OLIMEX/OLINUXINO/HARDWARE/LCDs/LCD-DRIVER/README.md

LCD-DRIVER is a common LCD board used in Olimex displays that have one of these suffixes 
at the end of the product name: "-RTS", "-CTS", or "+" and suffix.

Displays without touchscreen, without "+" at the end of the product name, or with suffix "TS" 
use own driver boards, not LCD-DRIVER. Check the folders of these displays for schematics of 
the driver boards.

It is important to notice that depending on the size of the display and the type of touschreen 
used the LCD_DRIVER board would be configured dirrently. Refer to the labes in the schematic 
and also refer to the bill of materials in the hardware revision B folder (BOM) for the 
different configurations.

List of boards using LCD-DRIVER as of 03.09.2019:

LCD-OLinuXino-4.3+
LCD-OLinuXino-4.3RTS
LCD-OLinuXino-5CTS+
LCD-OLinuXino-7+
LCD-OLinuXino-7CTS
LCD-OLinuXino-7RTS
LCD-OLinuXino-7TS+
LCD-OLinuXino-10+
LCD-OLinuXino-10CTS
LCD-OLinuXino-10RTS
LCD-OLinuXino-10TS+
