OLIMEX/OLINUXINO/HARDWARE/LCDs/LCD-OLinuXino-10+/README.md

Description of product LCD-OLinuXino-10+

LCD-OLinuXino-10+ is a 10 inch display with resolution of 1024x600 pixels. 

LCD-OLINUXINO-10+ has no touschreen.

The design uses LCD-DRIVER board, instead the legcay board design of the original 
LCD-OLinuXino-10 (without the plus) and LCD-OLinuXino-10TS.

Refer to LCD-DRIVER's GitHub page for the hardware deisng files.

It is important to notice that depending on the size of the display and the type of touschreen 
used the LCD-DRIVER board would be configured dirrently. Refer to the labes in the schematic 
and also refer to the bill of materials in the hardware revision B folder (BOM) for the 
different configurations.
