OLIMEX/OLINUXINO/HARDWARE/LCDs/LCD-OLinuXino-10/README.md

LCD-OLINUXINO-10 is a 10 inch display with resolution of 1024x600 pixels. LCD-OLINUXINO-10 has no touschreen.

LCD-OLINUXINO-10 and LCD-OLINUXINO-10TS use the same design files (schematic, board files).

Both boards use the legacy driver board design, not the common LCD-DRIVER board.

Visit the folder of LCD-OLinuXino-10TS for the hardware design resources.
