OLIMEX/OLINUXINO/HARDWARE/LCDs/LCD-OLinuXino-4.3+/README.md

Description of product LCD-OLinuXino-4.3+

LCD-OLinuXino-4.3+ is a 4.3 inch display with resolution of 480x272.

LCD-OLinuXino-4.3+ has no touschreen.

It has LCD-DRIVER board, instead the legacy PCB design of the original 
LCD-OLinuXino-4.3 (without the plus).

Refer to LCD-DRIVER's GitHub page for the hardware source files.

It is important to notice that depending on the size of the display and the type of touschreen 
used the LCD_DRIVER board would be configured dirrently. Refer to the labes in the schematic 
and also refer to the bill of materials in the hardware revision B folder (BOM) for the 
different configurations.
