OLIMEX/OLINUXINO/HARDWARE/LCDs/LCD-OLinuXino-4.3/README.md

LCD-OLINUXINO-4.3 is a 4.3 inch display with resolution of 480x272 pixels.

LCD-OLINUXINO-4.3 has no touschreen.

LCD-OLINUXINO-4.3 and LCD-OLINUXINO-4.3TS use the same design files (schematic, board files).

Both boards use the legacy driver board design, not the common LCD-DRIVER board.

Check the files in the LCD-OLinuXino-4.3TS folder for the hardware design files.
