OLIMEX/OLINUXINO/HARDWARE/LCDs/LCD-OLinuXino-4.3RTS/README.md

Description of product LCD-OLinuXino-4.3RTS

LCD-OLinuXino-4.3RTS is is a 4.3 inch display with resolution of 800x480 pixels and resistive touch screen.

It uses LCD-DRIVER board, instead the original board design of the original 
LCD-OLinuXino-4.3 (without the plus).

In LCD-OLinuXino-4.3RTS the touschreen uses digital interface (I2C).

Refer to LCD-DRIVER's GitHub page for the hardware source files.

It is important to notice that depending on the size of the display and the type of touschreen 
used the LCD_DRIVER board would be configured dirrently. Refer to the labes in the schematic 
and also refer to the bill of materials in the hardware revision B folder (BOM) for the 
different configurations.
