OLIMEX/OLINUXINO/HARDWARE/LCDs/LCD-OLinuXino-4.3TS+/README.md

Description of product LCD-OLinuXino-4.3TS+

LCD-OLinuXino-4.3TS+ is a 4.3 inch display with resolution of 480x272.

It uses LCD-DRIVER board, instead the original board design of the original 
LCD-OLinuXino-4.3 (without the plus).

Unlike LCD-OLinuXino-4.3RTS, the touchscreen of LCD-OLinuXino-4.3TS+ is configured for analog
connection. In LCD-OLinuXino-4.3RTS the touschreen uses digital interface (I2C).

Refer to LCD-DRIVER's GitHub page for the hardware source files.

It is important to notice that depending on the size of the display and the type of touschreen 
used the LCD_DRIVER board would be configured dirrently. Refer to the labes in the schematic 
and also refer to the bill of materials in the hardware revision B folder (BOM) for the 
different configurations.
