OLIMEX/OLINUXINO/HARDWARE/LCDs/LCD-OLinuXino-5CTS/README.md

LCD-OLinuXino-5CTS is a 5 inch display with resolution of 800x480 pixels and capacitive touch screen.

LCD-OLINUXINO-5CTS uses the legacy driver board design, not the common LCD-DRIVER board.
