OLIMEX/OLINUXINO/SOFTWARE/A13/EASYCAP/README

EasyCap is low cost video capture USB dongle which could be find at low cost from ebay. It allow 1 to 4 cameras to be connected and to implement DVR security survilance on your PC.

Kaloyan Yovchev sent us tested drivers which works with A13-OLinuXIno and kernel 3.0.42+
