OLIMEX/OLINUXINO/SOFTWARE/A13/ANDROID-MOD-IO/README.TXT

This is demo code made by Dimitar Gamishev and show how to access MOD-IO and drive relays, read GPIOs, read ADCs with Android application.
The sources of the projects are at: https://github.com/hehopmajieh/modio_android
