OLIMEX/OLINUXINO/HARDWARE/A10S-OLinuXino-MICRO/A10S-OLinuXino-MICRO_Rev_D.sch.pdf

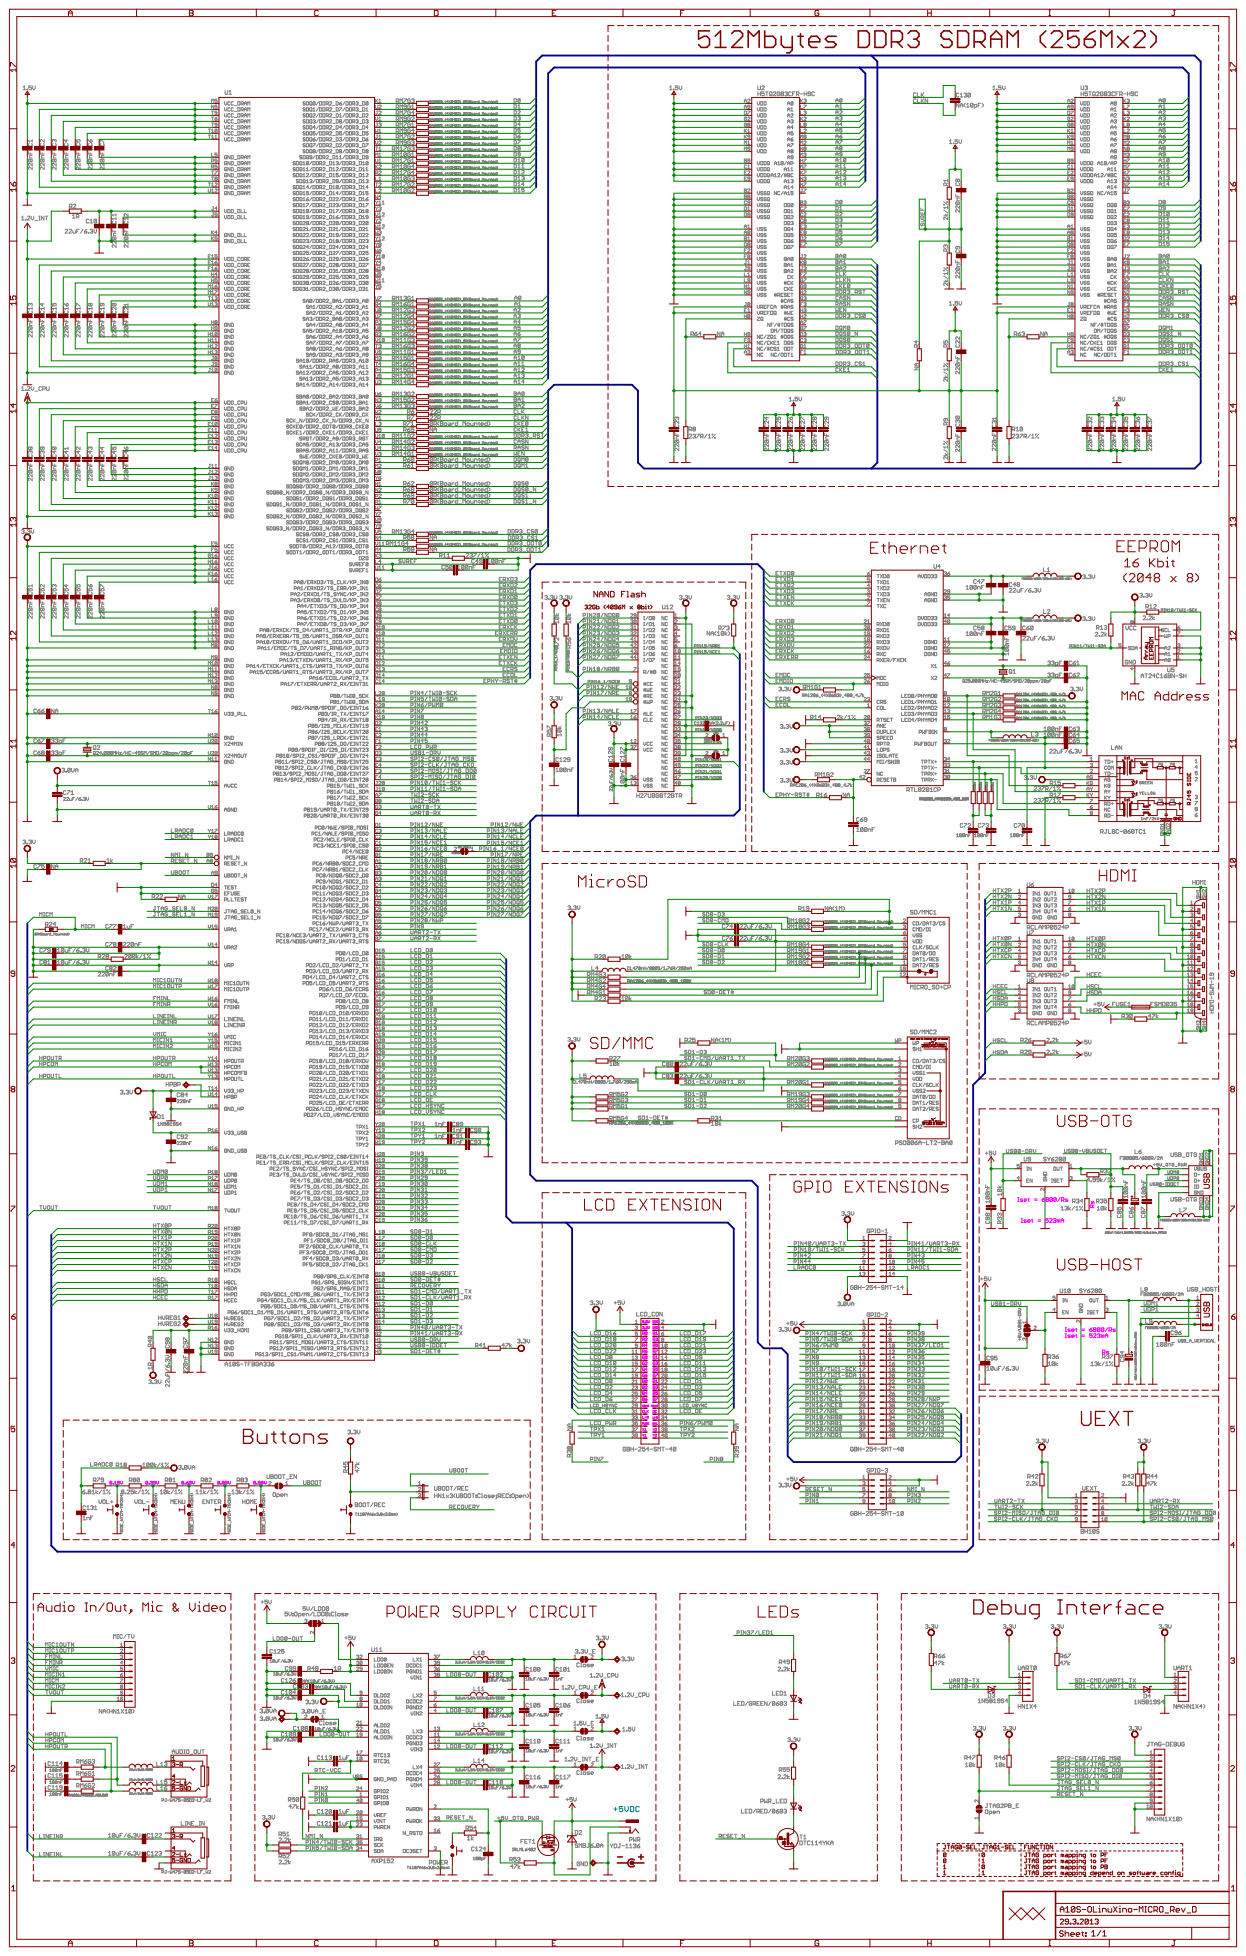
[picture p3: page 1]
