OLIMEX/OLINUXINO/HARDWARE/AM3352-OLinuXino/AM3352-OLINUXINO_Rev_A-14122012.sch.pdf

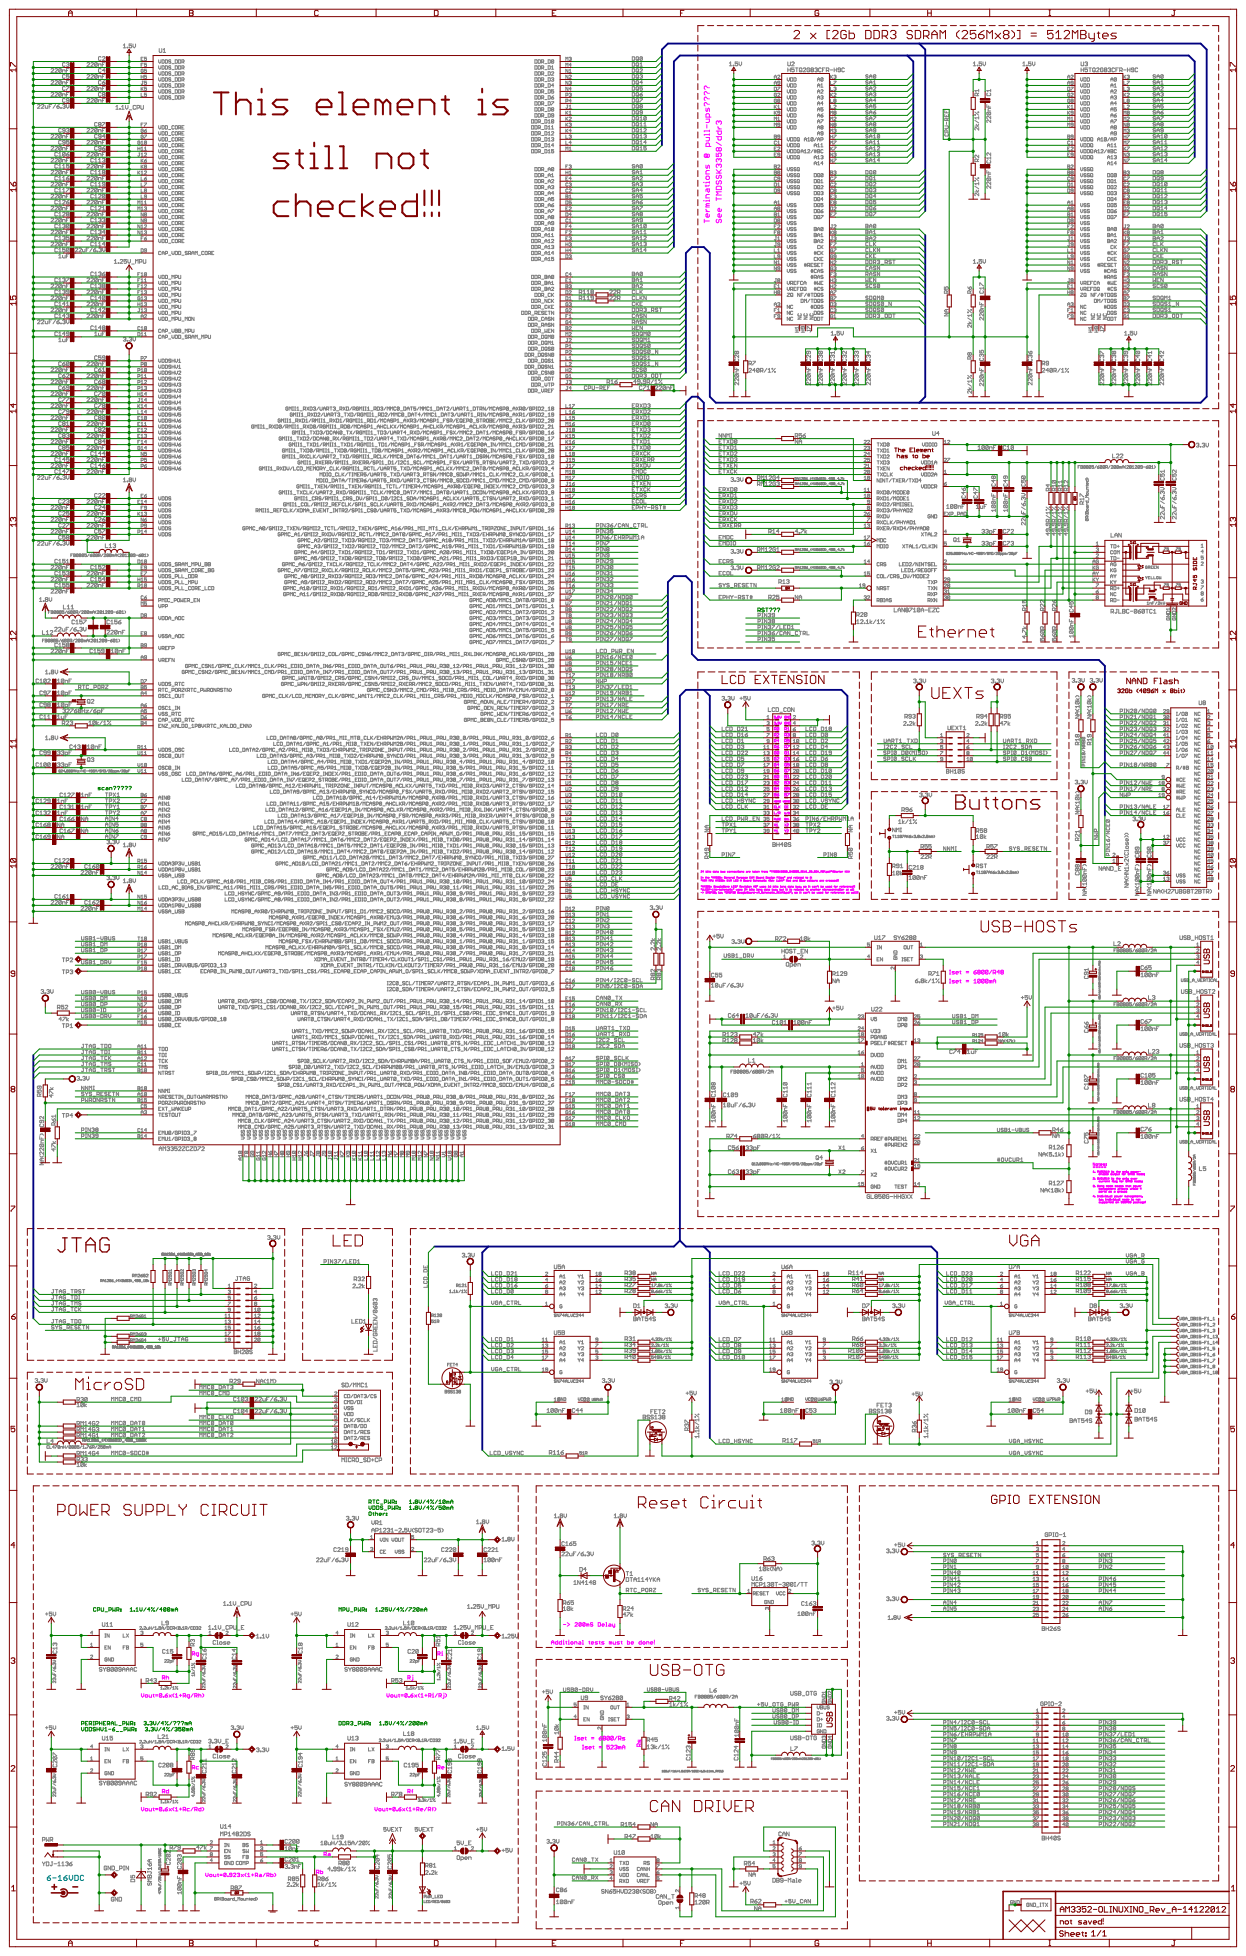
[picture p4: page 1]
