OLIMEX/OLINUXINO/HARDWARE/A13-OLinuXino-MICRO/A13-OLinuXino-MICRO_Rev_A.sch.pdf

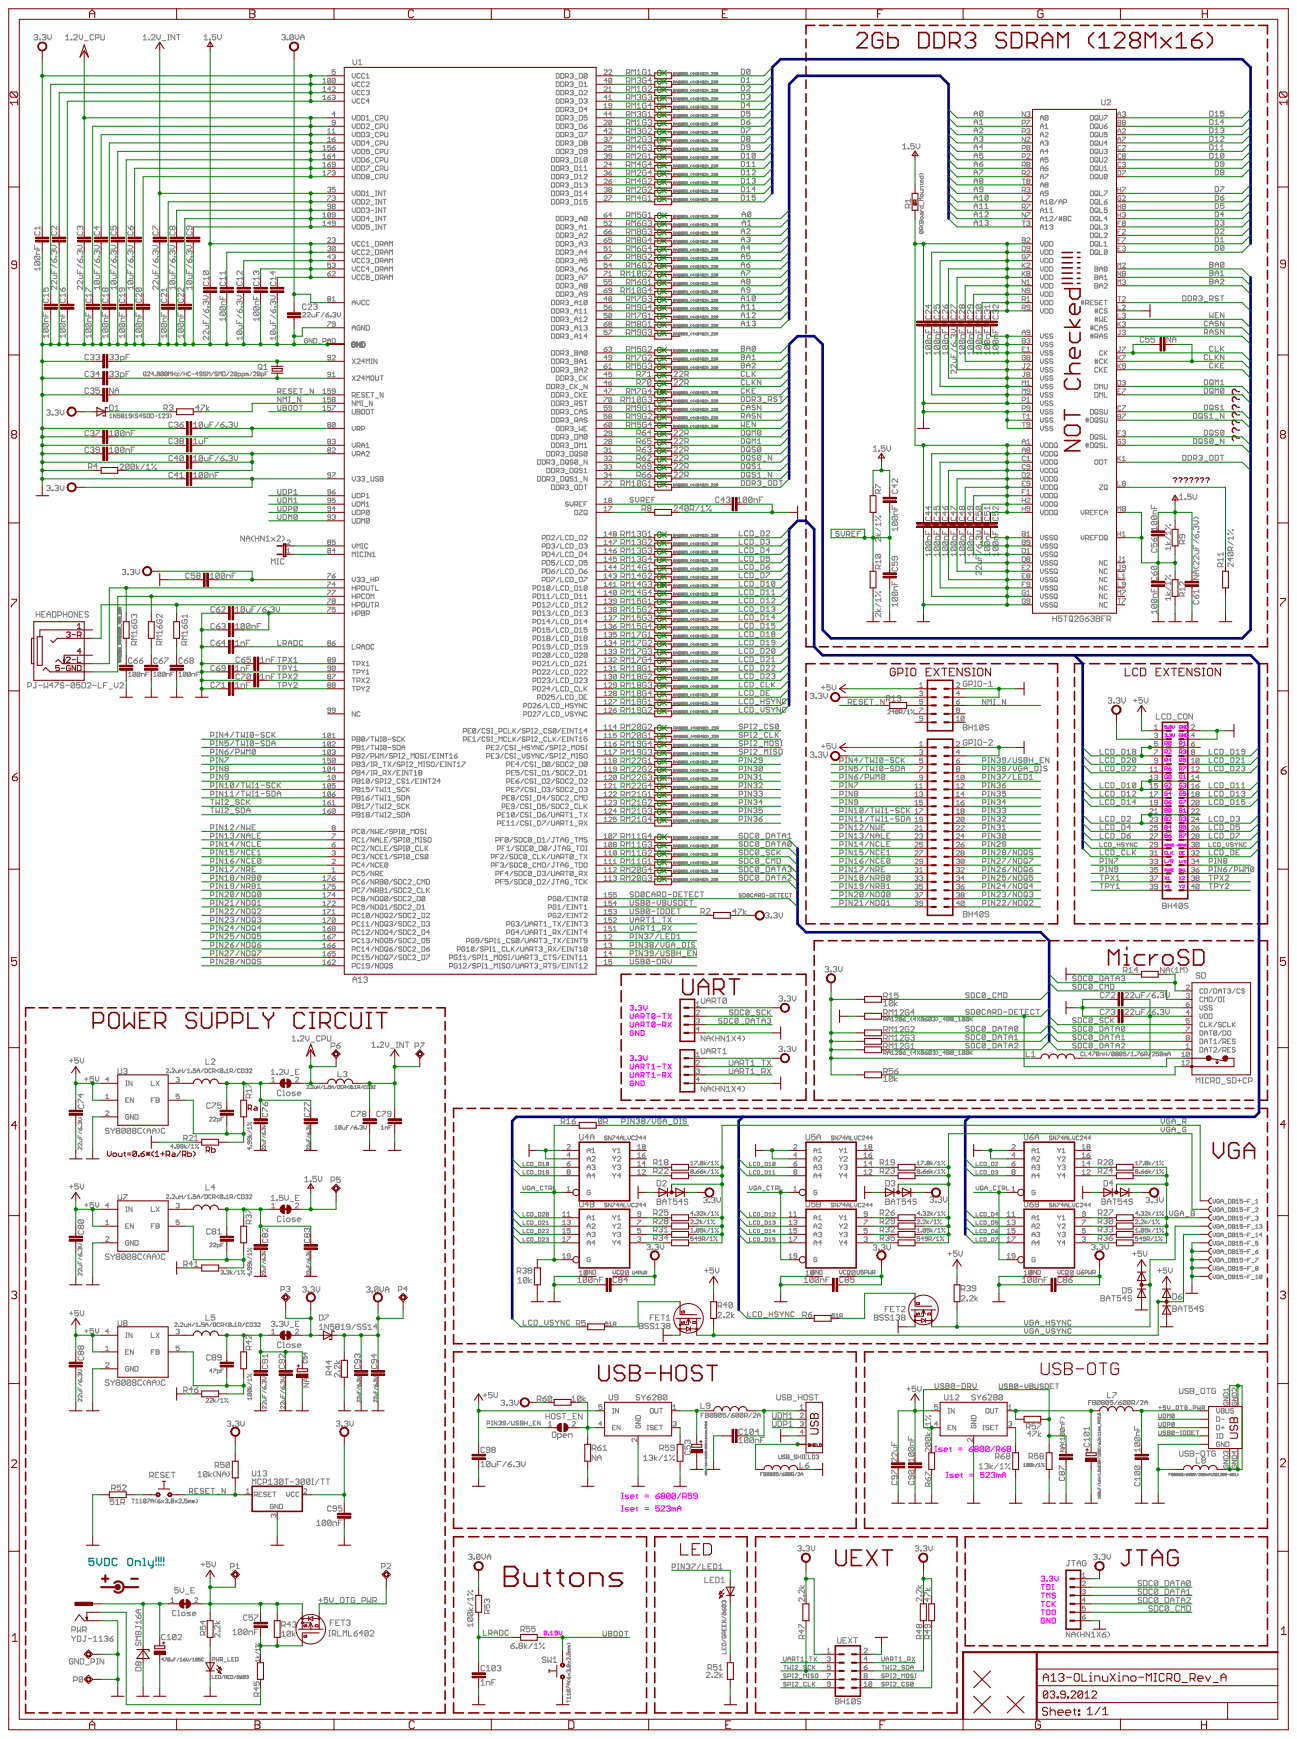
[picture p5: page 1]
