OLIMEX/OLINUXINO/HARDWARE/A10-OLinuXino/A10-OLinuXino_Rev_A.sch.pdf

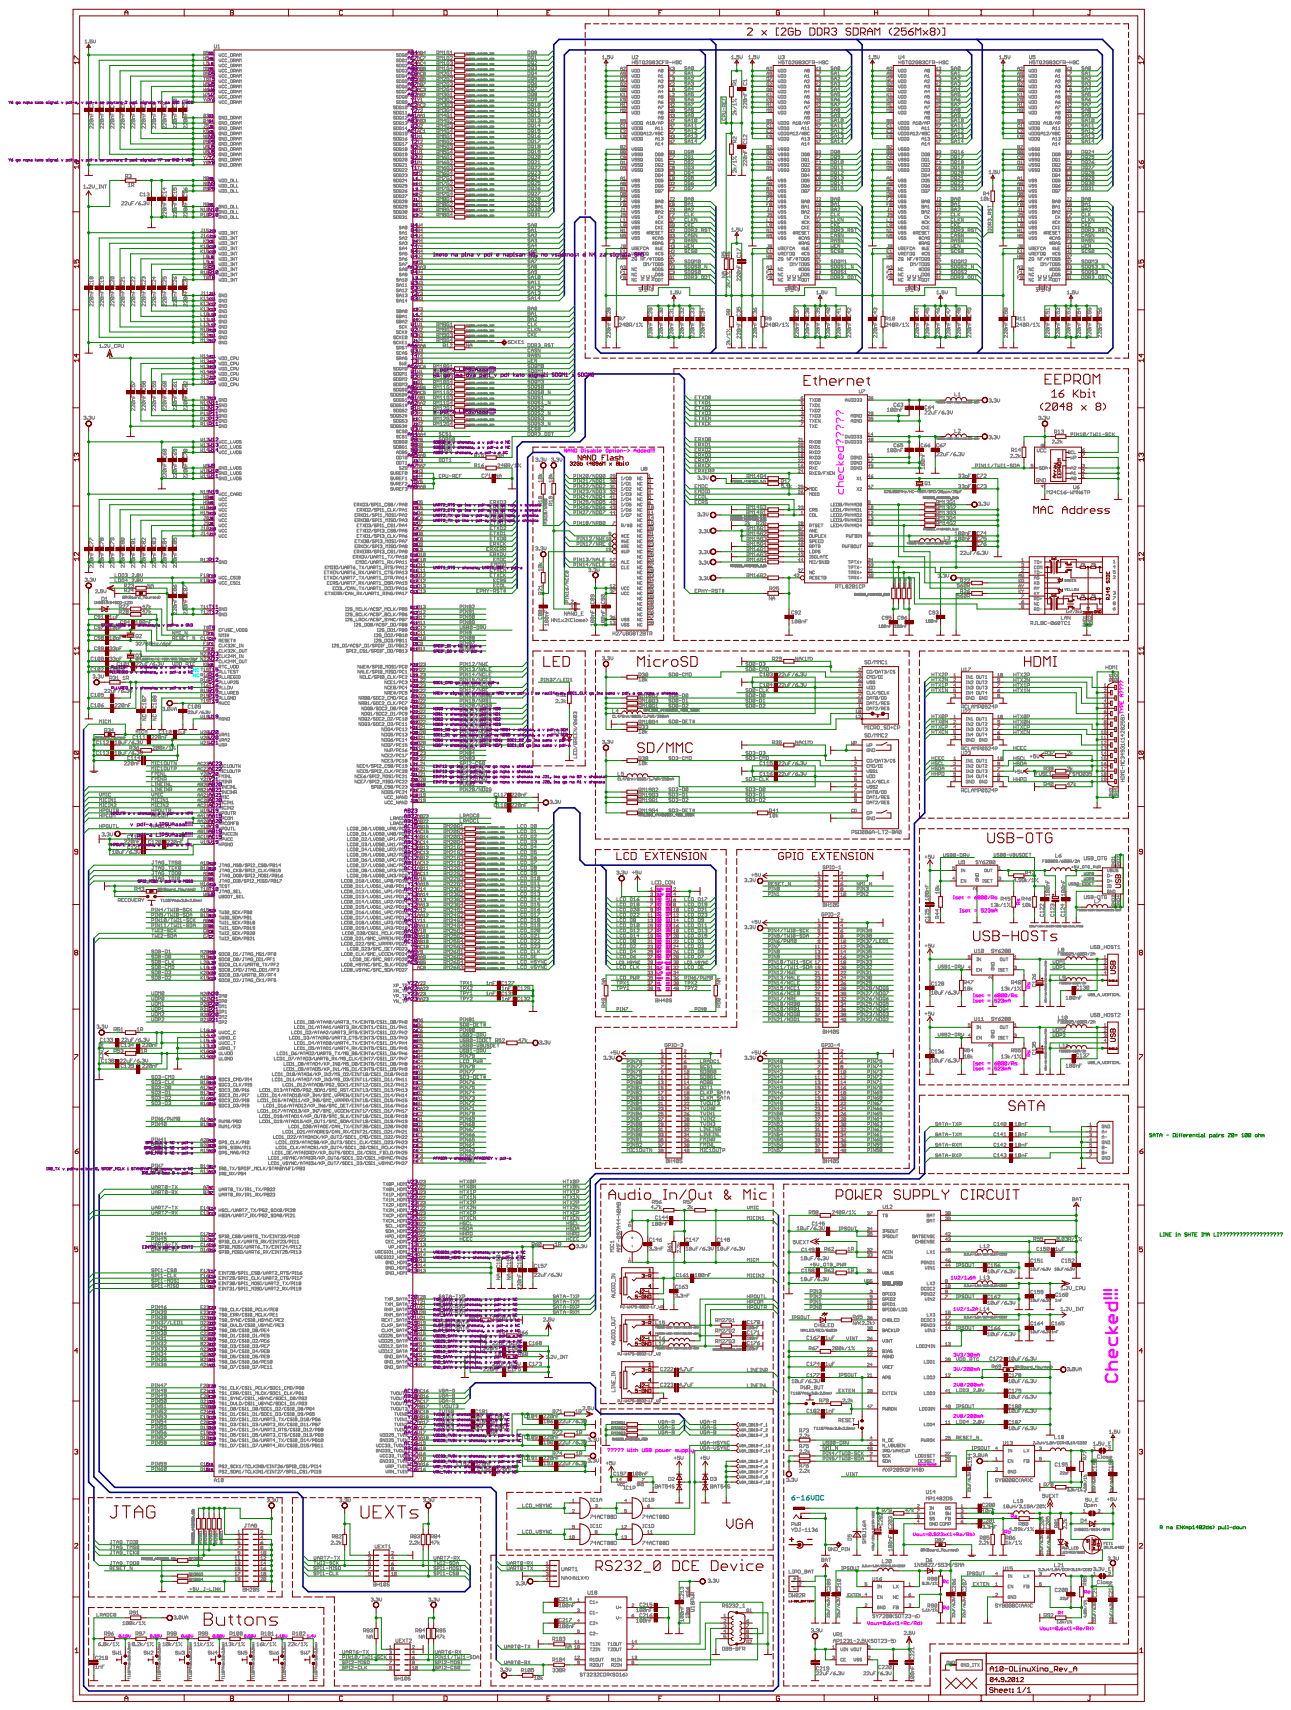
[picture p6: page 1]
