OLIMEX/OLINUXINO/HARDWARE/A10-OLinuXino-LIME/2. Older hardware revisions/A10-OLinuXino-LIME hardware revision preliminary/A10-OLinuXino/README.TXT

A10-OLinuXino	September, 2012	REV.A

Status	: design 

Issues	: 

TODO	: 

Features of the board specification:
What we put on the board:
- A10 Cortex A8 processor running at 1Ghz
- 1GB of DDR3 memory (organized as 4 x 256MB x8 with two 2Gbit chips)
- 4GB NAND Flash
- HDMI
- VGA
- RS232 UART
- 100Mbit Ethernet
- LCD 
- 2 USB hosts 
- 1 USB OTG
- SATA
- JTAG
- UEXT1 and UEXT2 for connecting addtional UEXT modules like Zigbee, Bluetooth, Relays, etc
- GPIO-1,2,3,4 with total 132 GPIOs available for the user
- Audio Output, Audio Input, Line Input
- 7 buttons for android navigation
- STATUS LED
- micro-SDcard 
- normal size SD/MMC card
- 6-16VDC input power supply, noise immune design
- LiPo battery power option
- RESET and Power-Down buttons
- console debug UART port
