OLIMEX/OLINUXINO/BOXES/LIME2-PLASTIC-BOX/Olinuxinoe-lime2-back.png

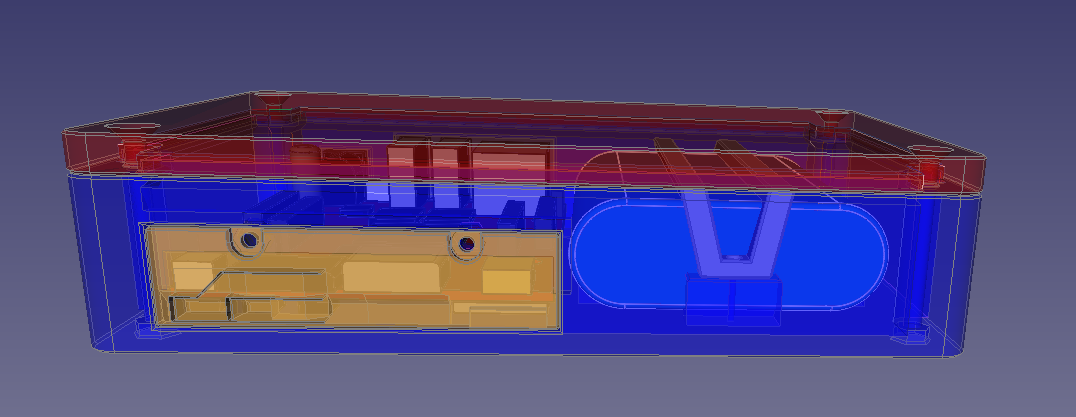
BOXES/LIME2-PLASTIC-BOX/Olinuxinoe-lime2-back.png
