OLIMEX/OLINUXINO/BOXES/LIME2-PLASTIC-BOX/Olinuxinoe-lime2-open.png

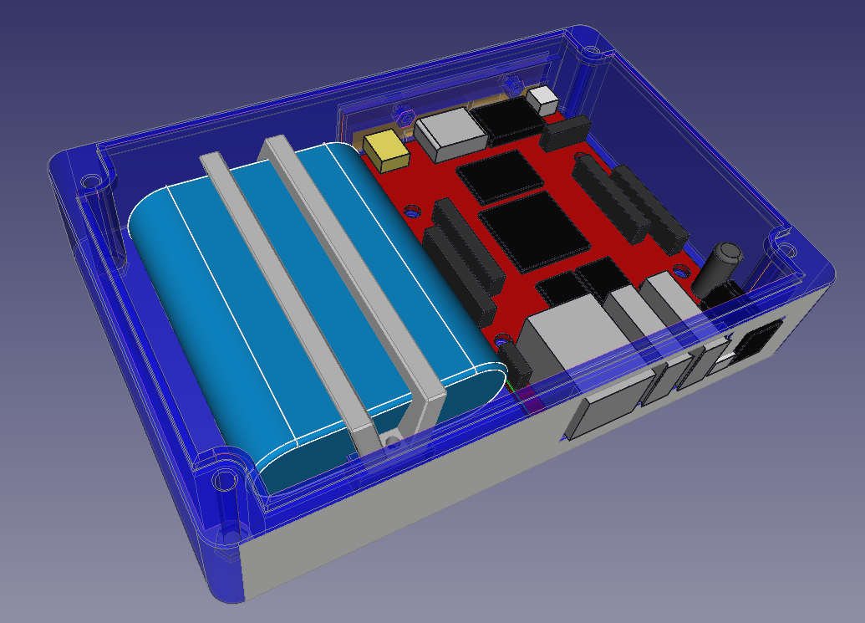
BOXES/LIME2-PLASTIC-BOX/Olinuxinoe-lime2-open.png
