OLIMEX/OLINUXINO/BOXES/LIME2-PLASTIC-BOX/Olinuxinoe-lime2-top.png

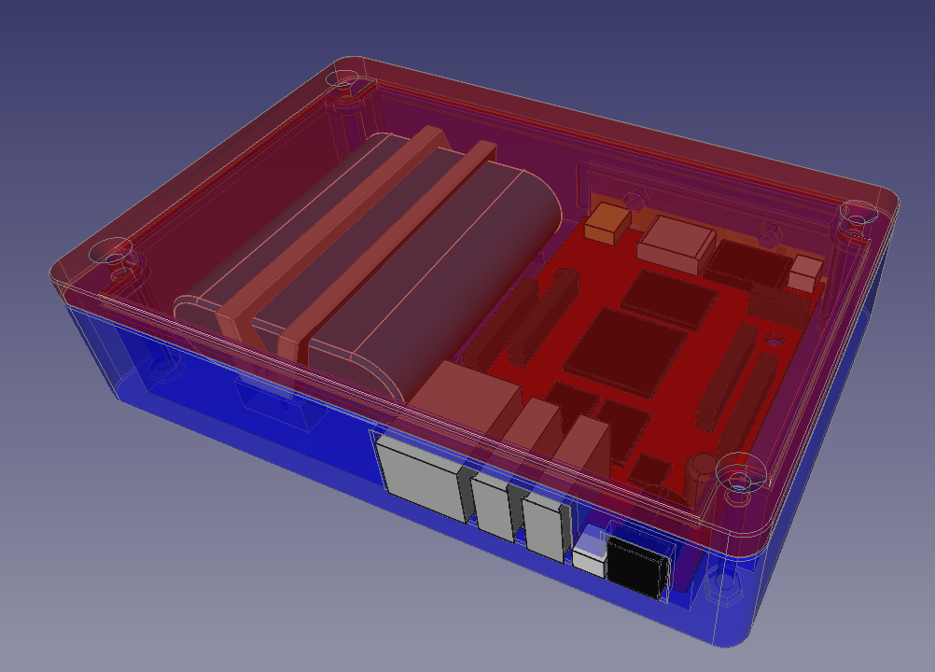
BOXES/LIME2-PLASTIC-BOX/Olinuxinoe-lime2-top.png
