OLIMEX/OLINUXINO/BOXES/LIME2-PLASTIC-BOX/PLASTIC-BOX-ASM1.jpg

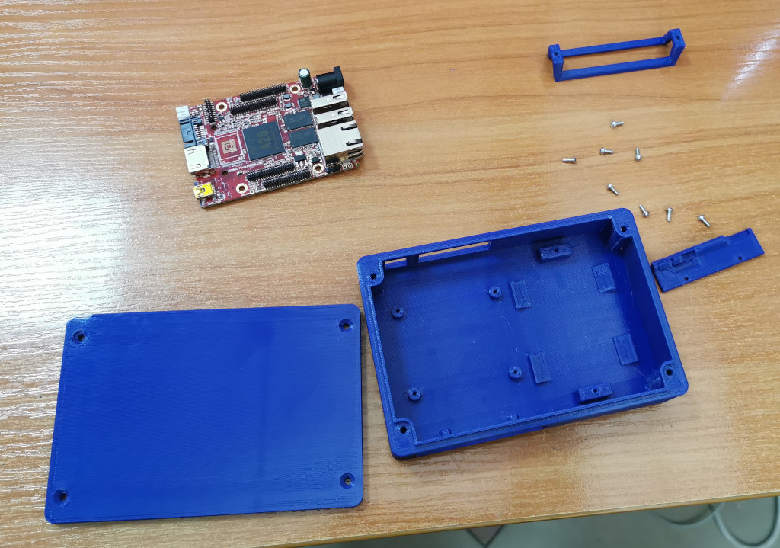
BOXES/LIME2-PLASTIC-BOX/PLASTIC-BOX-ASM1.jpg
