OLIMEX/OLINUXINO/BOXES/LIME2-PLASTIC-BOX/PLASTIC-BOX-ASM2.jpg

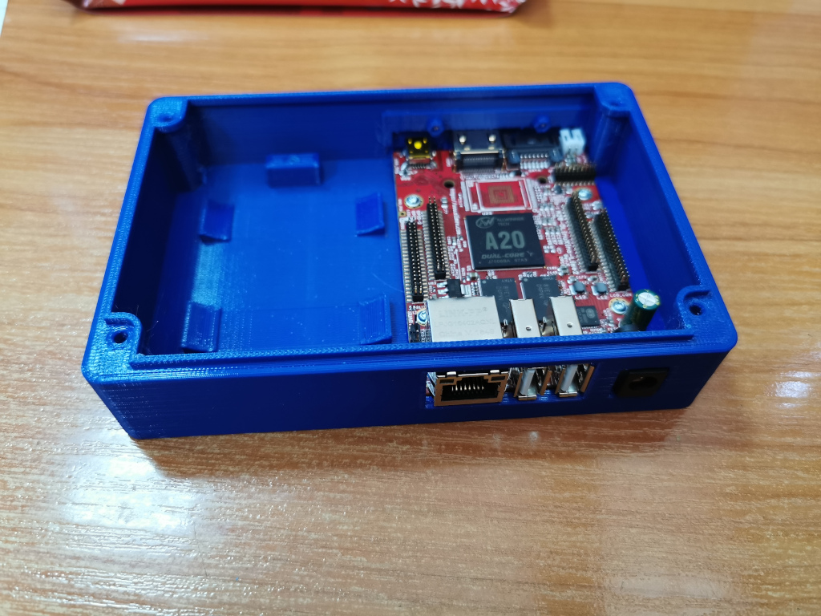
BOXES/LIME2-PLASTIC-BOX/PLASTIC-BOX-ASM2.jpg
