OLIMEX/OLINUXINO/SOFTWARE/A13/A13+OpenCV+Scratch+BallTracking/Configure Blue.png

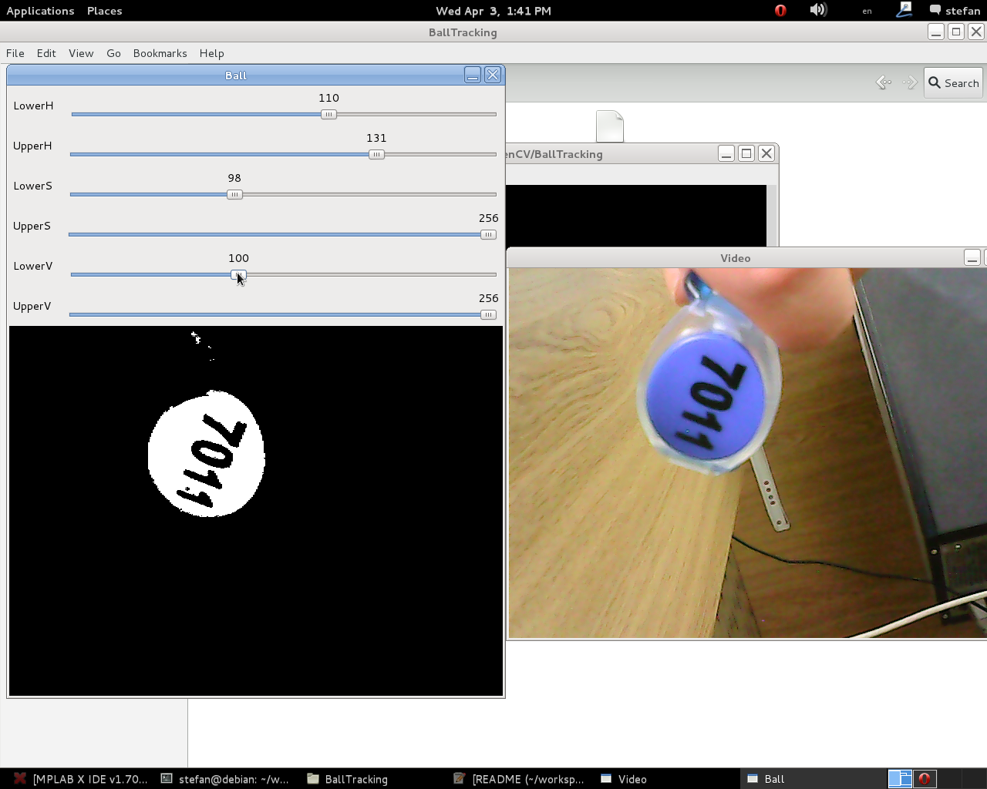
SOFTWARE/A13/A13+OpenCV+Scratch+BallTracking/Configure Blue.png
