OLIMEX/OLINUXINO/SOFTWARE/A13/A13-OLinuXino-WIFI-MOD-GPS-LOGGER/A13+GPS.png

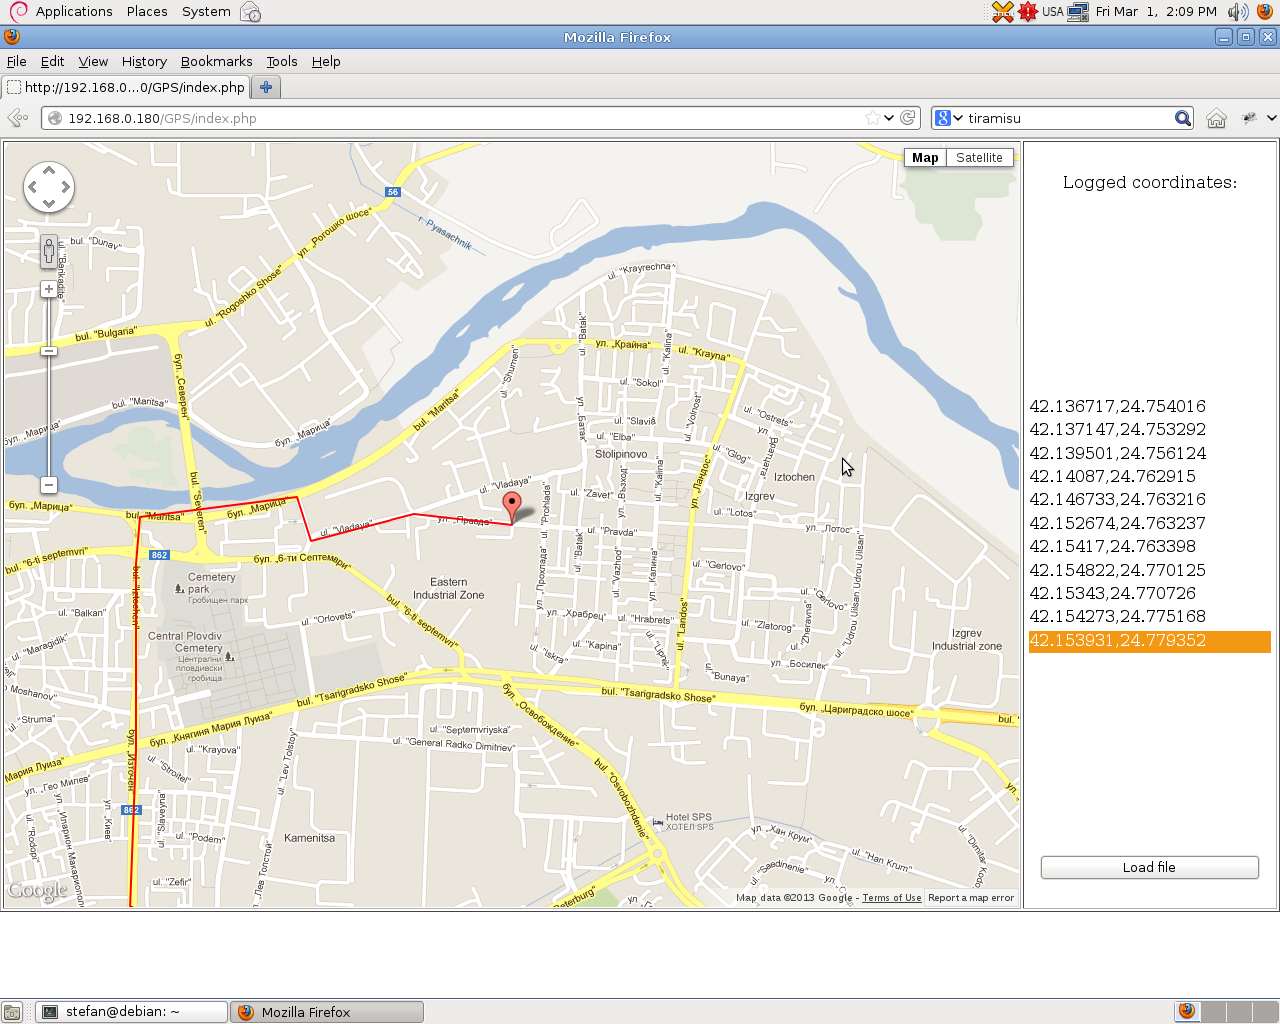
SOFTWARE/A13/A13-OLinuXino-WIFI-MOD-GPS-LOGGER/A13+GPS.png
