OLIMEX/OLINUXINO/SOFTWARE/A13/MOD-GPS/MOD-GPS-COMPILE.jpg

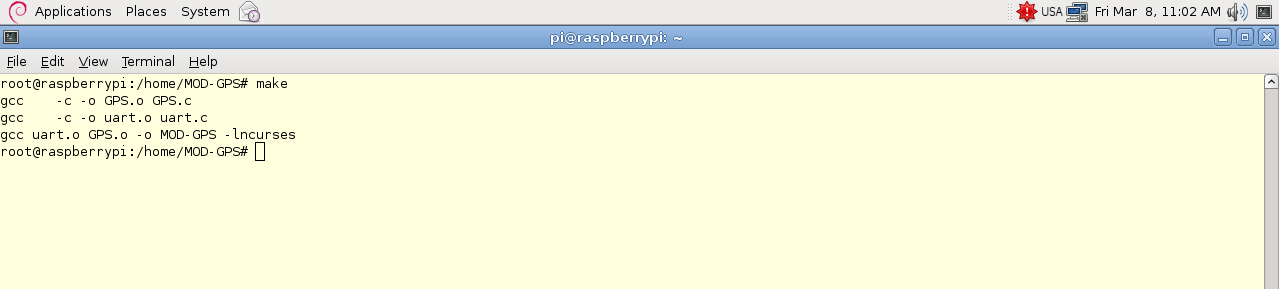
SOFTWARE/A13/MOD-GPS/MOD-GPS-COMPILE.jpg
