OLIMEX/OLINUXINO/SOFTWARE/A13/MOD-GPS/MOD-GPS-START.jpg

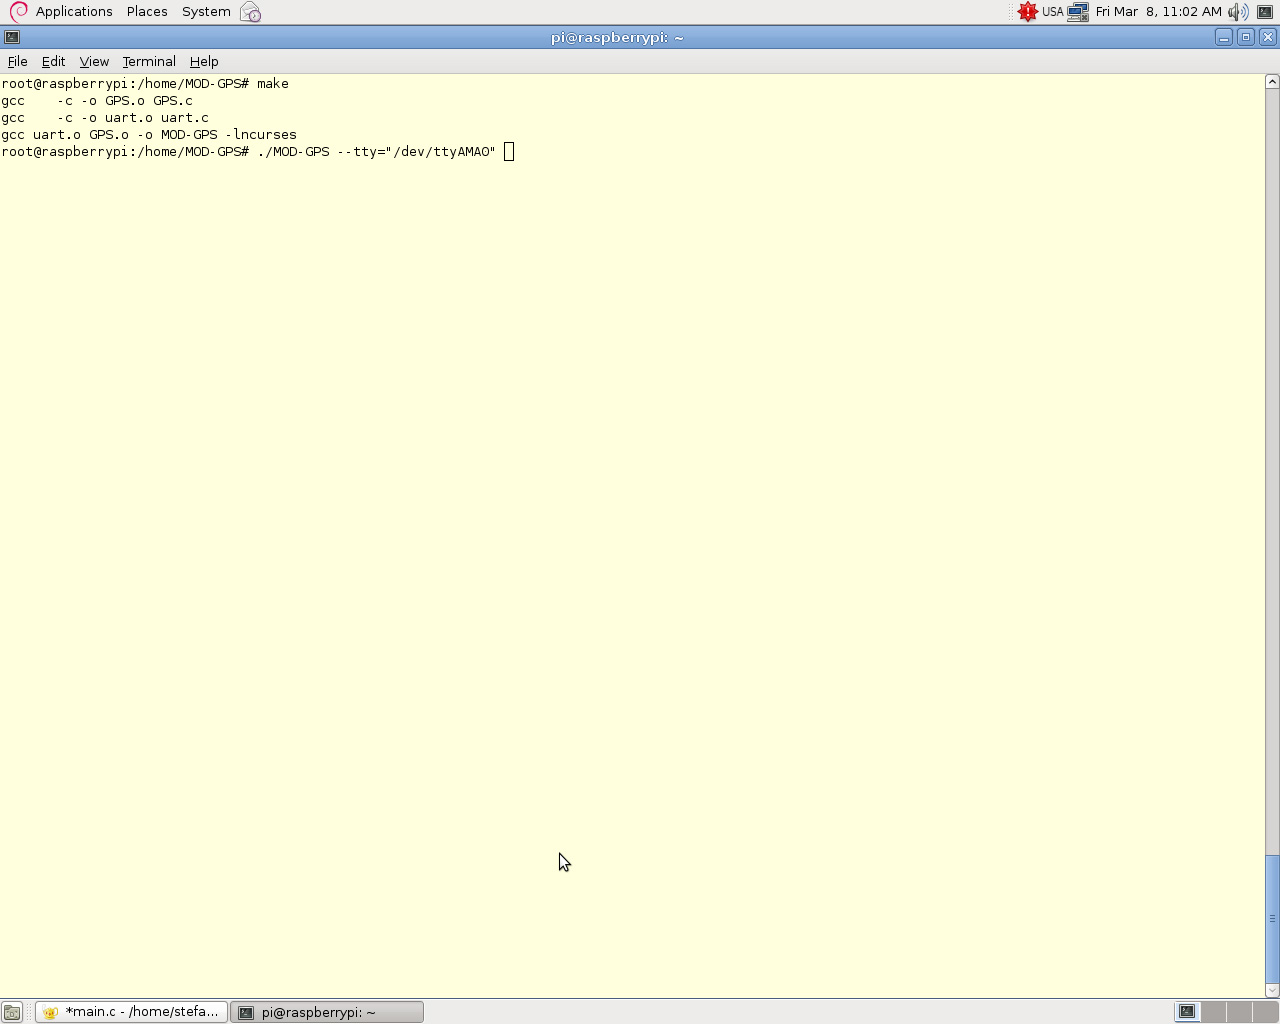
SOFTWARE/A13/MOD-GPS/MOD-GPS-START.jpg
