OLIMEX/OLINUXINO/SOFTWARE/A13/MOD-GPS/MOD-GPS.jpg

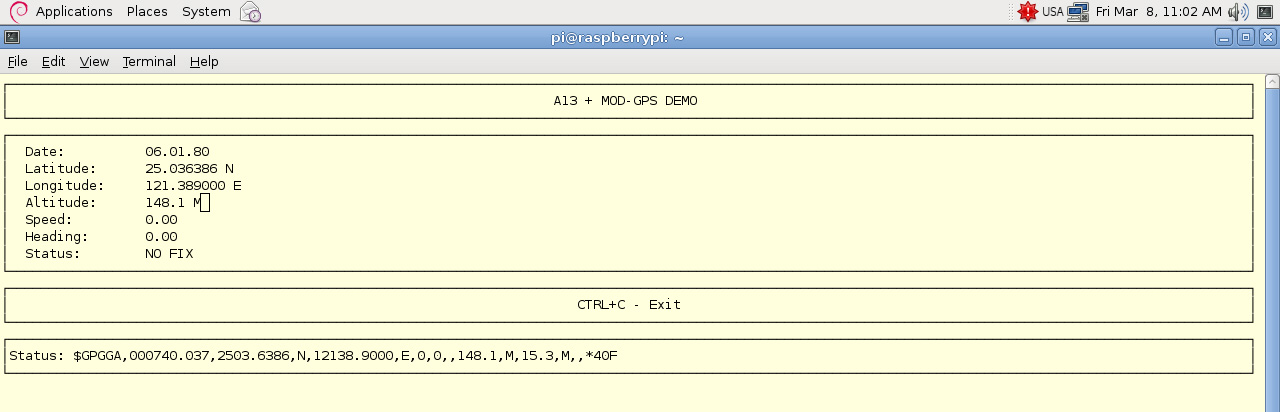
SOFTWARE/A13/MOD-GPS/MOD-GPS.jpg
