OLIMEX/OLINUXINO/SOFTWARE/A13/MOD-RGB/RGB.png

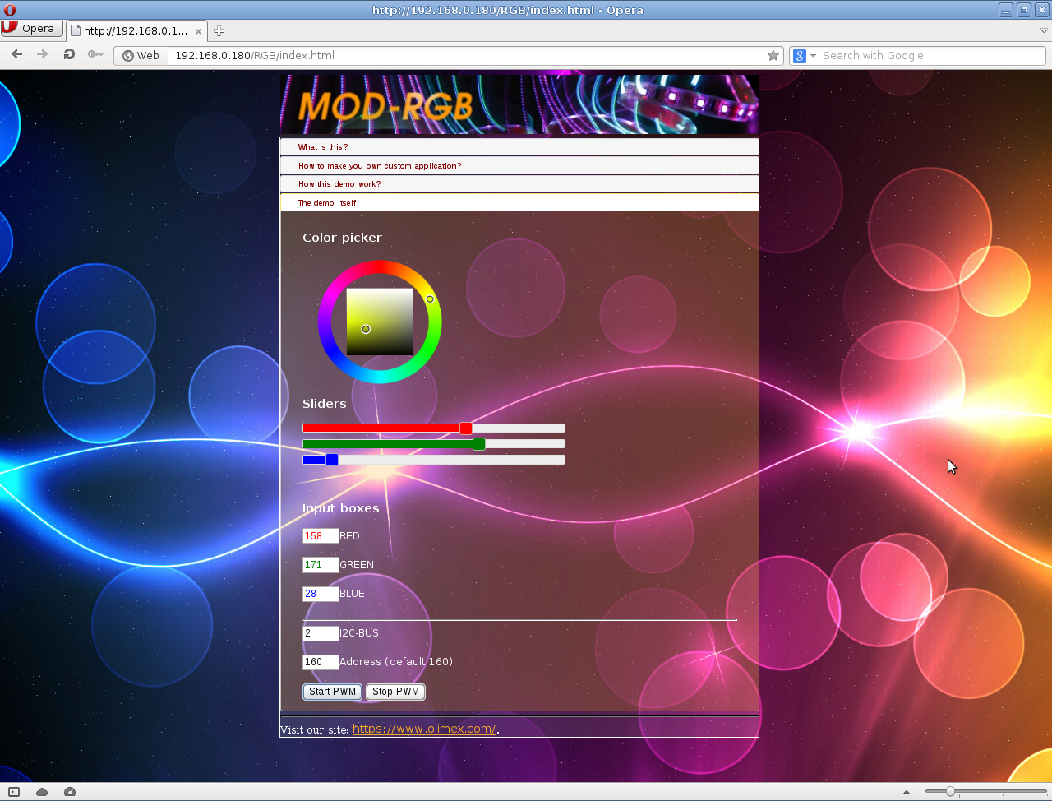
SOFTWARE/A13/MOD-RGB/RGB.png
