OLIMEX/OLINUXINO/SOFTWARE/A20/ANDROID A20-OLINUXINO-TOOLS/A20-OLINUXINO-TOOLS/ic_launcher-web.png

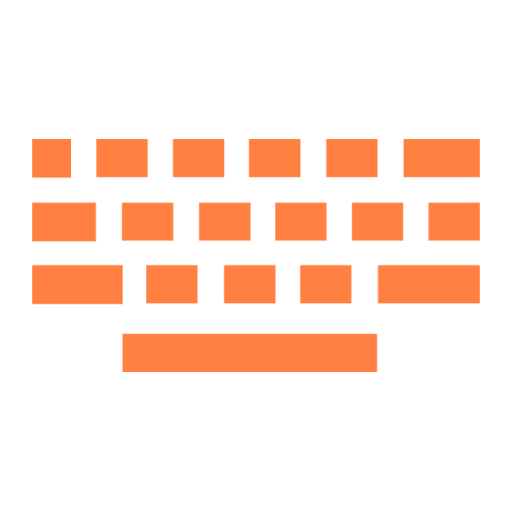
SOFTWARE/A20/ANDROID A20-OLINUXINO-TOOLS/A20-OLINUXINO-TOOLS/ic_launcher-web.png
