OLIMEX/OLINUXINO/SOFTWARE/A20/ANDROID A20-OLINUXINO-TOOLS/Screenshot_1970-01-02-02-06-02.png

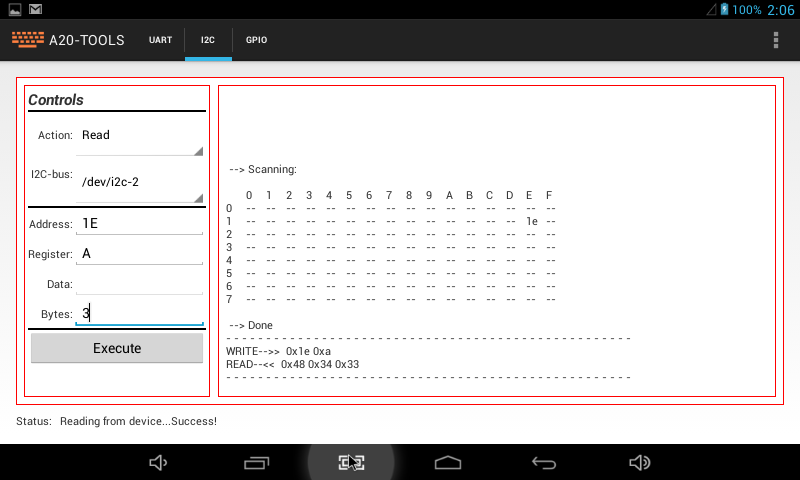
SOFTWARE/A20/ANDROID A20-OLINUXINO-TOOLS/Screenshot_1970-01-02-02-06-02.png
