OLIMEX/OLINUXINO/HARDWARE/LCDs/LCD-OLinuXino-15.6FHD/Hardware revision H/LCD-OLinuXino-15.6FHD_Rev_H_bom.ods

Designation | Quantity | Designator | Package
(na) | 1 | RM1 | R_MATRIX_4_KICAD
(na) 100K | 2 | R12,R15 | R0402
(na) FB0805 | 1 | FB4 | L_0805_5MIL_DWS
SMD РЕЗ 0603 1.05 K 1% | 1 | R14 | R_0603_5MIL_DWS
SMD КОНД 0402 100 NF 10% 10VDC | 16 | C3,C4,C5,C6,C7,C8,C9,C11,C13,C14,C15,C16,C17,C18,C24,C19 | C_0402_5MIL_DWS
SMD РЕЗ 0402 10 K 5% | 4 | R5,R6,R8,R11 | R_0402_5MIL_DWS
SMD КОНД 0603 1 UF 10V X5R | 2 | C1,C2 | C_0603_5MIL_DWS
SMD КОНД 0603 1 UF 50VDC X5R | 2 | C20,C21 | C_0603_5MIL_DWS
SMD РЕЗ 0402 2.2 K 5% | 5 | R1,R3,R10,R2,R4 | R_0402_5MIL_DWS
SMD РЕЗ 0603 20 K 1% | 1 | R13 | R_0603_5MIL_DWS
SMD КОНД 0402 33 PF +-0.25 PF | 2 | C10,C12 | C_0402_5MIL_DWS
4SB24.000F20E15/5x3.2mm/20ppm/20pF | 1 | Q1 | Q5x3.25
PWR-JACK-MIL-SMT | 1 | PWR1 | PWR-JACK-MIL-SMT
SMD ДИОД ШОТКИ SOT23 BAT54C | 1 | D2 | SOT23
SMD ИНД YS75 22 UH | 1 | L1 | SD75
SMD ТРАНЗИСТОР DTC114YKA | 1 | T1 | SOT23
FB0805 | 3 | FB1,FB2,FB3 | L_0805_5MIL_DWS
SMD СЪЕДИНИТЕЛ FPV-WZA21-40LF | 2 | P1,SOM204-LVDS1 | FPV-WZA21-40-LF
SMD ТРАНЗИСТОР IRLML6402 | 1 | FET1 | SOT23
SMD СЪЕДИНИТЕЛ LCD30P-0.5MM-02 | 1 | eDP1 | eDP-TERES
SMD ИС MCP1700T-1202E/MB | 1 | U1 | SOT89
SMD СЪЕДИНИТЕЛ B-V-40-LF (GBH254SMT-40) | 1 | uICR1 | GBH-254-SMT-40
SMD СЪЕДИНИТЕЛ MALE-PAV16X-2x20 | 2 | LIME1,LIME2 | GPH127SMT-02X20(PA-V16X-2X20-LF)
SMD ИС MT3608 2-24V 2A | 1 | U3 | SOT23-6
SMD ИС NCS8801 | 1 | U2 | QFN56_7x7mm_0.4p
SMD ИС PIC10F206T-I/OT | 1 | IC1 | SOT23-6
SMD ДИОД 1N5822 (SS34) SMA | 2 | D1,D3 | SMA-KA
LCD 15.6 1920x1080-eDP | 1
