OLIMEX/OLINUXINO/HARDWARE/A64-OLinuXino/A64-OLinuXino_Rev_C/A64-OlinuXino_Rev_C.csv

Id | Designator | Package | Quantity | Designation | Supplier and ref
1 | LCD_CON1 | FPV-WZA21-40-LF | 1 | FPV-WZA21-40-LF
2 | USB1 | USB_A_VERTICAL_PTH | 1 | USB_A_VERTICAL
3 | HDMI1 | HDMI-SWM-19 | 1 | HDMI-SWM-19
4 | U5 | TBGA100 | 1 | MTFC4GACAANA-4M_IT(TBGA100)
5 | Mounting_hole1 | Mounting_hole_3.3mm_with_5.5mm_pad | 1 | Mounting_hole
6 | PWRLED1,GPIO_LED1 | LED_0603_KA | 2 | LED/Red/0603
7 | L16 | YS75_7X8MM | 1 | 2.2uH/3A/YS75/7x8
8 | RM9,RM7,RM12 | RA1206_(4X0603)_4B8_xx | 3 | RA1206_(4x0603)_4B8_100k
9 | C187,C48,C62,C105,C185,C84,C85 | C_0402_5MIL_DWS | 7 | 33pF/50V/5%
10 | R93 | R_0402_5MIL_DWS | 1 | 10M
11 | C91,C5,C10,C16,C21,C26,C42,C47,C49,C53,C54,C57,C59,C63,C89,C116,C121,C122,C124,C125,C126,C128,C129,C131,C133,C136,C138,C139,C140,C141,C143,C144,C145,C146,C147,C148,C149,C150,C151,C152,C153,C154,C157,C159,C161,C162,C164,C165,C166,C167,C168,C169,C170,C171,C172,C173,C175,C176,C178,C179,C188,C192,C194 | C_0603_5MIL_DWS | 63 | 10uF/6.3V/20%
12 | R46 | R_0402_5MIL_DWS | 1 | 27k
13 | T1 | DFN2x2-6L | 1 | WPM1481-6/TR(DFN2X2-6L)
14 |  | LOGO_ROHS_1 | 1
15 | RM2,RM5,RM3,RM14 | RA0805_(4X0402)_xx | 4 | RA0805_(4X0402)_22R
16 | RM4,RM1 | RA1206_(4X0603)_4B8_xx | 2 | RA1206_(4X0603)_4B8_10k
17 | ,,,,, | Fiducial1x3_transp | 6
18 | 5V_E1,HSIC_E1 | SJ | 2 | Opened
19 | C1,C2,C3,C4,C6,C7,C8,C9,C11,C12,C13,C14,C15,C17,C18,C19,C20,C22,C23,C24,C25,C28,C29,C30,C31,C32,C33,C34,C35,C37,C44,C46,C50,C51,C52,C58,C60,C65,C66,C67,C72,C73,C74,C79,C80,C90,C92,C109,C110,C115,C117,C123,C127,C130,C132,C134,C155,C156,C158,C177,C186,C189,C191,C195,C197,C199,C200,C203,C206,C207,C208,C209,C210,C215,C216,C217,C45,C82,C83,C86,C87 | C_0402_5MIL_DWS | 81 | 100nF/10V/10%
20 | C27,C38,C43,C55,C120,C135,C137,C142,C160,C163,C181,C182,C190,C211 | C_0603_5MIL_DWS | 14 | 1uF/10V/10%
21 | C36,C204,C205,C214,C218,C219 | C_0603_5MIL_DWS | 6 | 22uF/6.3V/20%
22 | C39,C40,C41,C81 | C_0402_5MIL_DWS | 4 | NA(100nF/10V/10%)
23 | C56,C61 | C_0603_5MIL_DWS | 2 | 2.2uF/6.3V/10%
24 | C64,C68,C71,C75,C78,C118,C119,C180,C201,C202 | C_0805_5MIL_DWS | 10 | 47uF/6.3V/20%
25 | C69,C70,C76,C77 | C_0805_5MIL_DWS | 4 | NA(47uF/6.3V/20%)
26 | C106,C107,C198 | C_0402_5MIL_DWS | 3 | NA
27 | C174 | C_0603_5MIL_DWS | 1 | NA(110uF/6.3V/20%)
28 | C183,C184 | C_0402_5MIL_DWS | 2 | 10pF/50V/5%
29 | C193 | C_0402_5MIL_DWS | 1 | NA(1nF/50V/10%)
30 | D2,D3 | SMA-KA | 2 | 1N5822/SS34/SMA
31 | D4 | SOD-123_1C-2A_KA | 1 | 1N5819(S4SOD-123)
32 | FET1 | SOT23 | 1 | BSS138(SOT23-3)
33 | FET2 | SOT23 | 1 | IRLML6402(SOT-23)
34 | FUSE1 | FUSE-1206 | 1 | FSMD035
35 | FUSE2 | FUSE-5025 | 1 | NA(5025)
36 | L1,L2,L3,L4,L5,L6,L8,L21,L23,L24 | L_0805_5MIL_DWS | 10 | FB0805/600R/2A
37 | NAND_E1 | SJ | 1 | Unsoldered
38 | Q2 | MC306-HS | 1 | MC-306_32.768KHZ/12.5pF/20ppm/SMD_8038
39 | Q3 | Q5x3.25 | 1 | 4SB24.000F20E15/5x3.2mm/20ppm/20pF
40 | R2 | R_0402_5MIL_DWS | 1 | 100R/1%
41 | R3,R4,R33,R54,R100,R105,R109,R63,R64,R65 | R_0402_5MIL_DWS | 10 | 22R
42 | R18 | R_0402_5MIL_DWS | 1 | NA(22R)
43 | R39,R43,R44,R45 | R_0402_5MIL_DWS | 4 | NA(510R)
44 | R60 | R_0402_5MIL_DWS | 1 | NA(0R)
45 | R96,R97,R98,R84,R19,R20,R24,R6,R118,R55 | R_0402_5MIL_DWS | 10 | NA
46 | U6,U9 | SOT-23-5 | 2 | SY6280AAC(SOT23-5)
47 | U13 | SOT23-6 | 1 | MT3608(SOT23-6)
48 | R37,R40,R42,R85,R83,R95,R76,R79,R31,R52,R21,R23,R99,R106,R119 | R_0402_5MIL_DWS | 15 | 10k
49 | R38,R51 | R_0402_5MIL_DWS | 2 | 4.7k
50 | R41 | R_0402_5MIL_DWS | 1 | 13k/1%
51 | R61,R104,R48,R15,R16,R17,R22,R53,R56,R57 | R_0402_5MIL_DWS | 10 | NA(10k)
52 | ANT1 | bt_antenna_1ant_2gnd | 1 | PCB_WIFI_ANT
53 | R70,R71,R74,R82,R90,R88,R75,R77,R47,R50 | R_0402_5MIL_DWS | 10 | 2.2k
54 | R101,R102 | R_0402_5MIL_DWS | 2 | NA(2.2k)
55 | R103,R30,R35,R116 | R_0402_5MIL_DWS | 4 | 100k
56 | R78 | R_1206_5MIL_DWS | 1 | 0.01R/1%/1206
57 | R92,R89,R91,R107,R108,R110,R111,R112,R113,R114,R117,R58 | R_0402_5MIL_DWS | 12 | 1k
58 | R80 | R_0402_5MIL_DWS | 1 | 8.25k/1%
59 | R81 | R_0402_5MIL_DWS | 1 | 1.1k/1%
60 | R25 | R_0402_5MIL_DWS | 1 | 470R
61 | R26,R29,R11,R12,R1,R5,R8 | R_0402_5MIL_DWS | 7 | 2k/1%
62 | R32 | R_0402_5MIL_DWS | 1 | NA(1M)
63 | R49 | R_0402_5MIL_DWS | 1 | 3.92k/1%
64 | R27 | R_0402_5MIL_DWS | 1 | 200k/1%
65 | R7,R9,R10 | R_0402_5MIL_DWS | 3 | 243R/1%
66 | R13,R14 | R_0402_5MIL_DWS | 2 | NA(243R/1%)
67 |  | OLIMEX_LOGO_TB | 1
68 |  | LOGO_ANTISTATIC_1 | 1
69 |  | LOGO_OPENHARDWARE_8x8 | 1
70 |  | LOGO_PBFREE | 1
71 |  | LOGO_RECYCLEBIN_1 | 1
72 | 3.3V/VCC-PE:2.8V1 | SJ_2_SMALL_12_TIED | 1 | Opened(2-3);Closed(1-2)
73 | PWRON1,RESET1,UBOOT1 | uTACTIL | 3 | IT-1185AU2-160G-G-TR
74 | R34,R62,R86,R87,R94 | R_0402_5MIL_0R(Board_Mounted) | 5 | 0R(Board_Mounted)
75 | R36 | R_0603_5MIL_0R(Board_Mounted) | 1 | 0R(Board_Mounted)
76 | C196 | C_1206_5MIL_DWS_ISO | 1 | 1nF/2kV/10%/X7R
77 | C212,C213 | C_0603_5MIL_DWS | 2 | 27pF/50V/5%
78 | Q4 | HCX-4S_2Pins_5.0x3.2mm | 1 | E4SB25.000F20E15(25MHz/20pF/20ppm/5x3.2mm)
79 | R115 | R_0603_5MIL_DWS | 1 | 12.1k/1%
80 | R120 | R_0603_5MIL_DWS | 1 | 120R
81 | RM8 | RA1206_(4X0603)_4B8_xx | 1 | RA1206_(4x0603)_4B8_4.7k
82 | RM15 | RA1206_(4X0603)_4B8_xx | 1 | RA1206_(4x0603)_4B8_22R
83 | D5 | SMA-KA | 1 | 1N4007/SMA
84 | VR1 | SOT223 | 1 | AMS1117(ADJ)
85 | U12 | SO-8_208mil | 1 | NA(W25Q128FVSIG(EN25Q64-104HIP))
86 | D1 | DO214AA | 1 | SMBJ6.0A
87 | +1.5V1,+1.8V1,+3.0VA1,+3.3VD1,+3.3VWiFiIO1,+5V_USBOTG1,1.1V_CPUS1,1.1V_CPUX1,1.1V_SYS1,3.0V_RTC1,3.3V1,3.3V_MIPI1,IPS1,VCC-PC1,VCC-PL1,1.25_EXT1,GND1 | TP_SMD | 17 | TESTPAD
88 | R59 | R_0402_5MIL_DWS | 1 | 47k
89 | U10,U8,U7 | SLP2510P8 | 3 | NA(RCLAMP0524P(SLP2510P8))
90 | U2,U3 | FBGA96(HYNIX_SAMSUNG_512MX16_DDR3) | 2 | K4B4G1646Q-HYK0(FBGA-96_256Mx16_DDR3-1600_11-11-11)
91 | HSIC1 | B4B-PH-K-S | 1 | NA(B4B-PH-K-S)
92 | GPIO1 | HN2x20 | 1 | NA(HN2x20)
93 | U4 | TSOP48 | 1 | NA(H27UBG8T2BTR-BC(TSOP48))
94 | U1 | FBGA396 | 1 | AllWinner-A64(FBGA396)
95 | UEXT1 | HN2x5 | 1 | NA(HN2x5)
96 | DBG_UART1 | HN1x3 | 1 | NA(HN1x3)
97 | U14 | QFN68 | 1 | AXP803(QFN68_8x8mm)
98 | LIPO_BAT1 | LIPO_BAT-CON2DW02R | 1 | DW02R
99 | LAN1 | TM211Q01FM22 | 1 | TM211Q01FM22
100 | PHYRST1 | HN1x2_Jumper | 1 | HN1x2(Opened)
101 | U11 | RL-SM02BD(RTL8723BS) | 1 | RTL8723BS(ComboModule)
102 | MICRO_SD1 | TFC-WPAPR-08 | 1 | MICRO_SD(TFC-WPAPR-08)
103 | MIPI-DSI1 | FPV-WZA21-20-LF | 1 | FPV-WZA21-20-LF
104 | U15 | QFN48_1DRILL(PADPITCH-0.5MM) | 1 | KSZ9031RNXCC(QFN48_1DRILL(PADPITCH-0.5MM))
105 | L18,L15,L17 | CD42(43) | 3 | SWPA4018S1R5NT(1.5uH/3.35A/DCR<0.1R/CD43)
106 | L14,L20,L19 | CD32 | 3 | SWPA3015S1R5NT(1.5uH/2.30A/DCR<0.1R/CD32)
107 | USB-OTG1 | USB-MICRO_MISB-SWMM-5B_LF | 1 | MICRO_USB/MISB-SWMM-5B_LF
108 | GNDA1 | TESTPAD_40-ROUND | 1 | TESTPAD
109 | PWR1 | PWRJ-2mm(YDJ-1134) | 1 | PWRJ-2mm(YDJ-1134)
110 | Mounting_hole2,Mounting_hole3 | Mounting_hole_3.3mm_with_5.5mm_pad_no_inner_pads | 2 | Mounting_hole
111 | LINEINL/MICIN1N1,LINEINR/MICIN1P1,PWR_PC1 | SJ_2_SMALL | 3 | Opened(2-3);Soldered(1-2)
112 | PHONEOUTL/LINEOUTL1,PHONEOUTR/LINEOUTR1 | SJ_2_SMALL | 2 | Soldered(1-2);Opened(2-3)
113 | Mounting_hole4 | Mounting_hole_3.3mm | 1 | Mounting_hole
114 | CHGLED1 | LED_0603_KA | 1 | LED/YELLOW/0603
115 | HEADPHONES/LINEOUT1,MIC/LINEIN1 | SCJ325P00XG0B02G | 2 | SCJ325P00XG0B02G
116 | R28 | R_0402_5MIL_DWS | 1 | NA(1k)
