OLIMEX/OLINUXINO/HARDWARE/LCDs/LCD-DRIVER/Hardware revision C/LCD-DRIVER_Rev_C_LCD-10-TS.ods

Qty | Designation | Package | Designator
5 | 0R/R0402 | R_0402_5MIL_DWS | R30,R31,R32,R33,R61
2 | 1R/1%/R0603 | R_0603_5MIL_DWS | R38,R40
1 | 220R/R0402 | R_0402_5MIL_DWS | R50
1 | 510R/1%/R0402 | R_0402_5MIL_DWS | R16
4 | 1k/1%/R0402 | R_0402_5MIL_DWS | R15,R36,R39,R55
1 | 1.05k/1%/R0402 | R_0402_5MIL_DWS | R45
1 | 2.2k/R0402 | R_0402_5MIL_DWS | R41
9 | 10k/R0402 | R_0402_5MIL_DWS | R11,R14,R18,R22,R23,R34,R42,R48,R63
4 | 20k/1%/R0402 | R_0402_5MIL_DWS | R35,R37,R43,R58
2 | 27k/R0402 | R_0402_5MIL_DWS | R46,R47
1 | 56.2k/1%/R0402 | R_0402_5MIL_DWS | R44
3 | 100nF/16V/10%/X7R/C0402 | C_0402_5MIL_DWS | C6,C9,C14
6 | 100nF/50V/20%/Y5V/C0603 | C_0603_5MIL_DWS | C15,C18,C22,C23,C24,C26
2 | 2.2uF/50V/10%/X5R/C0805 | C_0805_5MIL_DWS | C16,C19
6 | 22uF/6.3V/20%/X5R/C0603 | C_0603_5MIL_DWS | C7,C20,C21,C25,C27,C8
2 | 22uH/1.5A/220mR/20%/CD53(YS53-220M) | CD53(54) | L1,L2
1 | BAT54C(SOT23-3) | SOT23-3 | D2
1 | BZV55C20/SOD80C | SOD80C-4148-KA | D3
2 | BAT54S(SOT23-3) | SOT23-3 | D4,D6
1 | BZV55C5V1/SOD80C | SOD80C-4148-KA | D7
3 | IRLML6402(SOT23-3) | SOT23 | FET1,FET2,FET3
1 | DTC114YKA(SOT-23) | SOT23 | T1
2 | AP3036BKTR-G1(SOT23-6) | SOT23-6 | U3,U4
1 | MALE-PAV16X-2x20(0.8_bud) | GPH127SMT-02X20 (PA-V16X-2X20-LF)_Drill_0.9mm | LCD_Lime2
1 | MALE-PAV16X-2x20(0.8_bud) | GPCB127SMT-02X20 (YA-V36P-2X20-LF)_Drill_0.9mm | LCD_Lime1
1 | P-B-V-40-LF | GBH254SMT-40 | LCD_CON1
1 | LCD-10"(1024x600_LOYE_BOE10.1-33LEDH) +(FPV-WZA21-50-LF) | FPV-WZA21-50-LF | LCD-10,1in_DISP1
1 | LCD-TS10(LCD-10"_TOUCHPANEL) +(FPA-WZB25-04-LF) | FPA-WZB25-04-LF | LCD-10,1in_RTP1
1 | FPV-WZA21-40-LF | FPV-WZA21-40-LF | LCD_FLAT_CON1
1 | PWRJ-2mm(DCJ-W54R-20-LF) | PWRJ-2mm(DCJ-W54R-20-LF) | PWR_JACK1
2 | Closed | SJ_Closed | VLED-_E1,VLED+_E1
1 | 3.3V:Opened/5.0V:Closed | SJ_2_SMALL_23_TIED | 3.3V/5.0V1
1 | CTRL:Closed/EN:Opened | SJ_2_SMALL_23_TIED | CTRL/EN1
2 | Opened | SJ | L/R_EN1,U/D_EN1
1 | NA(WU10S) | WU10S | PWR1
1 | NA(LCD-4.3"(480x272_GFT043HA480272Y) +(FPV-WZA21-40-LF)) | FPV-WZA21-40-LF | LCD-4,3in_DISP1
5 | NA(22uF/6.3V/20%/X5R/C0603) | C_0603_5MIL_DWS | C1,C3,C5,C11,C2
3 | NA(100nF/16V/10%/X7R/C0402) | C_0402_5MIL_DWS | C4,C10,C17
2 | NA(10nF/50V/10%/X7R/C0402) | C_0402_5MIL_DWS | C12,C13
1 | NA(BZV55C3V9/SOD80C) | SOD80C-4148-KA | D1
1 | NA(BZV55C3V6/SOD80C) | SOD80C-4148-KA | D5
1 | NA(LCD-5â€(CAPACITIVE_TS)+ (FPV-WZB201-06-LF)) | FPV-WZB201-06-LF | LCD-5in_CTP1
1 | NA(LCD-5â€(800x480_HDW050TN22)+ (FPV-WZA21-40-LF)) | FPV-WZA21-40-LF | LCD-5in_DISP1
2 | NA(FPV-WZB201-06-LF) | FPV-WZB201-06-LF | LCD-7in_CTP1,LCD-10,1in_CTP1
1 | NA(LCD-7"(800x480_AT070TN92)+ (FPV-WZA21-50-LF)) | FPV-WZA21-50-LF | LCD-7in_DISP1
1 | NA(LCD-TS7(LCD-7"_TOUCHPANEL)+ (FPA-WZB25-04-LF)) | FPA-WZB25-04-LF | LCD-7in_RTP1
12 | NA/R0402 | R_0402_5MIL_DWS | R1,R4,R5,R8,R12,R13,R17,R20,R21, R24,R49,R62
16 | NA(10k/R0402) | R_0402_5MIL_DWS | R2,R3,R6,R7,R9,R10,R19,R51,R52, R53, R54,R56,R57,R59,R60,R64
1 | NA(20k/1%/R0402) | R_0402_5MIL_DWS | R25
4 | NA(2.2k/R0402) | R_0402_5MIL_DWS | R26,R27,R28,R29
1 | NA(AR1021T-I_SS(SSOP-20)) | SSOP-20W | U1
1 | NA(AT24C16C-SSHM-T(SOIC-8_150mil)) | SOIC-8_150mil | U2
1 | NA(LCD-7"(800x480_CX700TN94-CTP38)+ (FPV-WZA21-50-LF)) | FPV-WZA21-50-LF | LCD-7in_DISP2
1 | NA(LCD-10"_CAP_TS(1024x600_IPS_ CXT101H39-42E)+(FPV-WZA21-50-LF)) | FPV-WZA21-50-LF | LCD-10,1in_DISP2
