OLIMEX/OLINUXINO/HARDWARE/STMP157-OLinuXino-LIME2/1. Latest hardware revision/STMP157-OLinuXino-LIME2_Rev_B1/3d/pj-102ah.stp

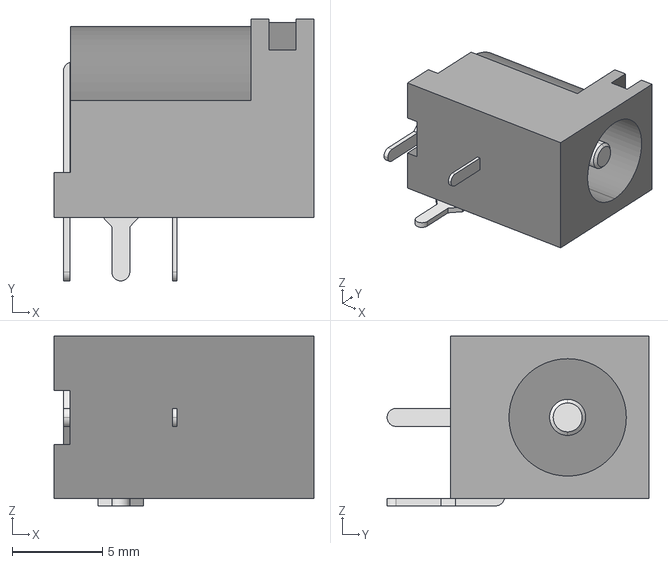
[picture p43: CAD file, 2021-10-07]
HARDWARE/STMP157-OLinuXino-LIME2/1. Latest hardware revision/STMP157-OLinuXino-LIME2_Rev_B1/3d/pj-102ah.stp
14.4 x 14.5 x 9.40 mm
