OLIMEX/OLINUXINO/BOXES/LIME2-PLASTIC-BOX/STL/Olinuxino-Lime2-SlimCase-v001-Bottom-v001.stl

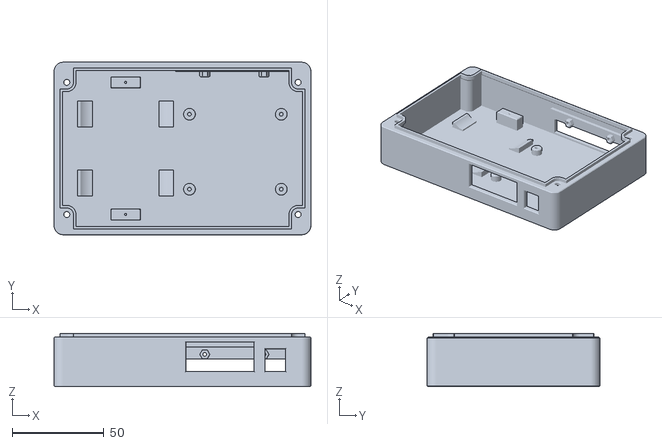
[picture p44: CAD file, 2020-05-13]
BOXES/LIME2-PLASTIC-BOX/STL/Olinuxino-Lime2-SlimCase-v001-Bottom-v001.stl
140.0 x 94.0 x 29.0
