OLIMEX/OLINUXINO/HARDWARE/A64-OLinuXino/1. Latest hardware revision/A64-OLinuXino hardware revision G/3d/L-CD32_shielded.step

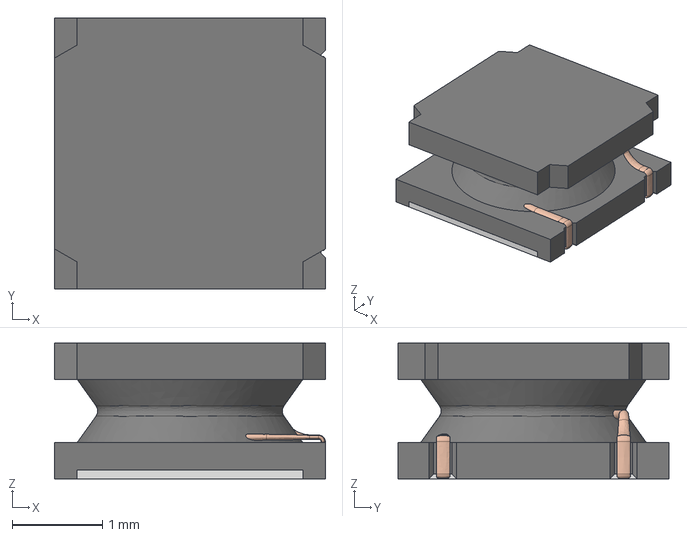
[picture p45: CAD file, 2021-03-23]
HARDWARE/A64-OLinuXino/1. Latest hardware revision/A64-OLinuXino hardware revision G/3d/L-CD32_shielded.step
3.00 x 3.00 x 1.50 mm
