OLIMEX/OLINUXINO/HARDWARE/LCDs/LCD-DRIVER/Hardware revision C/3d/WU10S-Molex_PicoBlade_530471010_1x10_P1.25mm_Vertical.step

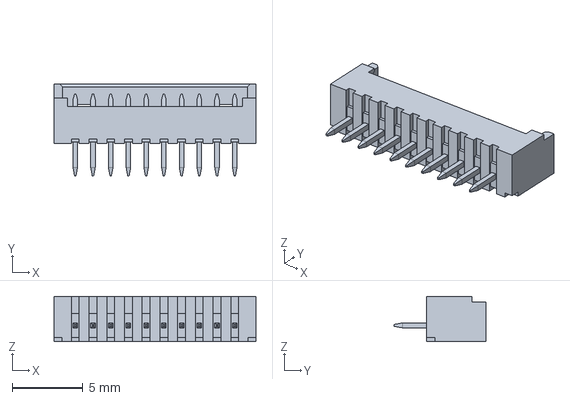
[picture p46: CAD file, 2020-01-09]
HARDWARE/LCDs/LCD-DRIVER/Hardware revision C/3d/WU10S-Molex_PicoBlade_530471010_1x10_P1.25mm_Vertical.step
14.2 x 6.50 x 3.20 mm
