OLIMEX/OLINUXINO/HARDWARE/STMP157-OLinuXino-LIME2/1. Latest hardware revision/STMP157-OLinuXino-LIME2_Rev_B1/3d/DO-214AC_SMA.step

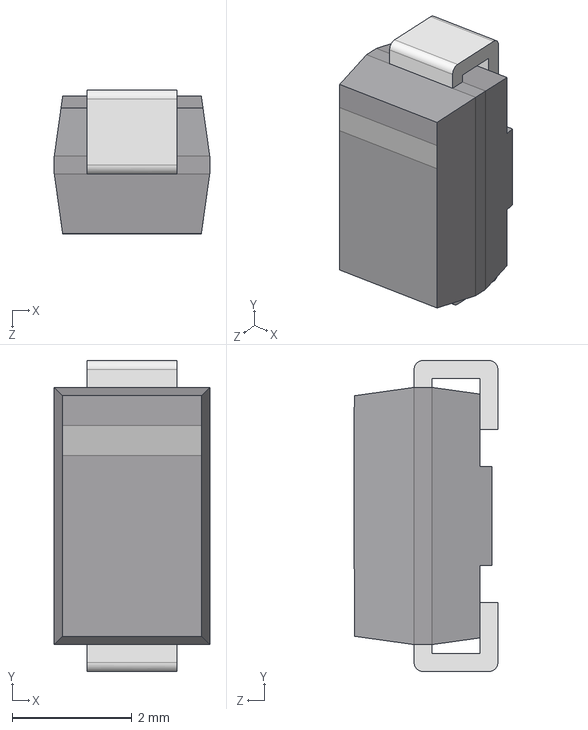
[picture p47: CAD file, 2021-10-07]
HARDWARE/STMP157-OLinuXino-LIME2/1. Latest hardware revision/STMP157-OLinuXino-LIME2_Rev_B1/3d/DO-214AC_SMA.step
2.60 x 5.20 x 2.40 mm
