OLIMEX/OLINUXINO/HARDWARE/LCDs/LCD-DRIVER/Hardware revision C/3d/GBH254SMT-40(B-V-40-LF).stp

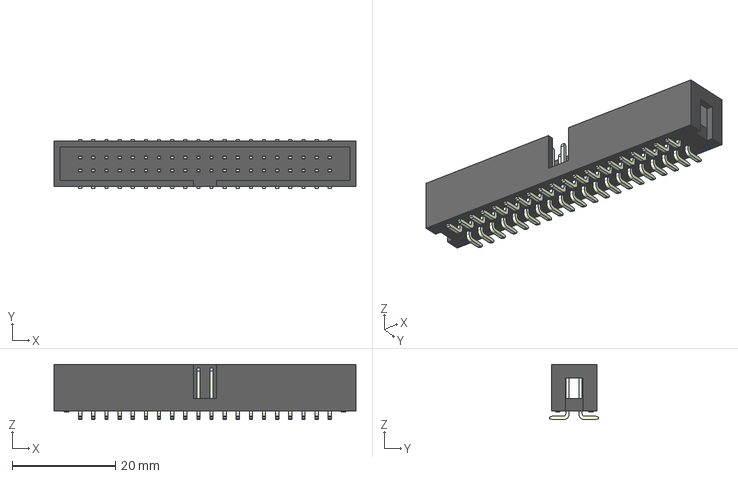
[picture p48: CAD file, 2020-01-09]
HARDWARE/LCDs/LCD-DRIVER/Hardware revision C/3d/GBH254SMT-40(B-V-40-LF).stp
58.4 x 9.50 x 10.6 mm
