OLIMEX/OLINUXINO/HARDWARE/STMP157-OLinuXino-LIME2/1. Latest hardware revision/STMP157-OLinuXino-LIME2_Rev_B1/3d/BGA-624_21.0x21.0mm_Layout25x25_P0.8mm.step

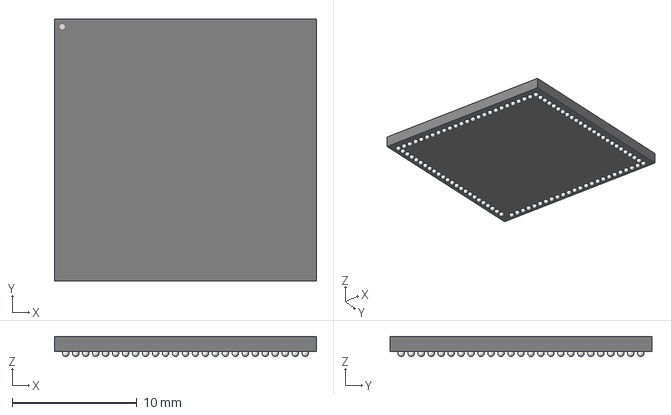
[picture p49: CAD file, 2021-10-07]
HARDWARE/STMP157-OLinuXino-LIME2/1. Latest hardware revision/STMP157-OLinuXino-LIME2_Rev_B1/3d/BGA-624_21.0x21.0mm_Layout25x25_P0.8mm.step
21.0 x 21.0 x 1.61 mm
