OLIMEX/OLINUXINO/HARDWARE/A64-OLinuXino/1. Latest hardware revision/A64-OLinuXino hardware revision G/3d/Q32.768kHz_12.5pF_2P_SMD1206---ECS-.327-12.5-34B-C-TR.STEP

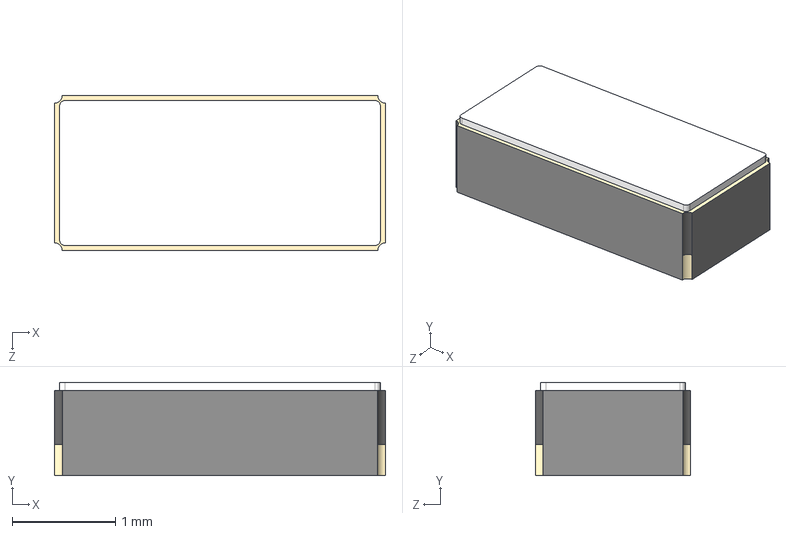
[picture p50: CAD file, 2021-03-23]
HARDWARE/A64-OLinuXino/1. Latest hardware revision/A64-OLinuXino hardware revision G/3d/Q32.768kHz_12.5pF_2P_SMD1206---ECS-.327-12.5-34B-C-TR.STEP
3.20 x 0.9 x 1.50 mm
