OLIMEX/OLINUXINO/HARDWARE/LCDs/LCD-DRIVER/Hardware revision C/3d/BAT54.step

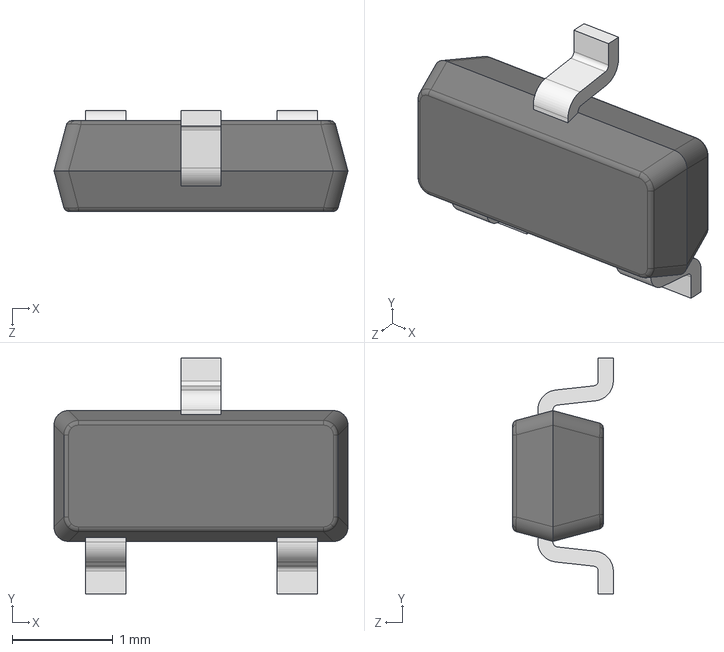
[picture p51: CAD file, 2020-01-09]
HARDWARE/LCDs/LCD-DRIVER/Hardware revision C/3d/BAT54.step
2.92 x 2.34 x 1.00 mm
