OLIMEX/OLINUXINO/HARDWARE/LCDs/LCD-DRIVER/Hardware revision C/3d/40PinMaleSMD.stp

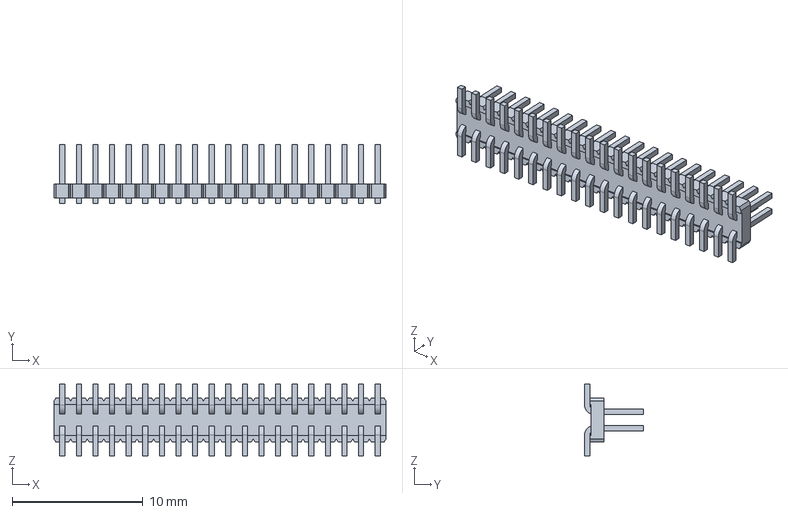
[picture p52: CAD file, 2020-01-09]
HARDWARE/LCDs/LCD-DRIVER/Hardware revision C/3d/40PinMaleSMD.stp
25.4 x 4.50 x 5.50 mm
