OLIMEX/OLINUXINO/HARDWARE/STMP157-OLinuXino-LIME2/1. Latest hardware revision/STMP157-OLinuXino-LIME2_Rev_B1/3d/USB-A-S-F-B-VU.stp

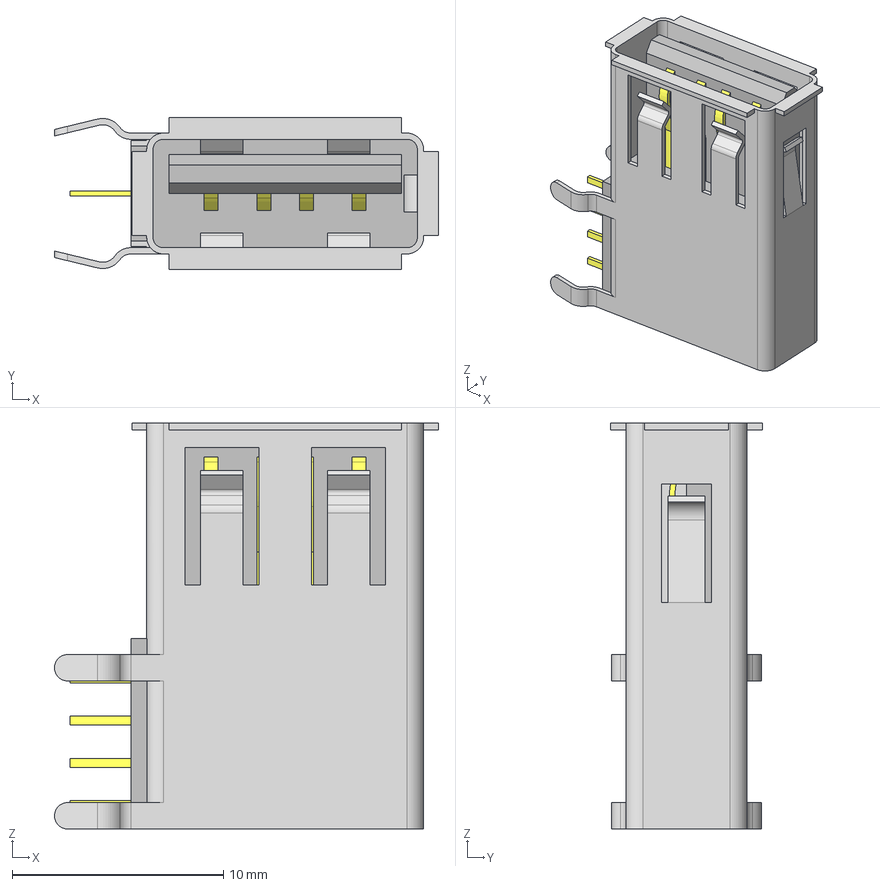
[picture p53: CAD file, 2021-10-07]
HARDWARE/STMP157-OLinuXino-LIME2/1. Latest hardware revision/STMP157-OLinuXino-LIME2_Rev_B1/3d/USB-A-S-F-B-VU.stp
18.2 x 7.20 x 19.2 mm
_USB-A-S-VU_S
_USB-A-S-B-VU_B
_USB-A-S-VU_P
