OLIMEX/OLINUXINO/HARDWARE/A64-OLinuXino/1. Latest hardware revision/A64-OLinuXino hardware revision G/3d/bga-81-2.step

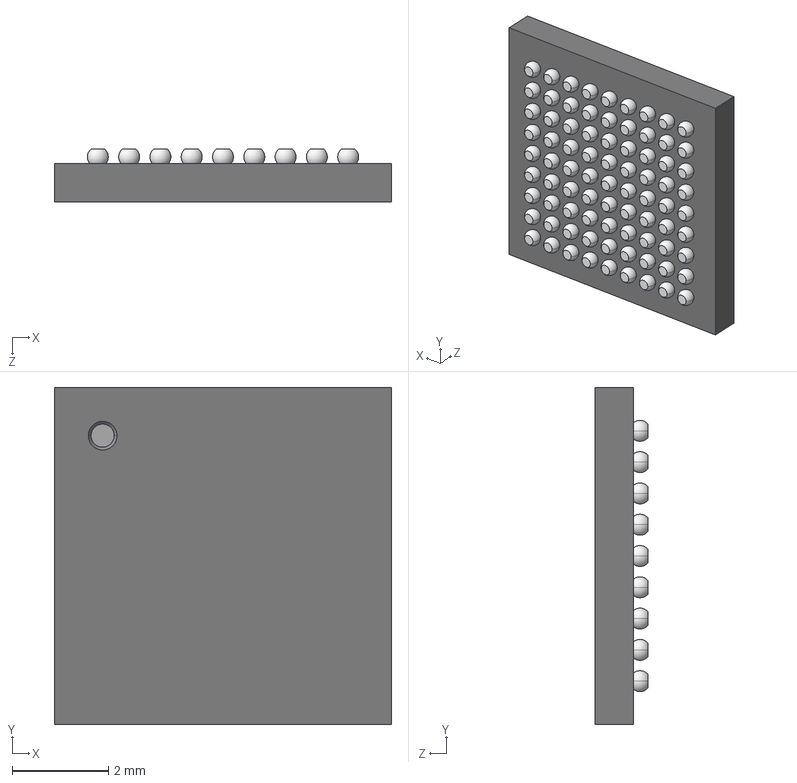
[picture p54: CAD file, 2021-03-23]
HARDWARE/A64-OLinuXino/1. Latest hardware revision/A64-OLinuXino hardware revision G/3d/bga-81-2.step
7.00 x 7.00 x 1.10 mm
