OLIMEX/OLINUXINO/HARDWARE/LCDs/LCD-DRIVER/Hardware revision C/3d/FPA-WZB25-04-LF.stp

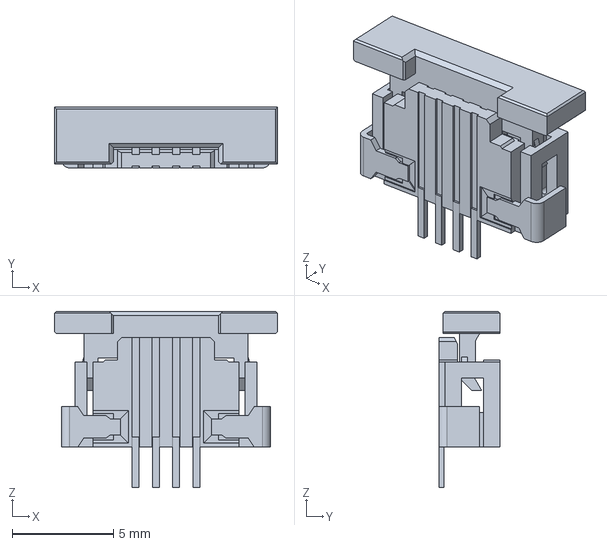
[picture p55: CAD file, 2020-01-09]
HARDWARE/LCDs/LCD-DRIVER/Hardware revision C/3d/FPA-WZB25-04-LF.stp
11.0 x 3.00 x 8.70 mm
