OLIMEX/OLINUXINO/HARDWARE/A64-OLinuXino/1. Latest hardware revision/A64-OLinuXino hardware revision G/3d/SOT-223-2.STEP

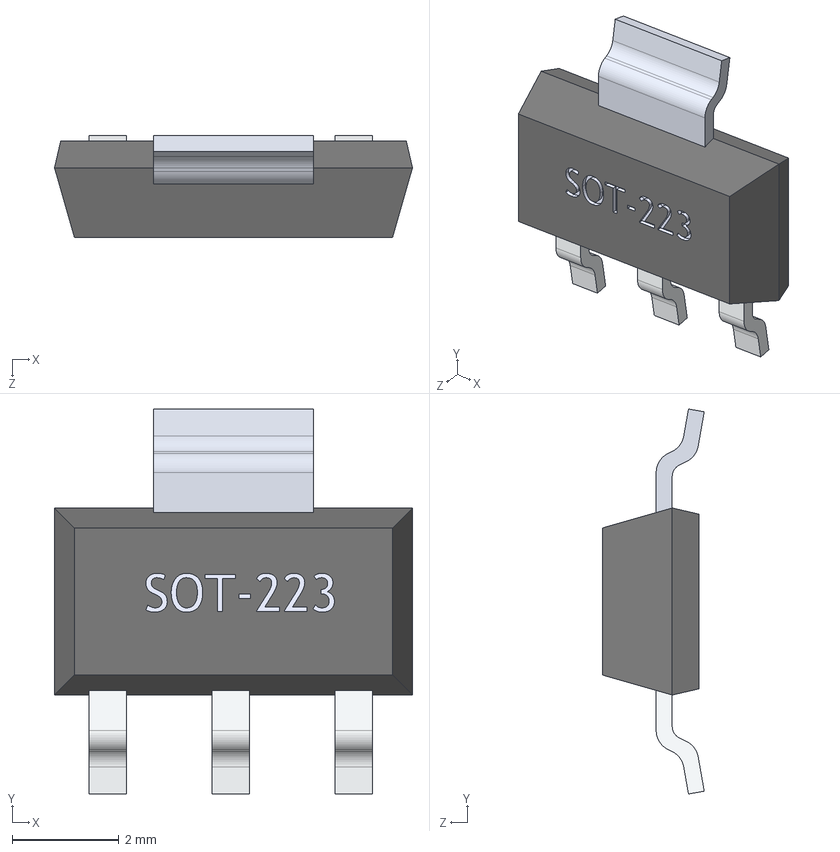
[picture p56: CAD file, 2021-03-23]
HARDWARE/A64-OLinuXino/1. Latest hardware revision/A64-OLinuXino hardware revision G/3d/SOT-223-2.STEP
6.70 x 7.20 x 1.90 mm
User Library-SOT-223-2_PIN_SOT-223_2_1 x 3
User Library-SOT-223-2_SOT-223_1
User Library-SOT-223-2_PIN_SOT-223_1
