OLIMEX/OLINUXINO/HARDWARE/STMP157-OLinuXino-LIME2/1. Latest hardware revision/STMP157-OLinuXino-LIME2_Rev_B1/3d/L-CD75(YS75)_7.80x7.00x5.50mm.step

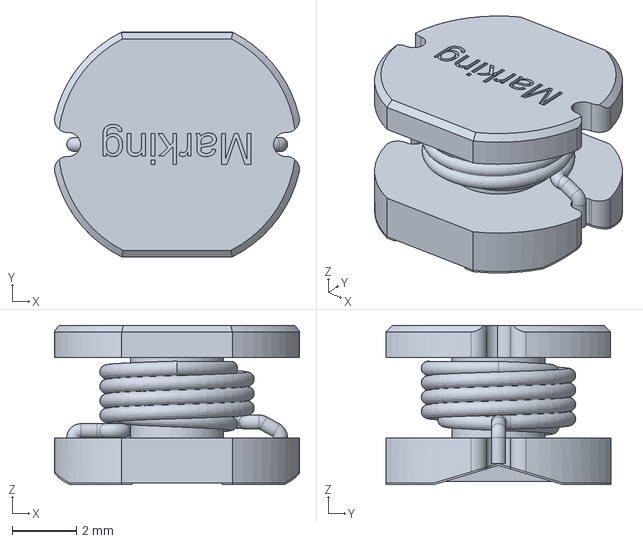
[picture p58: CAD file, 2021-10-07]
HARDWARE/STMP157-OLinuXino-LIME2/1. Latest hardware revision/STMP157-OLinuXino-LIME2_Rev_B1/3d/L-CD75(YS75)_7.80x7.00x5.50mm.step
7.63 x 7.00 x 4.95 mm
