OLIMEX/OLINUXINO/HARDWARE/A64-OLinuXino/1. Latest hardware revision/A64-OLinuXino hardware revision G/3d/it1185.step

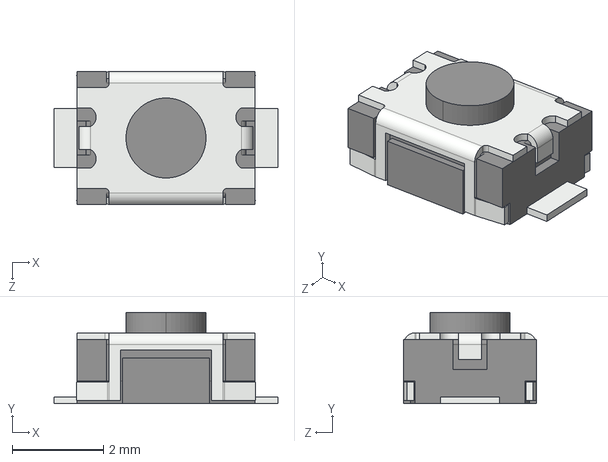
[picture p59: CAD file, 2021-03-23]
HARDWARE/A64-OLinuXino/1. Latest hardware revision/A64-OLinuXino hardware revision G/3d/it1185.step
4.90 x 2.00 x 2.90 mm
