OLIMEX/OLINUXINO/HARDWARE/STMP157-OLinuXino-LIME2/1. Latest hardware revision/STMP157-OLinuXino-LIME2_Rev_B1/3d/DF12(3.0)-40DS-0.5V.stp

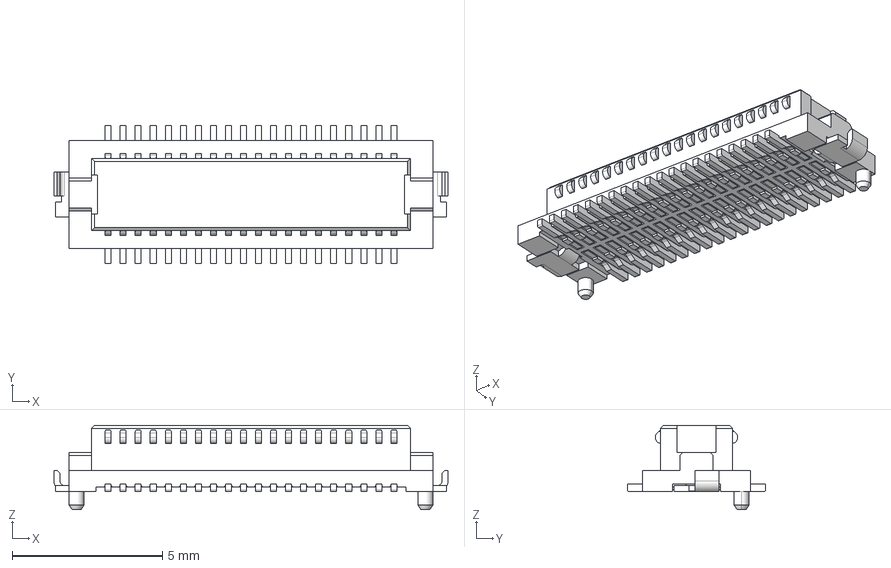
[picture p60: CAD file, 2021-10-07]
HARDWARE/STMP157-OLinuXino-LIME2/1. Latest hardware revision/STMP157-OLinuXino-LIME2_Rev_B1/3d/DF12(3.0)-40DS-0.5V.stp
13.1 x 4.60 x 2.80 mm
