OLIMEX/OLINUXINO/HARDWARE/STMP157-OLinuXino-LIME2/1. Latest hardware revision/STMP157-OLinuXino-LIME2_Rev_B1/3d/QFN-48_6x6mm_Pitch-0.4mm.STEP

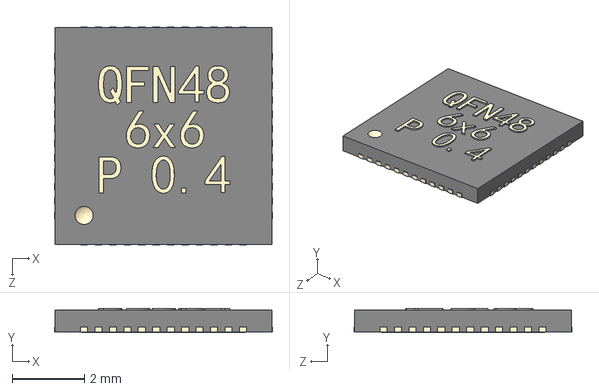
[picture p61: CAD file, 2021-10-07]
HARDWARE/STMP157-OLinuXino-LIME2/1. Latest hardware revision/STMP157-OLinuXino-LIME2_Rev_B1/3d/QFN-48_6x6mm_Pitch-0.4mm.STEP
6.04 x 0.67 x 6.04 mm
