OLIMEX/OLINUXINO/HARDWARE/A64-OLinuXino/1. Latest hardware revision/A64-OLinuXino hardware revision G/3d/DFN6(Body-2x2mm_Hight-1mm_Pitch-0,65mm).step

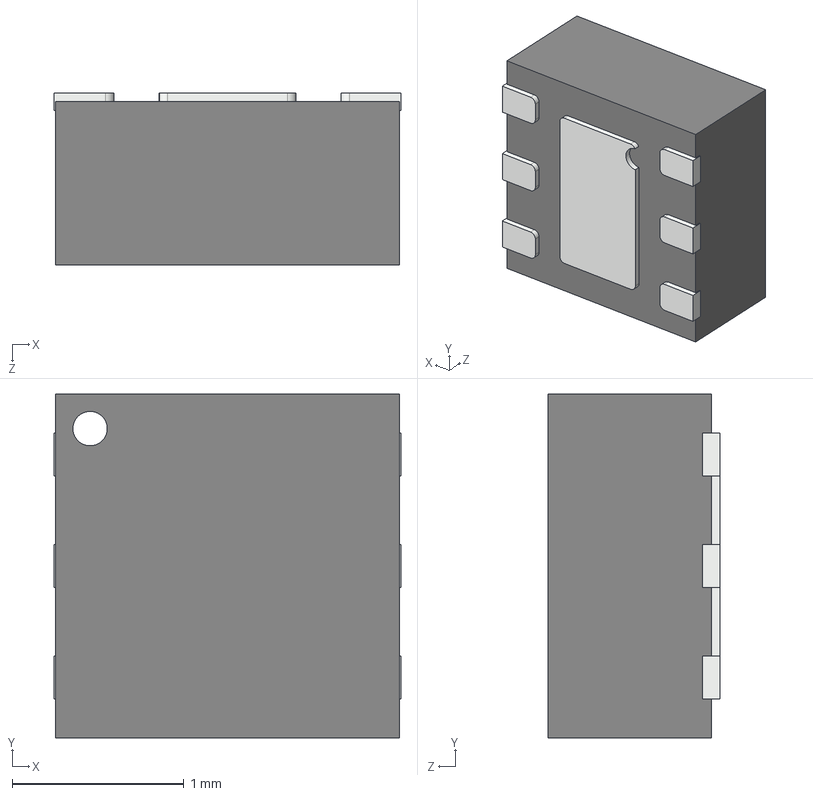
[picture p65: CAD file, 2021-03-23]
HARDWARE/A64-OLinuXino/1. Latest hardware revision/A64-OLinuXino hardware revision G/3d/DFN6(Body-2x2mm_Hight-1mm_Pitch-0,65mm).step
2.02 x 2.00 x 1.00 mm
