OLIMEX/OLINUXINO/HARDWARE/A64-OLinuXino/1. Latest hardware revision/A64-OLinuXino hardware revision G/3d/SMD5032.STEP

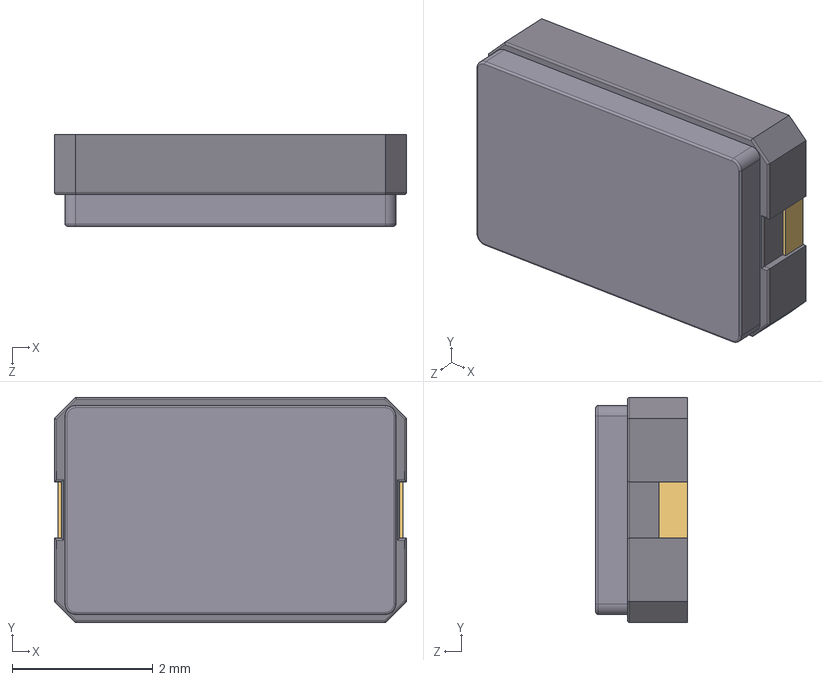
[picture p68: CAD file, 2021-03-23]
HARDWARE/A64-OLinuXino/1. Latest hardware revision/A64-OLinuXino hardware revision G/3d/SMD5032.STEP
5.00 x 3.20 x 1.30 mm
User Library-ABM3-1_Fillet002
User Library-ABM3-1_Fillet001
User Library-ABM3-1_Pad001
