OLIMEX/OLINUXINO/HARDWARE/STMP157-OLinuXino-LIME2/1. Latest hardware revision/STMP157-OLinuXino-LIME2_Rev_B1/3d/TFC-WPAPR-08---112J-TXAR-R_C_1-1.STEP

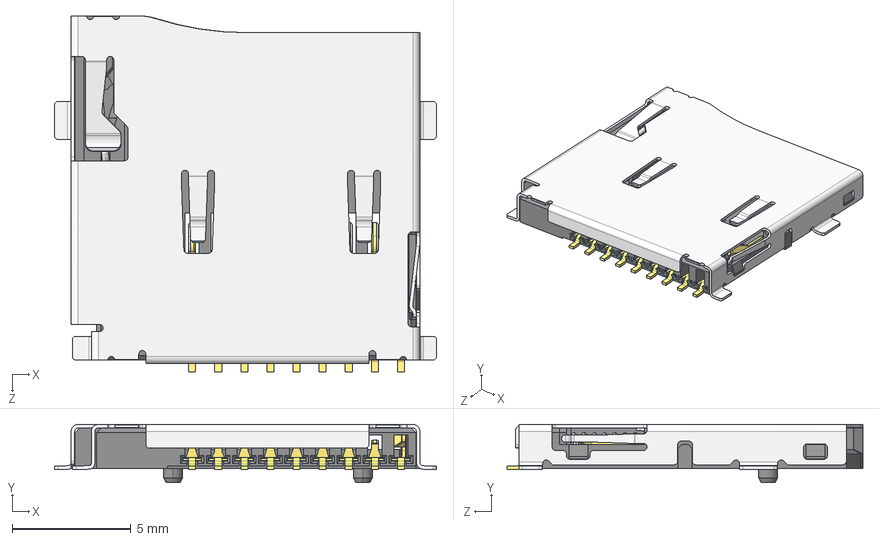
[picture p70: CAD file, 2021-10-07]
HARDWARE/STMP157-OLinuXino-LIME2/1. Latest hardware revision/STMP157-OLinuXino-LIME2_Rev_B1/3d/TFC-WPAPR-08---112J-TXAR-R_C_1-1.STEP
16.1 x 2.45 x 15.0 mm
