OLIMEX/OLINUXINO/HARDWARE/A64-OLinuXino/1. Latest hardware revision/A64-OLinuXino hardware revision G/3d/SO-8_208mil---SOIC8_Wide_5mmx5mm.step

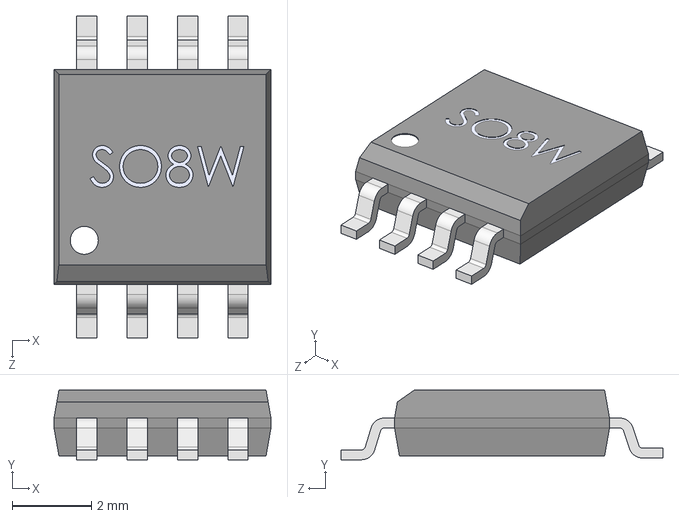
[picture p71: CAD file, 2021-03-23]
HARDWARE/A64-OLinuXino/1. Latest hardware revision/A64-OLinuXino hardware revision G/3d/SO-8_208mil---SOIC8_Wide_5mmx5mm.step
5.46 x 1.75 x 8.10 mm
