OLIMEX/OLINUXINO/HARDWARE/STMP157-OLinuXino-LIME2/1. Latest hardware revision/STMP157-OLinuXino-LIME2_Rev_B1/3d/SO-8_150mil---SN65HVDA1050AQDRQ1.STEP

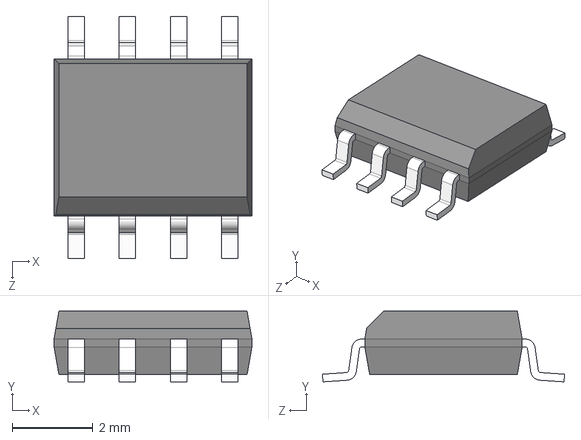
[picture p72: CAD file, 2021-10-07]
HARDWARE/STMP157-OLinuXino-LIME2/1. Latest hardware revision/STMP157-OLinuXino-LIME2_Rev_B1/3d/SO-8_150mil---SN65HVDA1050AQDRQ1.STEP
4.90 x 1.75 x 5.99 mm
