OLIMEX/OLINUXINO/HARDWARE/A64-OLinuXino/1. Latest hardware revision/A64-OLinuXino hardware revision G/3d/L-CD43_shielded.STEP

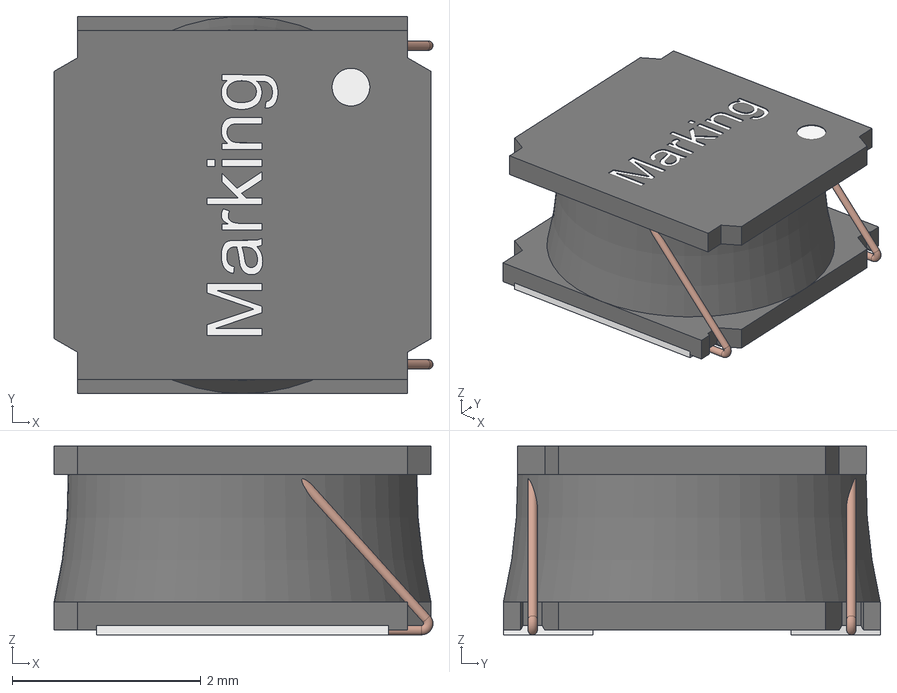
[picture p74: CAD file, 2021-03-23]
HARDWARE/A64-OLinuXino/1. Latest hardware revision/A64-OLinuXino hardware revision G/3d/L-CD43_shielded.STEP
4.02 x 4.00 x 2.00 mm
housing
contact x 2
Glue
Wire x 2
