OLIMEX/OLINUXINO/HARDWARE/A64-OLinuXino/1. Latest hardware revision/A64-OLinuXino hardware revision G/3d/BL-R8723BT1module.STEP

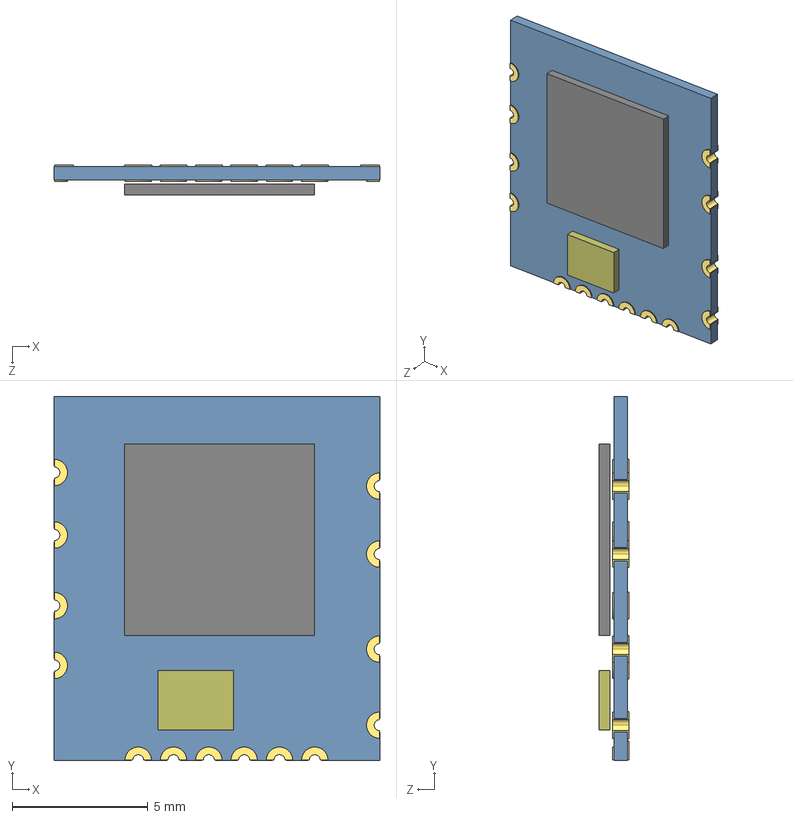
[picture p77: CAD file, 2021-03-23]
HARDWARE/A64-OLinuXino/1. Latest hardware revision/A64-OLinuXino hardware revision G/3d/BL-R8723BT1module.STEP
12.0 x 13.4 x 1.10 mm
User Library-BL-R8723BT1 module_Part_113087
User Library-BL-R8723BT1 module_Part_113087_2
User Library-BL-R8723BT1 module_Part_123053
User Library-BL-R8723BT1 module_Part_156259
User Library-BL-R8723BT1 module_Part_126661
User Library-BL-R8723BT1 module_Part_126661_2
User Library-BL-R8723BT1 module_Part_126661_3
User Library-BL-R8723BT1 module_Part_126661_4
User Library-BL-R8723BT1 module_Part_126661_5
User Library-BL-R8723BT1 module_Part_156259_2
User Library-BL-R8723BT1 module_Part_126661_6
User Library-BL-R8723BT1 module_Part_126661_7
User Library-BL-R8723BT1 module_Part_126661_8
User Library-BL-R8723BT1 module_Part_126661_9
User Library-BL-R8723BT1 module_Part_126661_10
User Library-BL-R8723BT1 module_Part_126661_11
User Library-BL-R8723BT1 module_Part_156259_3
