OLIMEX/OLINUXINO/HARDWARE/A64-OLinuXino/1. Latest hardware revision/A64-OLinuXino hardware revision G/3d/FPV-WZA21-20-LF_Molex-527452033.stp

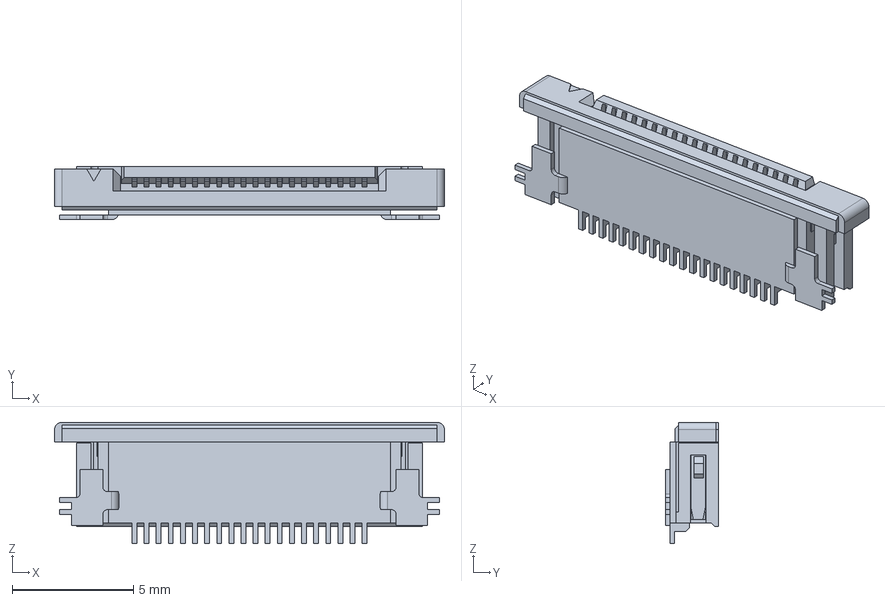
[picture p79: CAD file, 2021-03-23]
HARDWARE/A64-OLinuXino/1. Latest hardware revision/A64-OLinuXino hardware revision G/3d/FPV-WZA21-20-LF_Molex-527452033.stp
16.1 x 2.20 x 5.00 mm
