OLIMEX/OLINUXINO/HARDWARE/STMP157-OLinuXino-LIME2/1. Latest hardware revision/STMP157-OLinuXino-LIME2_Rev_B1/3d/JST_B2B-PH-SM4-TB(DW02R).step

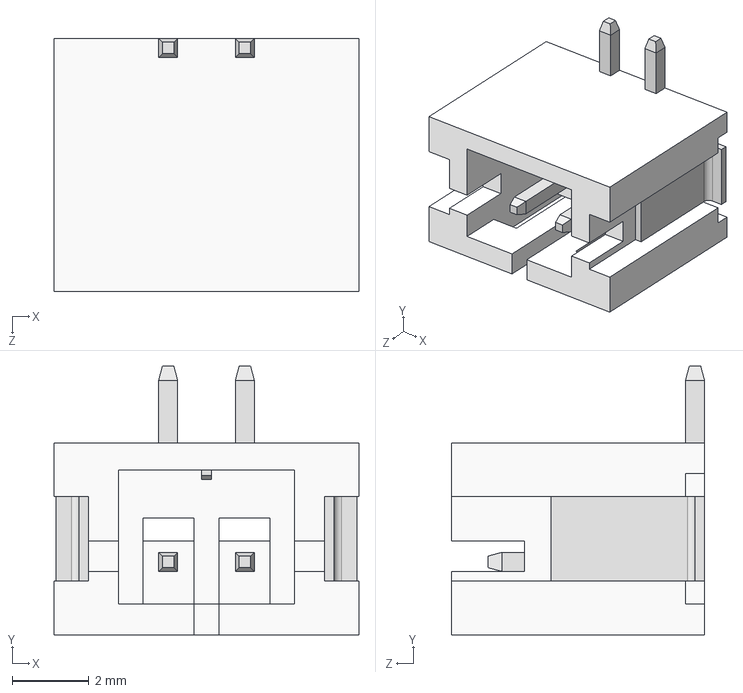
[picture p81: CAD file, 2021-10-07]
HARDWARE/STMP157-OLinuXino-LIME2/1. Latest hardware revision/STMP157-OLinuXino-LIME2_Rev_B1/3d/JST_B2B-PH-SM4-TB(DW02R).step
7.95 x 7.00 x 6.60 mm
