OLIMEX/OLINUXINO/HARDWARE/A64-OLinuXino/1. Latest hardware revision/A64-OLinuXino hardware revision G/3d/U_FL-R-SMT-1.step

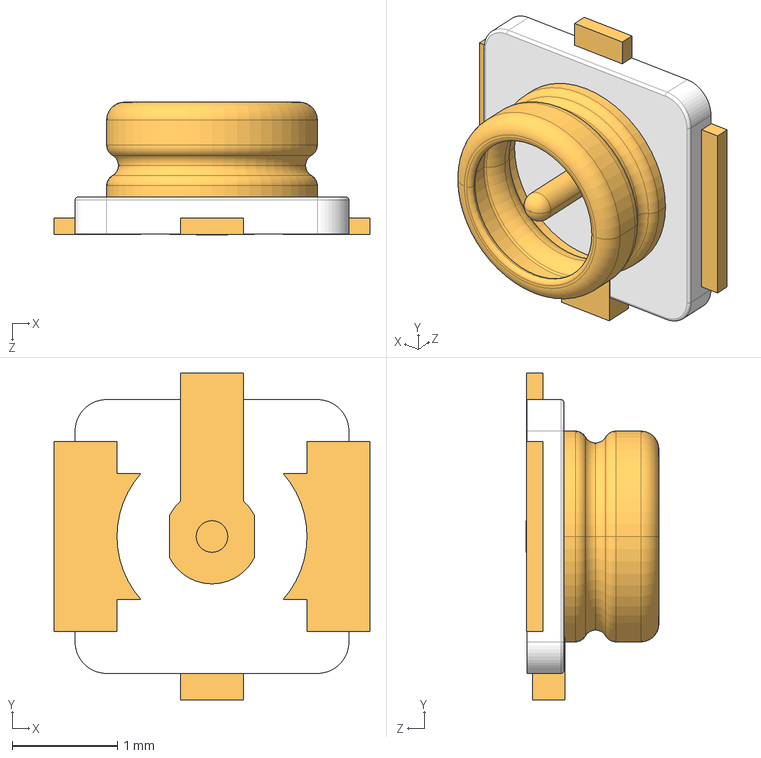
[picture p82: CAD file, 2021-03-23]
HARDWARE/A64-OLinuXino/1. Latest hardware revision/A64-OLinuXino hardware revision G/3d/U_FL-R-SMT-1.step
3.00 x 3.10 x 1.26 mm
