OLIMEX/OLINUXINO/HARDWARE/A64-OLinuXino/1. Latest hardware revision/A64-OLinuXino hardware revision G/3d/FPV-WZA21-40-LF_Molex-541044033.stp

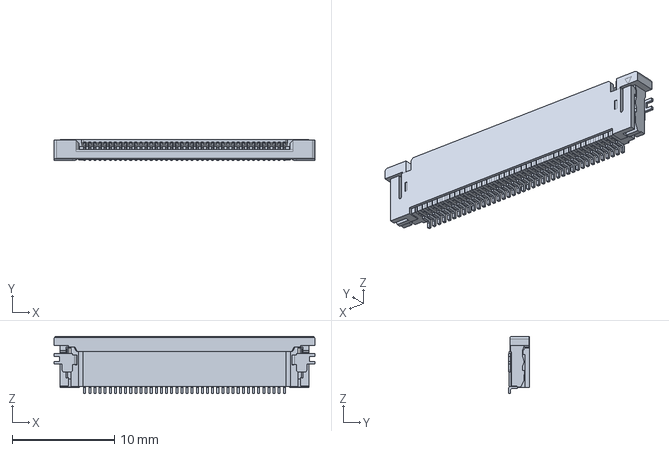
[picture p85: CAD file, 2020-01-09]
HARDWARE/A64-OLinuXino/1. Latest hardware revision/A64-OLinuXino hardware revision G/3d/FPV-WZA21-40-LF_Molex-541044033.stp
25.5 x 2.05 x 5.60 mm
