OLIMEX/OLINUXINO/HARDWARE/STMP157-OLinuXino-LIME2/1. Latest hardware revision/STMP157-OLinuXino-LIME2_Rev_B1/3d/HN1x3-PinHeader_1x03_P2.54mm_Vertical.step

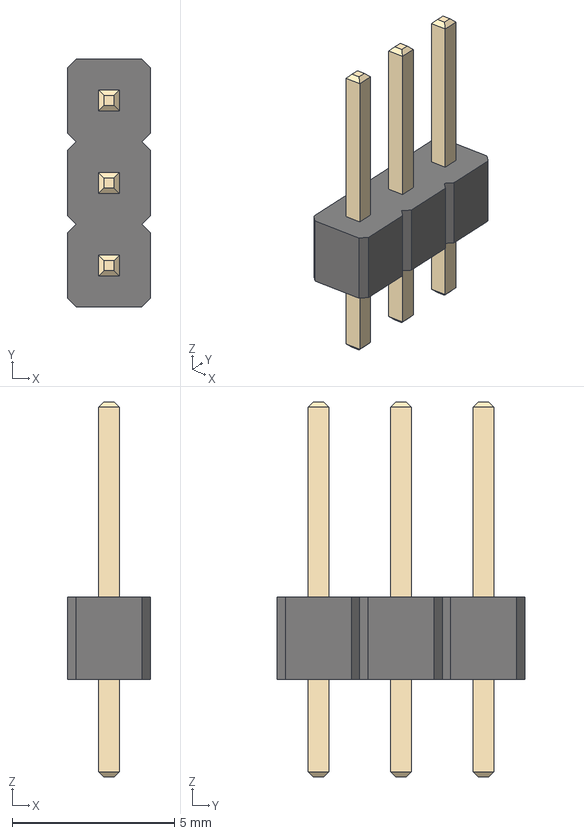
[picture p86: CAD file, 2021-03-23]
HARDWARE/STMP157-OLinuXino-LIME2/1. Latest hardware revision/STMP157-OLinuXino-LIME2_Rev_B1/3d/HN1x3-PinHeader_1x03_P2.54mm_Vertical.step
2.54 x 7.62 x 11.5 mm
