OLIMEX/OLINUXINO/HARDWARE/STMP157-OLinuXino-LIME2/1. Latest hardware revision/STMP157-OLinuXino-LIME2_Rev_B1/3d/HN1x2-PinHeader_1x02_P2.54mm_Vertical.step

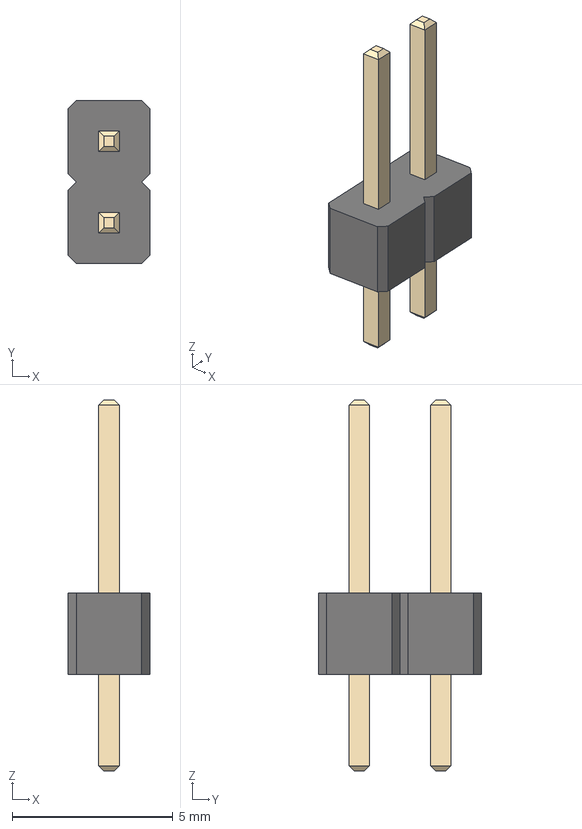
[picture p87: CAD file, 2021-03-23]
HARDWARE/STMP157-OLinuXino-LIME2/1. Latest hardware revision/STMP157-OLinuXino-LIME2_Rev_B1/3d/HN1x2-PinHeader_1x02_P2.54mm_Vertical.step
2.54 x 5.08 x 11.5 mm
