OLIMEX/OLINUXINO/HARDWARE/A10-OLinuXino-LIME/A10-OLinuXino-Lime-4GB_Rev_E.pdf

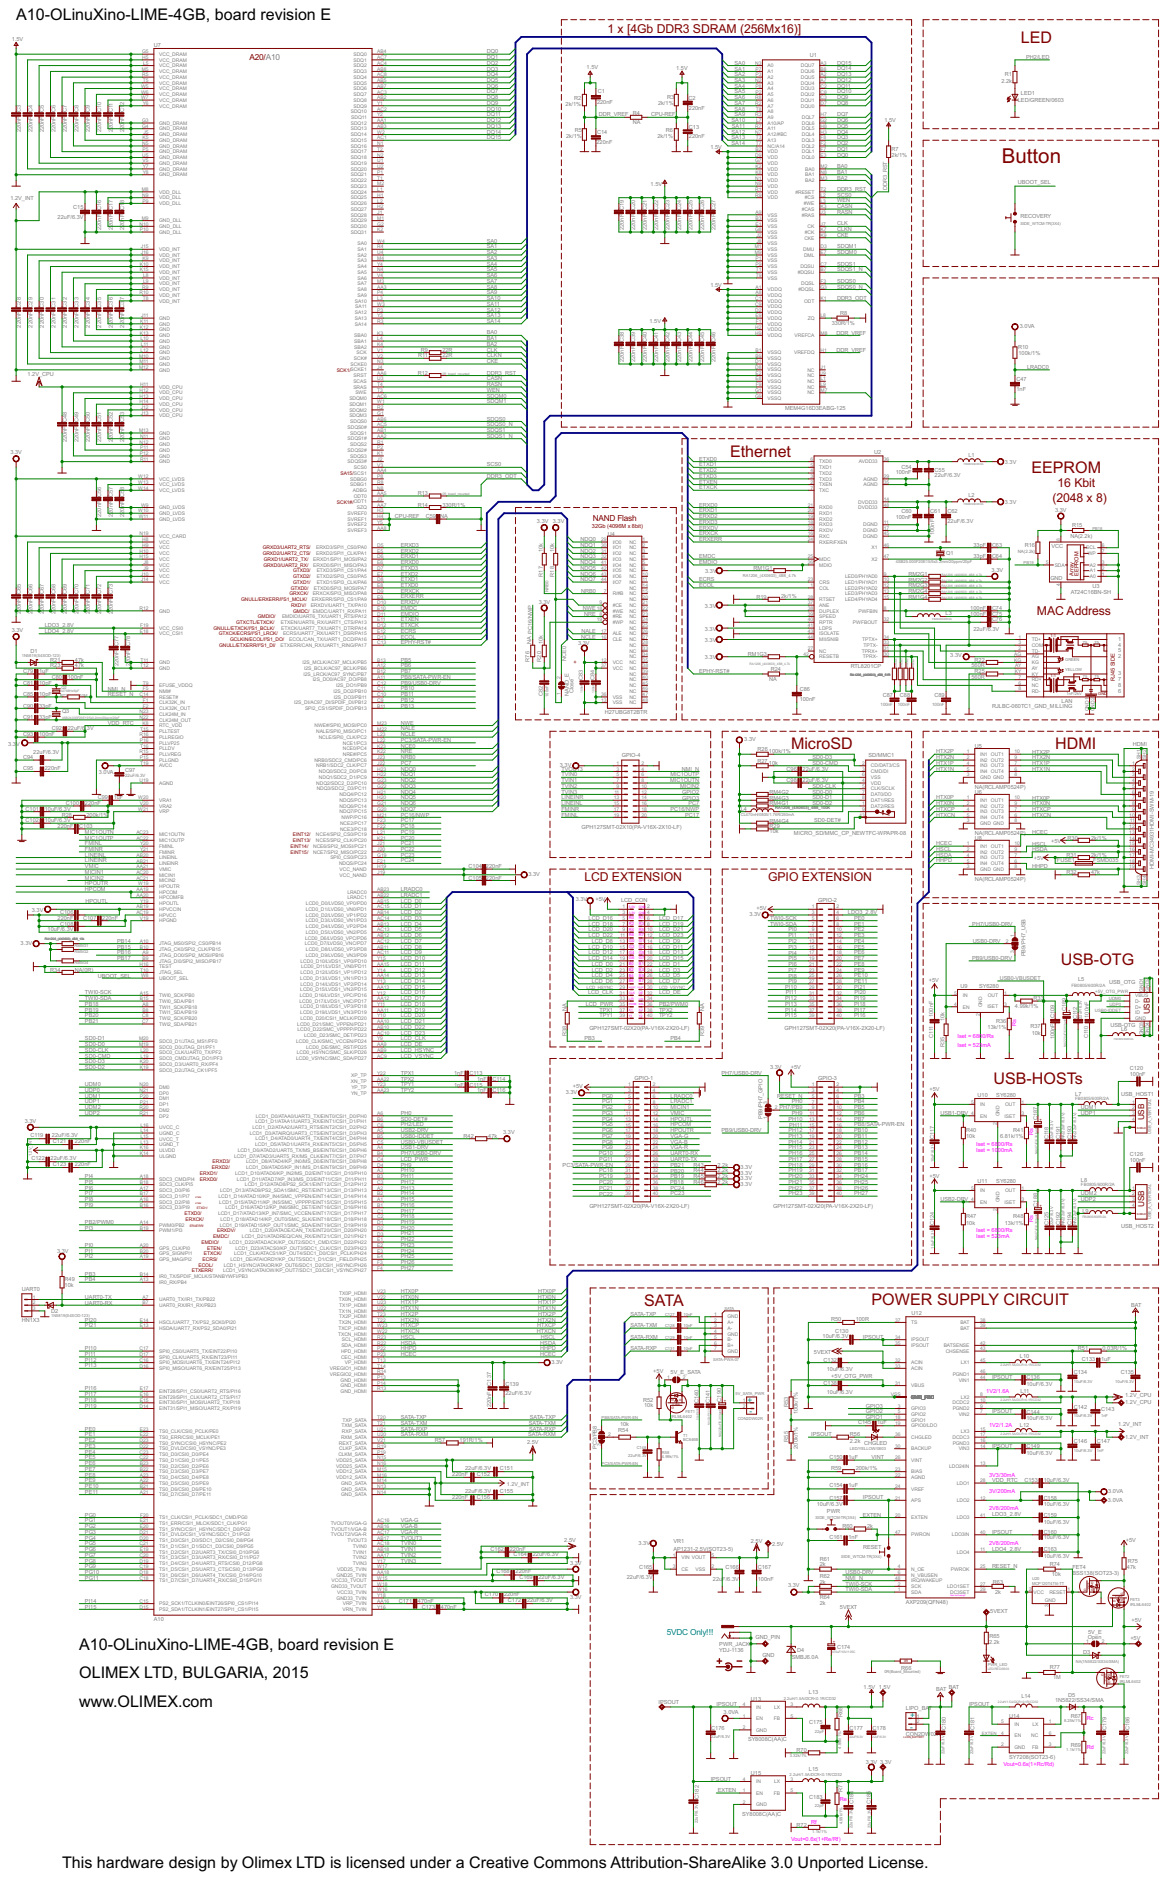
[picture p137: page 1]

A10-OLinuXino-LIME-4GB, board revision E

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

NA(47uF/6.3V/tant)

OLIMEX LTD, BULGARIA, 2015
www.OLIMEX.com

Rc Rd Vout=0.6x(1+Rc/Rd) Re Rf Vout=0.6x(1+Re/Rf)

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
