OLIMEX/OLINUXINO/HARDWARE/A13-OLinuXino/A13-OLinuXino_WIFI_Rev_G.pdf

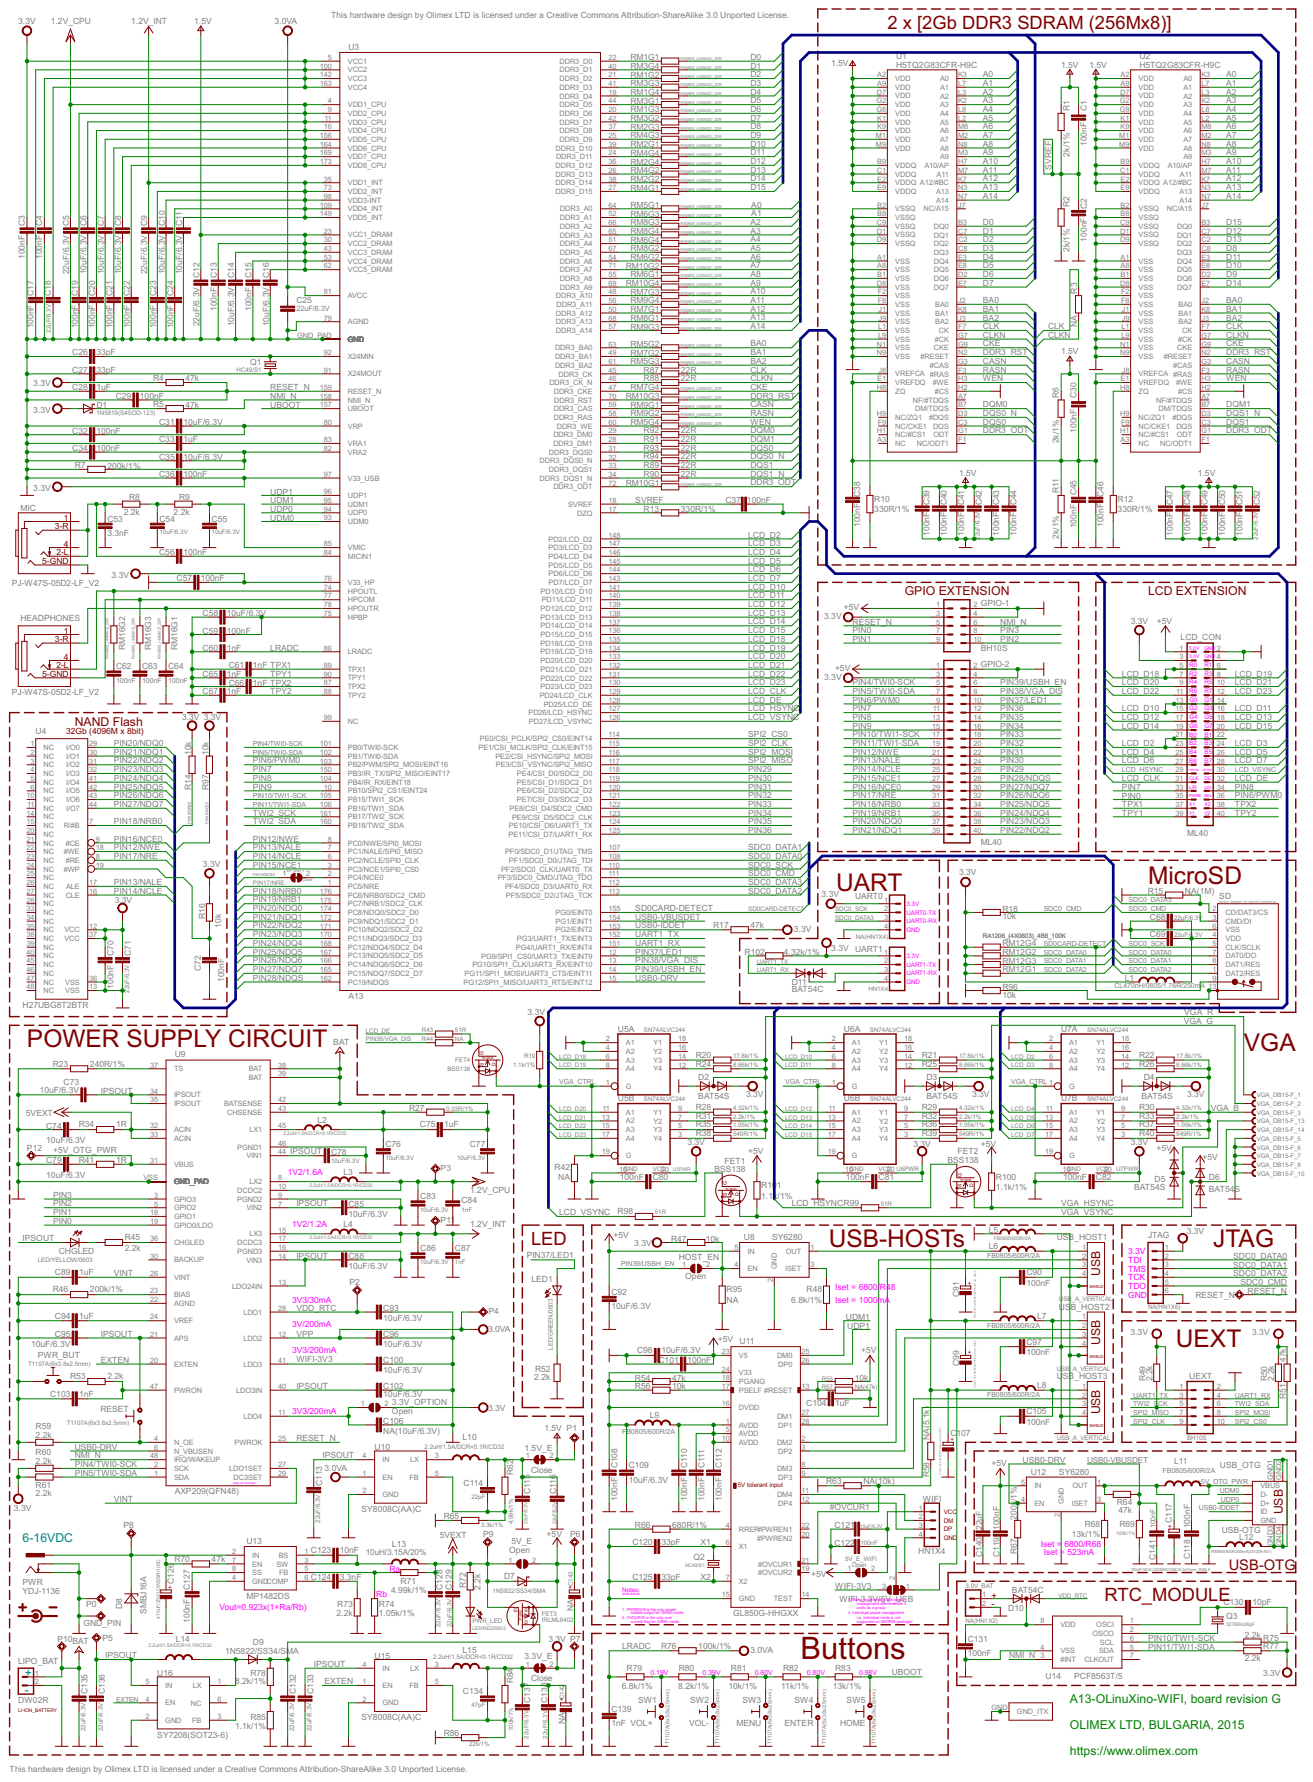
[picture p138: page 1]
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

30
43 | 67
62 | 54 DDR3_A8 71

management affects whole 4 Ra Rb Vout=0.923x(1+Ra/Rb)

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

A13-OLinuXino-WIFI, board revision G

https://www.olimex.com
