OLIMEX/OLINUXINO/HARDWARE/iMX233-OLinuXino-Micro/iMX233-OLinuXino-Micro_Rev_D.pdf

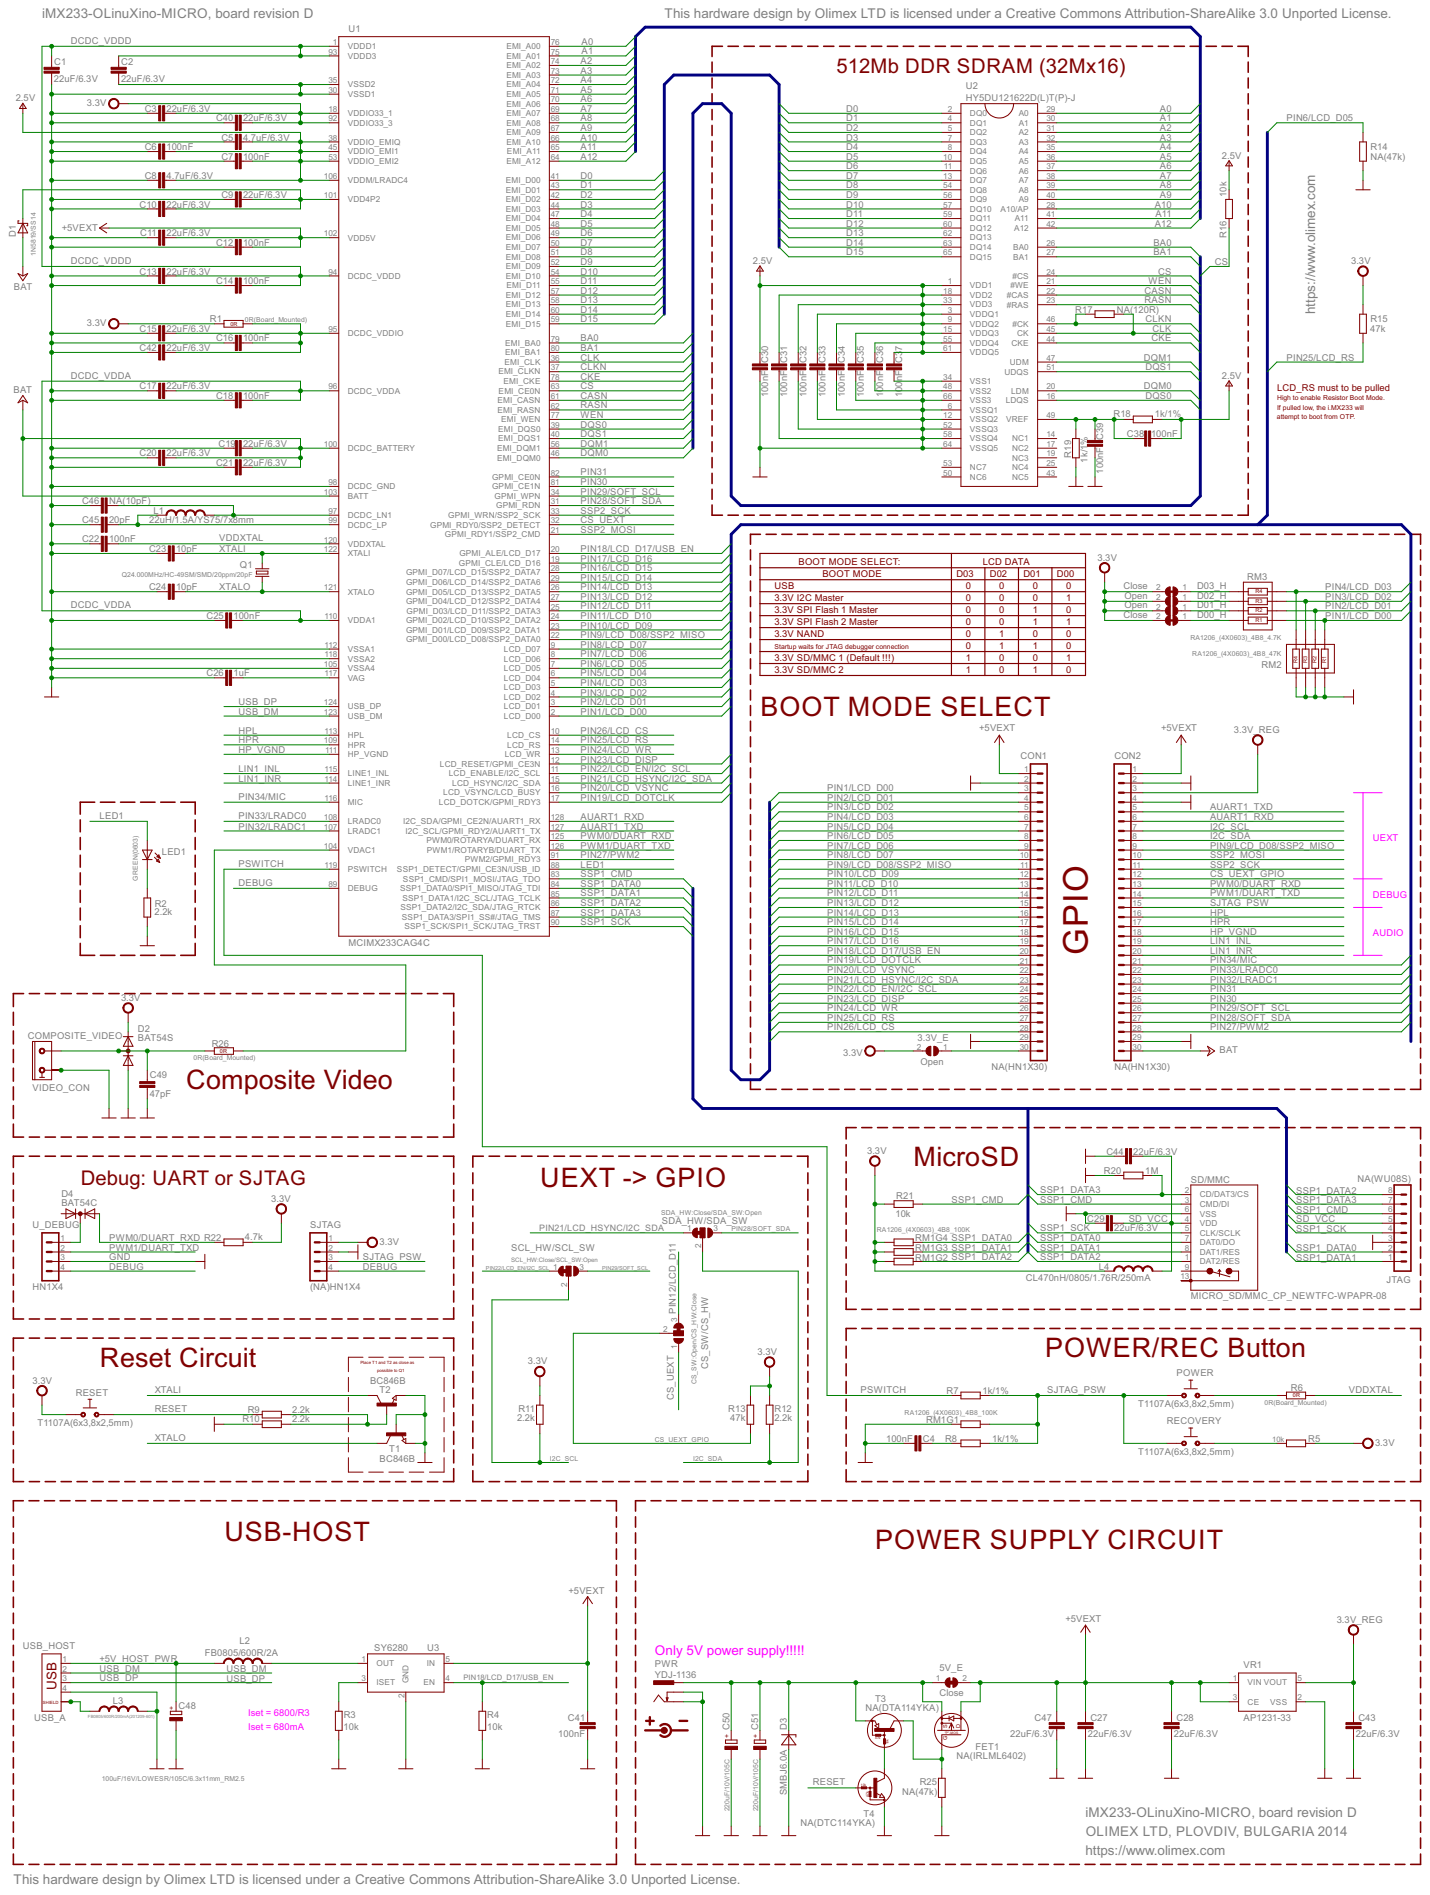
[picture p139: page 1]

iMX233-OLinuXino-MICRO, board revision D

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

LCD_RS must to be pulled

High to enable Resistor Boot Mode.
If pulled low, the i.MX233 will attempt to boot from OTP.

BOOT MODE SELECT: | LCD DATA
BOOT MODE | D03 0 | D02 0 | D01 0 | D00 USB 0

3.3V I2C Master 3.3V SPI Flash 1 Master 3.3V SPI Flash 2 Master 3.3V NAND

Close Open Open Close

Startup waits for JTAG debugger connection 3.3V SD/MMC 1 (Default !!!) 3.3V SD/MMC 2 | 1 | 0 | 0 | 1

Debug: UART or SJTAG

OLIMEX LTD, PLOVDIV, BULGARIA 2014
https://www.olimex.com
