OLIMEX/OLINUXINO/HARDWARE/iMX233-OLinuXino-Maxi/iMX233-OLINUXINO-MAXI_Rev_C2.sch.pdf

EMI_A12 | 64 EMI_A11 | 65 EMI_A10 | 66 EMI_A09 | 67 EMI_A08 | 68 EMI_A07 | 69 EMI_A06 | 70 EMI_A05 | 71 EMI_A04 | 72 EMI_A03 | 73 EMI_A02 | 74 EMI_A01 | 75 EMI_A00 | 76

# 512Mb DDR SDRAM (32Mx16)

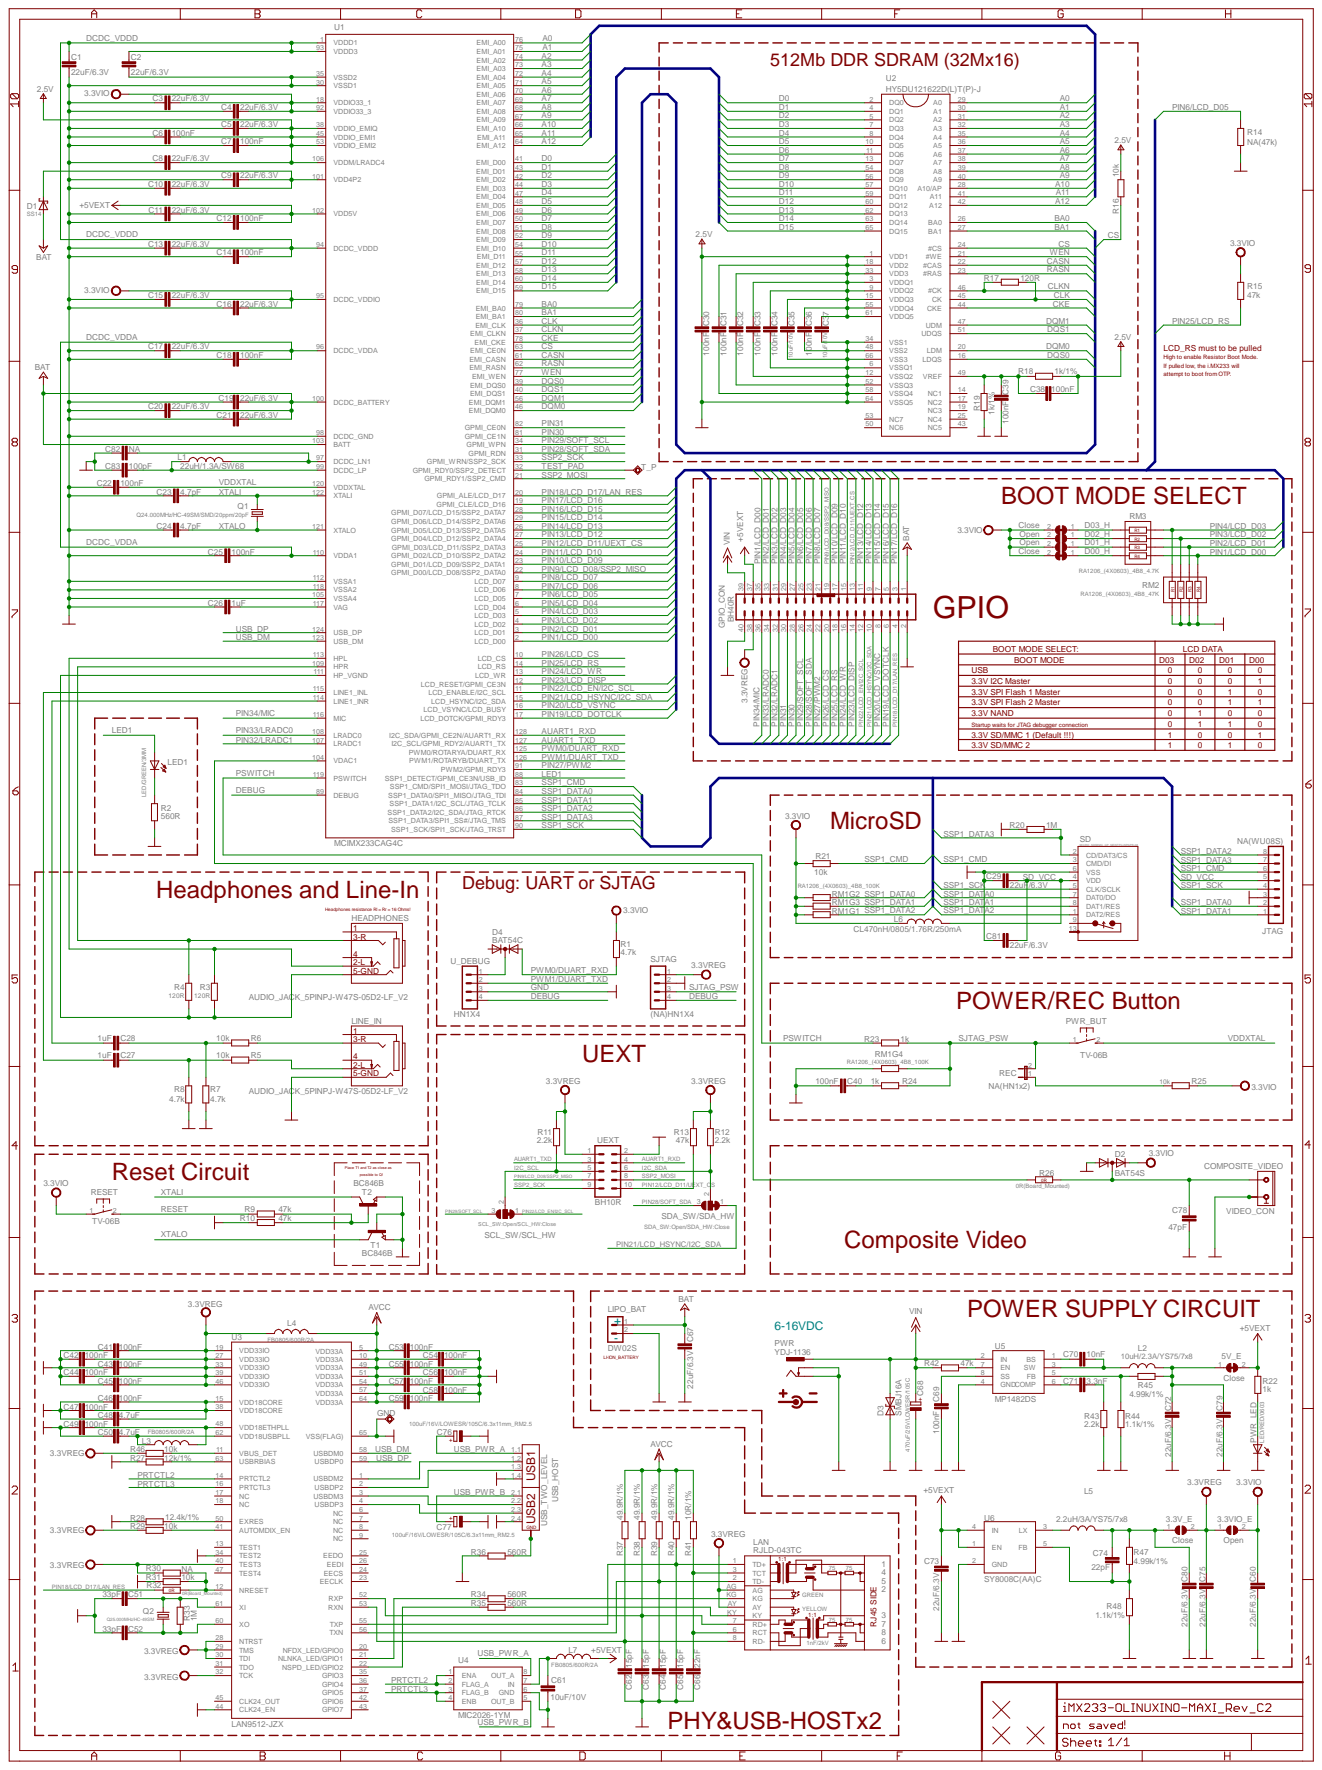
[picture p140: page 1]
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

3.3V I2C Master
3.3V SPI Flash 1 Master
3.3V SPI Flash 2 Master
3.3V NAND
Startup waits for JTAG debugger connection
3.3V SD/MMC 1 (Default !!!)
3.3V SD/MMC 2

Headphones and Line-In

Debug: UART or SJTAG

2 PWM1/DUART_TXD | 2
