OLIMEX/OLINUXINO/HARDWARE/A13-OLinuXino/A13-OLinuXino_WIFI_Rev_E.sch.pdf

# 2 x [2Gb DDR3 SDRAM (256Mx8)]

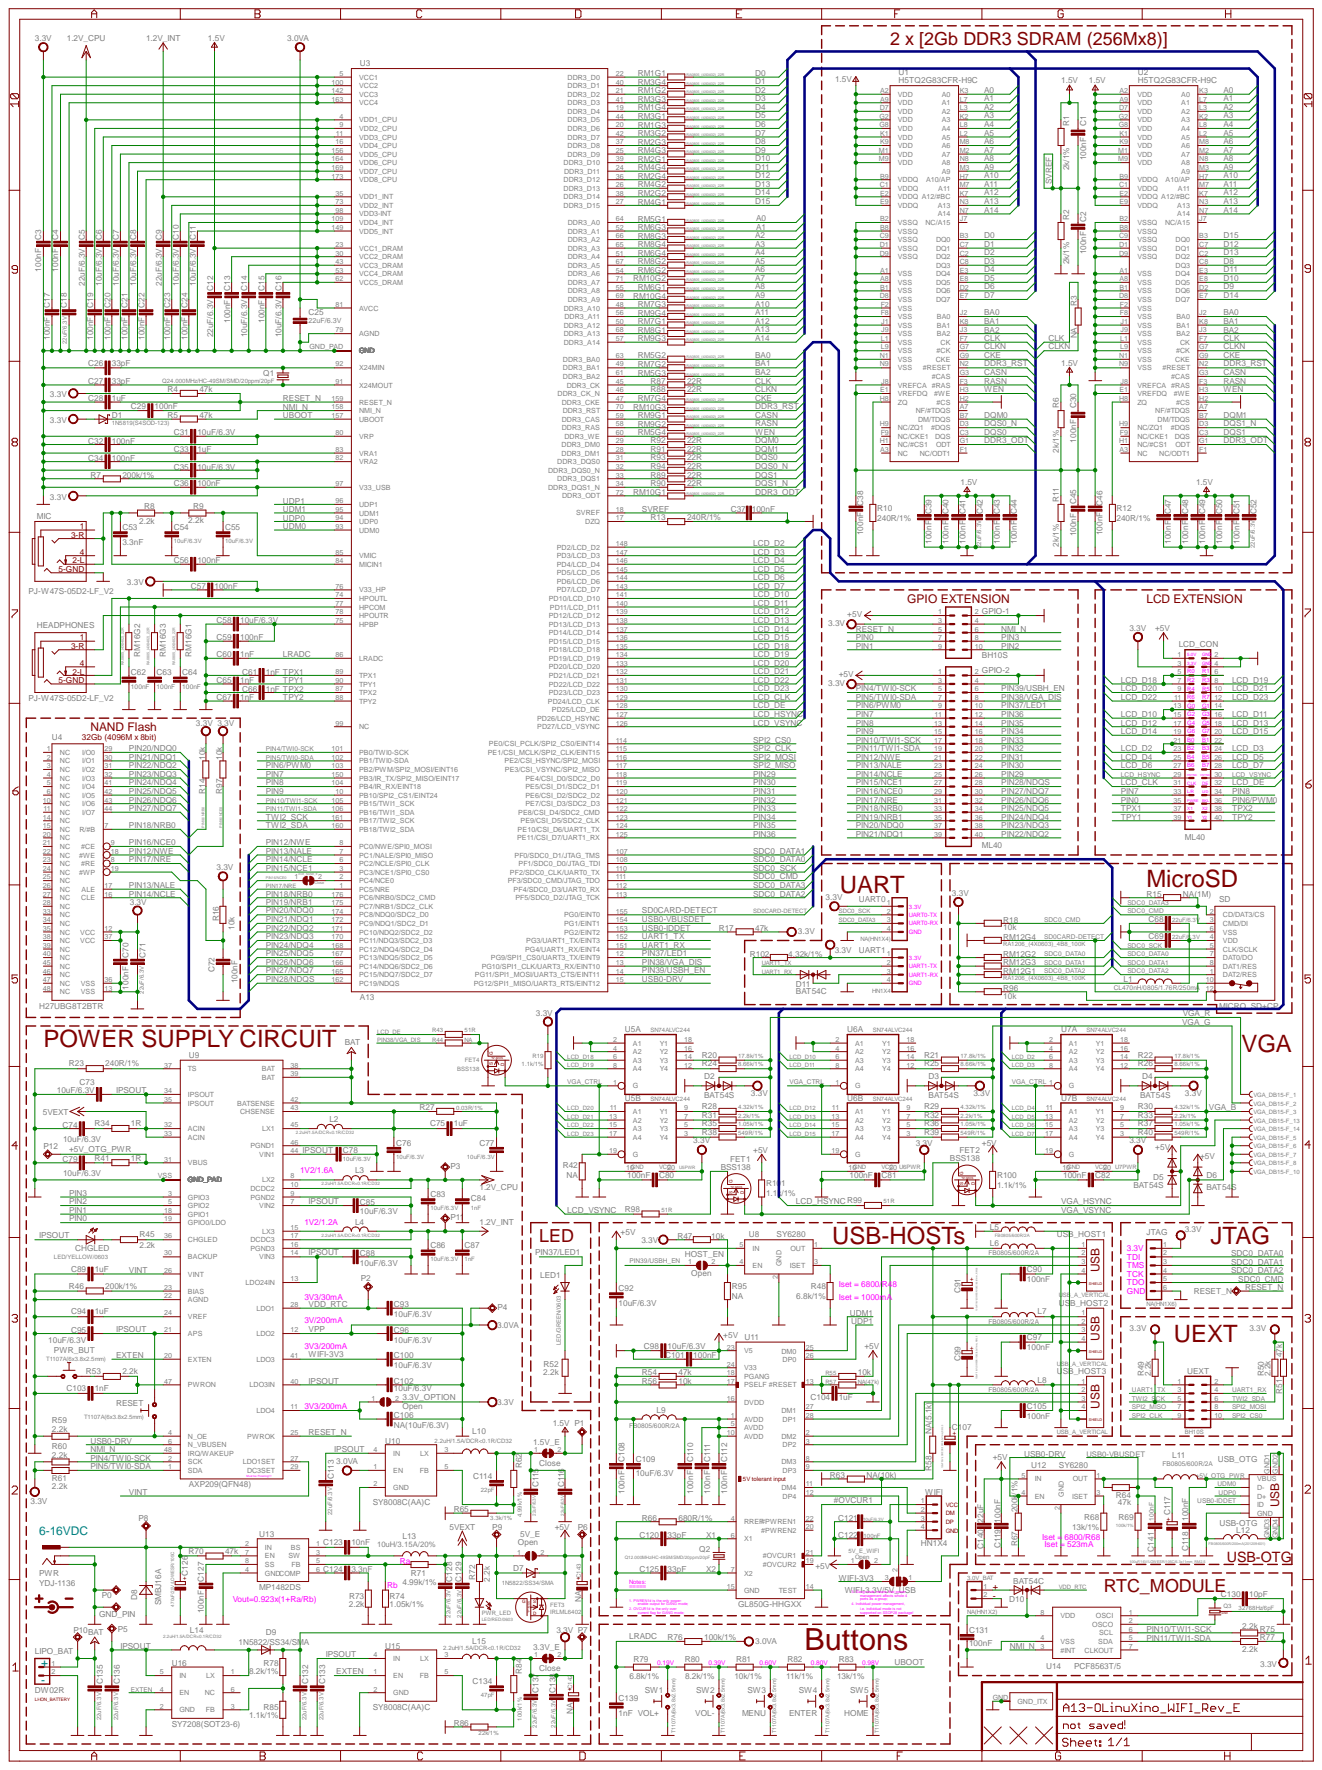
[picture p141: page 1]

1. PWREN1# is the only power-
enable output for GANG mode;
2. OVCUR1# is the only over
current flag for GANG mode;

3. Gang mode means that power
management affects whole 4
ports as a group;
4. Individual power management,
i.e. individual mode is not
supported on SSOP28 package!
