OLIMEX/OLINUXINO/HARDWARE/iMX233-OLinuXino-NANO/iMX233-OLinuXino-NANO_Rev_B.pdf

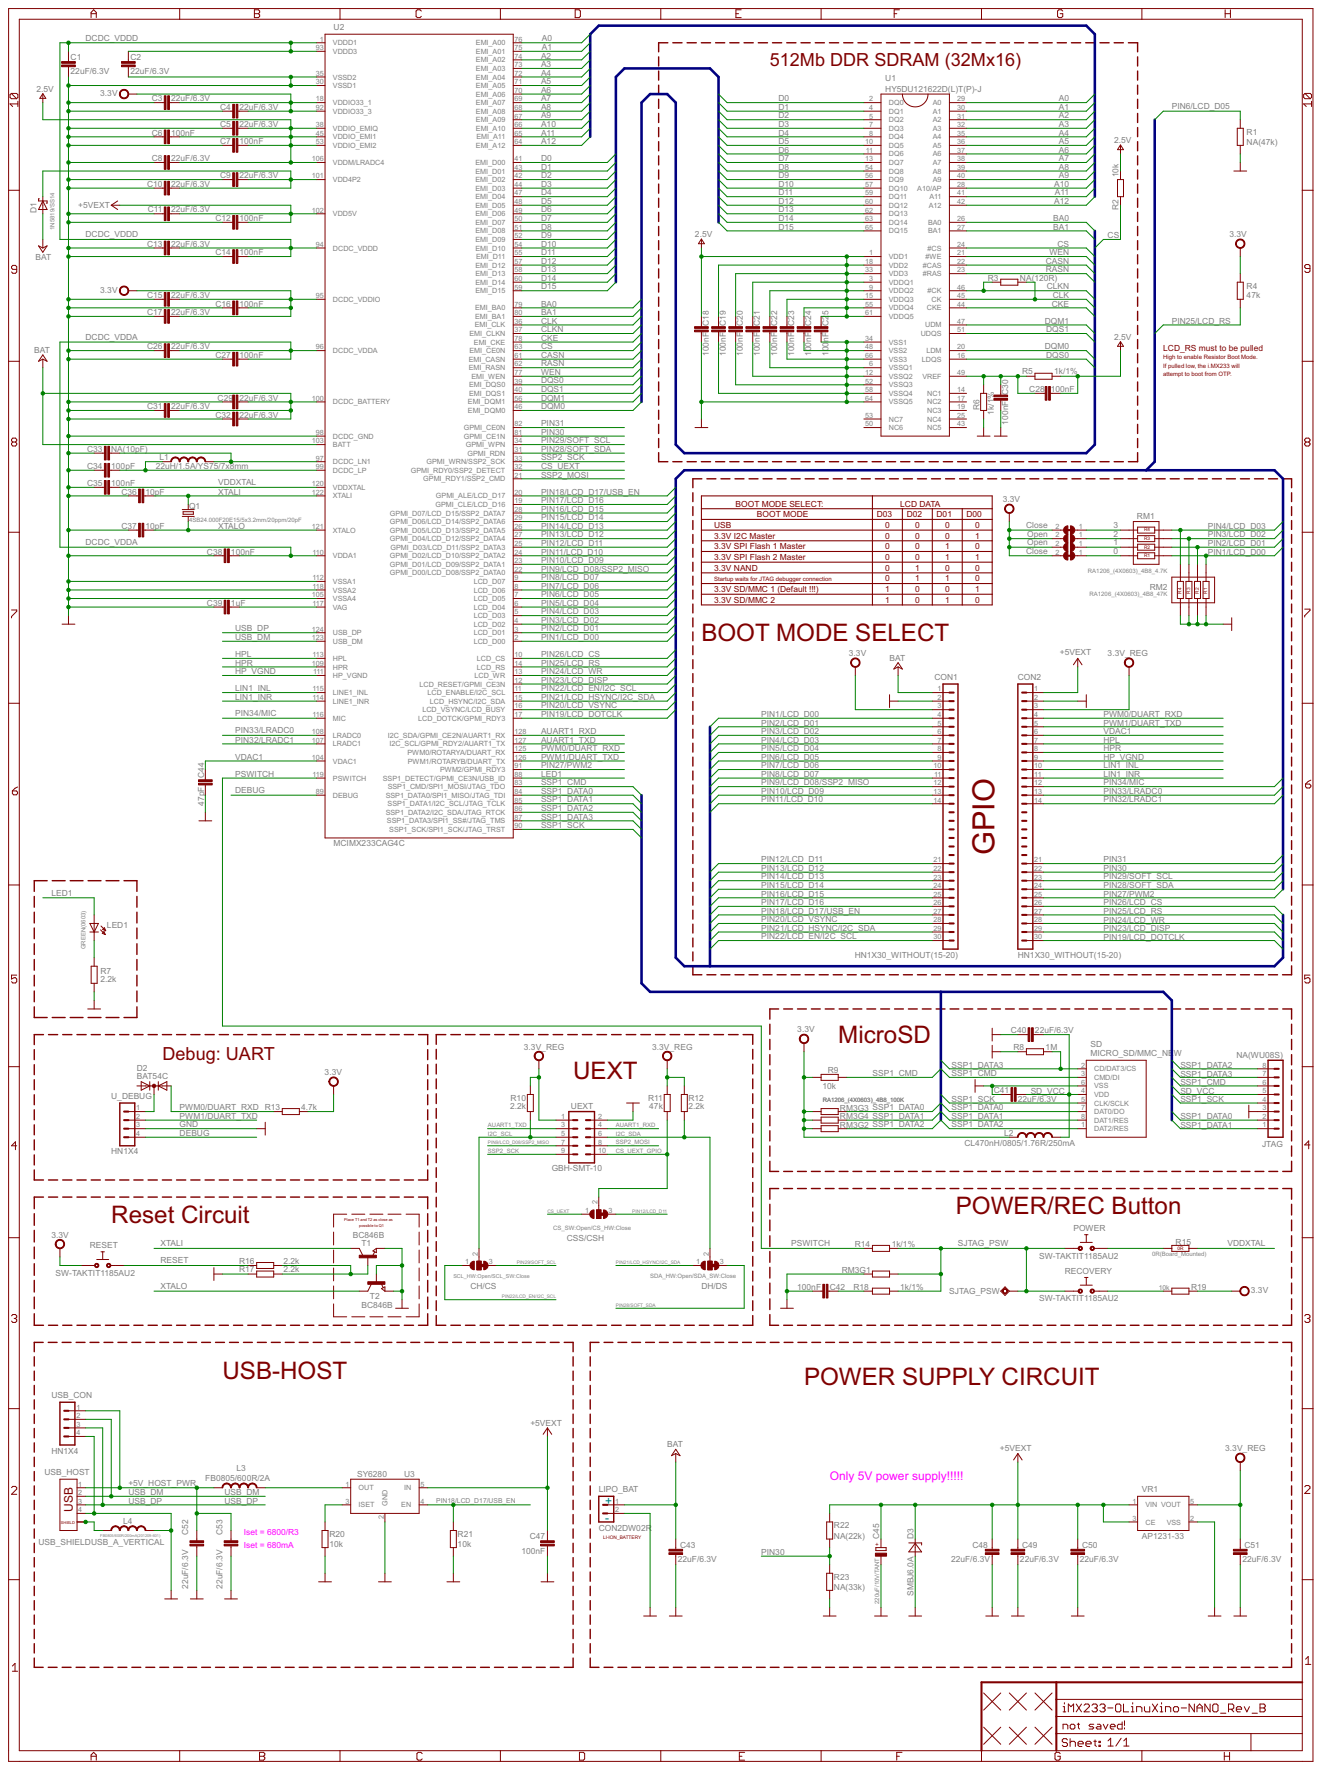
[picture p142: page 1]

LCD_RS must to be pulled

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

C31 | 22uF/6.3V | DQM0 46

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

Close Open Open Close

112 | PIN10/LCD_D09

Startup waits for JTAG debugger connection 3.3V SD/MMC 1 (Default !!!)

105 | | 7 PIN6/LCD_D05

C39 | 1uF | | 6 PIN5/LCD_D04

3.3V SD/MMC 2 | 1 | 0 | 1 | 0

USB_DP 124 | | 5 PIN4/LCD_D03
