OLIMEX/OLINUXINO/HARDWARE/iMX233-OLinuXino-Maxi/iMX233-OLINUXINO-MAXI_Rev_B1.sch.pdf

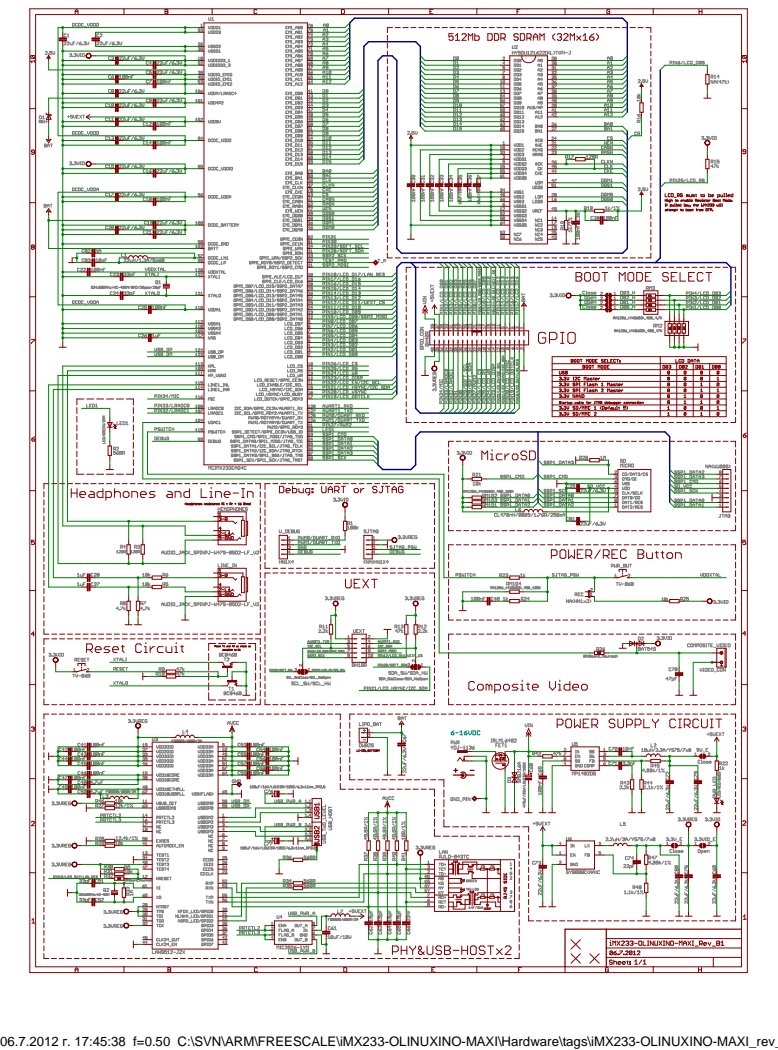
[picture p143: page 1]

06.7.2012 г. 17:45:38 f=0.50 C:\SVN\ARM\FREESCALE\iMX233-OLINUXINO-MAXI\Hardware\tags\iMX233-OLINUXINO-MAXI_rev_
