OLIMEX/OLINUXINO/HARDWARE/iMX233-OLinuXino-Micro/iMX233-OLinuXino-Micro_Rev_B.sch.pdf

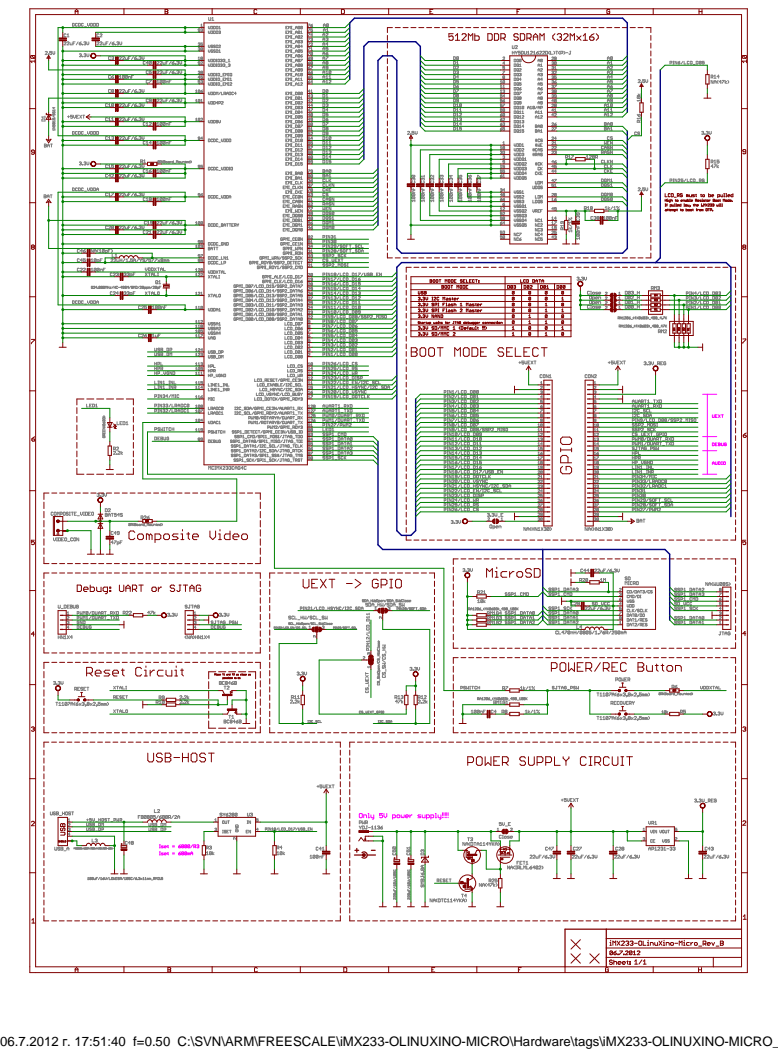
[picture p144: page 1]

06.7.2012 г. 17:51:40 f=0.50 C:\SVN\ARM\FREESCALE\iMX233-OLINUXINO-MICRO\Hardware\tags\iMX233-OLINUXINO-MICRO_Re
