OLIMEX/OLINUXINO/HARDWARE/A20-OLinuXino-MICRO/1. Latest hardware revision/A20-OLINUXINO-MICRO_Rev_N_BOM.pdf

A20-OLINUXINO-MICRO_Rev_N_BOM | 05/10/2022

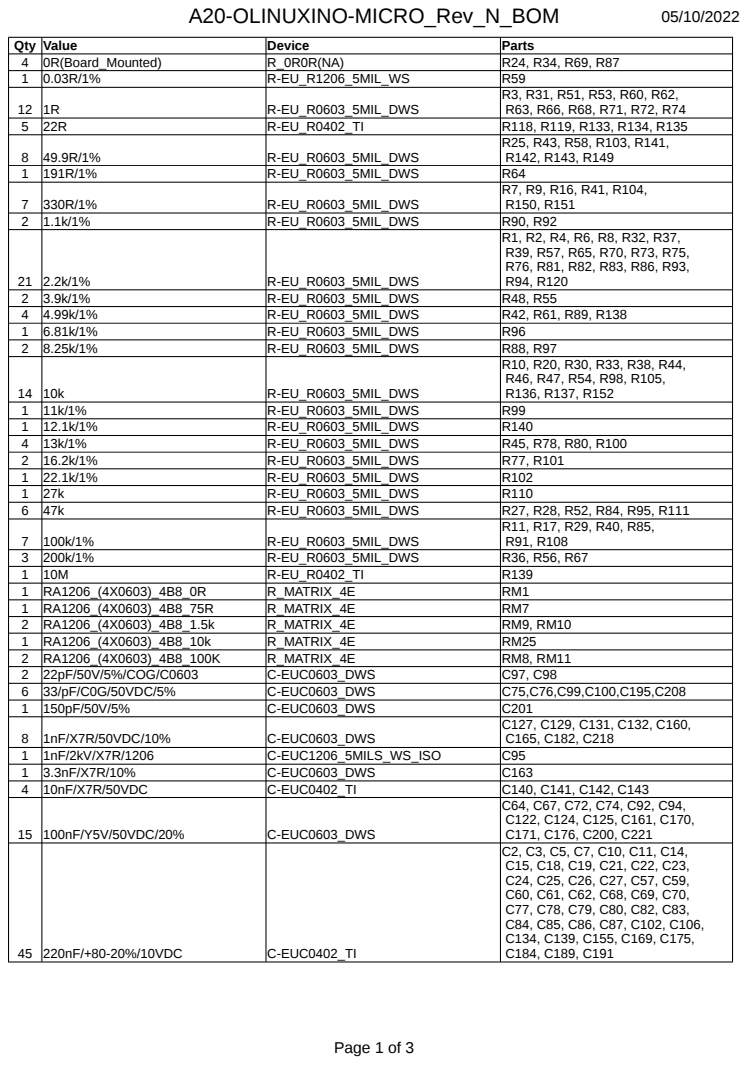
[picture p145: page 1]

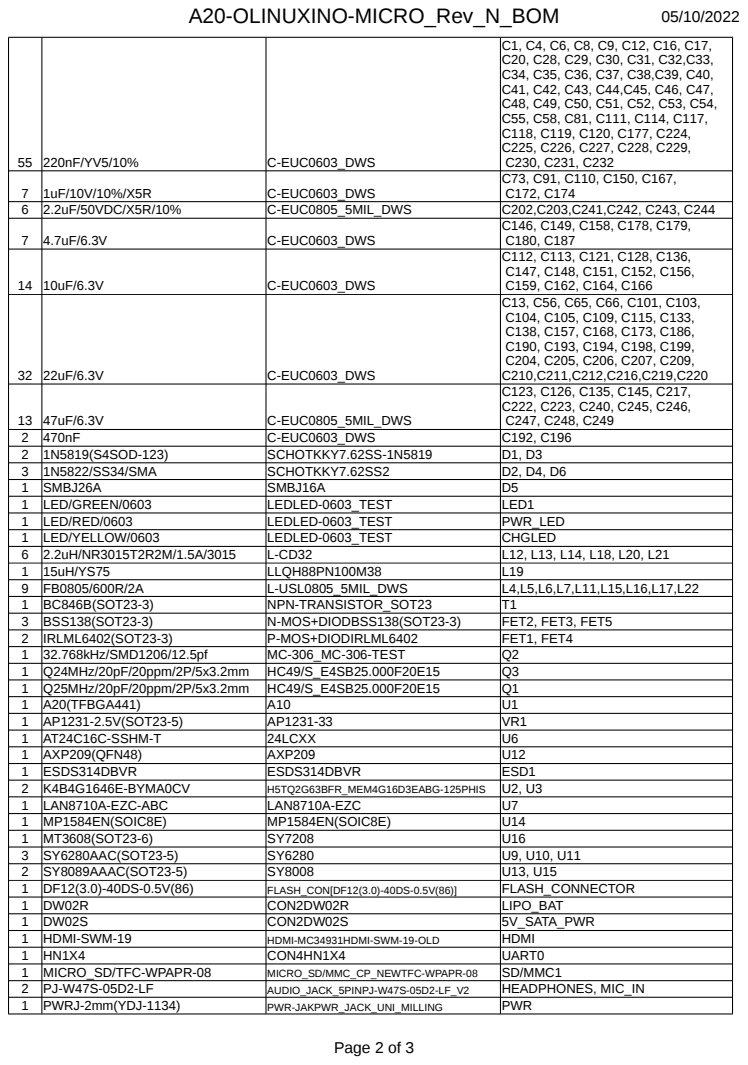
[picture p146: page 2]

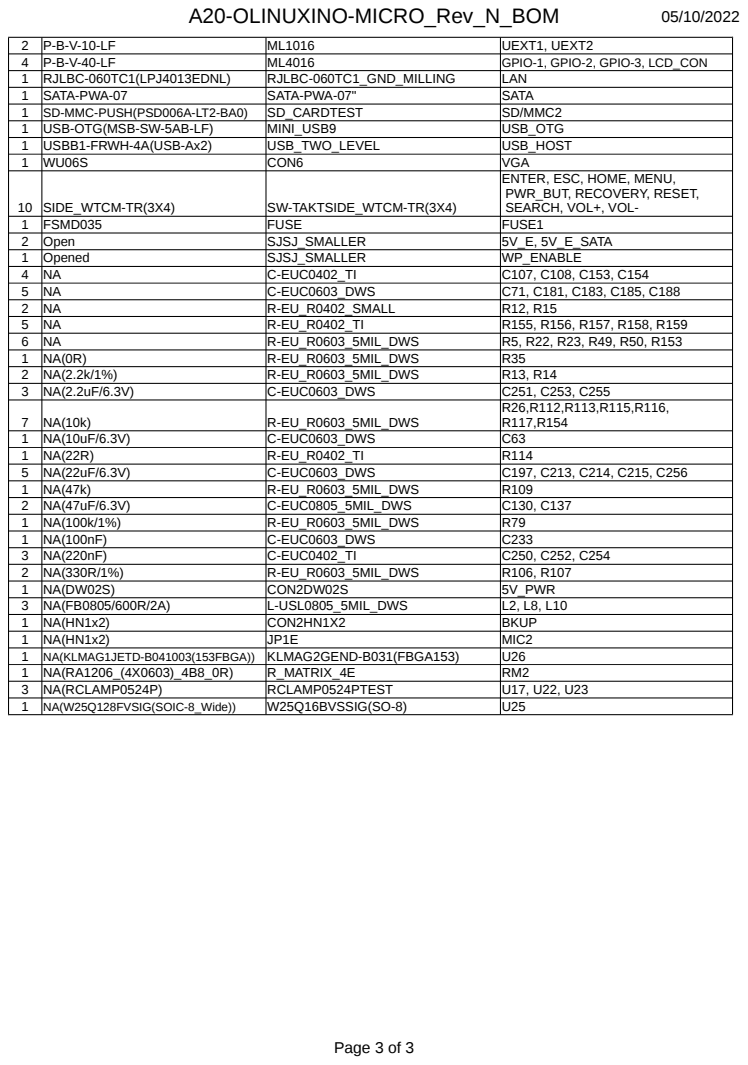
[picture p147: page 3]

ENTER, ESC, HOME, MENU,
PWR_BUT, RECOVERY, RESET,
SEARCH, VOL+, VOL-
