OLIMEX/OLINUXINO/HARDWARE/A20-OLinuXino-LIME2/1. Latest hardware revision/A20-OLinuXino-Lime2_Rev_L_BW.pdf

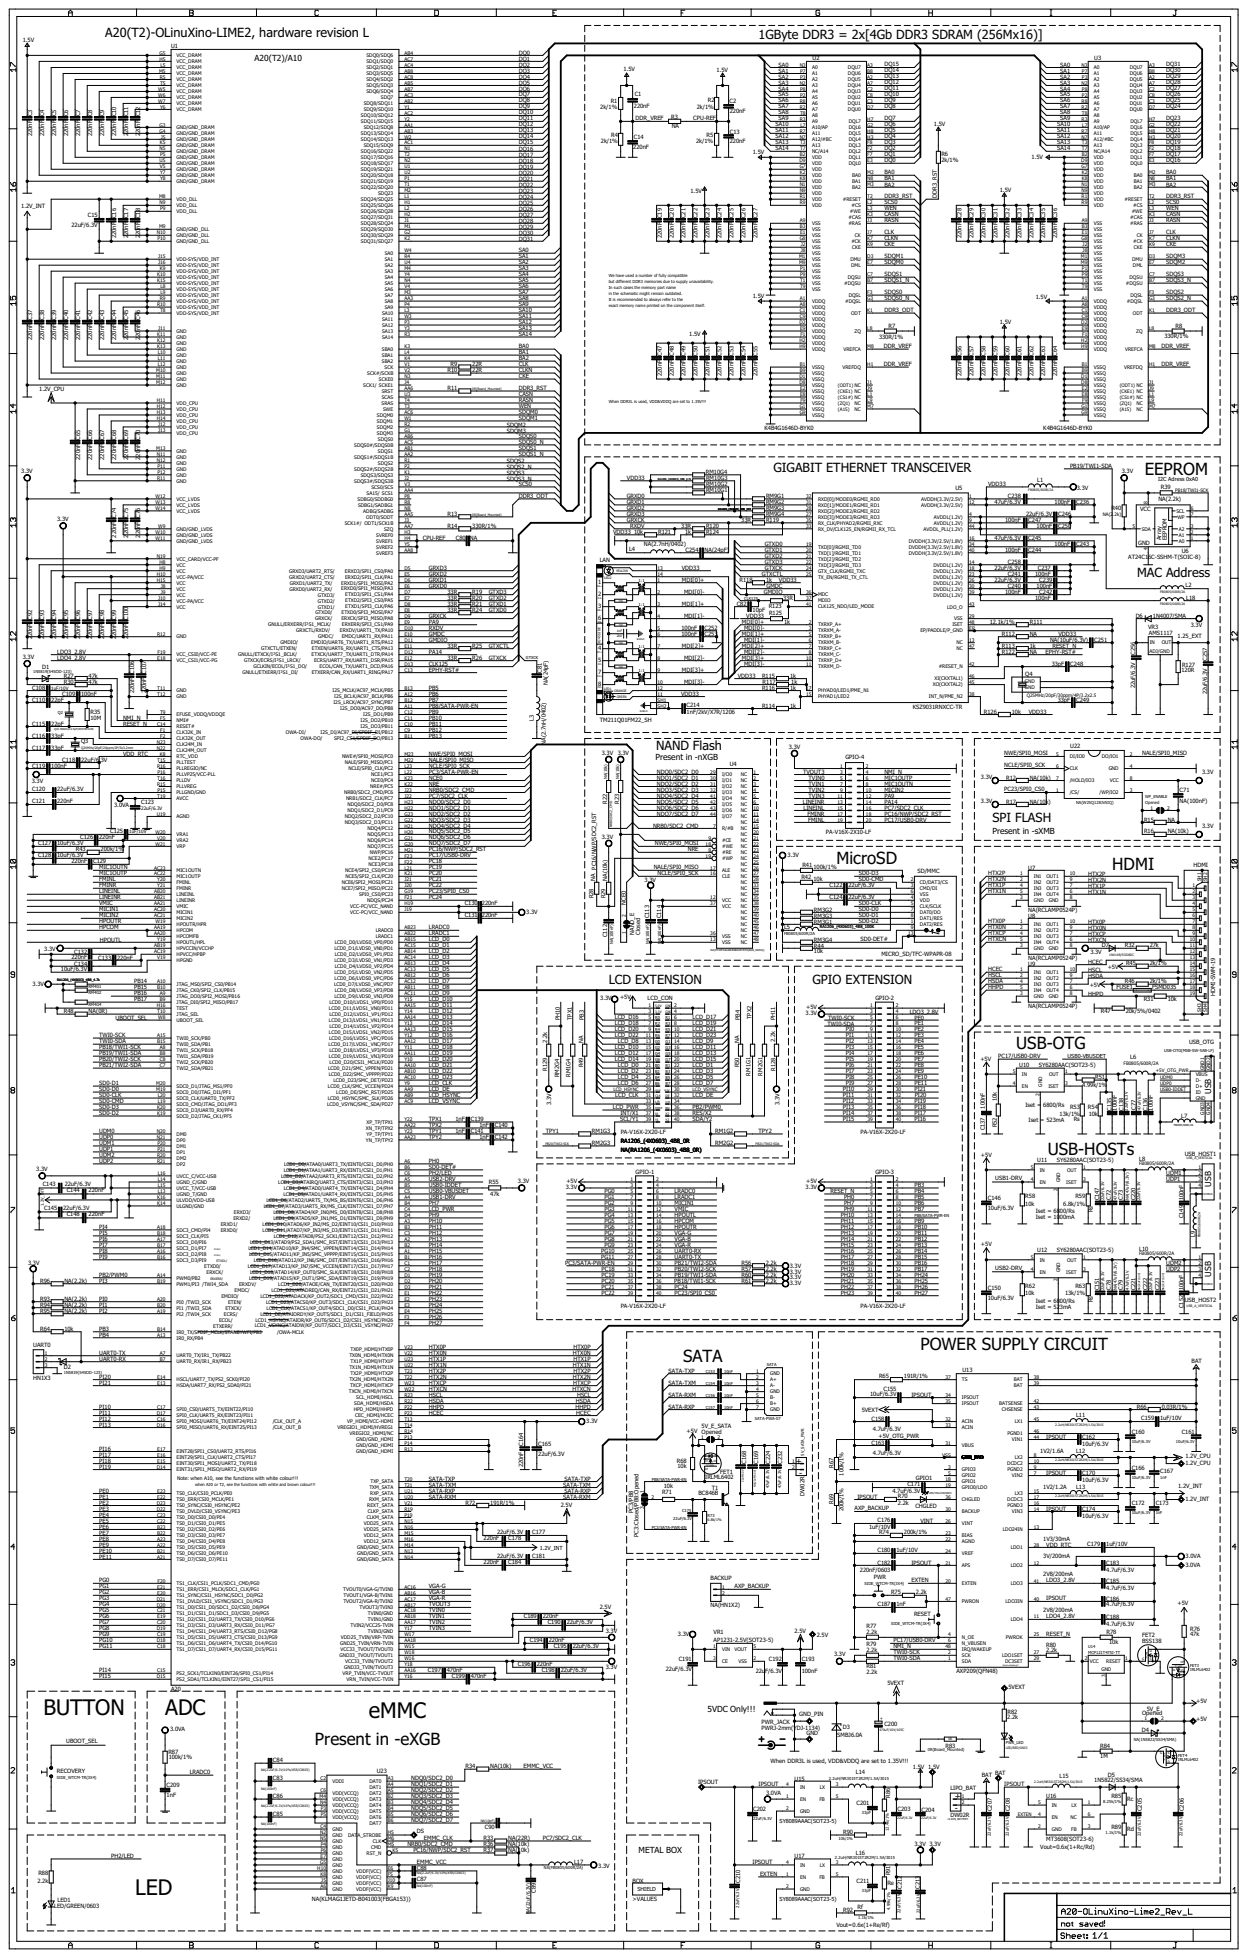
[picture p148: page 1]
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

in the schematic might remain outdated. It is recommended to always refer to the

exact memory name printed on the component itself.

When DDR3L is used, VDD&VDDQ are set to 1.35V!!!

GRXD3/UART2_RTS/ GRXD2/UART2_CTS/ GRXD1/UART2_TX/ GRXD0/UART2_RX/ GTXD3/ GTXD2/ GTXD1/ GTXD0/ GRXCK/ GNULL/ERXERR/I²S1_MCLK/ GRXCTL/RXDV/ GMDC/ GMDIO/ GTXCTL/ETXEN/ GNULL/ETXCK/I²S1_BCLK/ GTXCK/ECRS/I²S1_LRCK/ GCLKIN/ECOL/I²S1_DO/ GNULL/ETXERR/I²S1_DI/

OWA-DI/ OWA-DO/

USB-OTG(MSB-SW-5AB-LF) 4.99k/1%

Note: when A10, see the functions with white colour!!! when A20 or T2, see the functions with white and brown colour!!!
