OLIMEX/OLINUXINO/HARDWARE/A33-OLinuXino/1. Latest hardware revision/A33-OLinuXino_Rev_C.pdf

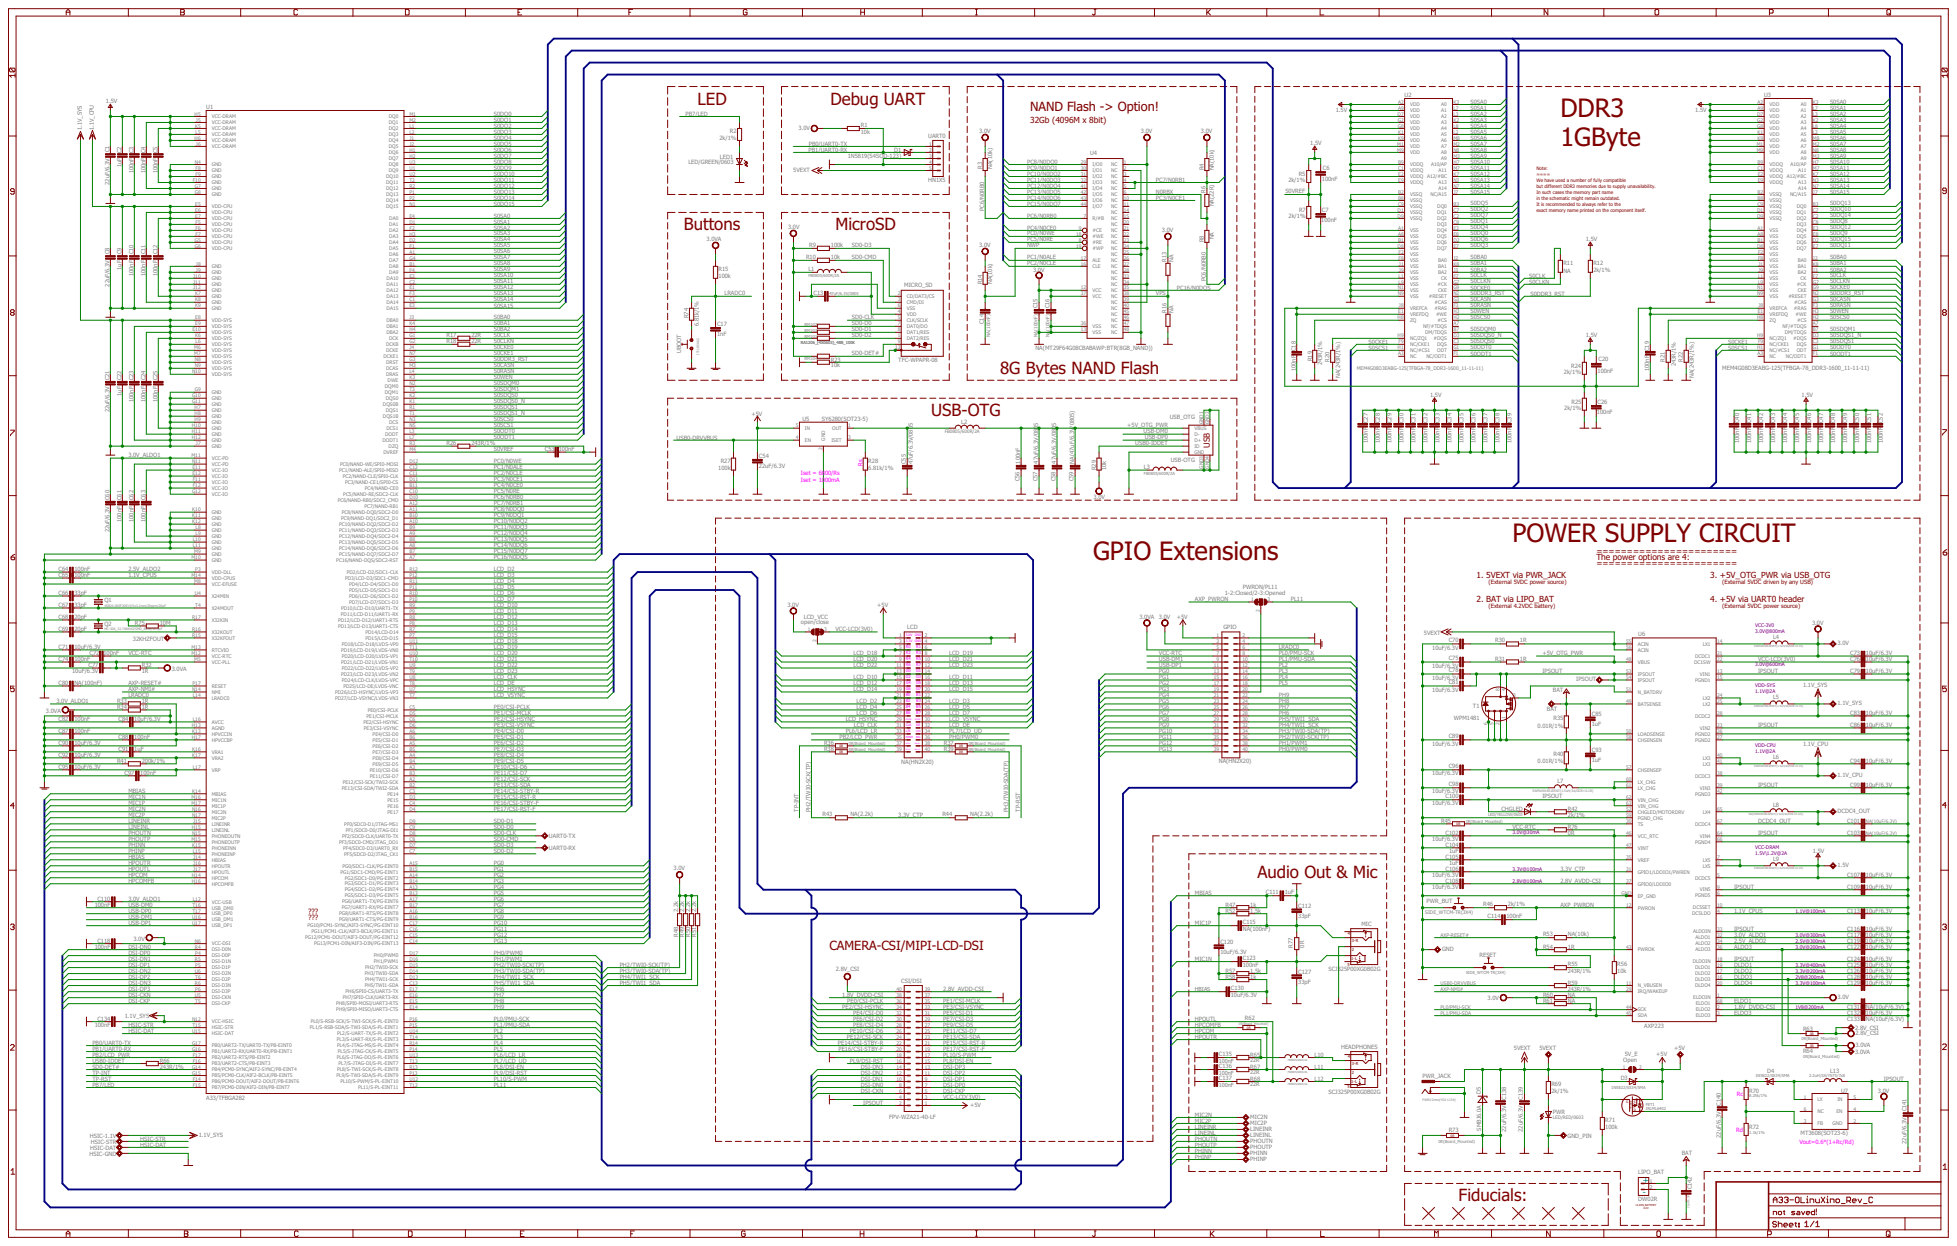
[picture p149: page 1]

NAND Flash -> Option! 32Gb (4096M x 8bit) LED

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

in the schematic might remain outdated. It is recommended to always refer to the

exact memory name printed on the component itself.

K9 L6 G11 H9 J7 N11 F11 G12 | VDD-SYS M6 VDD-SYS M7 VDD-SYS N8 VDD-SYS N9 VDD-SYS N10 VCC-PD M11

(External 5VDC driven by any USB) =======================

The power options are 4: 1. 5VEXT via PWR_JACK

PL0/PMU-SCK
PL1/PMU-SDA

HSIC-1.1V HSIC-STR HSIC-DAT HSIC-GND
