OLIMEX/OLINUXINO/HARDWARE/A10-OLinuXino-MICRO/A10-OLinuXino-MICRO hardware revision G/A20-OLINUXINO-MICRO_4GB_Rev_G1.pdf

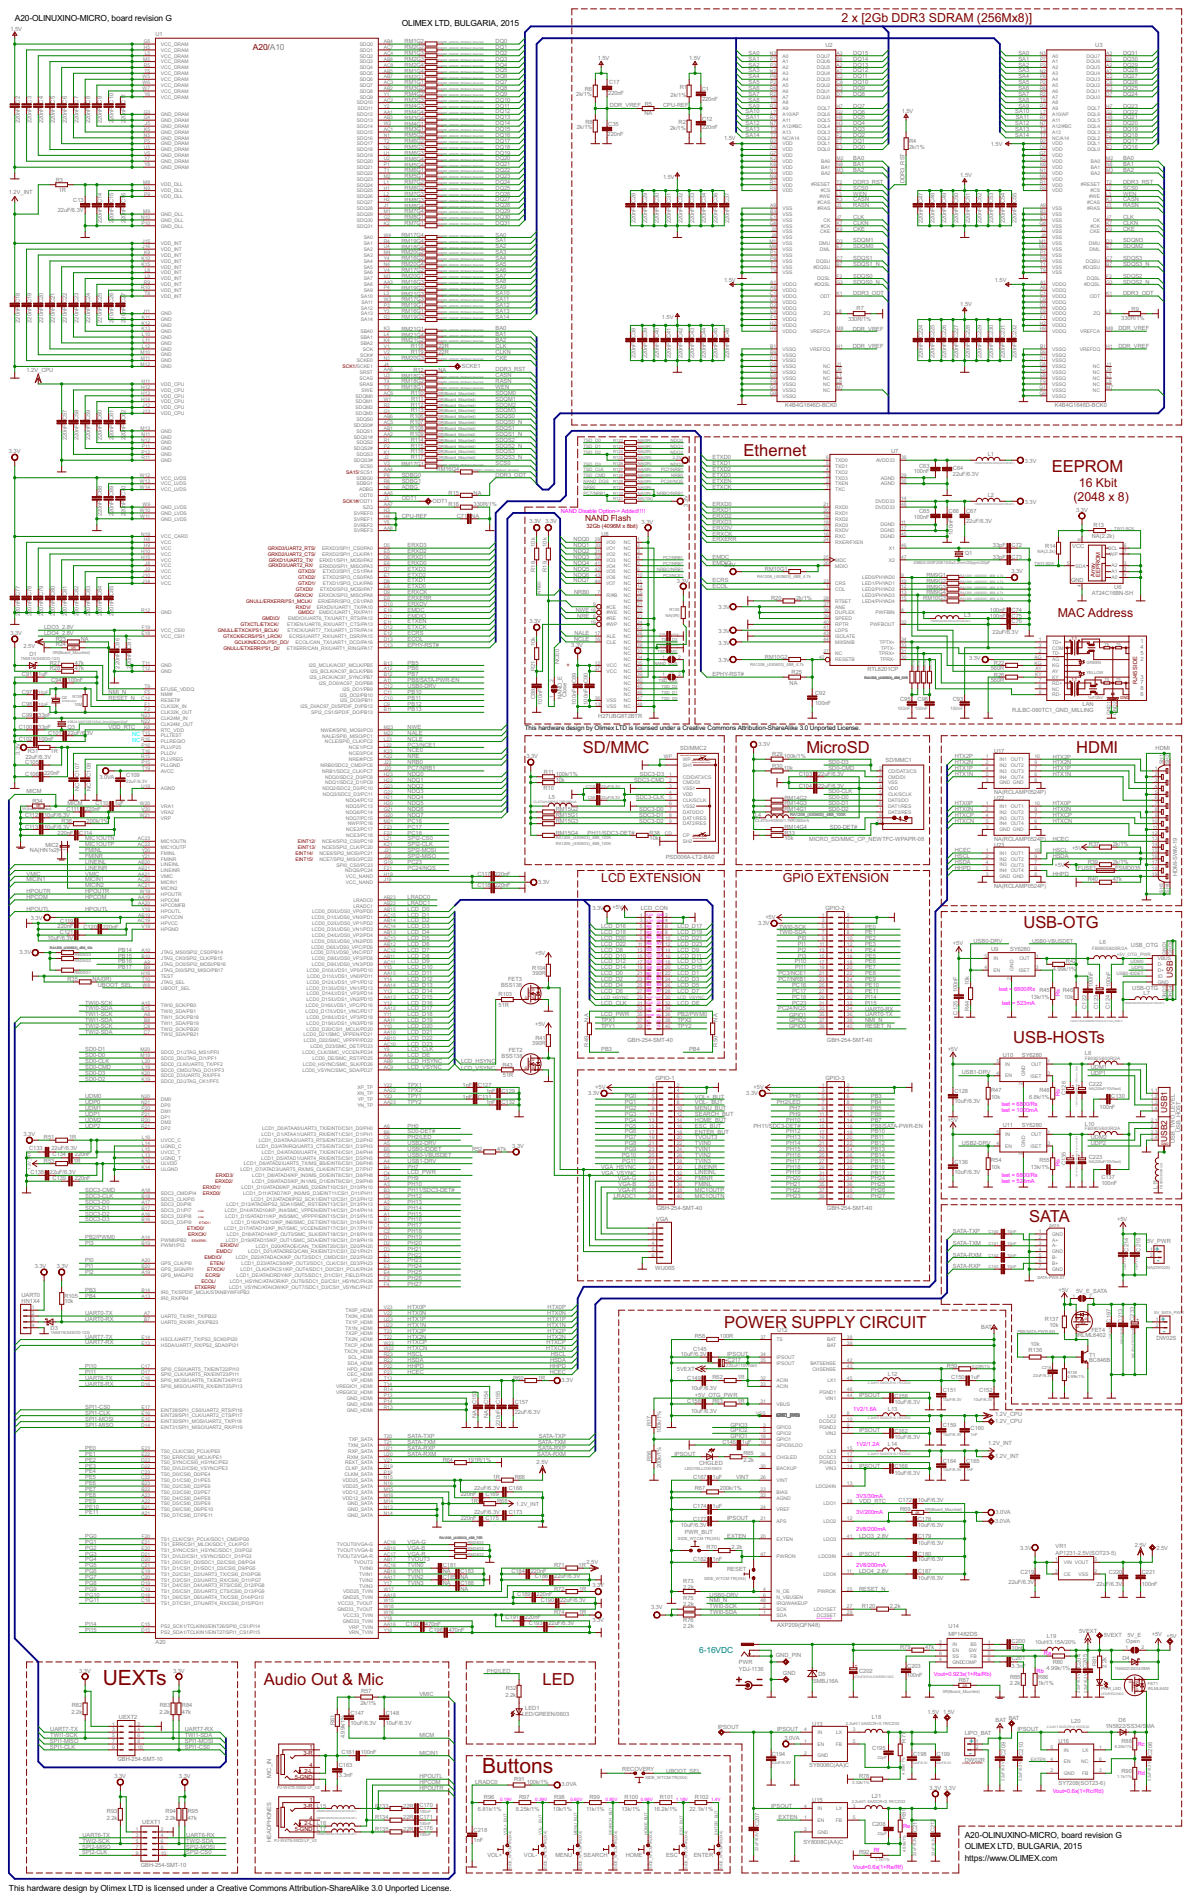
[picture p150: page 1]
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

When card is insertedwith WPstatus: Locked, WP switch i

When card is inserted, CPswitch is Closed
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
