OLIMEX/OLINUXINO/HARDWARE/LCDs/LCD-OLinuXino-7TS/Hardware revision F/LCD-OLINUXINO-7TS_Rev_F.pdf

5

A | B | C | D | E | F | G | H

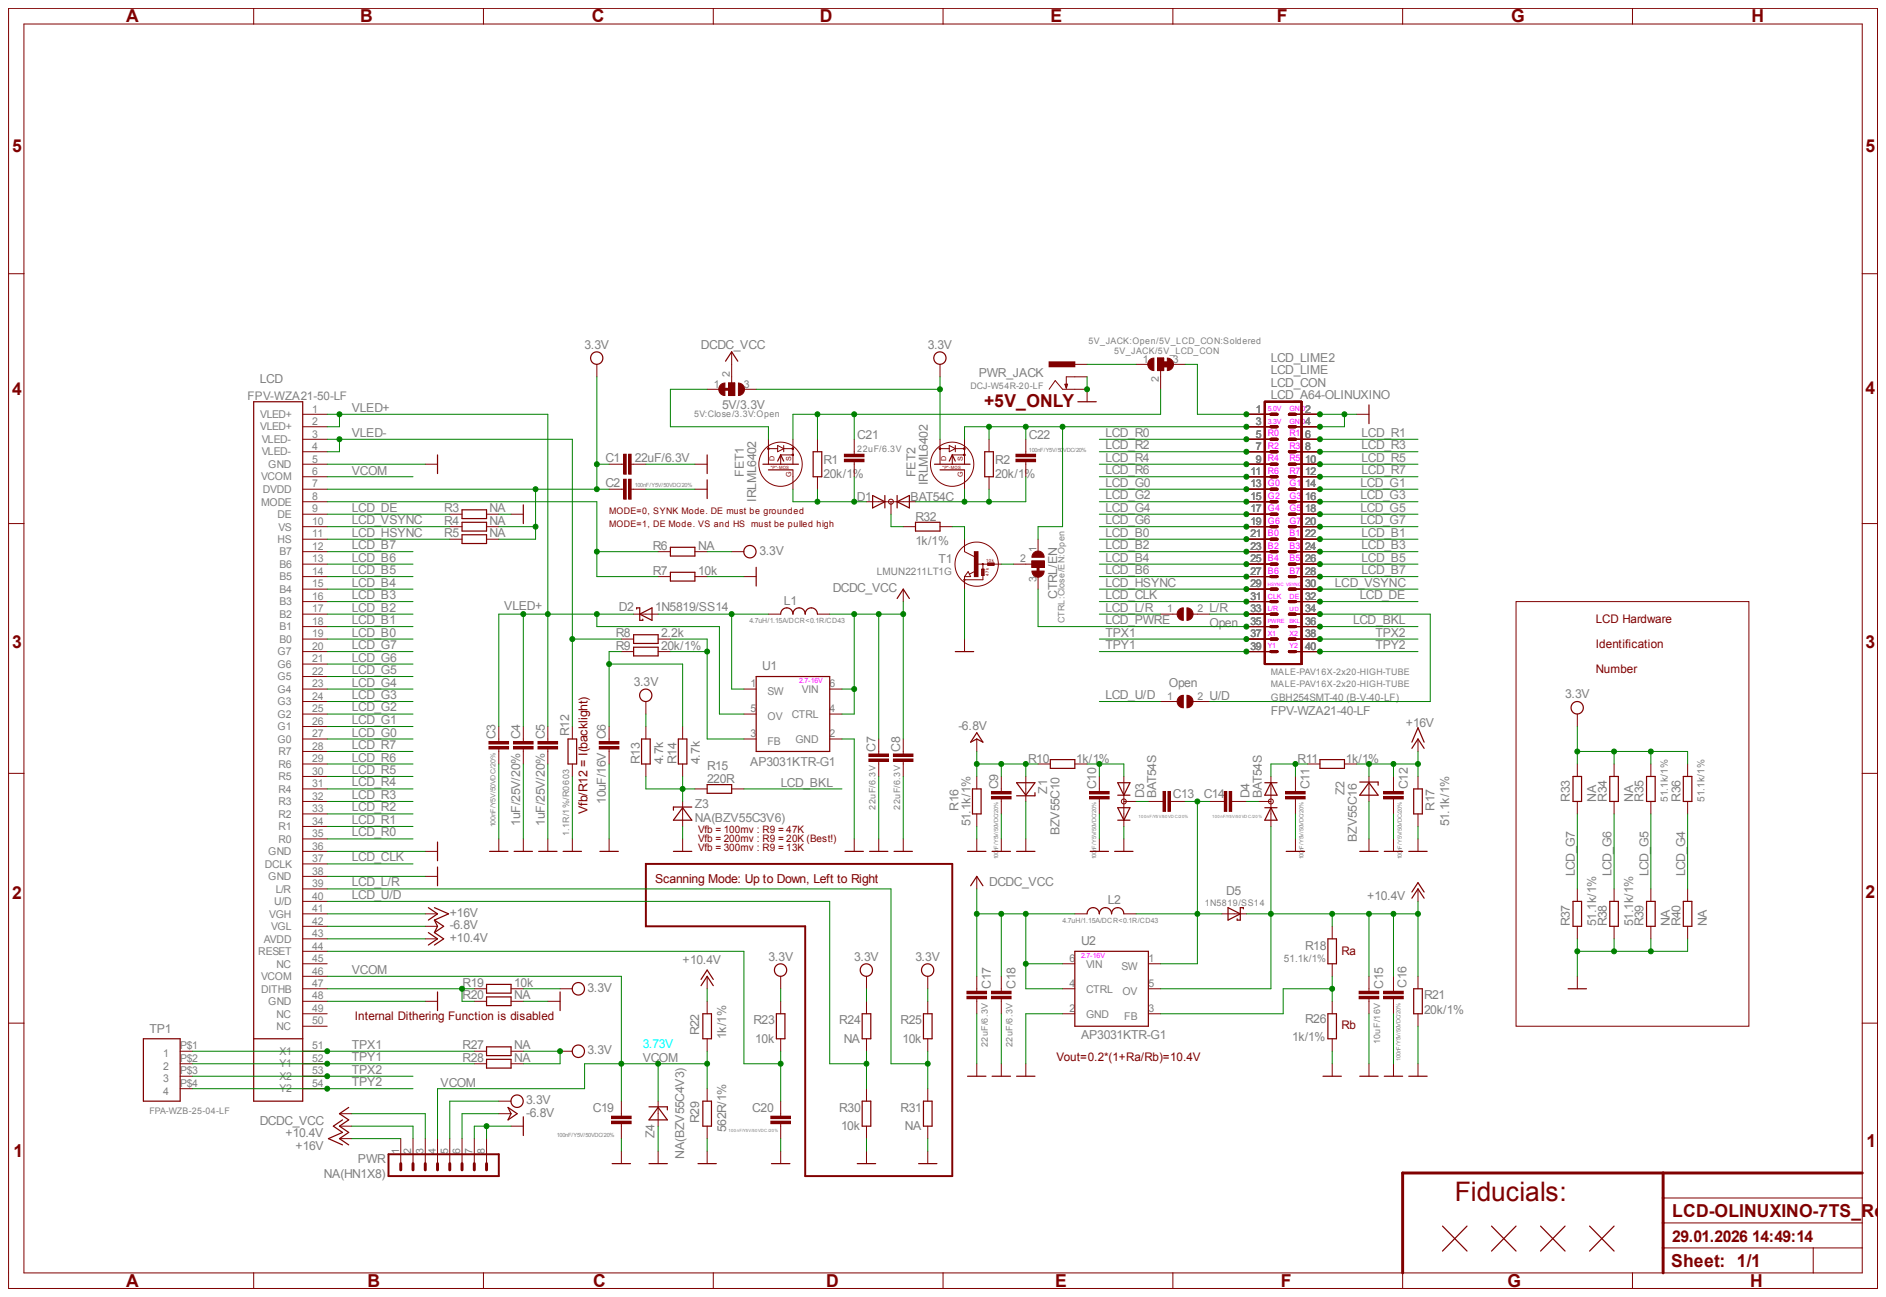
[picture p151: page 1]

MODE=0, SYNK Mode. DE must be grounded

MODE=1, DE Mode. VS and HS must be pulled high

CTRL:Close/EN:Open

Scanning Mode: Up to Down, Left to Right

Internal Dithering Function is disabled

P$2 | | TPY1 R28
P$3 | | TPX2 VCOM
P$4 | Y2 | TPY2 54

Fiducials:

Sheet: 1/1
