OLIMEX/OLINUXINO/HARDWARE/A13-OLinuXino-MICRO/1. Latest hardware revision/A13-OLinuXino-MICRO hardware revision C1/A13-OLinuXino-MICRO_Rev_C1.pdf

9

A | B | C | D | E | F | G | H

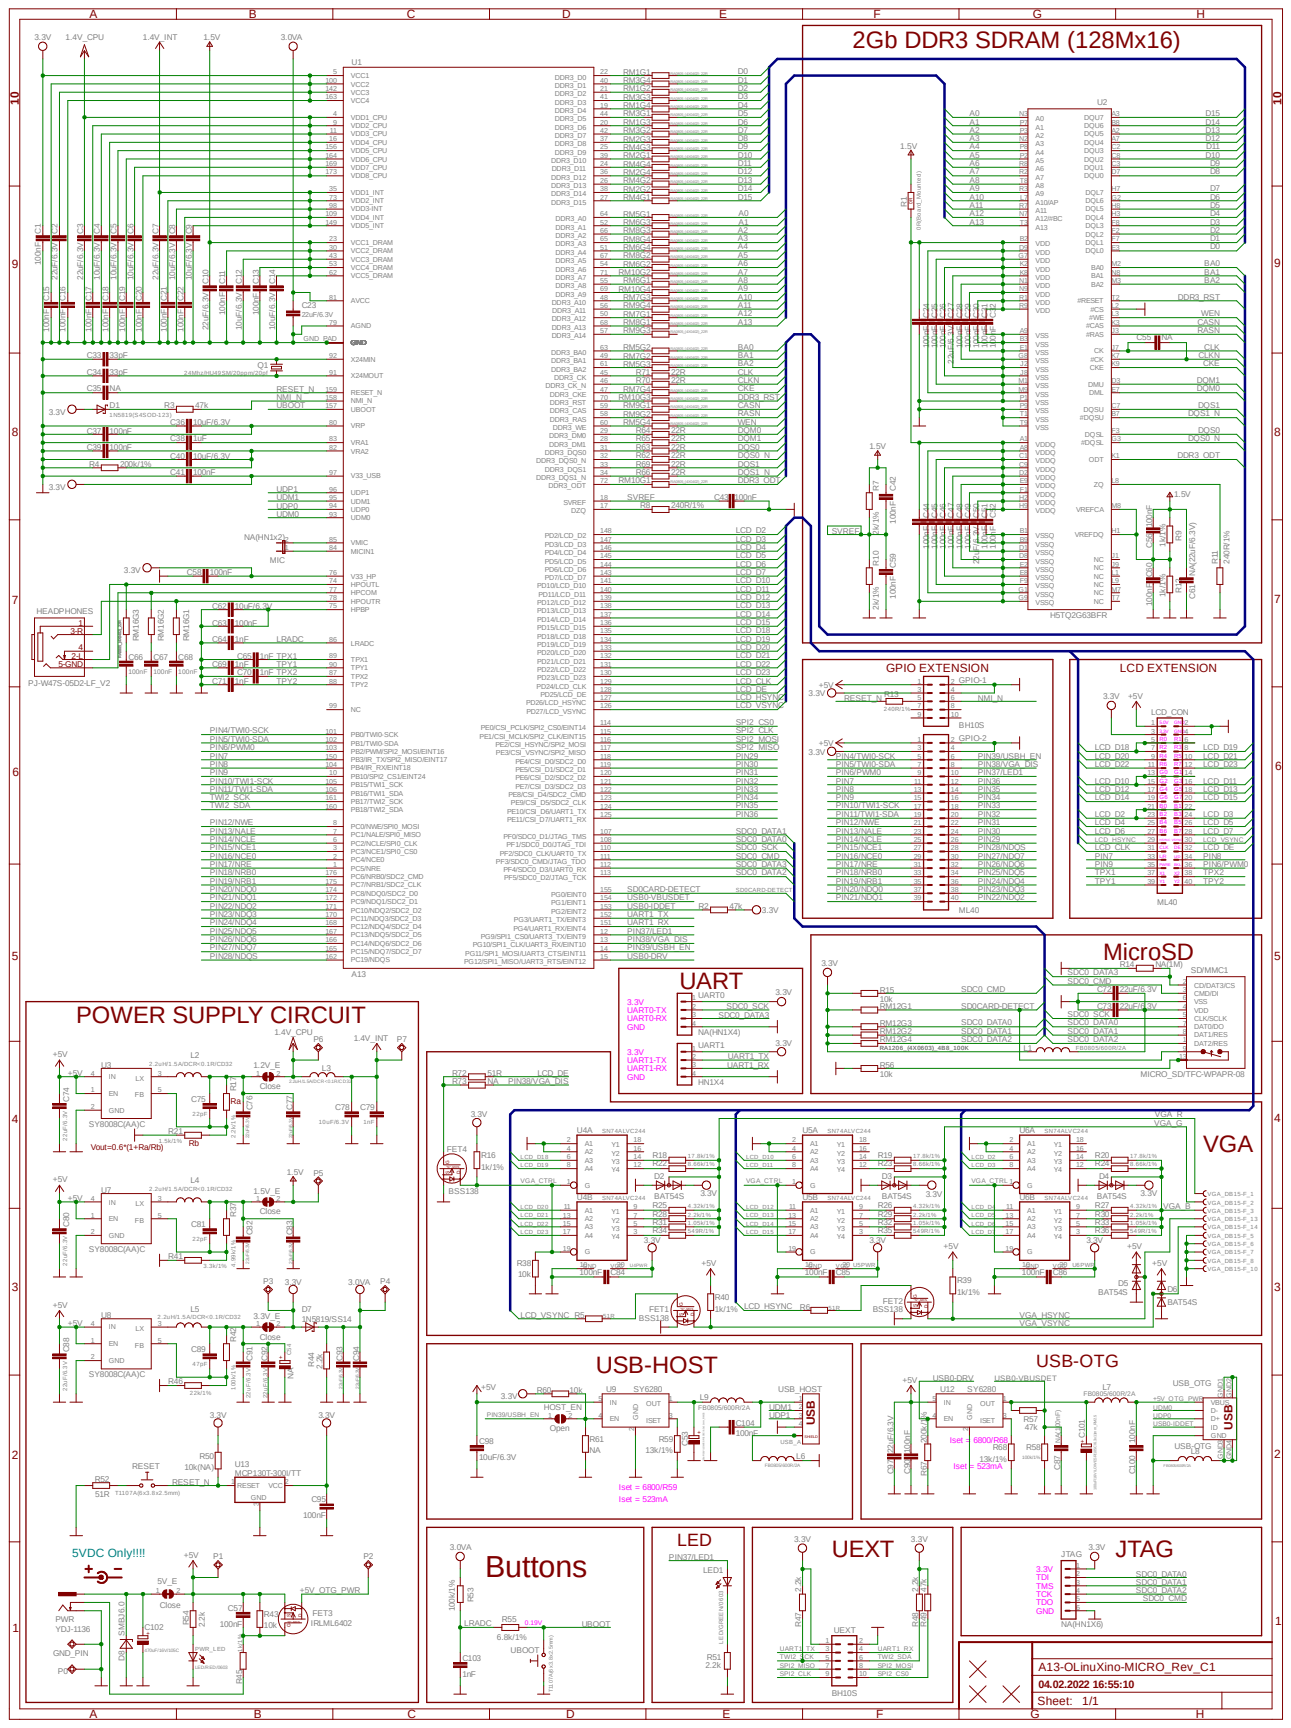
[picture p152: page 1]

3.3V 1.4V_CPU 1.4V_INT 1.5V 3.0VA

VCC2 100 | 40 RM3G4 RA0805_(4X0402)_22R D1
VCC3 142 | 21 RM1G2 RA0805_(4X0402)_22R D2
VCC4 163 | 41 RM3G3 D3 RA0805_(4X0402)_22R
VDD1_CPU 4 | 19 RM1G4 D4 RA0805_(4X0402)_22R

HPOUTR 78 | LCD_D12

C62 | 10uF/6.3V | HPBP 75 | LCD_D13
C63 | 100nF | LRADC | LRADC 86 | 137 LCD_D14

LCD_VSYNC 126 7 | | 8

PB0/TWI0-SCK 101 | 9 114 SPI2_CS0 | | 10

SDC0_CMD | CD/DAT3/CS 2 CMD/DI 3 VSS 6 VDD 4 CLK/SCLK 5 DAT0/DO 7 DAT1/RES 8 DAT2/RES 1 9

Rb Vout=0.6*(1+Ra/Rb)
