OLIMEX/OLINUXINO/HARDWARE/STMP157-OLinuXino-LIME2/1. Latest hardware revision/STMP157-OLinuXino-LIME2_Rev_B1/STMP157-OLinuXino-LIME2_Rev_B1.pdf

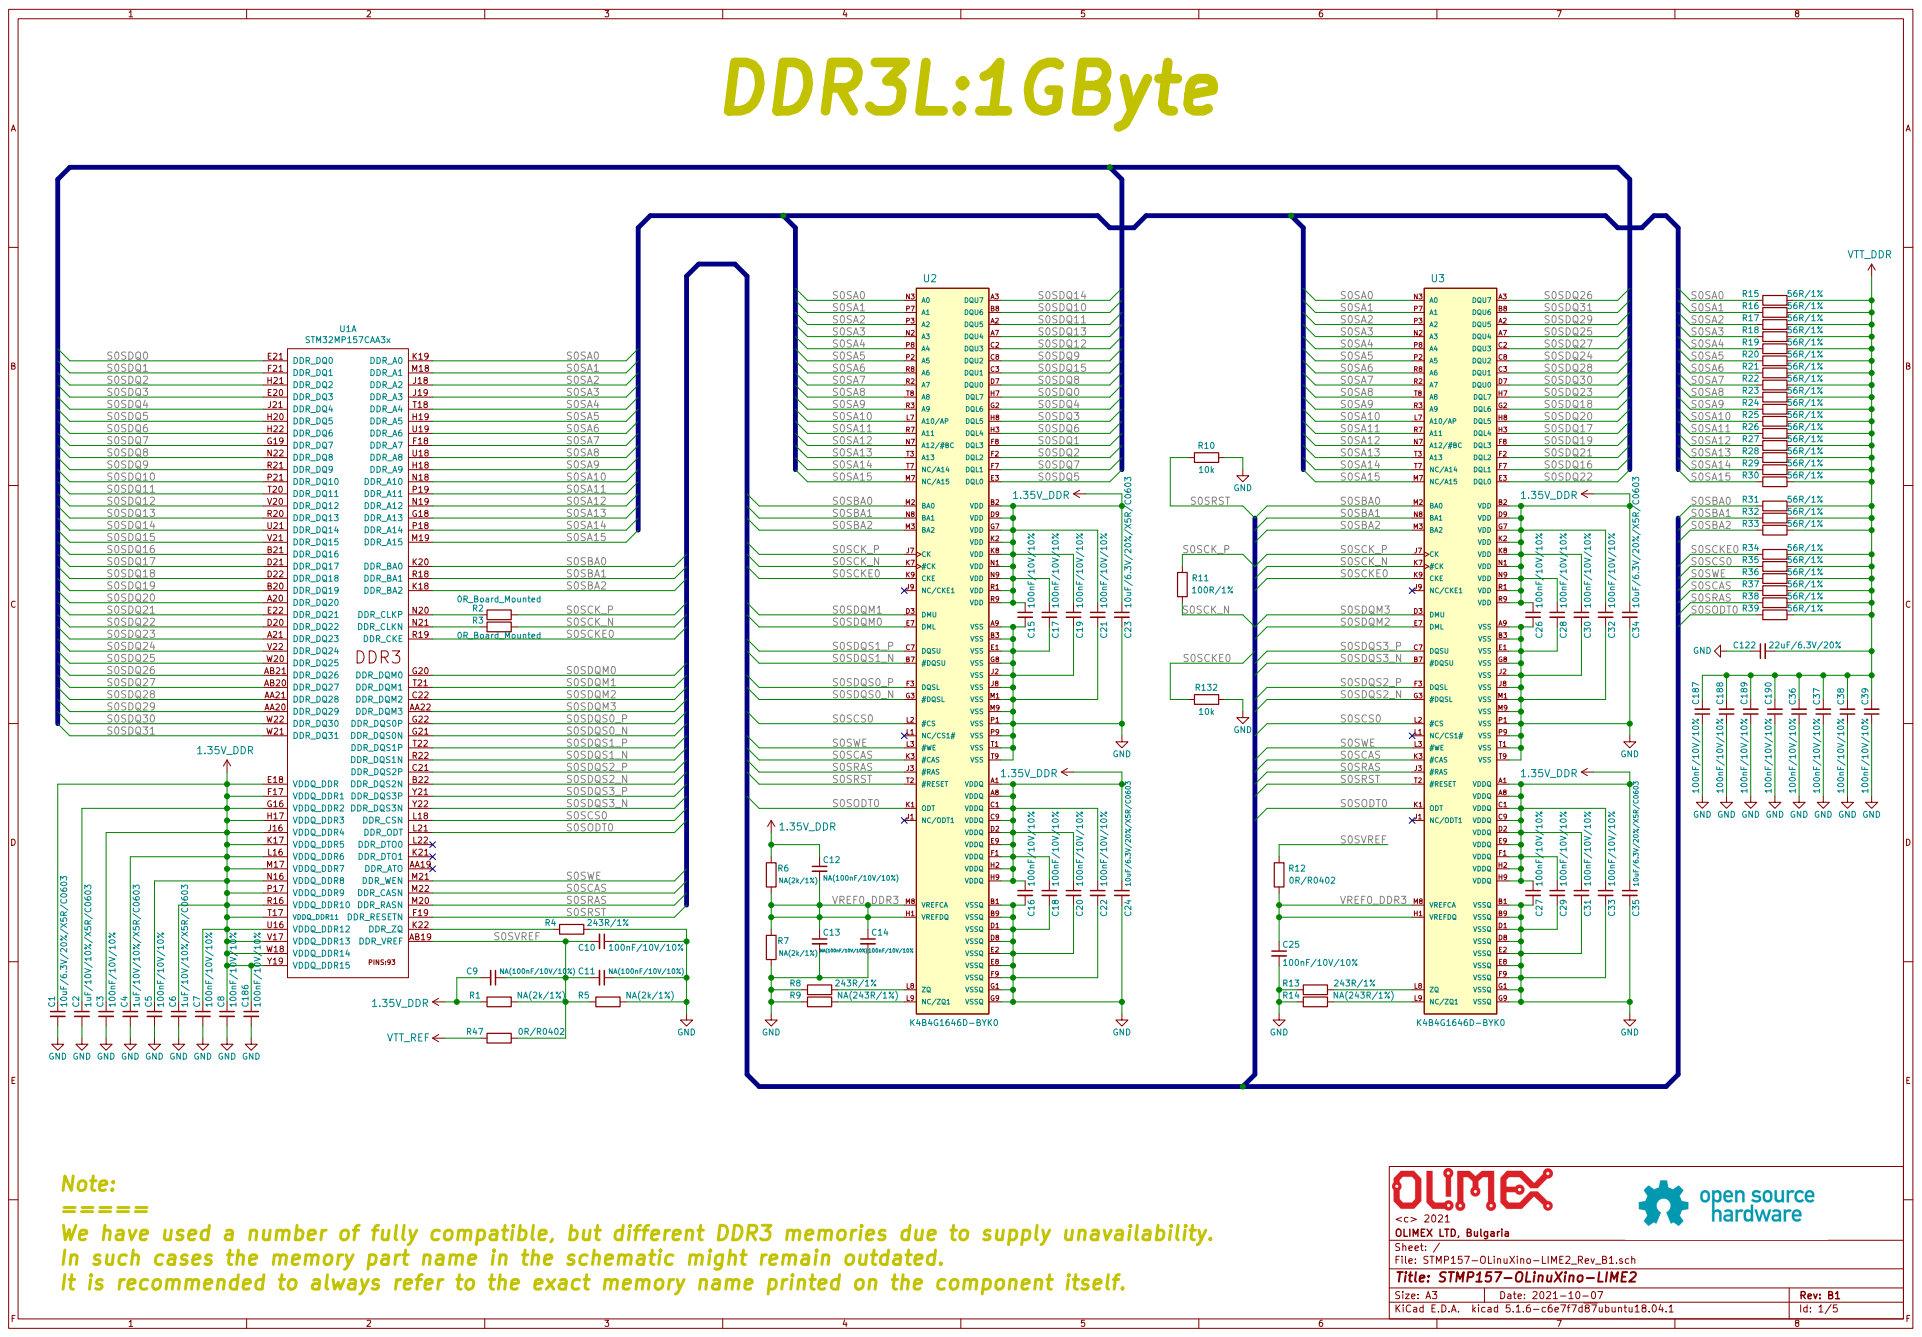
[picture p153: page 1]

GND GND GND GND GND

Note: ===== We have used a number of fully compatible, but different DDR3 memories due to supply unavailability.

In such cases the memory part name in the schematic might remain outdated.
It is recommended to always refer to the exact memory name printed on the component itself.

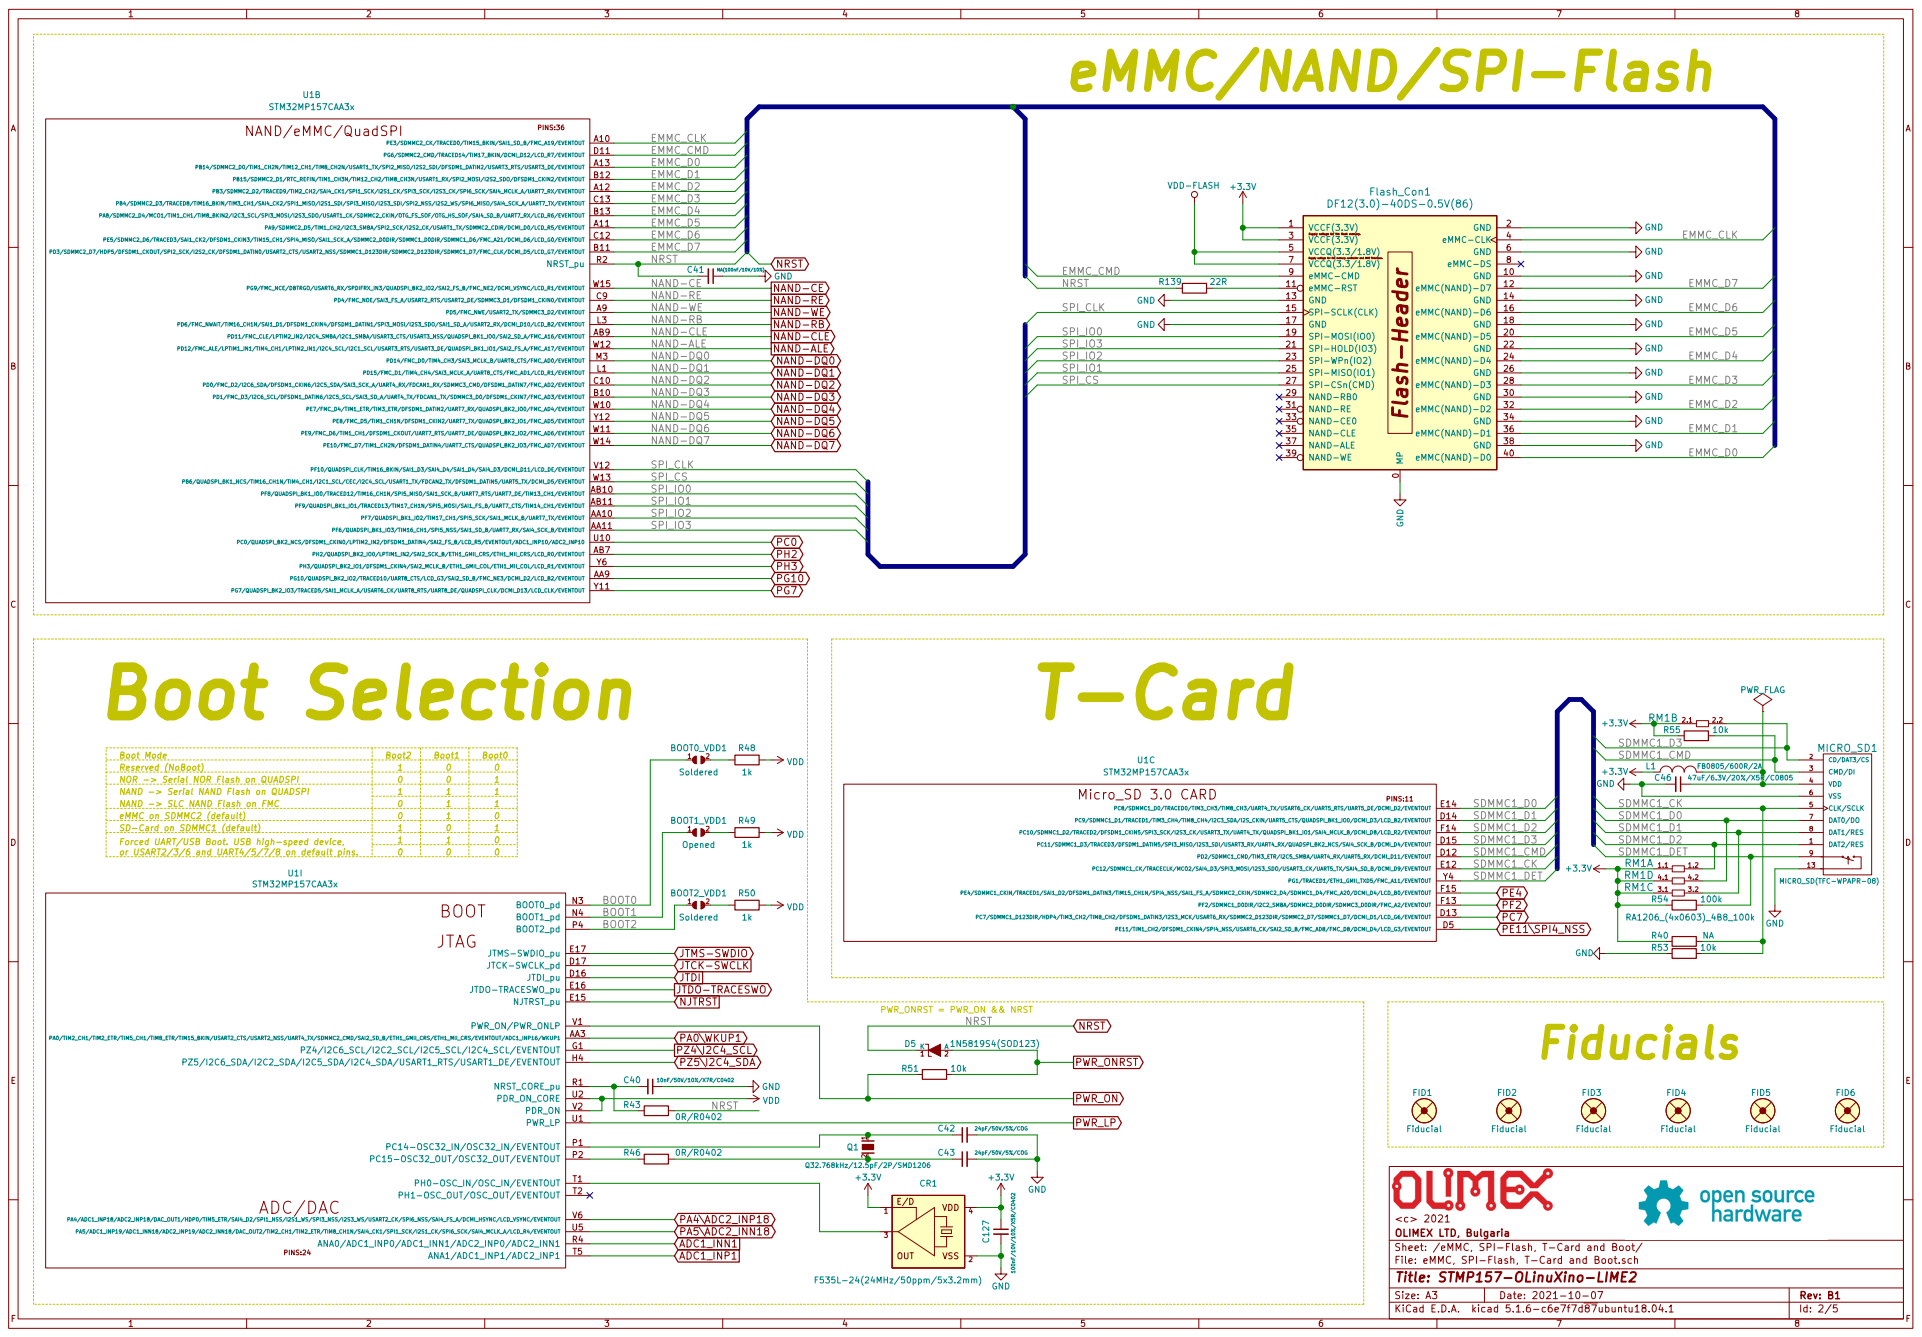
[picture p154: page 2]

EMMC_CLK
EMMC_CMD
EMMC_D0 NAND-RE
EMMC_D3 EMMC_D1 SPI_IO1 NAND-DQ6 NAND-DQ7 NAND-DQ5 NAND-DQ4 NAND-DQ3 NAND-CE
EMMC_D2 NAND-CLE NAND-ALE
NRST PH3 ADC1_INP1
NAND-DQ3 NAND-DQ2 NAND-DQ1 NAND-DQ0 NAND-DQ4 NAND-ALE NAND-CLE NAND-RB NAND-WE NAND-RE NAND-CE

File: eMMC, SPI-Flash, T-Card and Boot.sch Sheet: /eMMC, SPI-Flash, T-Card and Boot/ OLIMEX LTD, Bulgaria <c> 2021 R50

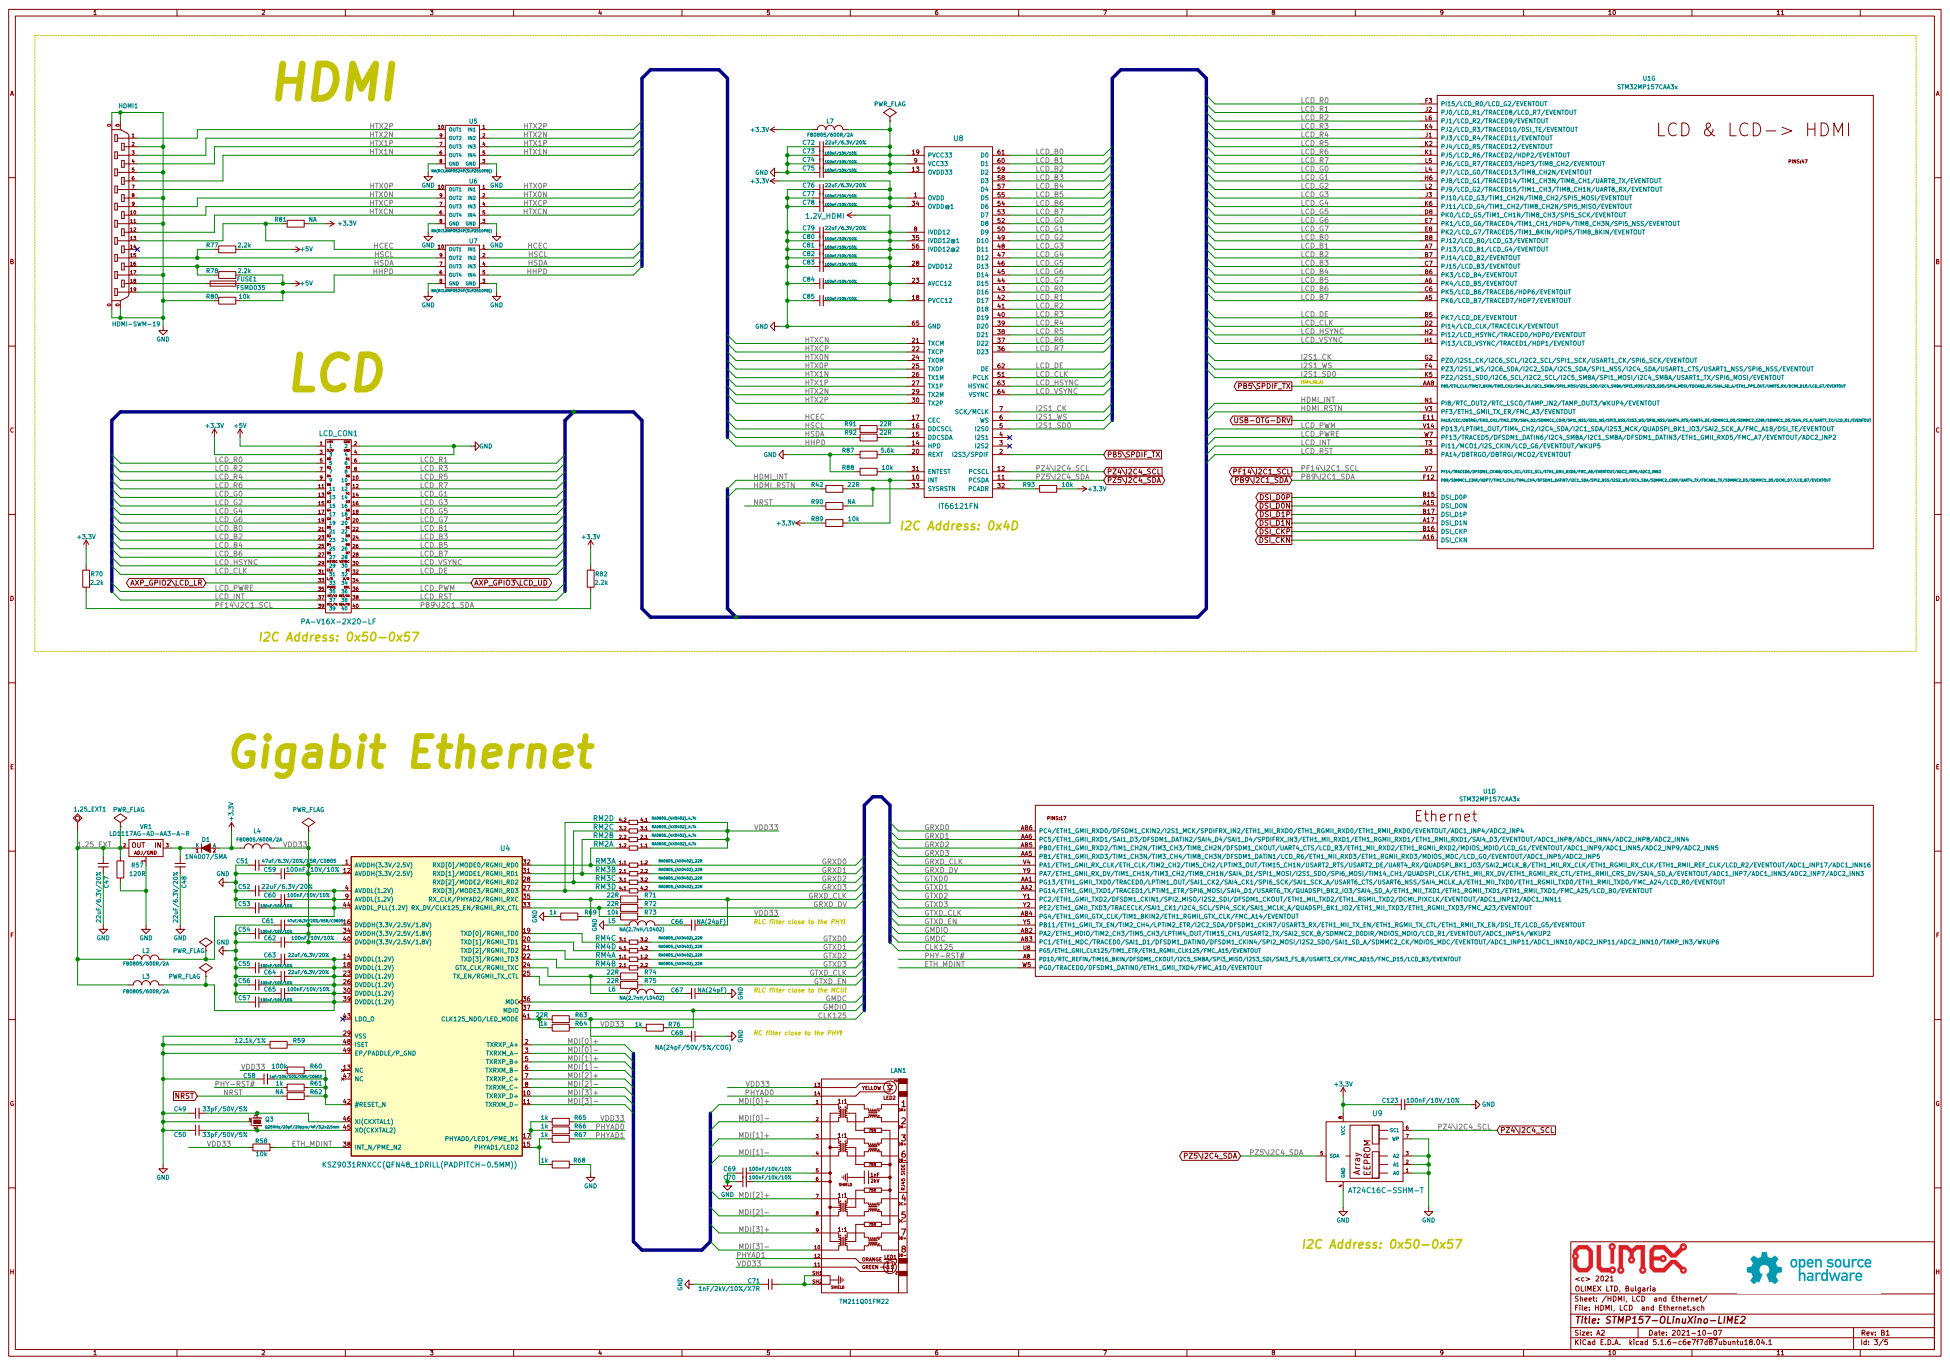
[picture p155: page 3]

RC filter close to the PHY! HDMI

NA(RCLAMP0524P(SLP2510P8))
HTXCP HSDA HSCL HTXCN

DA+ DA- DB+ DB- DC+ DC- DD+ DD- GREEN

4 SDA 5 SCL 6 WP 7 VCC

File: HDMI, LCD and Ethernet.sch Sheet: /HDMI, LCD and Ethernet/ OLIMEX LTD, Bulgaria <c> 2021

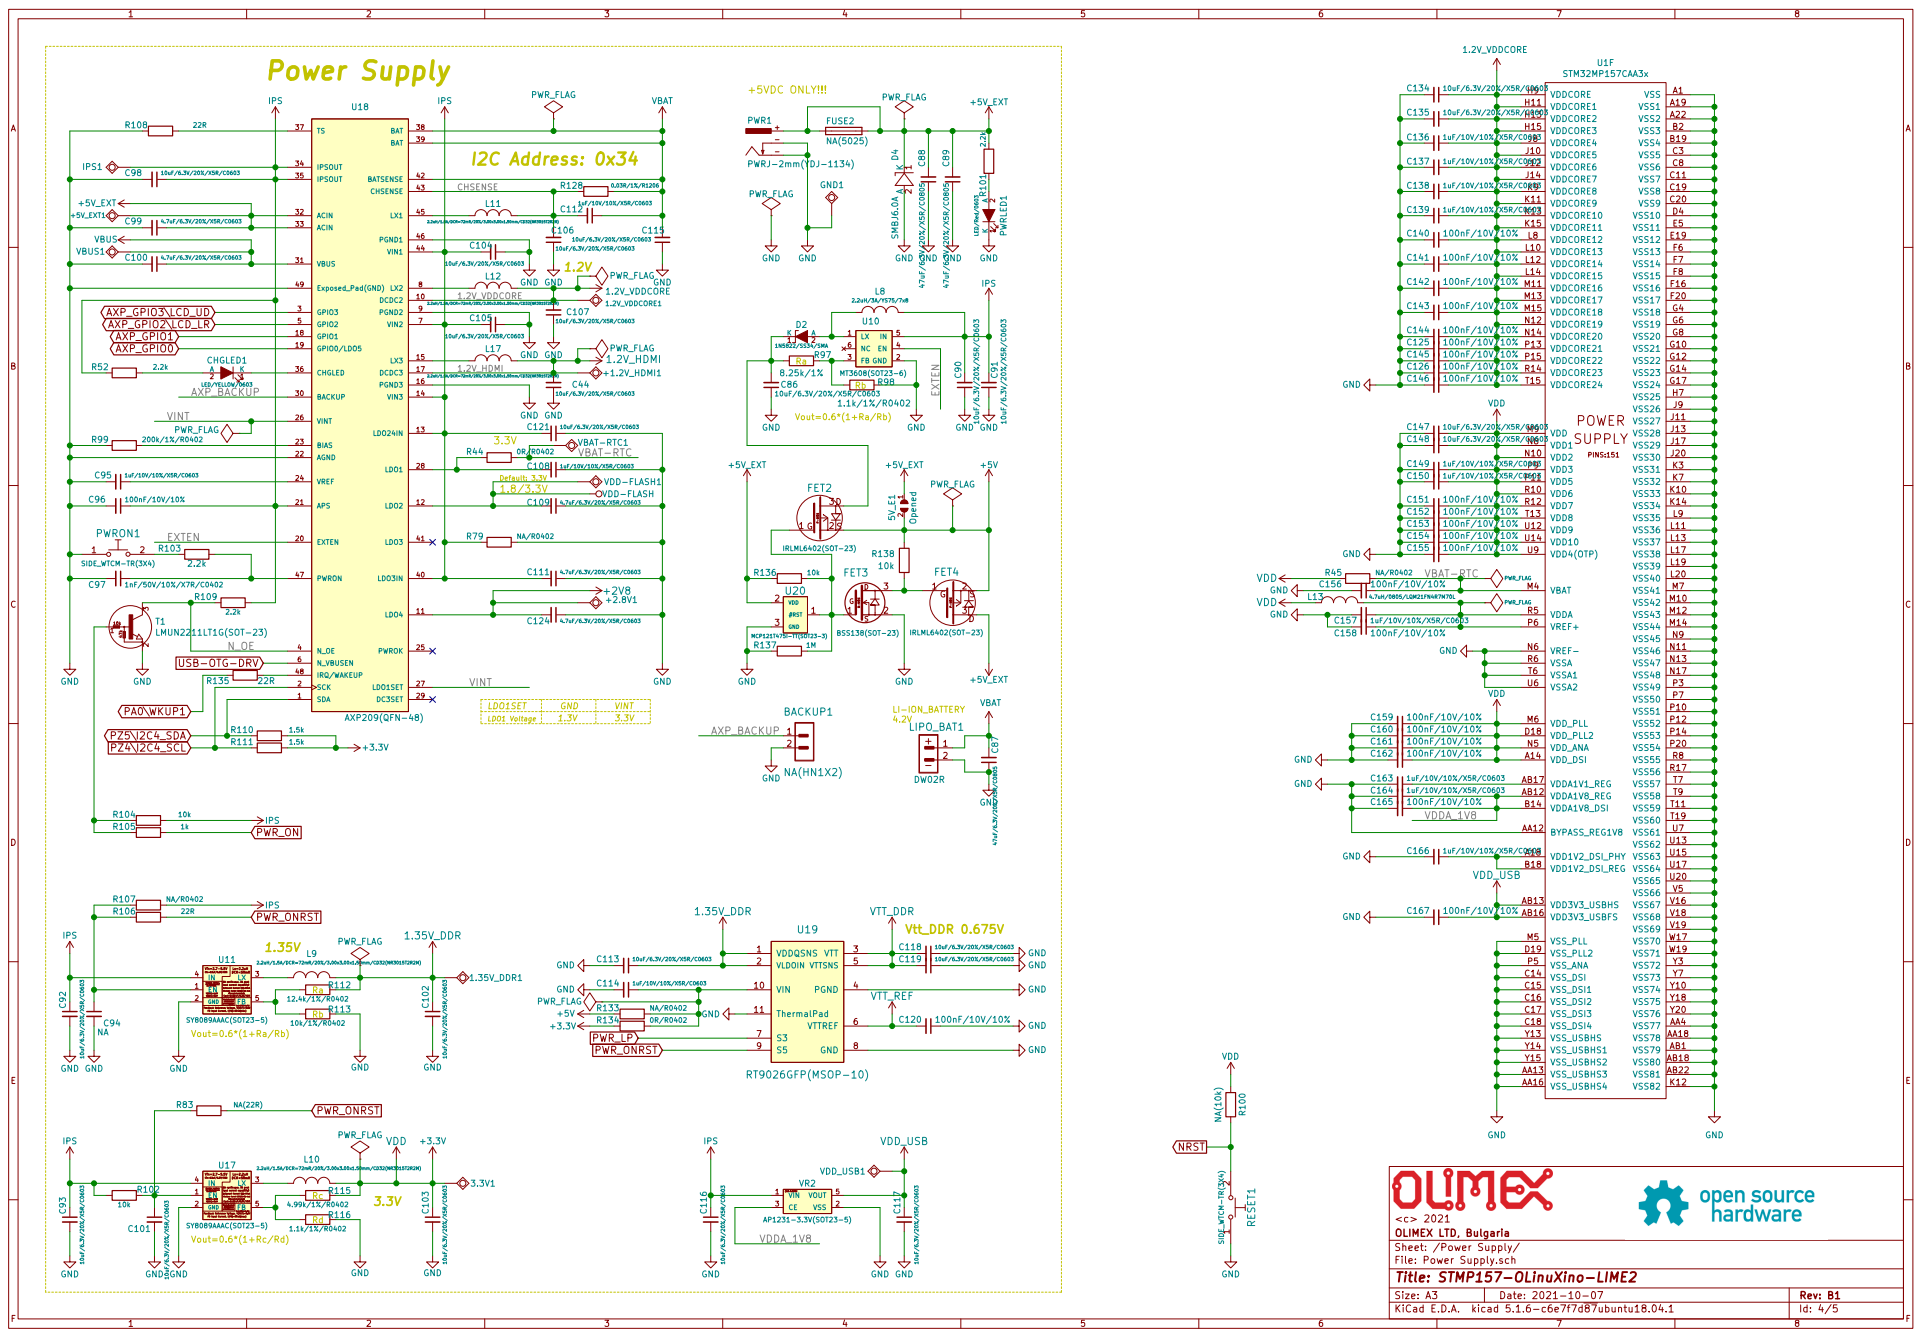
[picture p156: page 4]

Vout=0.6*(1+Ra/Rb) Power Supply

load current capability! Lx=2.2uH

Do not float. Enable control. FB Input Current, I(FB)=50nA(max) Feedback Reference Voltage, V(REF)=0.6V

Vout=0.6*(1+Ra/Rb) EN 1 GND 2

File: Power Supply.sch Sheet: /Power Supply/ OLIMEX LTD, Bulgaria <c> 2021

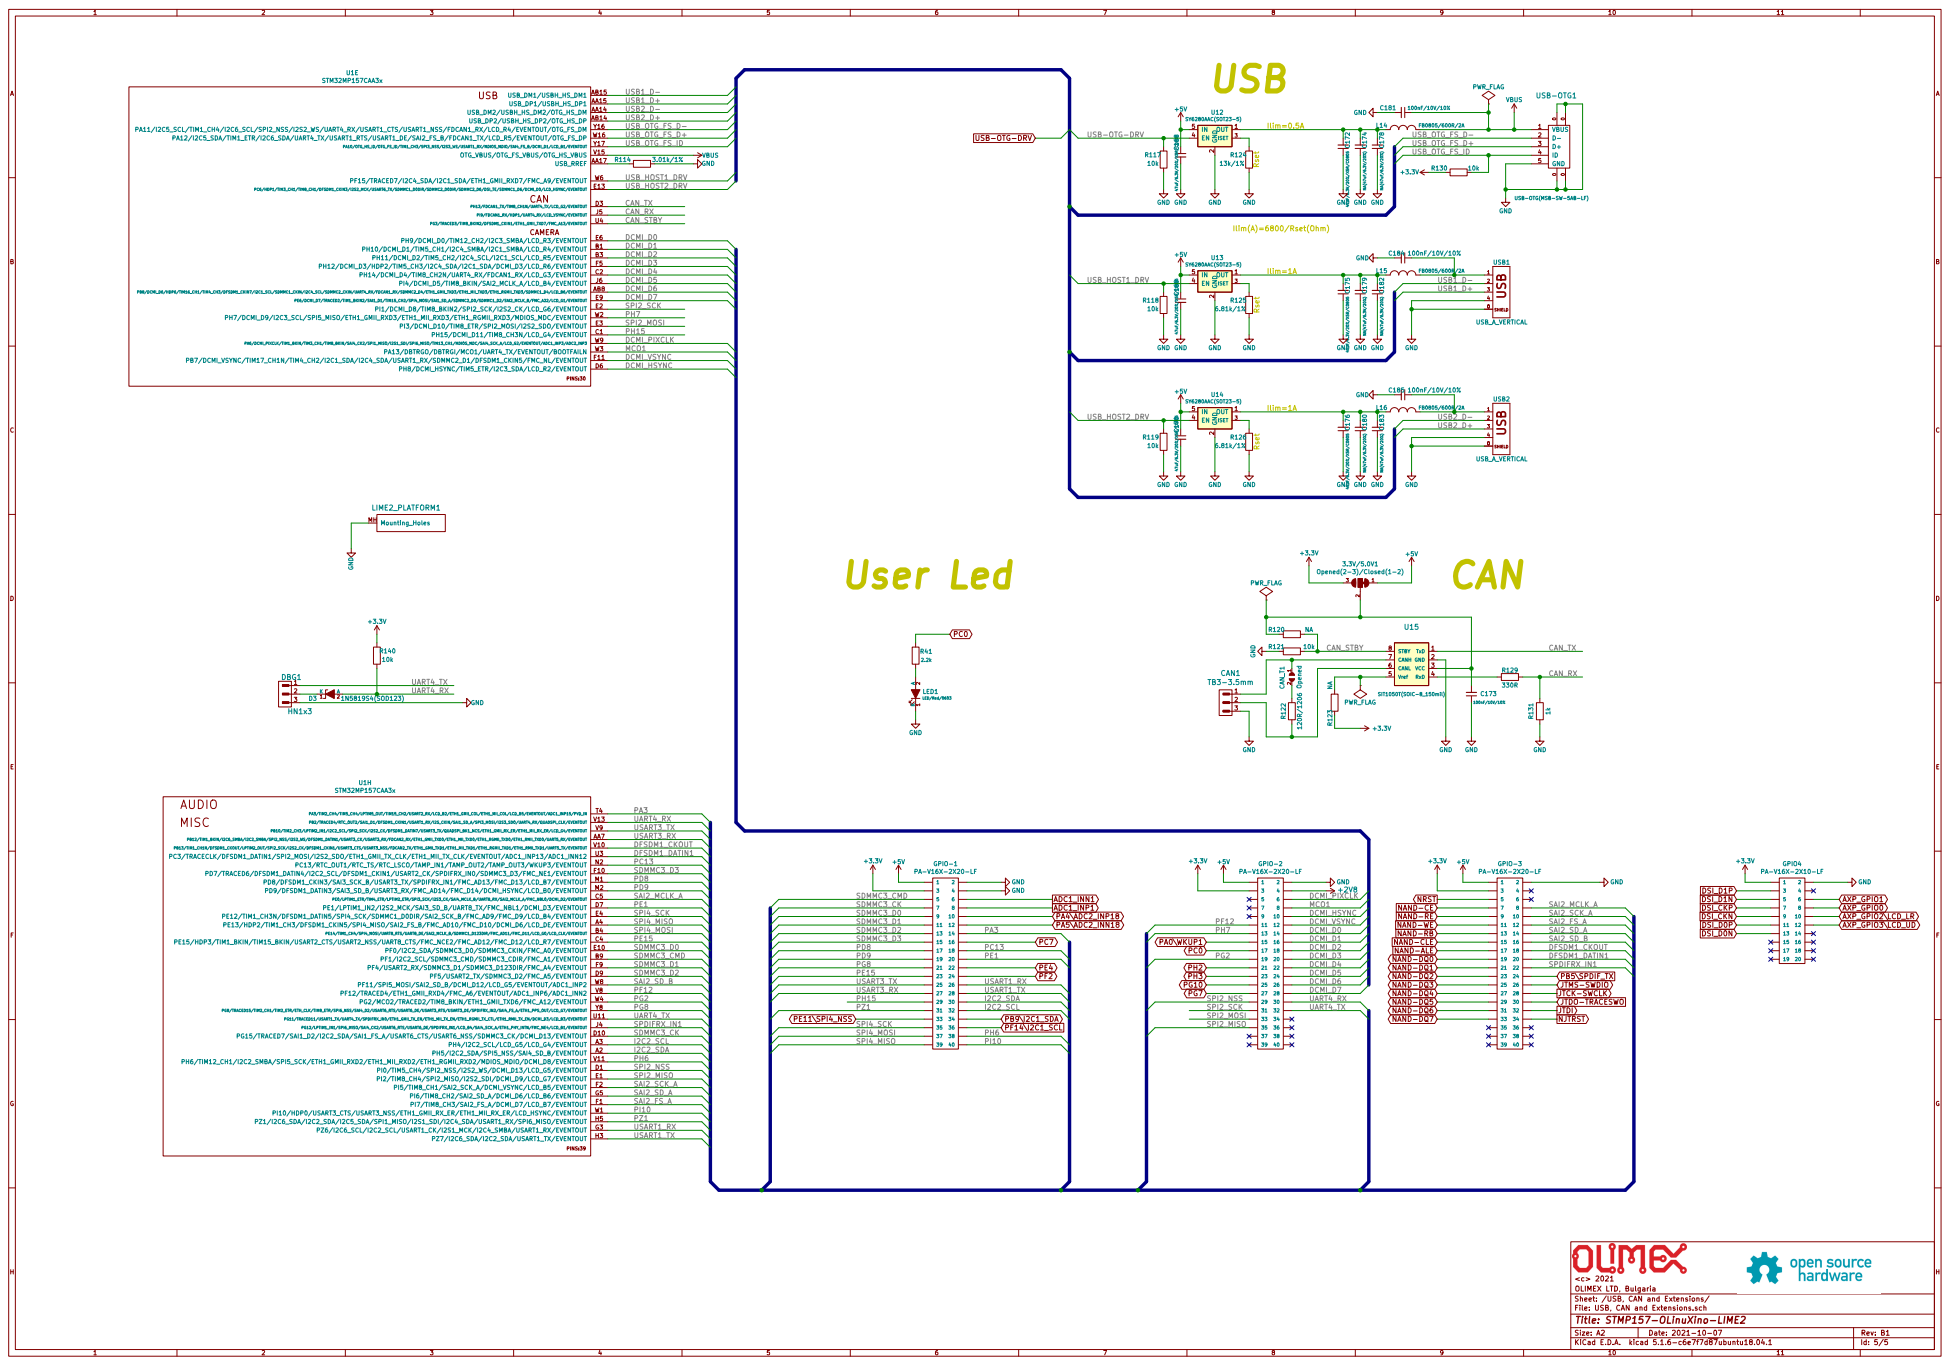
[picture p157: page 5]

Ilim(A)=6800/Rset(Ohm) USBRset

USB-OTG(MSB-SW-5AB-LF) +5V

AXP_GPIO0 NAND-DQ1 NAND-DQ0 NAND-ALE NAND-CLE NAND-RB NAND-WE NAND-RE NAND-CE

File: USB, CAN and Extensions.sch Sheet: /USB, CAN and Extensions/ OLIMEX LTD, Bulgaria <c> 2021
