OLIMEX/OLINUXINO/HARDWARE/A64-OLinuXino/1. Latest hardware revision/A64-OLinuXino hardware revision G/A64-OlinuXino_Rev_G.pdf

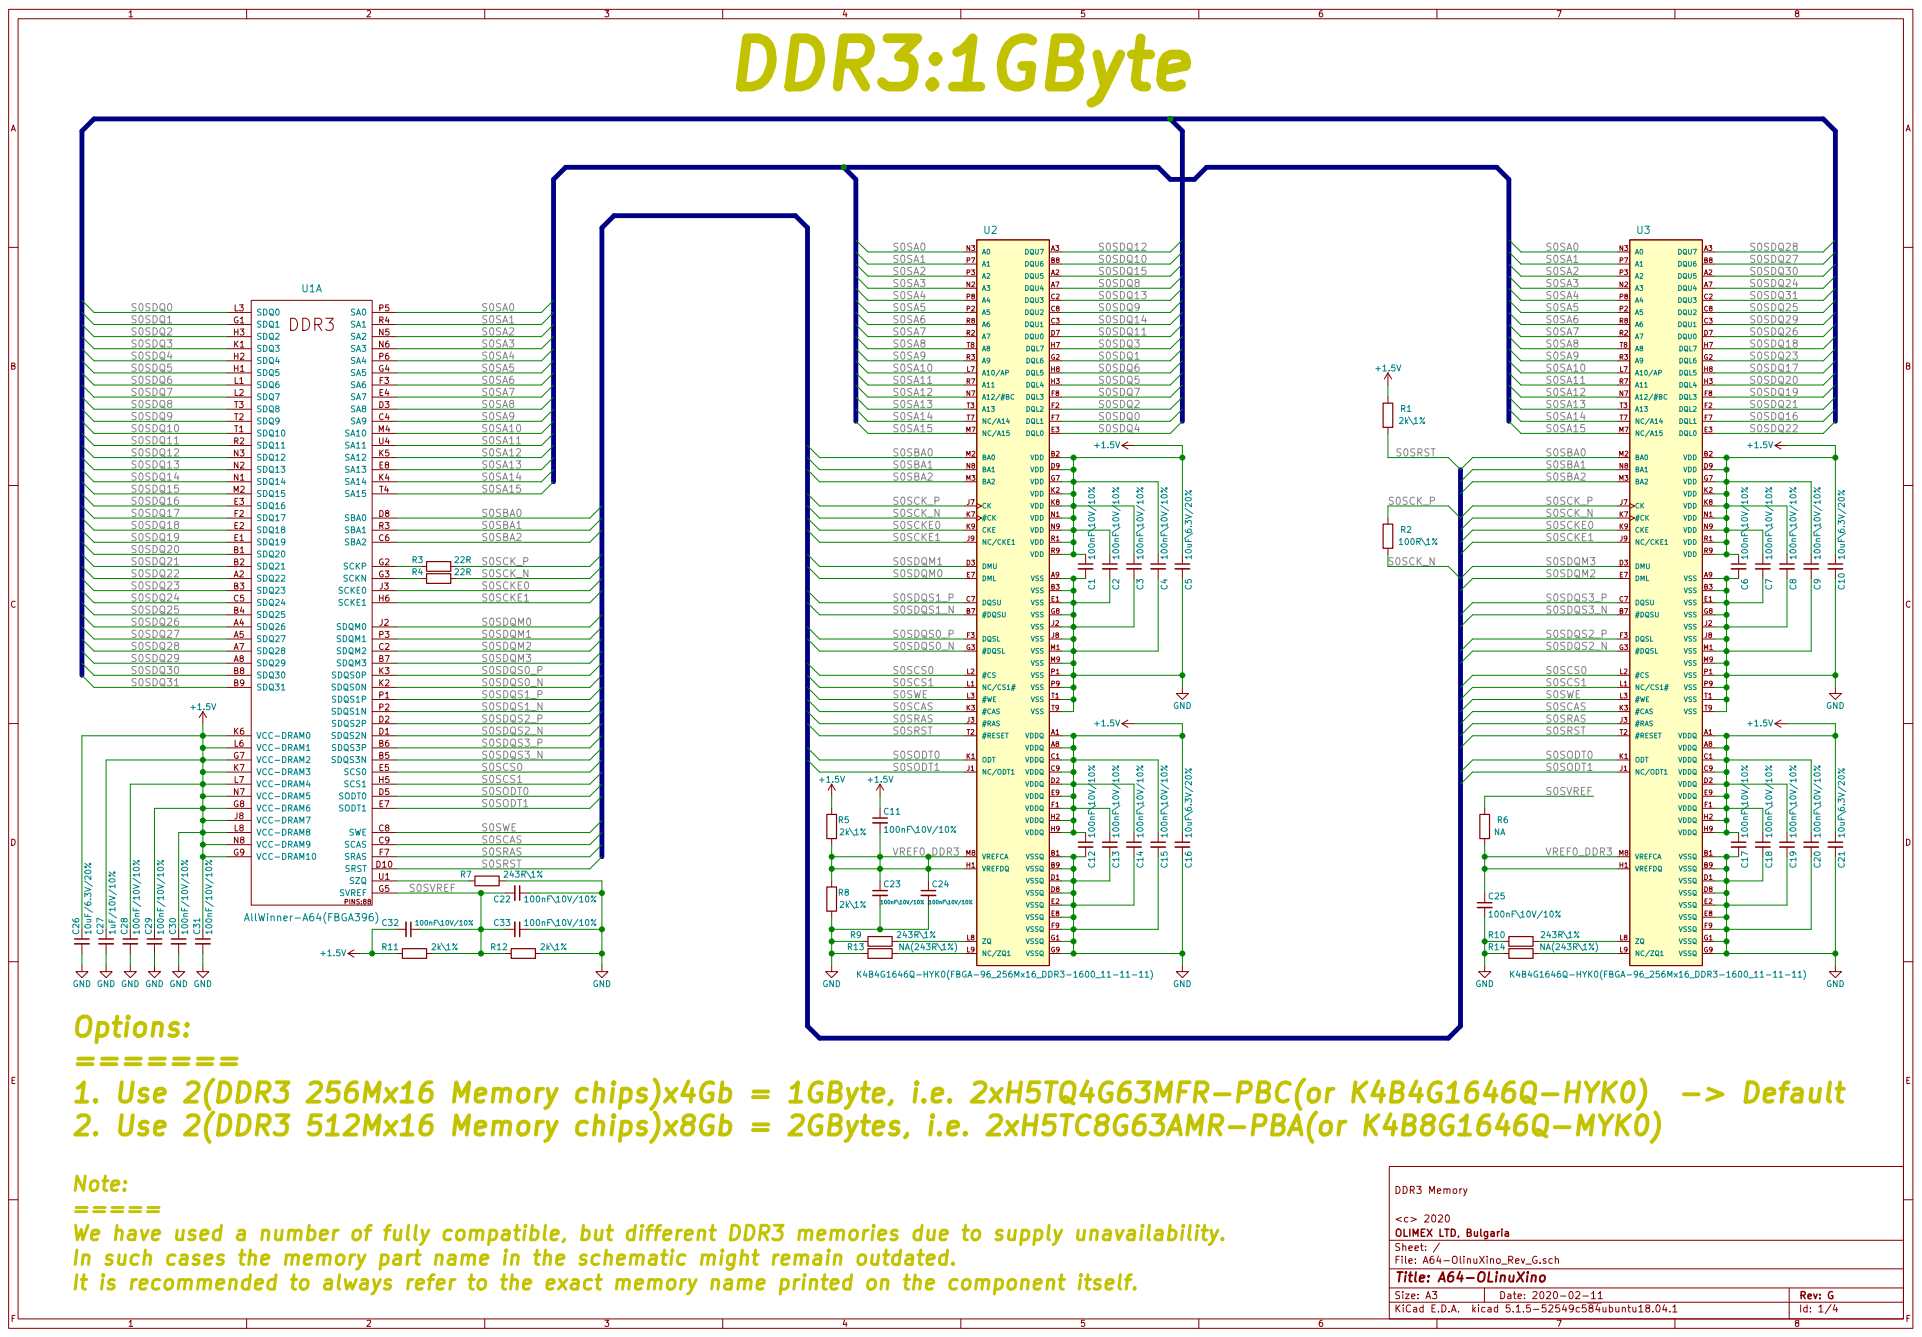
[picture p158: page 1]

1. Use 2(DDR3 256Mx16 Memory chips)x4Gb = 1GByte, i.e. 2xH5TQ4G63MFR-PBC(or K4B4G1646Q-HYK0) -> Default
2. Use 2(DDR3 512Mx16 Memory chips)x8Gb = 2GBytes, i.e. 2xH5TC8G63AMR-PBA(or K4B8G1646Q-MYK0)

In such cases the memory part name in the schematic might remain outdated.
It is recommended to always refer to the exact memory name printed on the component itself.

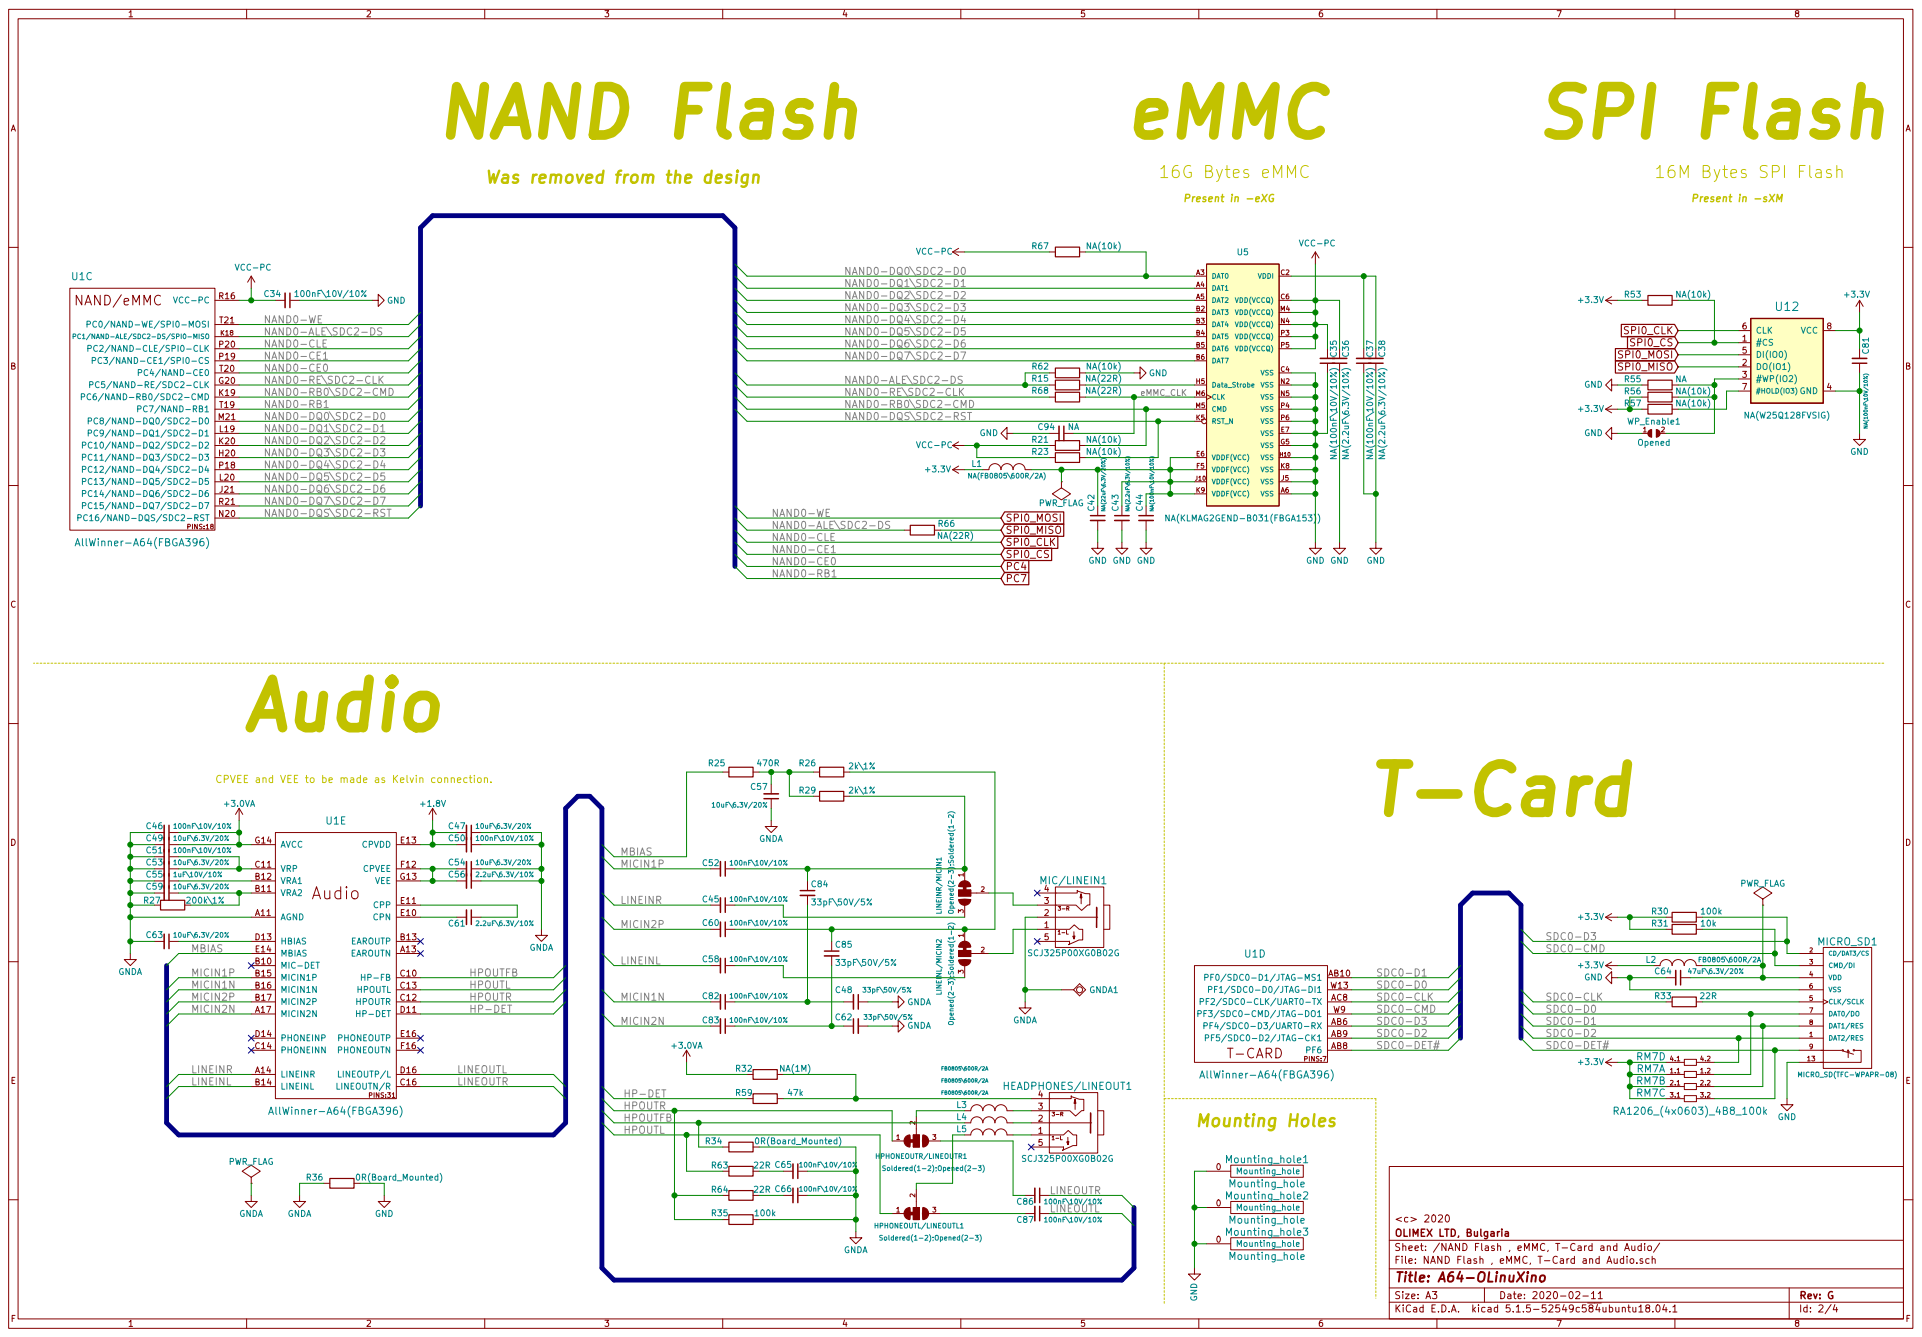
[picture p159: page 2]

Present in -sXM SPI Flash

Was removed from the design

NAND0-RE\SDC2-CLK NAND0-DQS\SDC2-RST NAND0-DQ7\SDC2-D7 NAND0-DQ6\SDC2-D6 NAND0-DQ0\SDC2-D0 NAND0-DQ1\SDC2-D1 NAND0-DQ2\SDC2-D2 NAND0-DQ3\SDC2-D3 NAND0-DQ4\SDC2-D4 NAND0-DQ5\SDC2-D5

CPVEE and VEE to be made as Kelvin connection. Audio

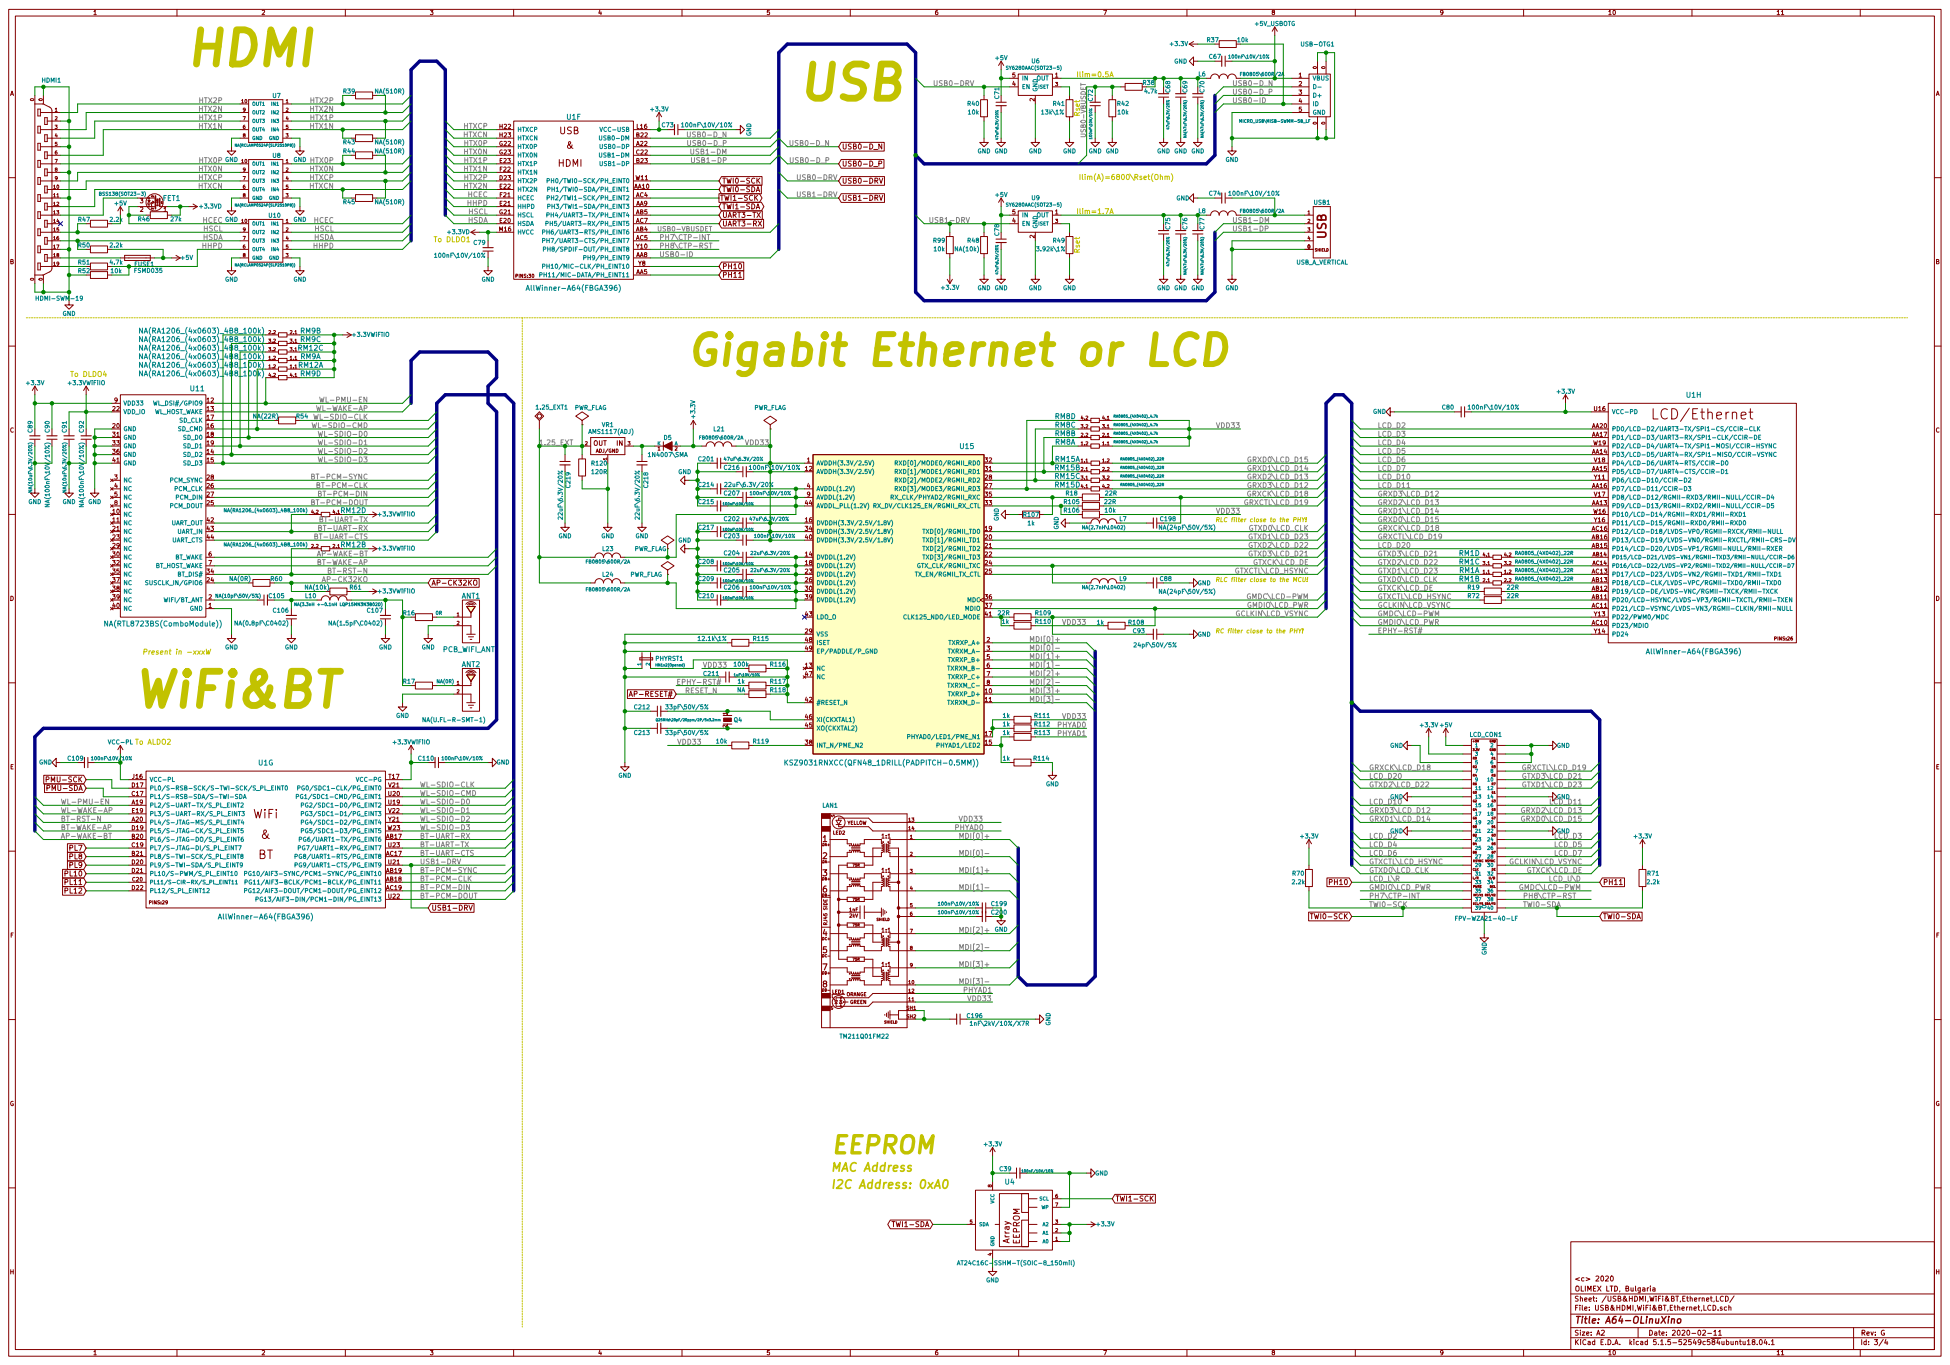
[picture p160: page 3]

+5V_USBOTG
RLC filter close to the PHY! RC filter close to the PHY! Rset Rset

USB0-DRV WL-SDIO-D1 WL-SDIO-D2 WL-SDIO-D3 WL-WAKE-AP WL-PMU-EN

WL-SDIO-CLK WL-SDIO-CMD

AllWinner-A64(FBGA396) C90 NA(100nF\10V/10%) C89 NA(10uF\6.3V/20%) GND

Present in -xxxW WiFi&BT

AP-RESET# PMU-SDA

4 SDA 5 SCL 6 WP 7 VCC

File: USB&HDMI,WiFi&BT,Ethernet,LCD.sch Sheet: /USB&HDMI,WiFi&BT,Ethernet,LCD/ OLIMEX LTD, Bulgaria <c> 2020

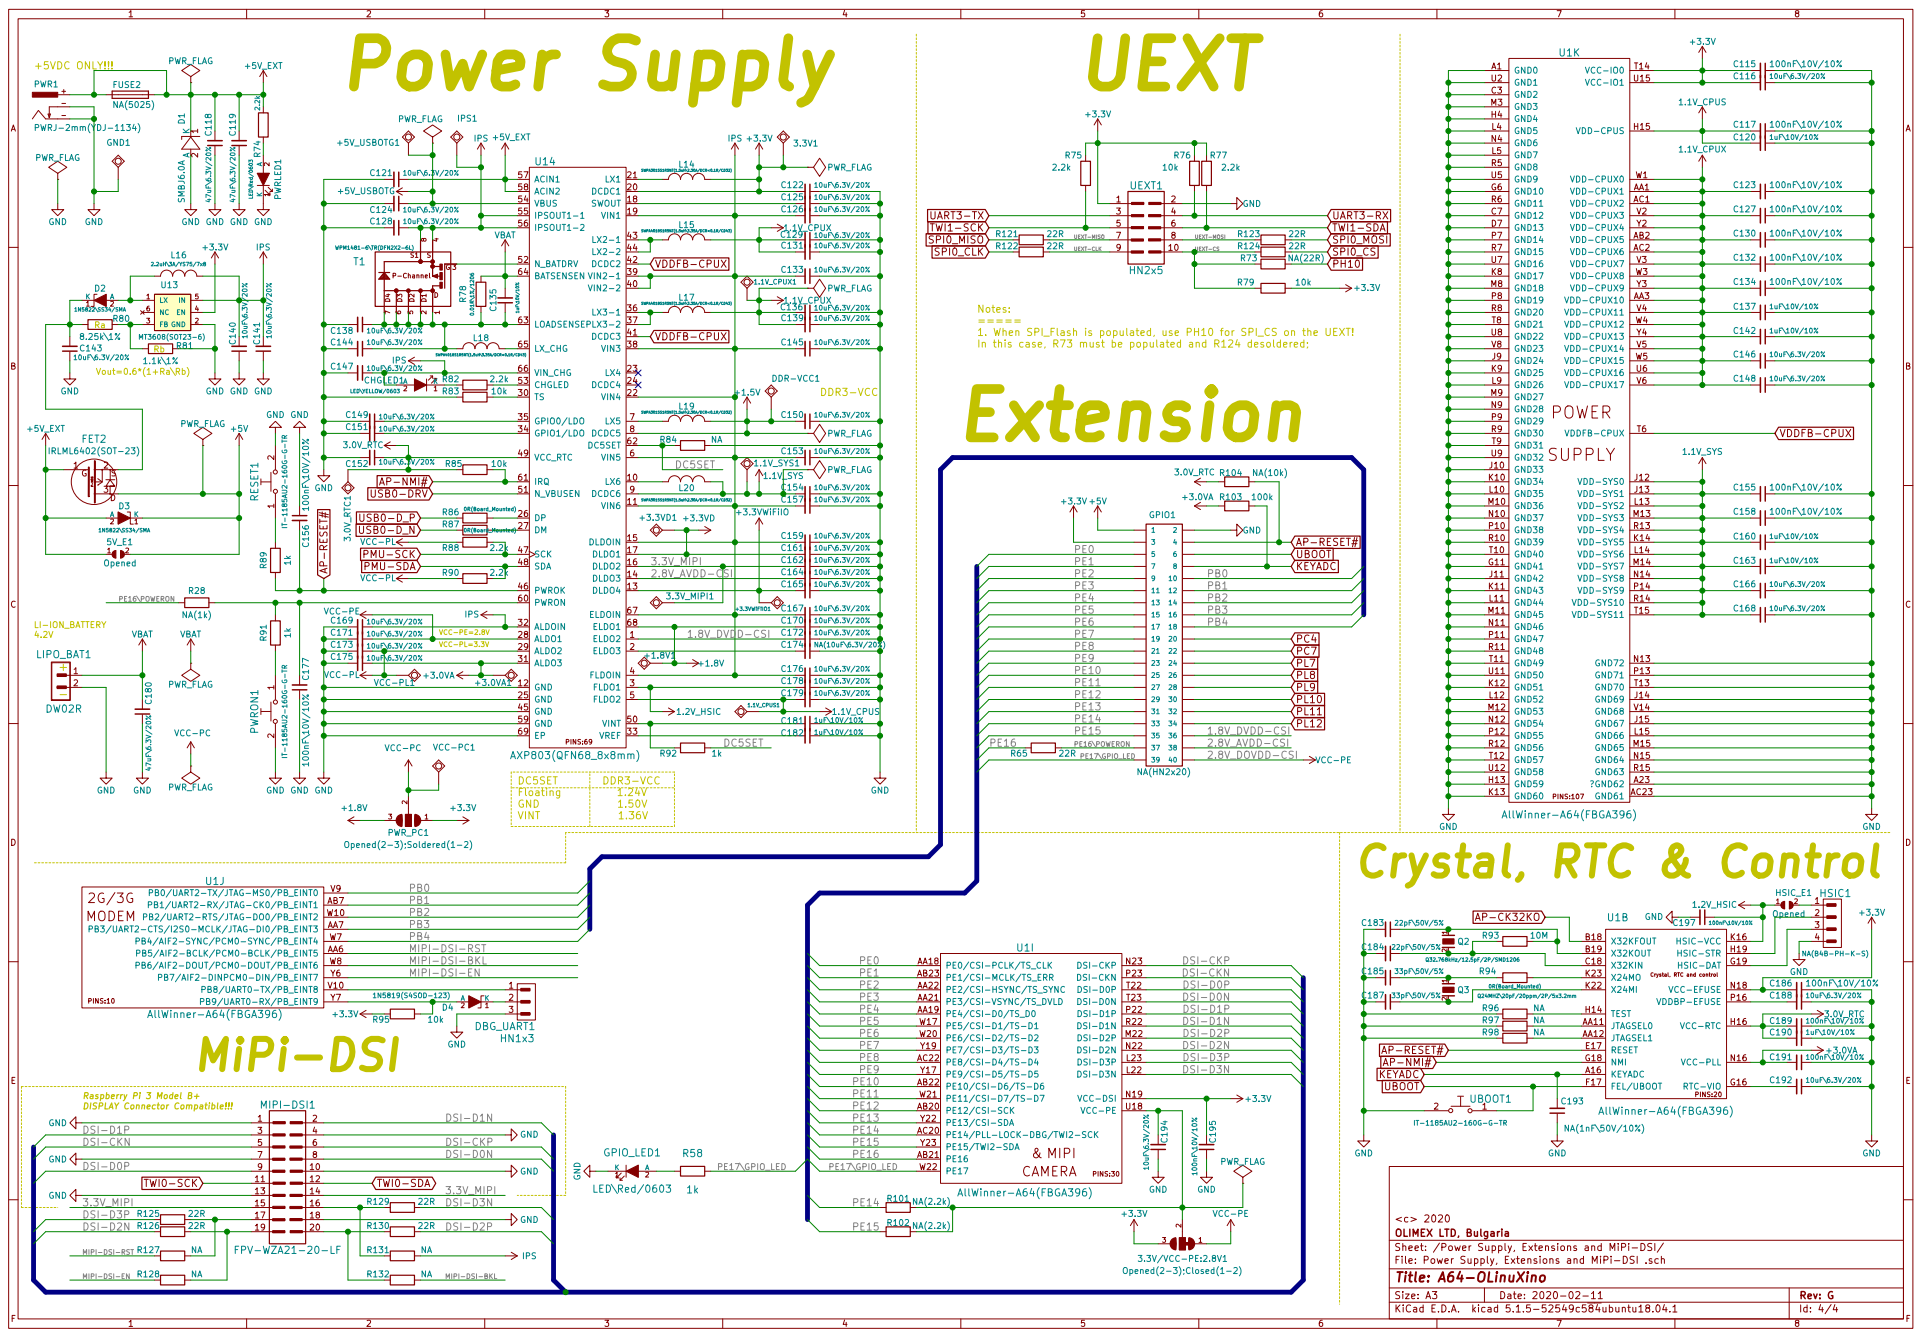
[picture p161: page 4]

VDD-CPUX1 AA1 VDD-CPUX10 AA3 VDD-CPUX5 AB2 VDD-CPUX2 AC1 VDD-CPUX6 AC2 GND61 AC23

1. When SPI_Flash is populated, use PH10 for SPI_CS on the UEXT!
In this case, R73 must be populated and R124 desoldered;

AP-RESET# VDDFB-CPUX

1 2 RESET1 IT-1185AU2-160G-G-TR GND GND R89 1k C156 100nF\10V/10%

1 2PWRON1 IT-1185AU2-160G-G-TR VCC-PE C171 10uF\6.3V/20% C175 10uF\6.3V/20%

Crystal, RTC and control PINS:20 KEYADC A16

AP-RESET# AP-NMI#

MIPI-DSI-BKL DSI-CKN

3 3.3V/VCC-PE:2.8V1 Opened(2-3);Closed(1-2) +3.3V

File: Power Supply, Extensions and MiPi-DSI .sch Sheet: /Power Supply, Extensions and MiPi-DSI/ OLIMEX LTD, Bulgaria <c> 2020
