OLIMEX/OLINUXINO/HARDWARE/iMX233-OLinuXino-Mini/1. Latest hardware revision/iMX233-OLINUXINO-MINI hardware revision E/iMX233-OLINUXINO-MINI_Rev_E.pdf

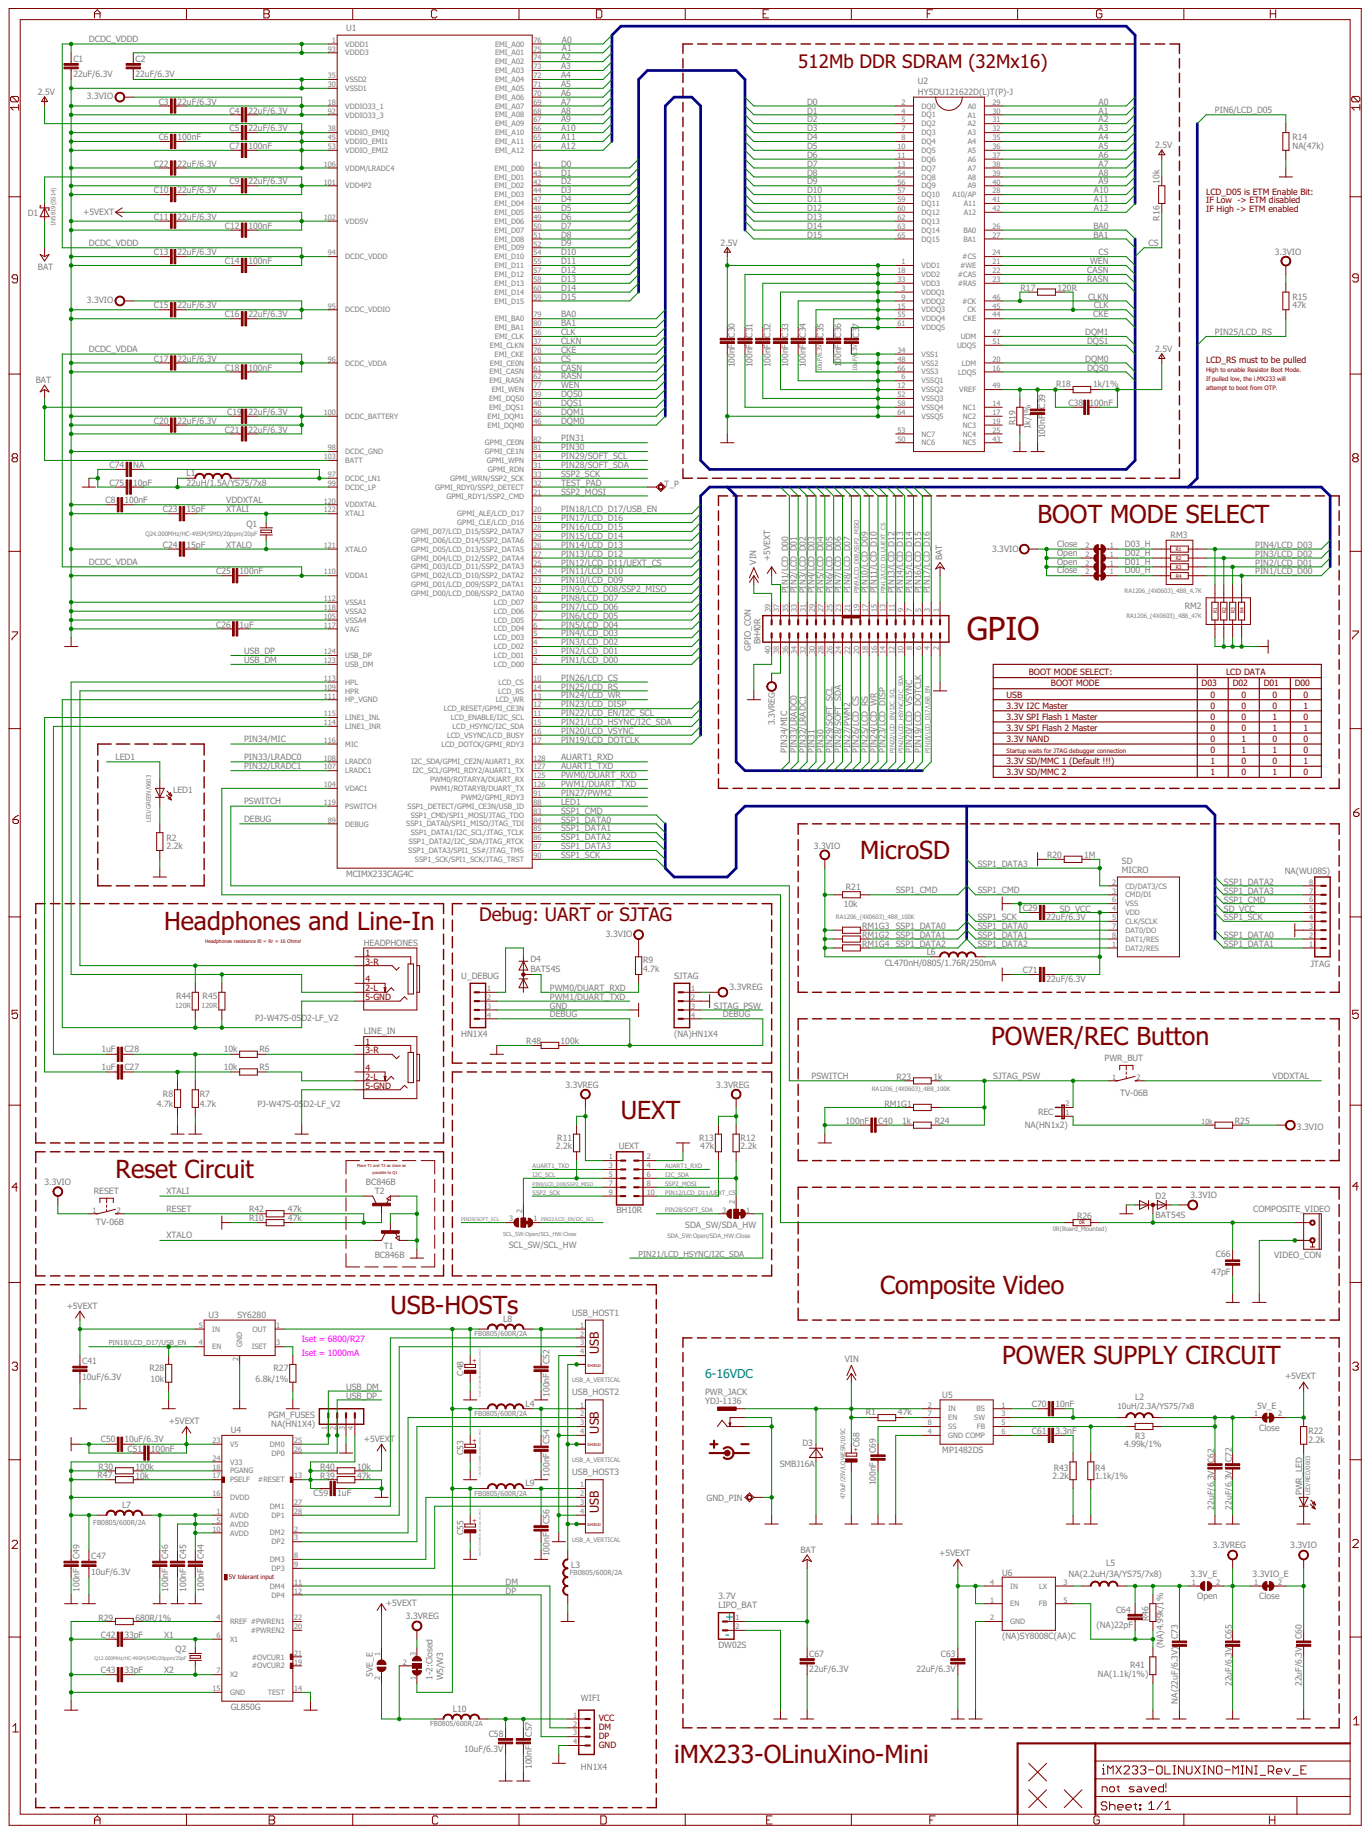
[picture p162: page 1]

LCD_D05 is ETM Enable Bit: IF Low -> ETM disabled

IF High -> ETM enabled

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

103 | PIN29/SOFT_SCL

C74 C75 | | PIN28/SOFT_SDA

Close Open Open Close

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

Headphones and Line-In

Debug: UART or SJTAG

Headphones resistance Rl = Rr = 16 Ohms!
