OLIMEX/OLINUXINO/HARDWARE/A33/A33-OLinuXino_Rev_A.pdf

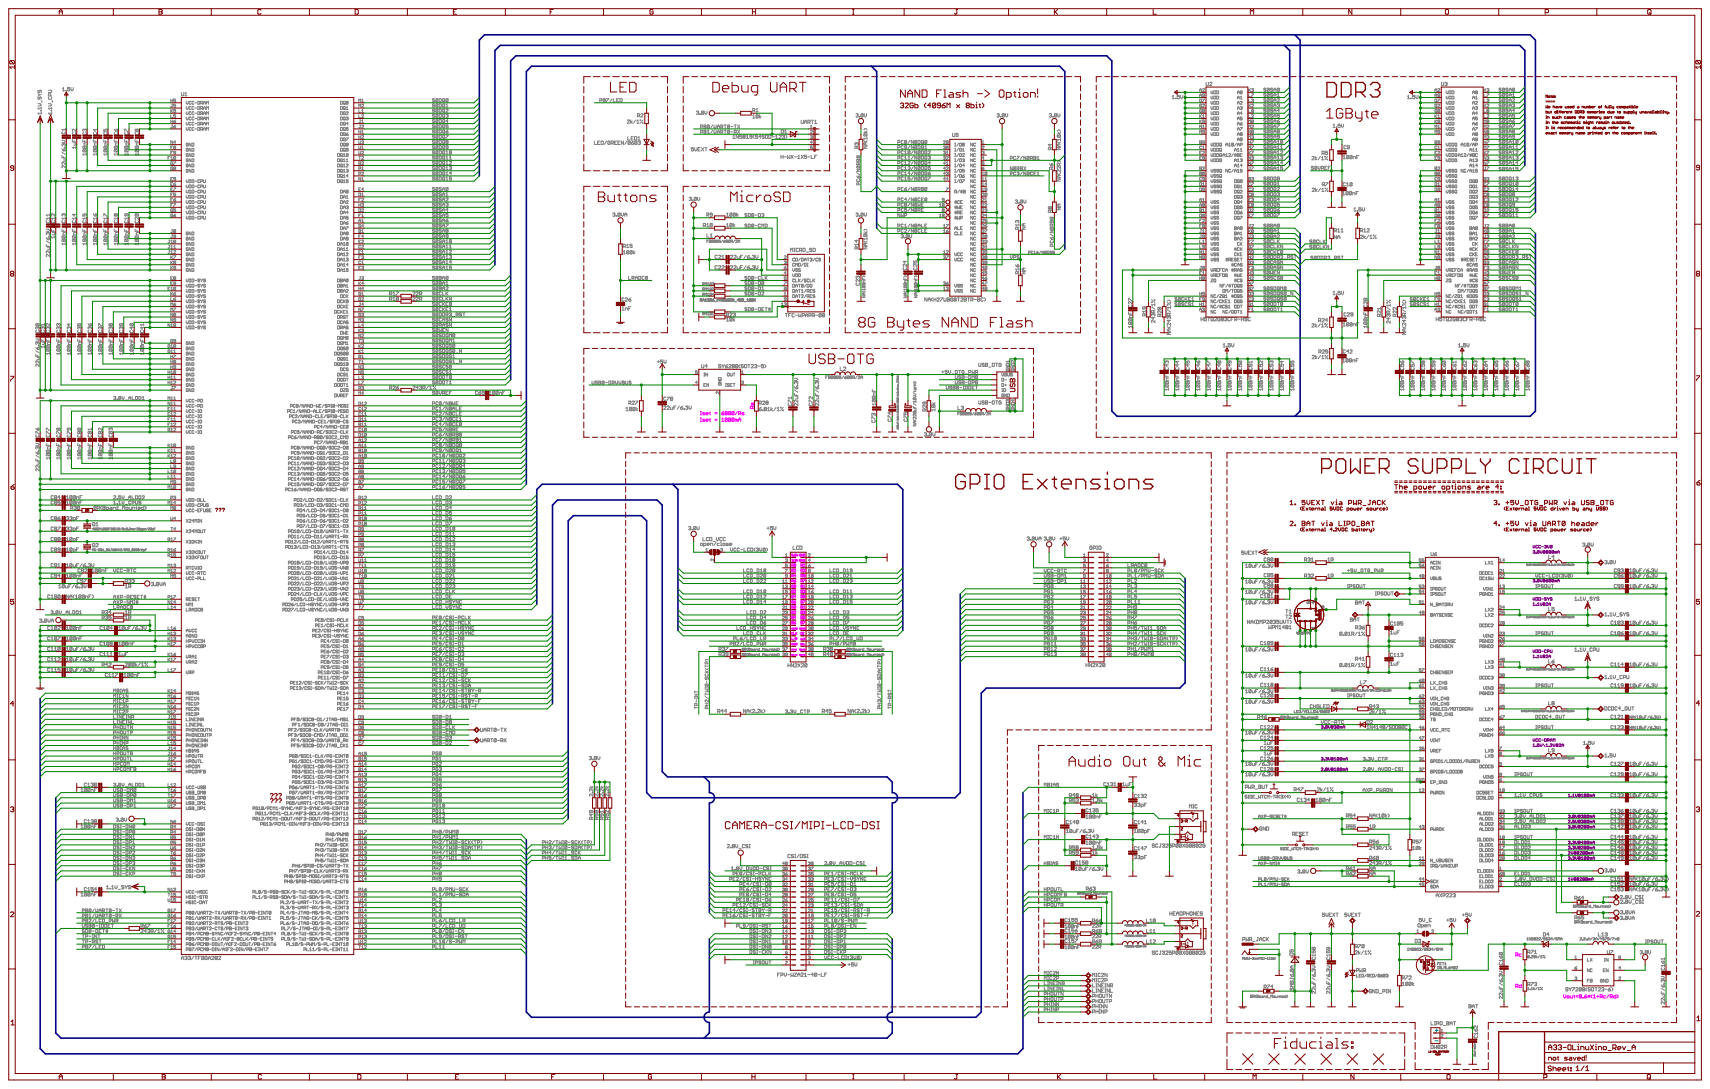
[picture p163: page 1]
