OLIMEX/OLINUXINO/HARDWARE/A13-OLinuXino-MICRO/A13-OLinuXino-MICRO_Rev_B.pdf

DQL0 | E3 DQL1 | F7 DQL2 | F2 DQL3 | F8 DQL4 | H3 DQL5 | H8 DQL6 | G2 DQL7 | H7
DQU0 | D7 DQU1 | C3 DQU2 | C8 DQU3 | C2 DQU4 | A7 DQU5 | A2 DQU6 | B8 DQU7 | A3

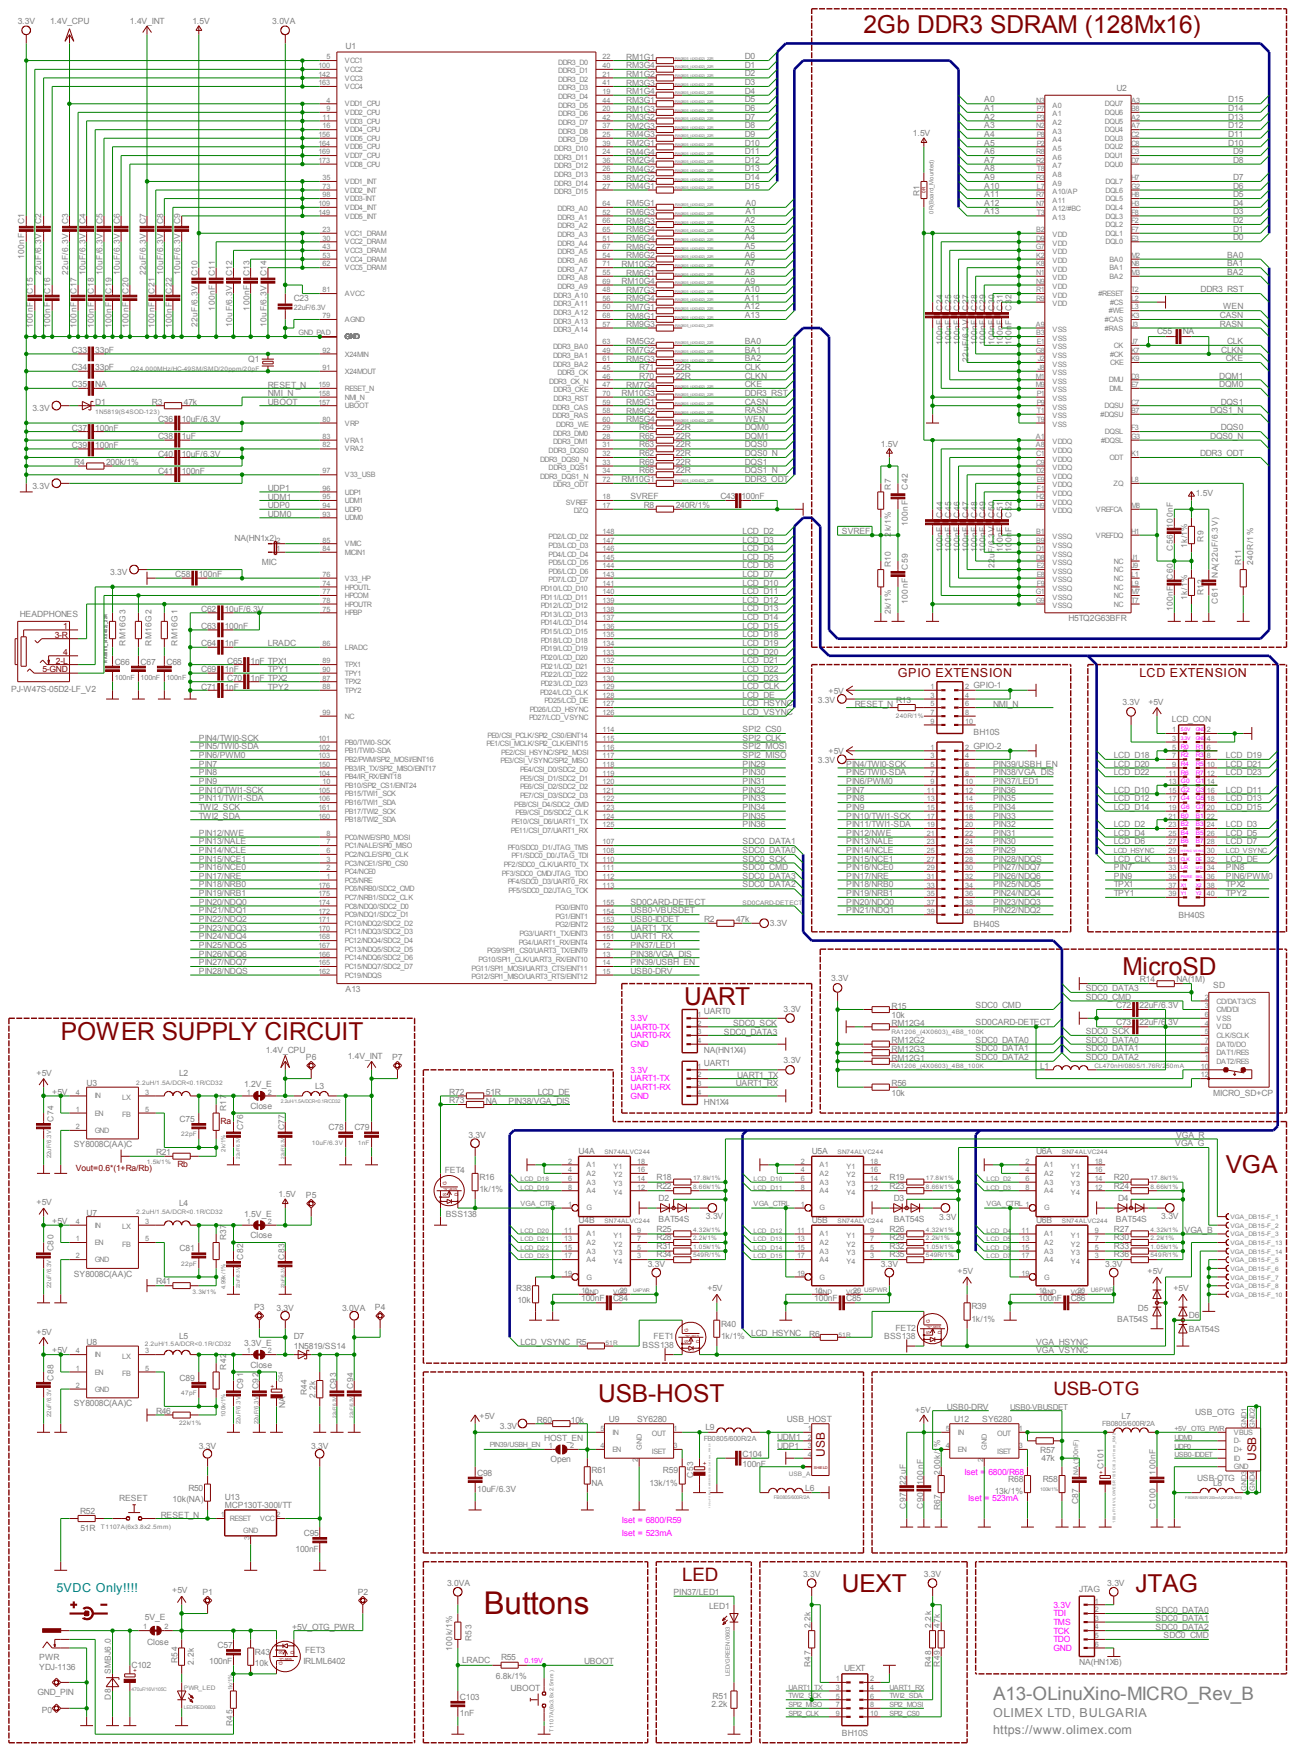
[picture p164: page 1]

VCC2 100 | 40 RM3G4 D1 RA0805_(4X0402)_22R
VCC3 142 | RM1G2 D2 RA0805_(4X0402)_22R
VCC4 163 | RM3G3 D3 RA0805_(4X0402)_22R
VDD1_CPU 4 | D4 19 RM1G4 RA0805_(4X0402)_22R

VCC4_DRAM 53 | A6 54 RM6G2 RA0805_(4X0402)_22R

C62 | 10uF/6.3V | HPBP 75 | LCD_D13
C63 | 100nF | LRADC | LRADC 86 | LCD_D14
C64 | 1nF | | | 135 LCD_D18

HPOUTR 78 | LCD_D12

VGA_R
VGA_G

Rb Vout=0.6*(1+Ra/Rb)

3 549R/1% | LCD_D15 | | A4 17 | 3 549R/1% LCD_D7 | | A4 17 | 549R/1%

A13-OLinuXino-MICRO_Rev_B
OLIMEX LTD, BULGARIA
https://www.olimex.com
