OLIMEX/OLINUXINO/HARDWARE/A13-OLinuXino/A13-OLinuXino_Rev_C.sch.pdf

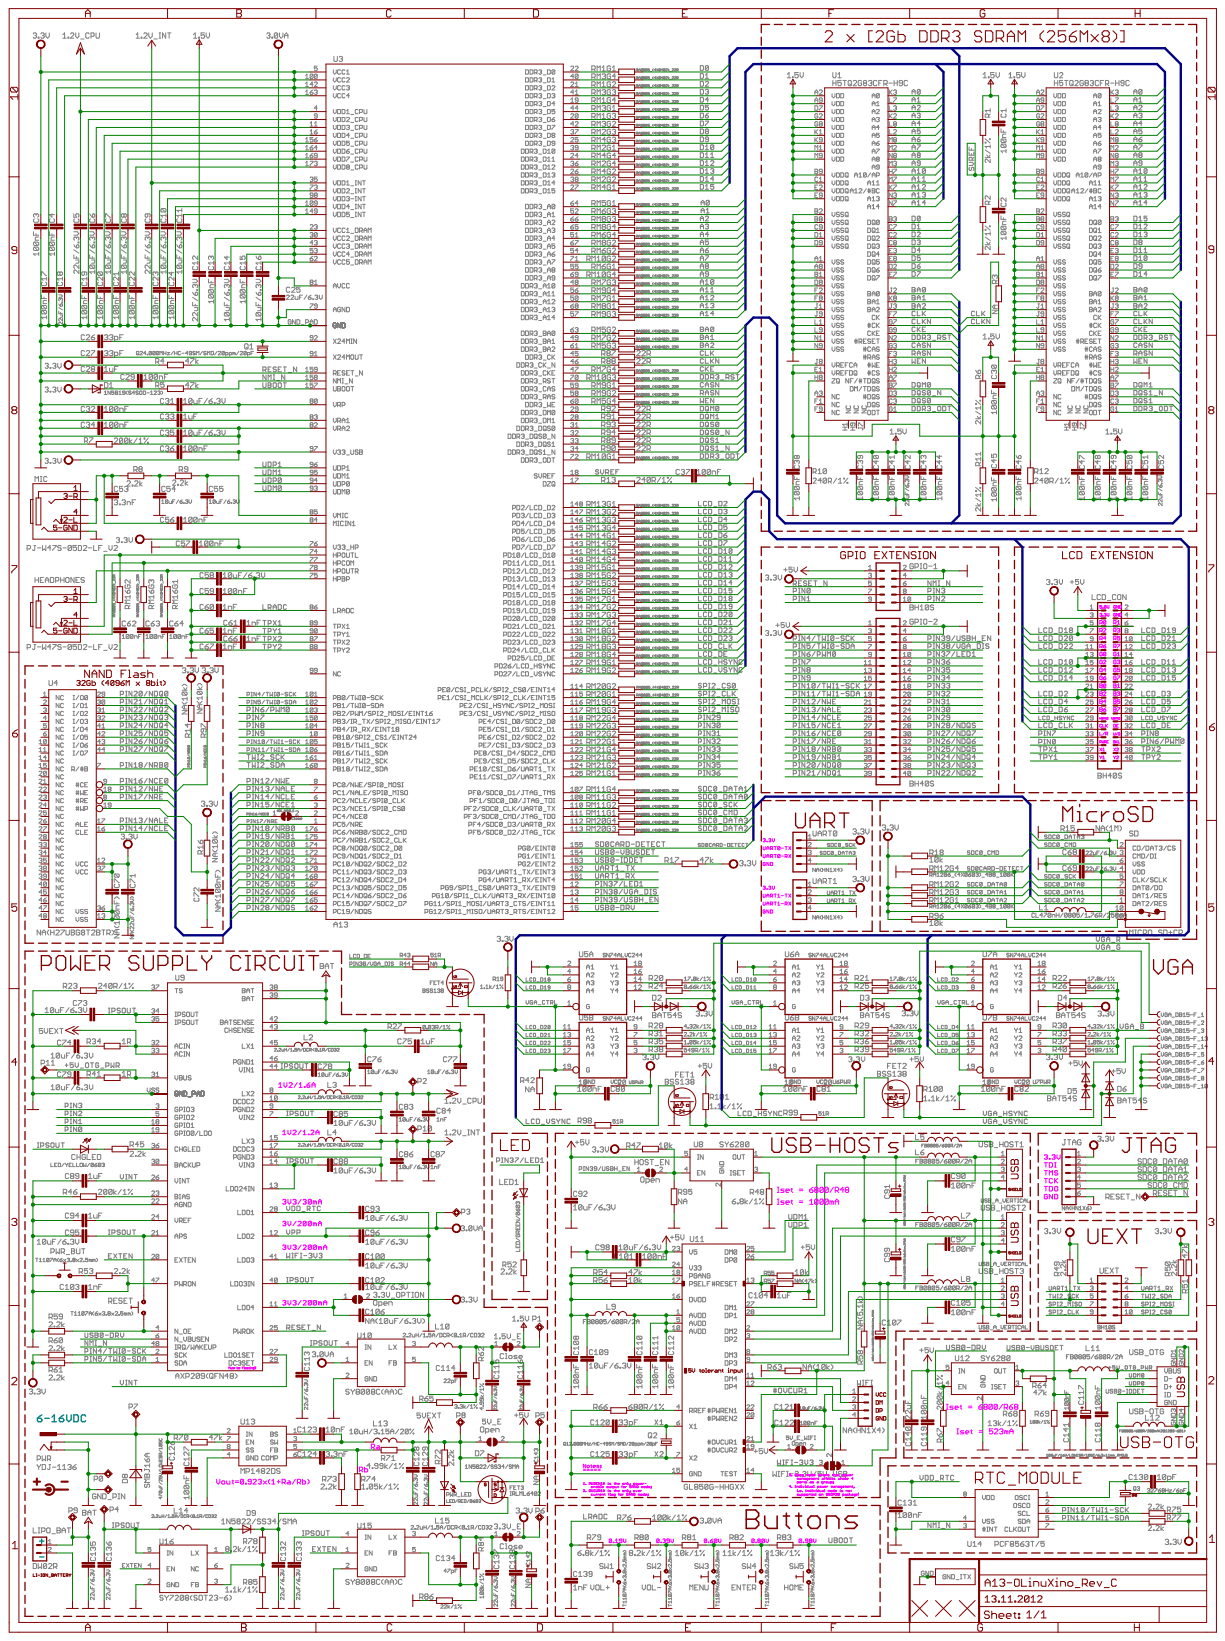
[picture p165: page 1]
