OLIMEX/OLINUXINO/HARDWARE/iMX233-OLinuXino-Mini/iMX233-OLINUXINO-MINI_Rev_C.sch.pdf

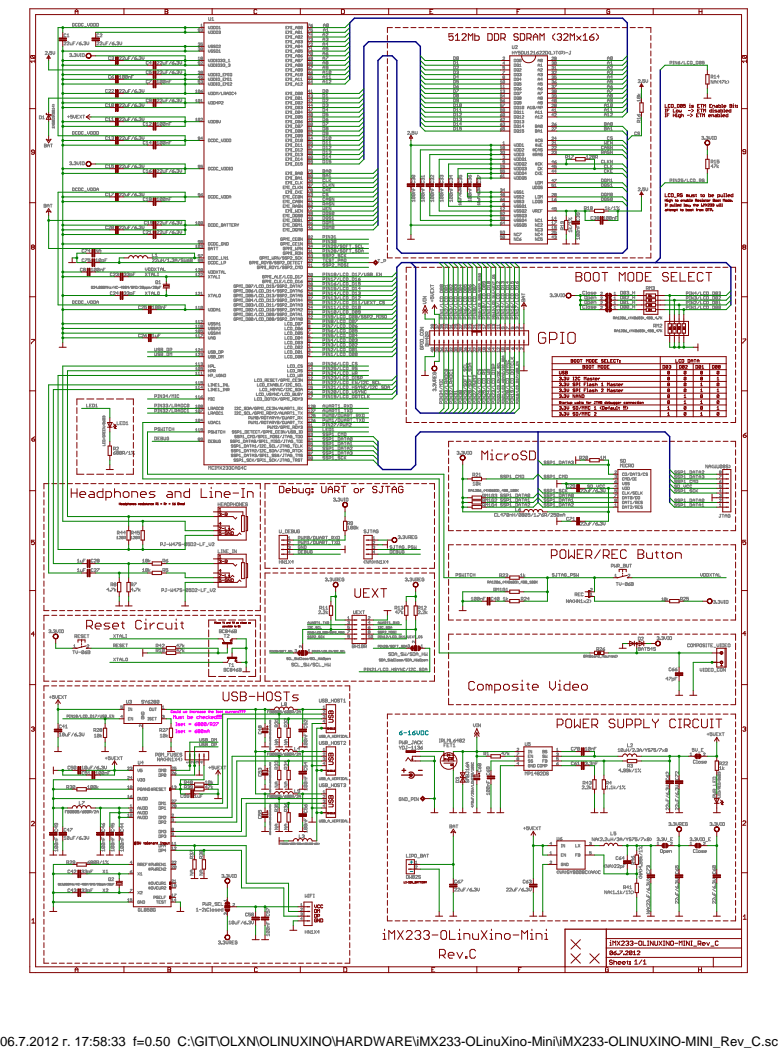
[picture p166: page 1]

06.7.2012 г. 17:58:33 f=0.50 C:\GIT\OLXN\OLINUXINO\HARDWARE\iMX233-OLinuXino-Mini\iMX233-OLINUXINO-MINI_Rev_C.sch
