OLIMEX/OLINUXINO/HARDWARE/A20-OLinuXino-LIME2/1. Latest hardware revision/A20-OLinuXino-Lime2_Rev_M_sch.pdf

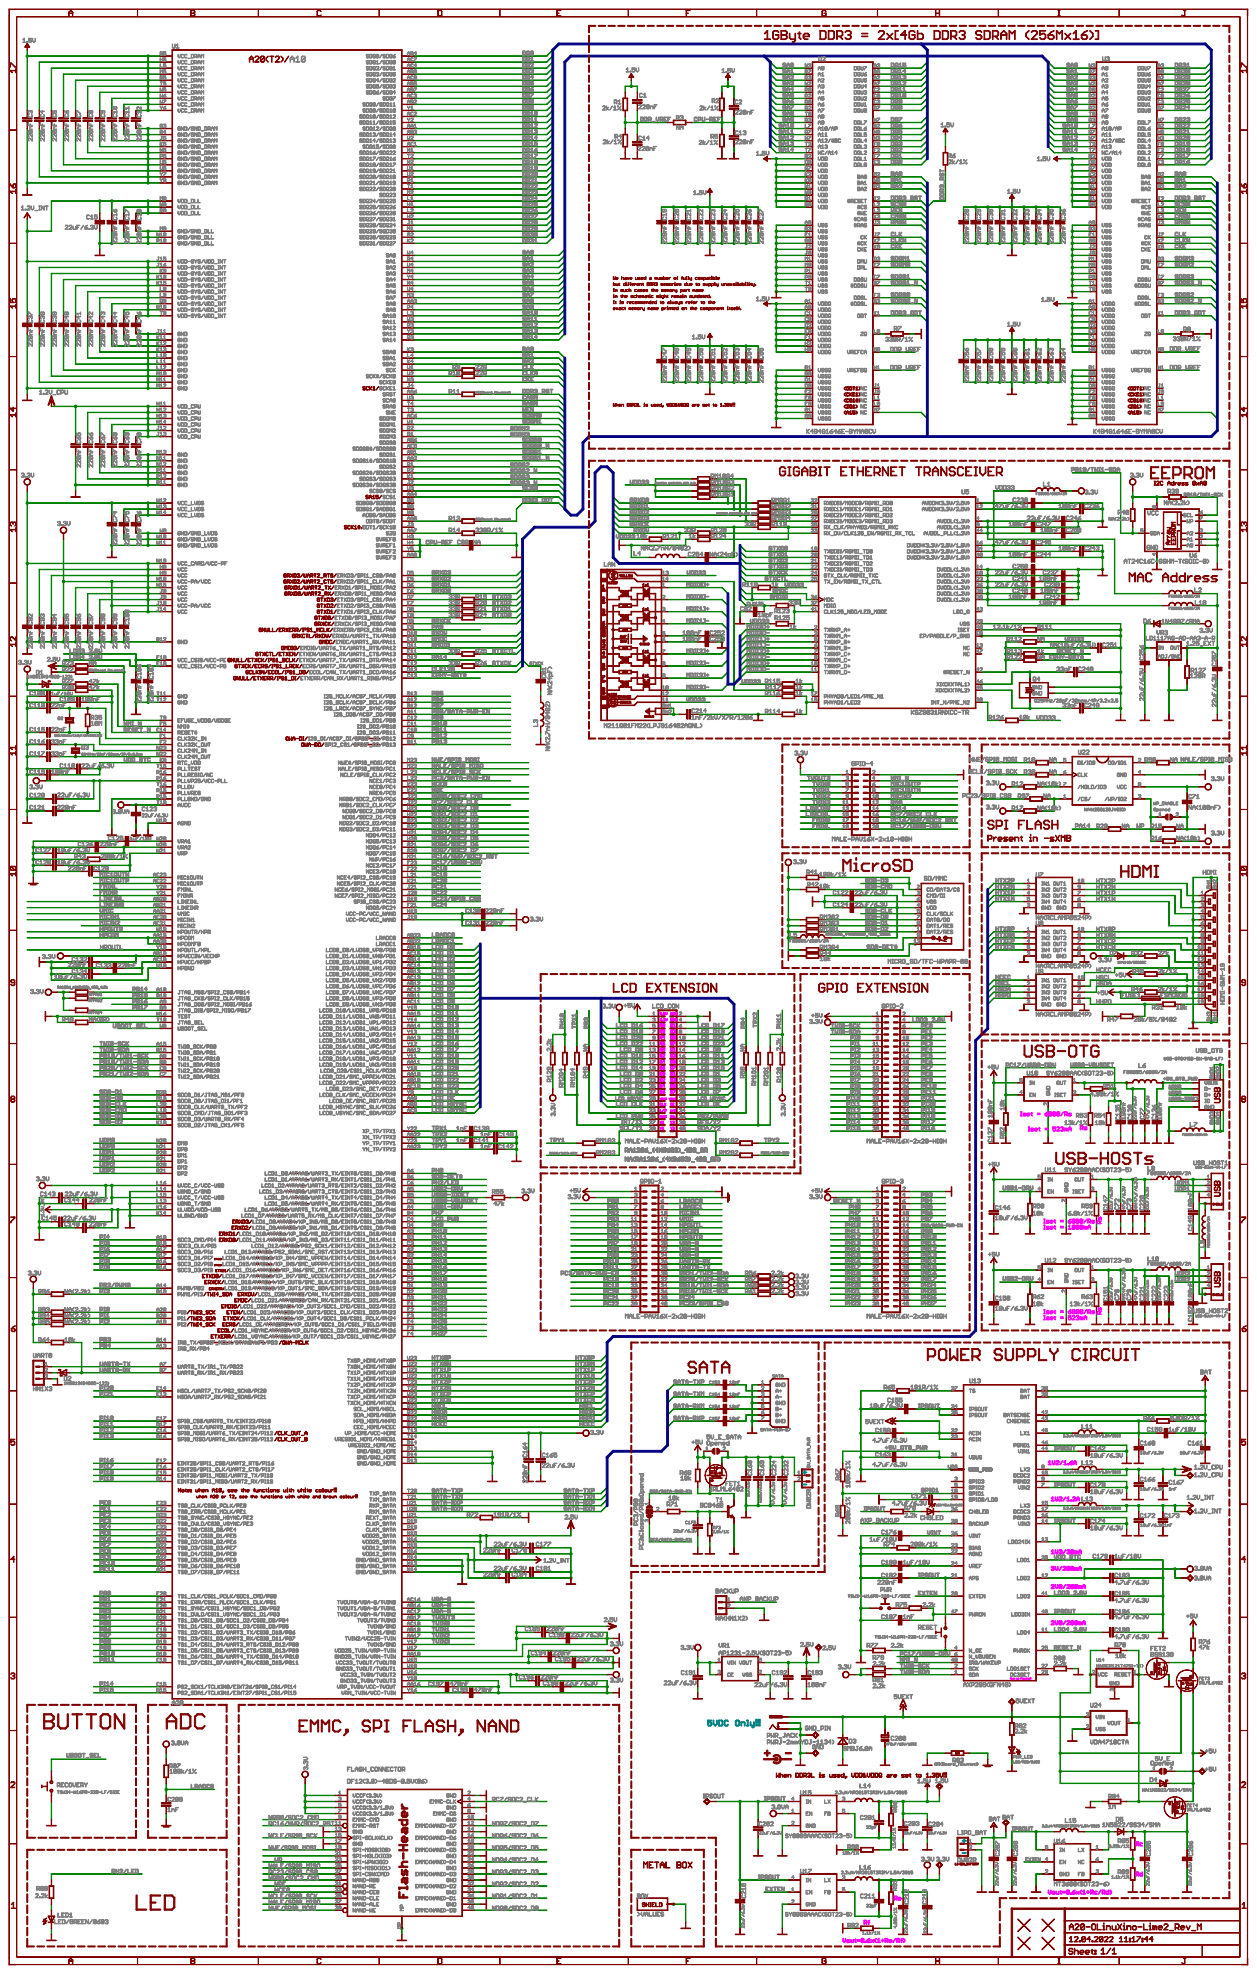
[picture p167: page 1]
