OLIMEX/OLINUXINO/HARDWARE/A20-OLinuXino-MICRO/1. Latest hardware revision/A20-OLINUXINO-MICRO_Rev_N.pdf

A10

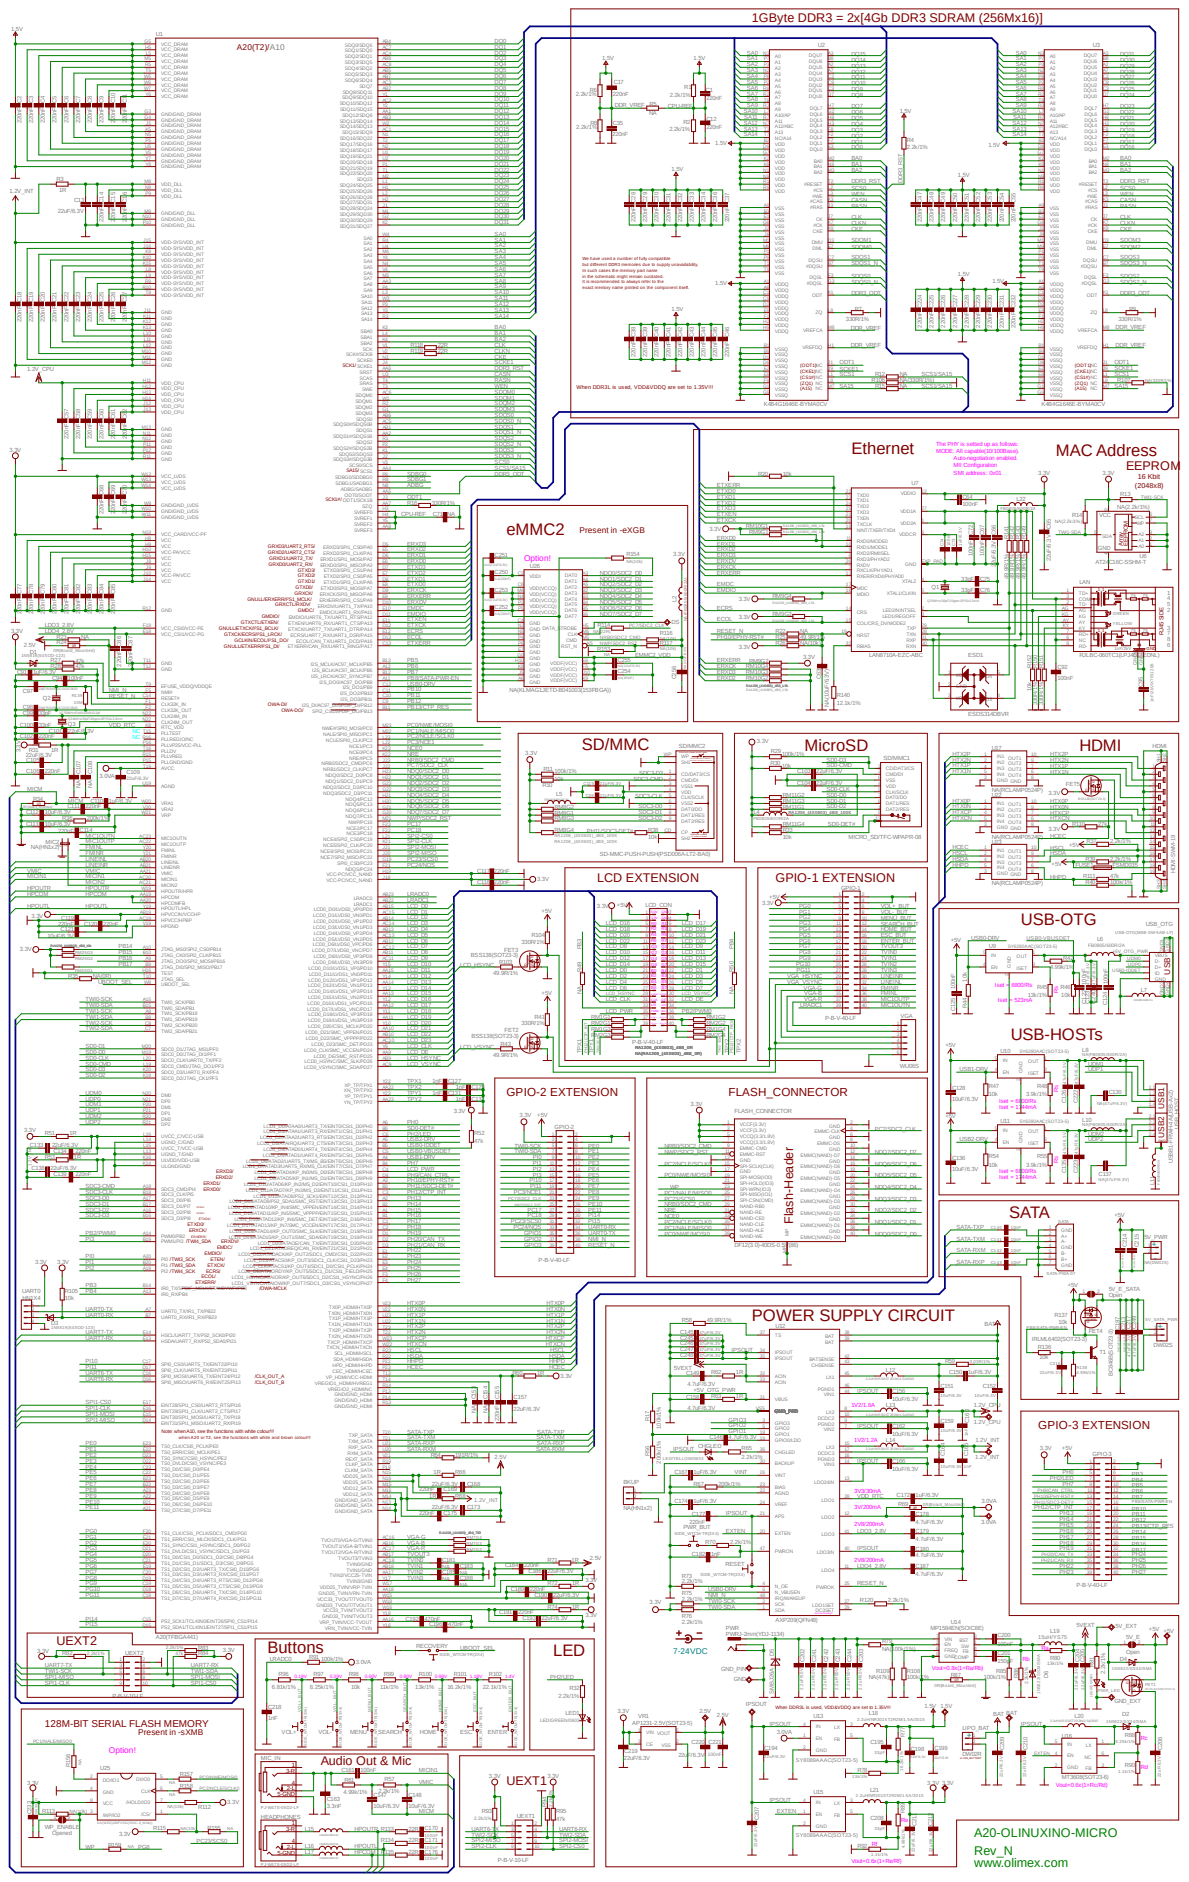
[picture p168: page 1]

The PHY is setted up as follows:
MODE: All capable(10/100Base).
Auto-negotiation enabled.
MII Configuration
SMI address: 0x01

TD+ 1
TD- 2 COM 3 AG AG | GREEN YELLOW

SD-MMC-PUSH-PUSH(PSD006A-LT2-BA0)
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
