OLIMEX/OLINUXINO/HARDWARE/Lime2-SATA/Lime2-SATA_RevA/Lime2-SATA_RevA.pdf

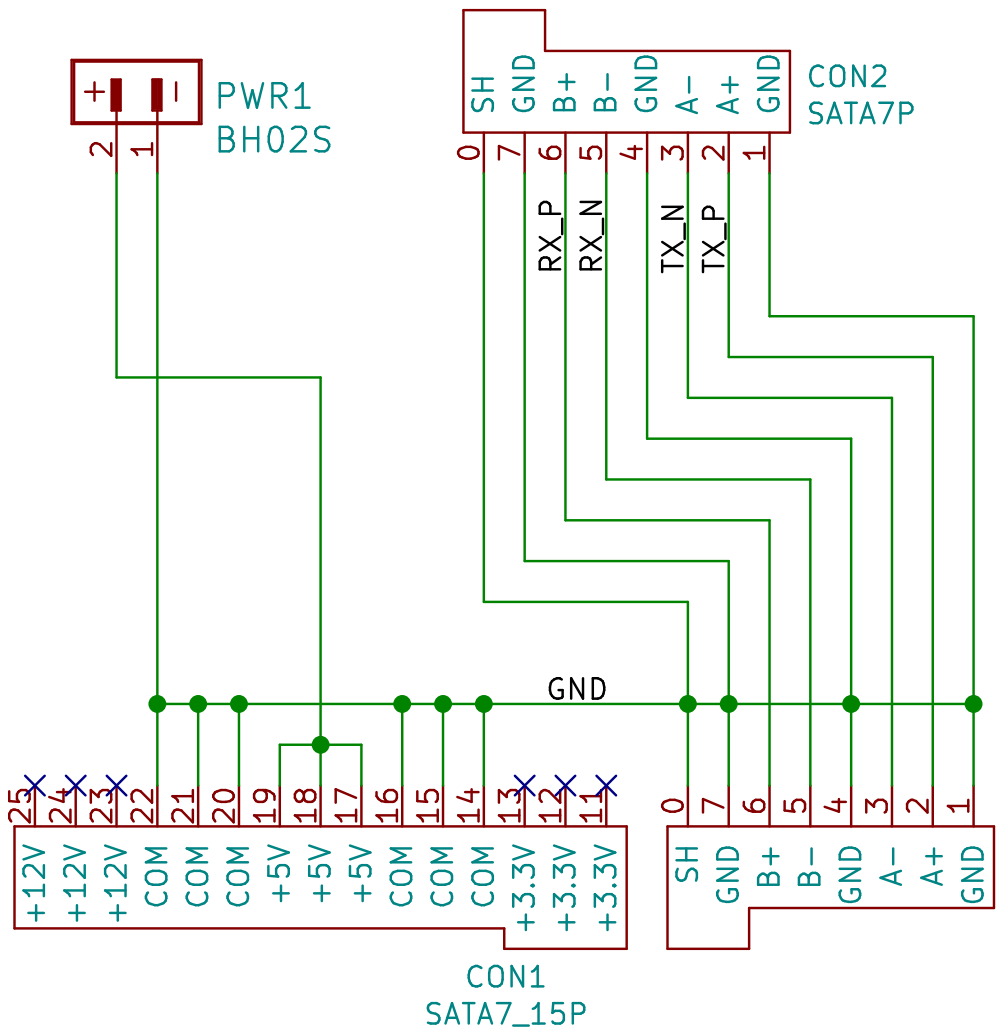
[picture p169: page 1]
