OLIMEX/OLINUXINO/HARDWARE/A10-OLinuXino-LIME/1. Latest hardware revision/A20-OLinuXino-Lime_Rev_I1.pdf

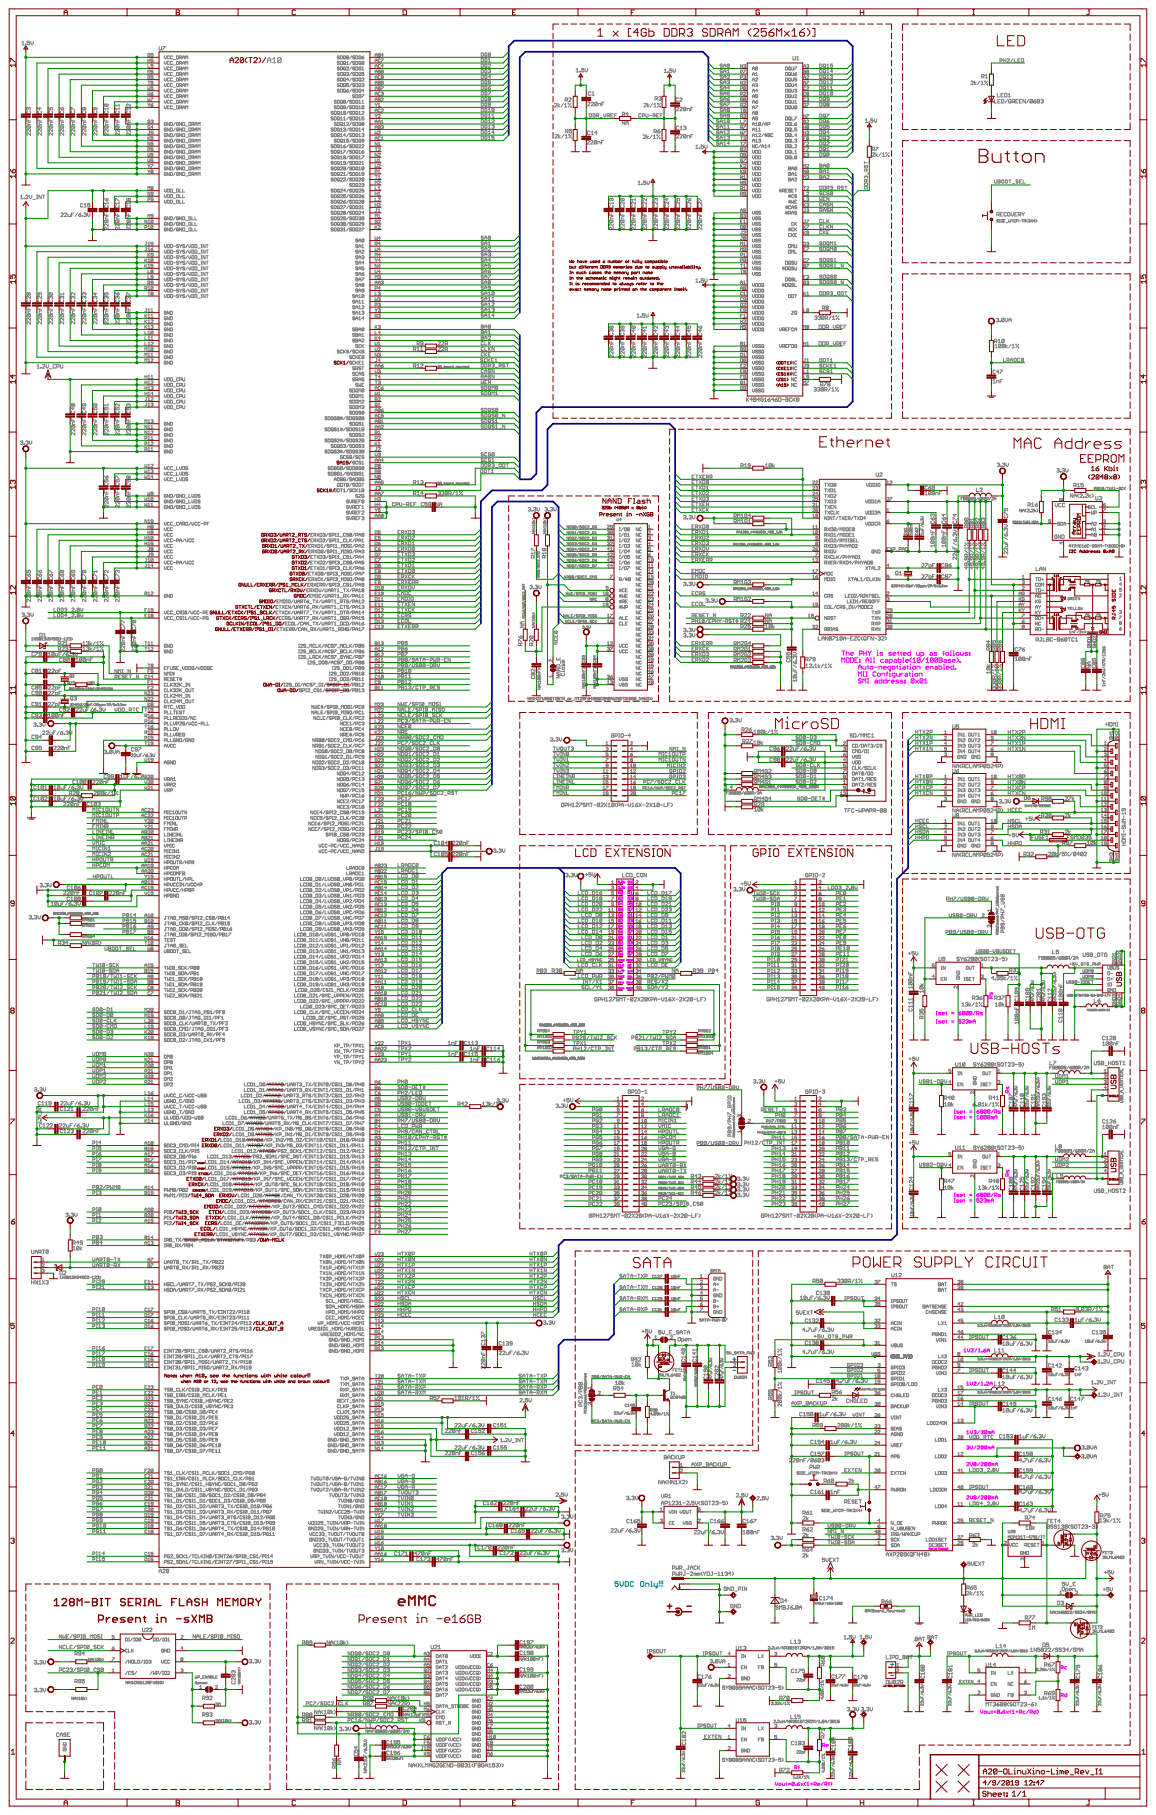
[picture p170: page 1]
