OLIMEX/OLINUXINO/HARDWARE/A10-OLinuXino-LIME/1. Latest hardware revision/A20-OLinuXino-Lime_Rev_I1_bom.pdf

A20-OLinuXino-Lime_Rev_I1_bom | 12/12/2018

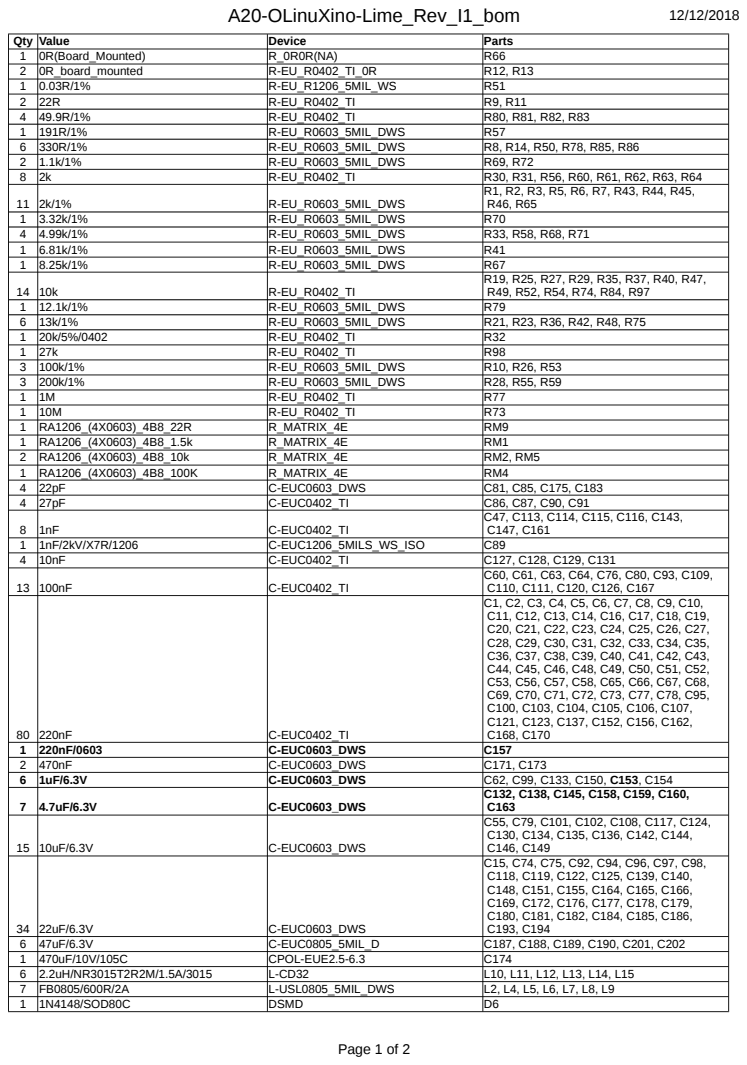
[picture p171: page 1]

A20-OLinuXino-Lime_Rev_I1_bom | 12/12/2018

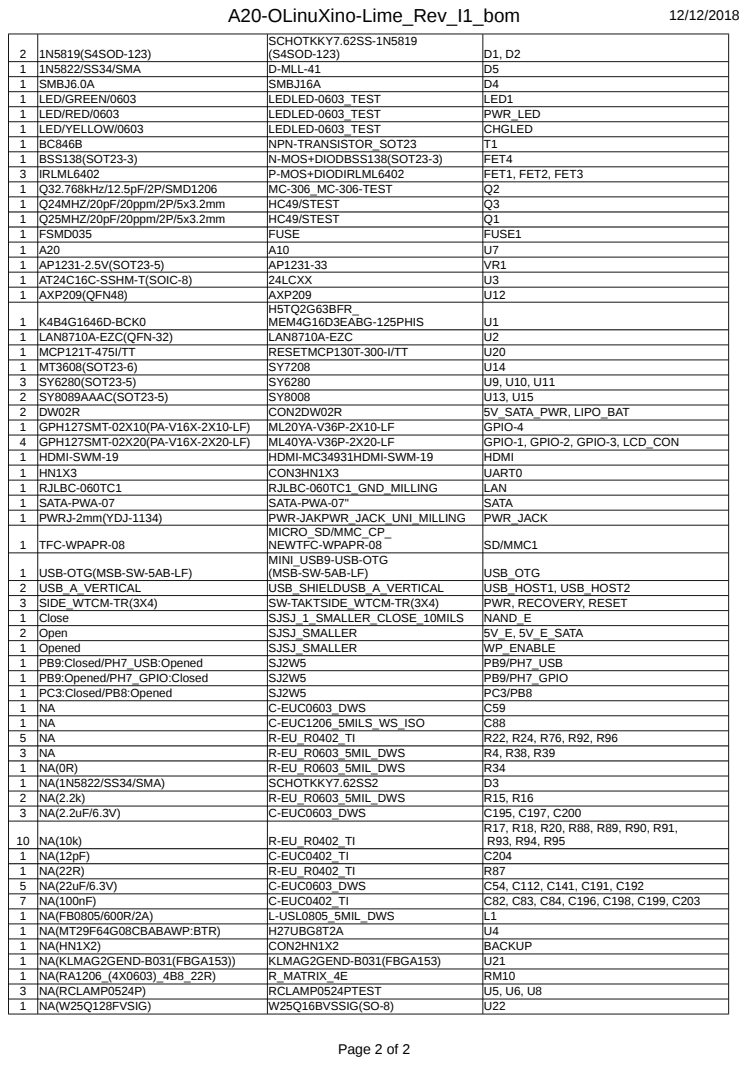
[picture p172: page 2]
