OLIMEX/OLINUXINO/HARDWARE/A33-OLinuXino/1. Latest hardware revision/A33-OLinuXino_Rev_C_n8GB_bom.pdf

A33-OLinuXino_Rev_C_n8GB_bom | 06/01/2018

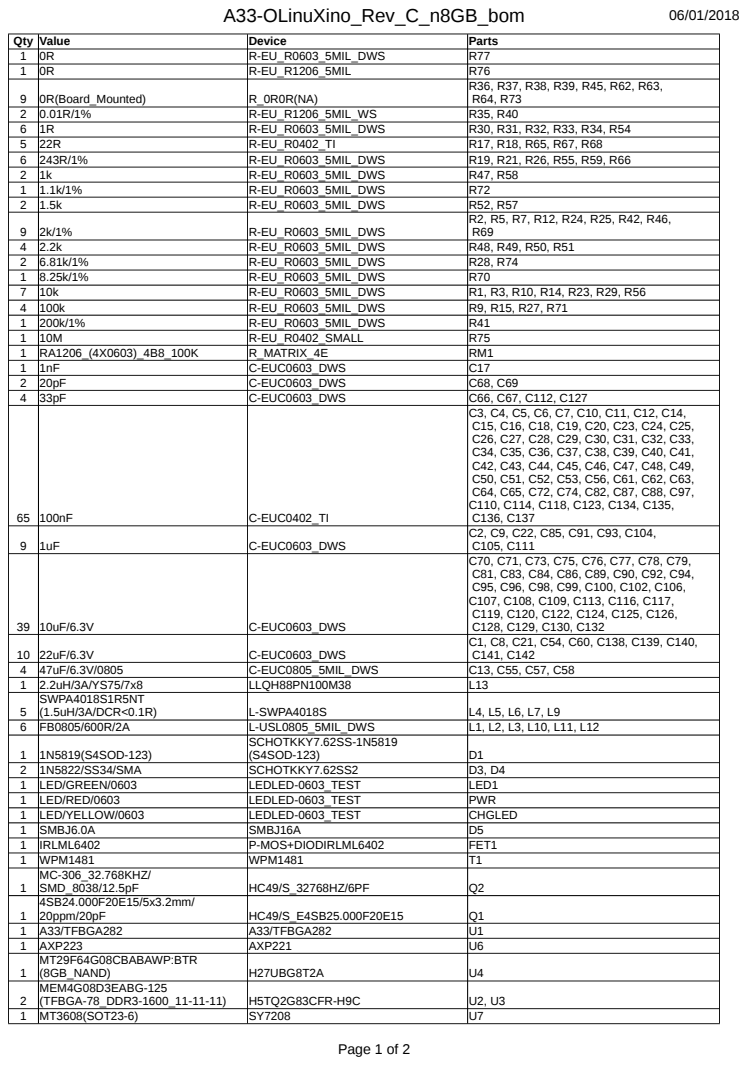
[picture p173: page 1]

A33-OLinuXino_Rev_C_n8GB_bom | 06/01/2018

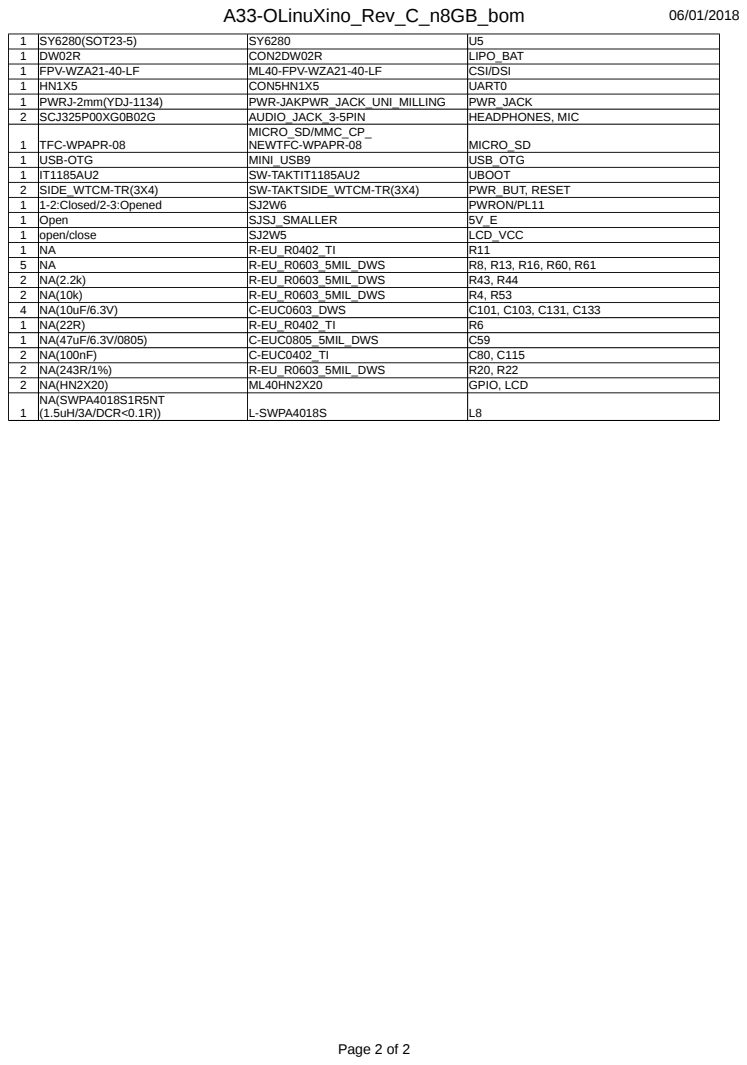
[picture p174: page 2]
