OLIMEX/OLINUXINO/HARDWARE/RT5350F/RT5350F-OLinuXino-EVB/RT5350F_OLinuXino_EVB_Rev_B.pdf

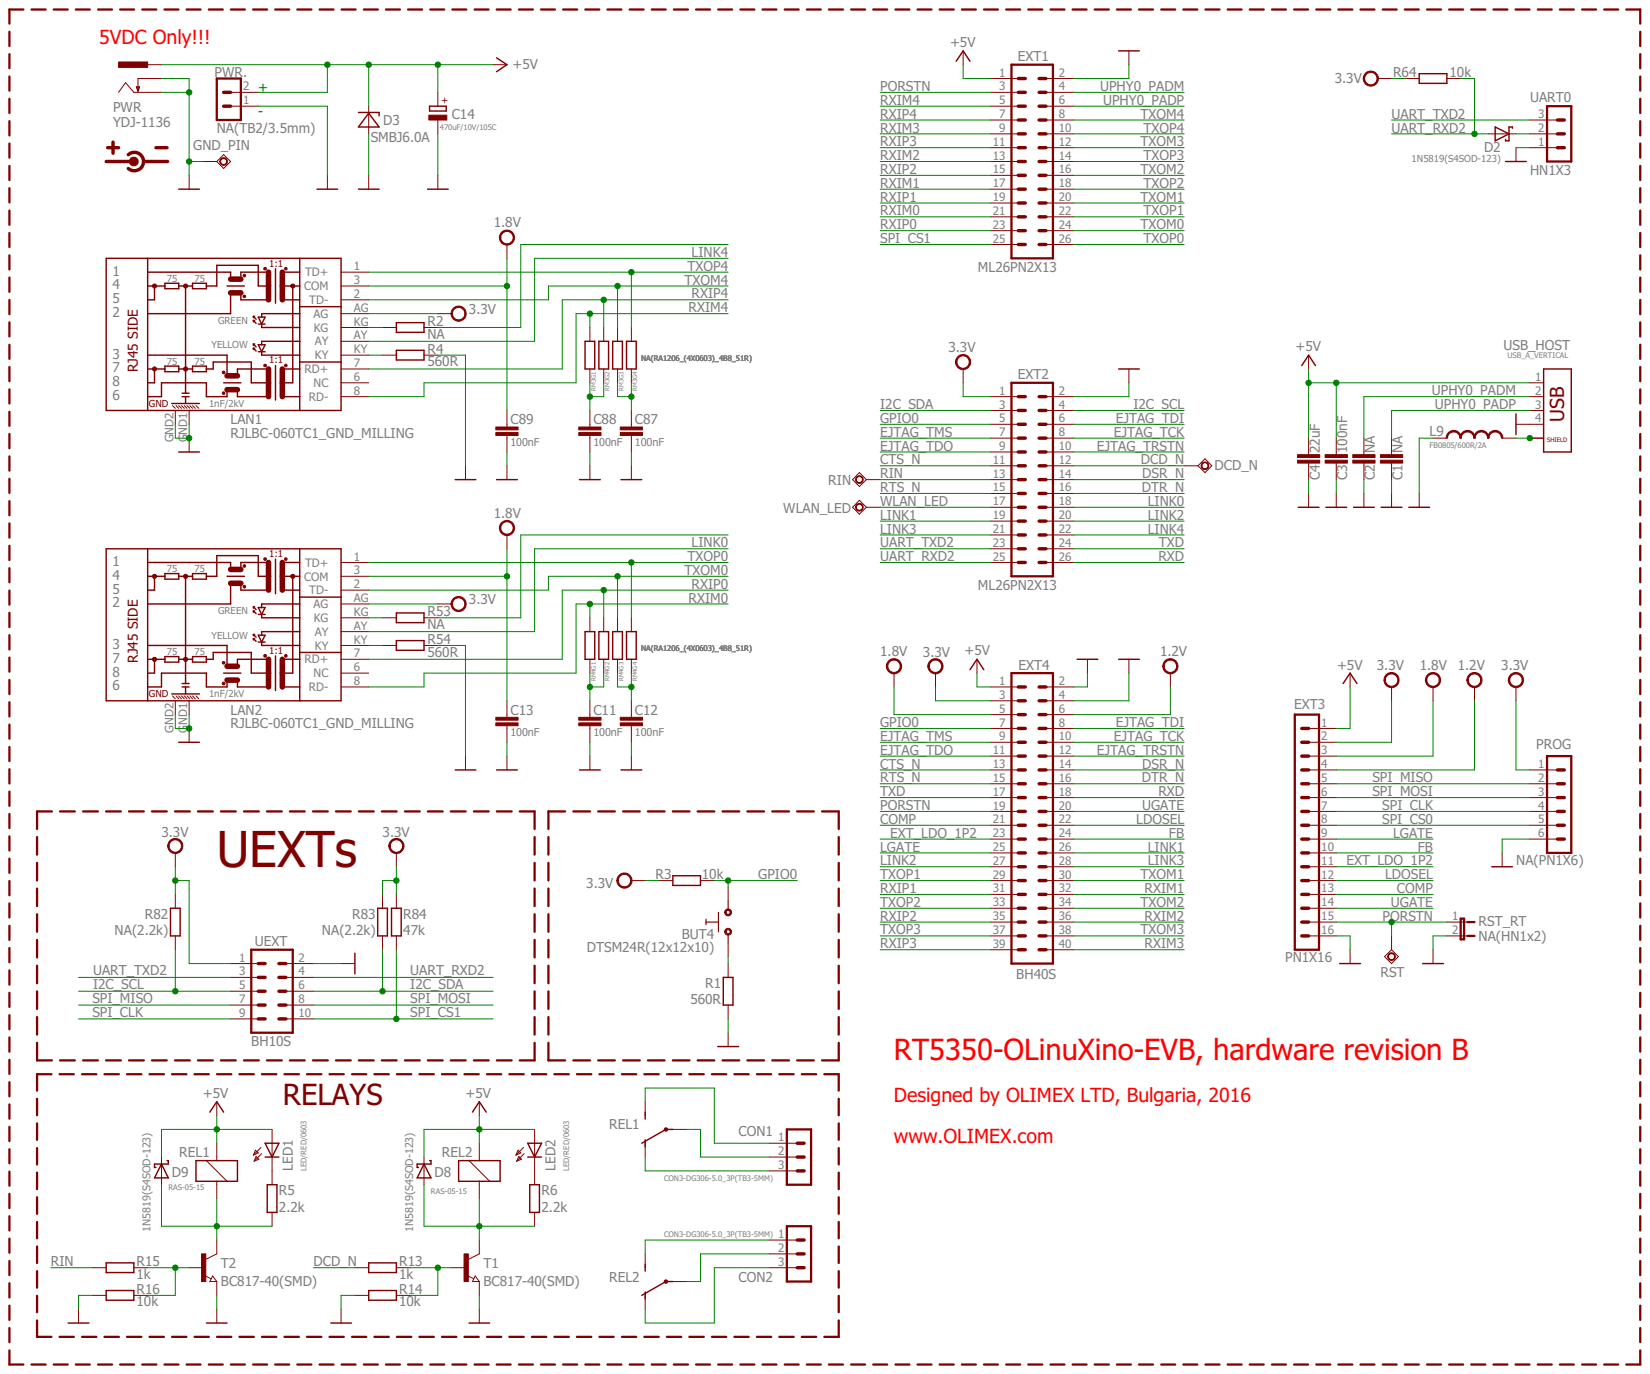
[picture p175: page 1]

RT5350-OLinuXino-EVB, hardware revision B

Designed by OLIMEX LTD, Bulgaria, 2016
