OLIMEX/OLINUXINO/HARDWARE/LCDs/A13-LCD10TS/A13-LCD10TS_sch.pdf

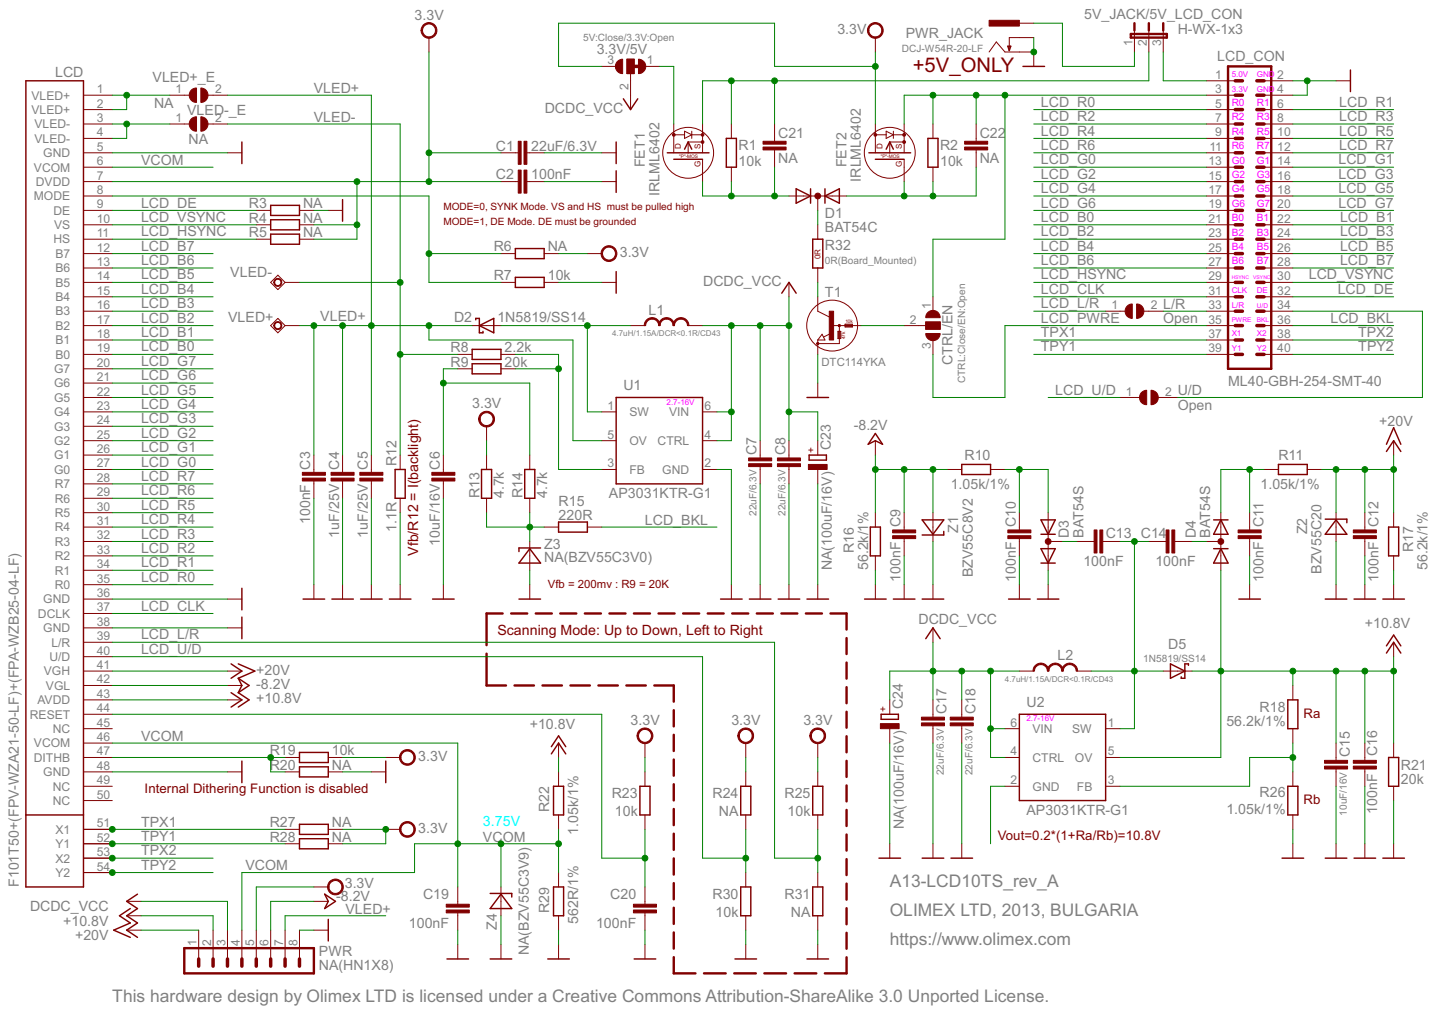
[picture p176: page 1]

7 MODE
8 DE 9 VS

MODE=0, SYNK Mode. VS and HS must be pulled high MODE=1, DE Mode. DE must be grounded

CTRL:Close/EN:Open

F101T50+(FPV-WZA21-50-LF)+(FPA-WZB25-04-LF)

Scanning Mode: Up to Down, Left to Right

Internal Dithering Function is disabled

A13-LCD10TS_rev_A
OLIMEX LTD, 2013, BULGARIA
https://www.olimex.com

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
