OLIMEX/OLINUXINO/HARDWARE/A10-OLinuXino-LIME/3. Templates and more/A10-OLinuXino-LIME revision B SHIELD TEMPLATE KiCAD/A10-OLinuXino-LIME revision B SHIELD TEMPLATE KiCAD.pdf

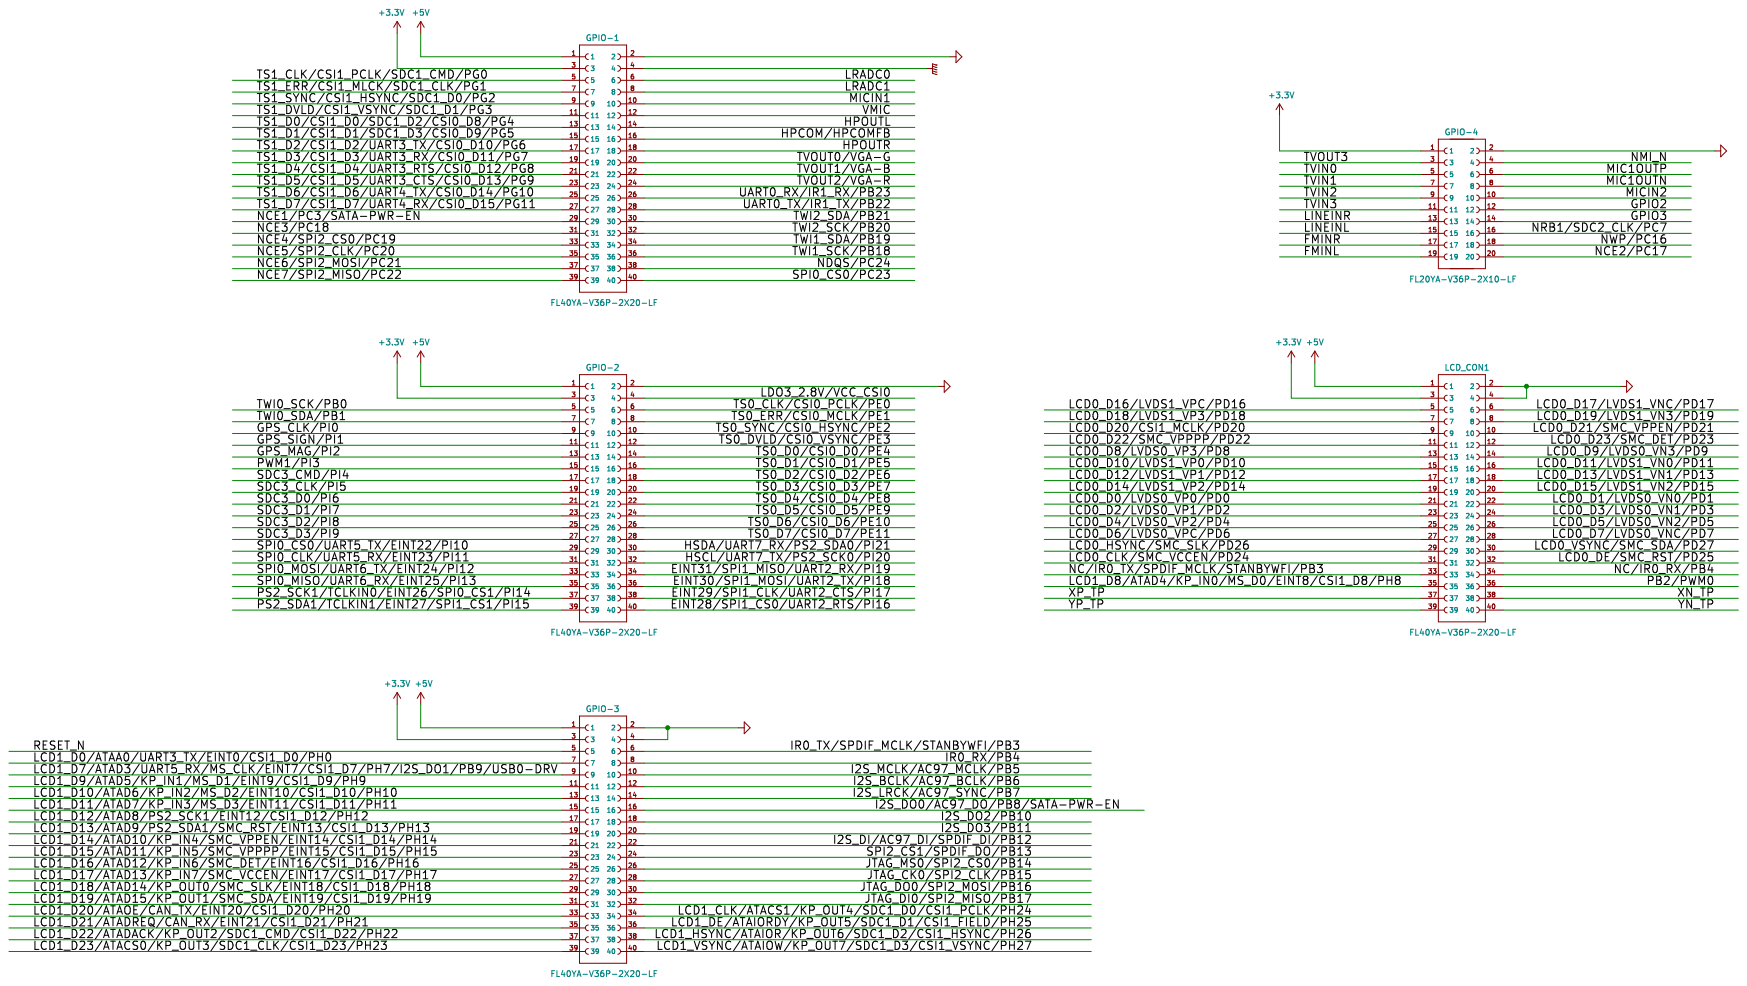
[picture p177: page 1]
