OLIMEX/OLINUXINO/HARDWARE/STMP157-OLinuXino-LIME2/1. Latest hardware revision/STMP157-OLinuXino-LIME2_Rev_B1/STMP157-OLinuXino-LIME2H_EXT_Rev_B1.pdf

STMP157-OLinuXino-LIME2H_EXT_Rev_B1 | 08/26/2021

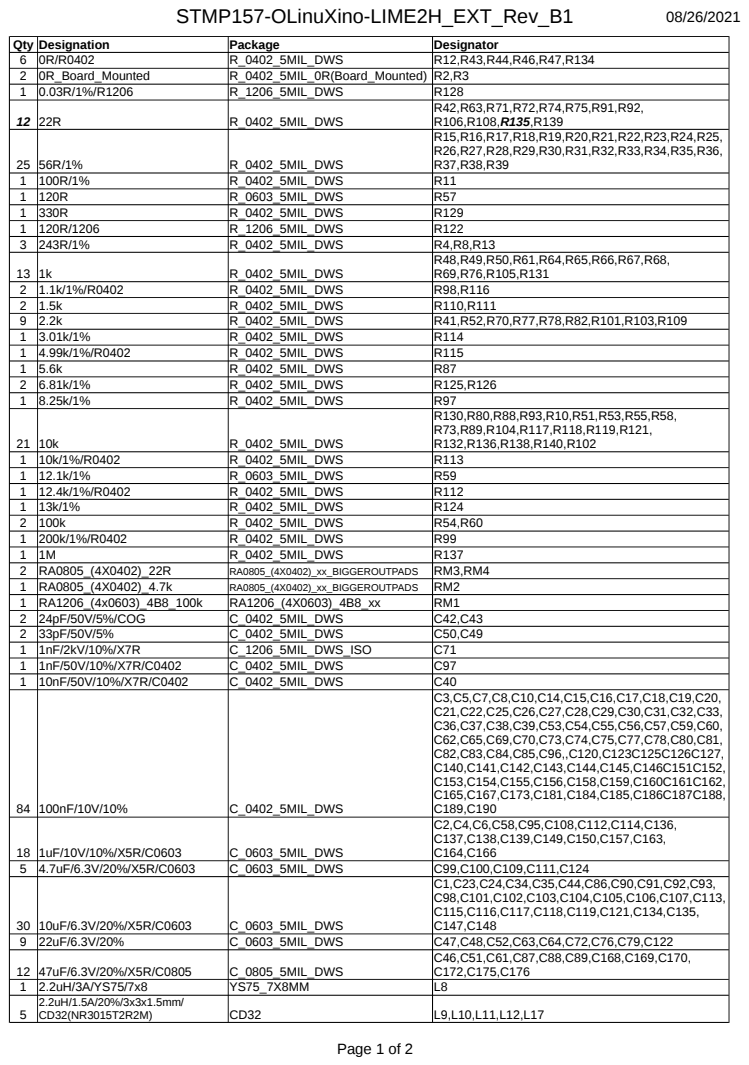
[picture p178: page 1]

STMP157-OLinuXino-LIME2H_EXT_Rev_B1 | 08/26/2021

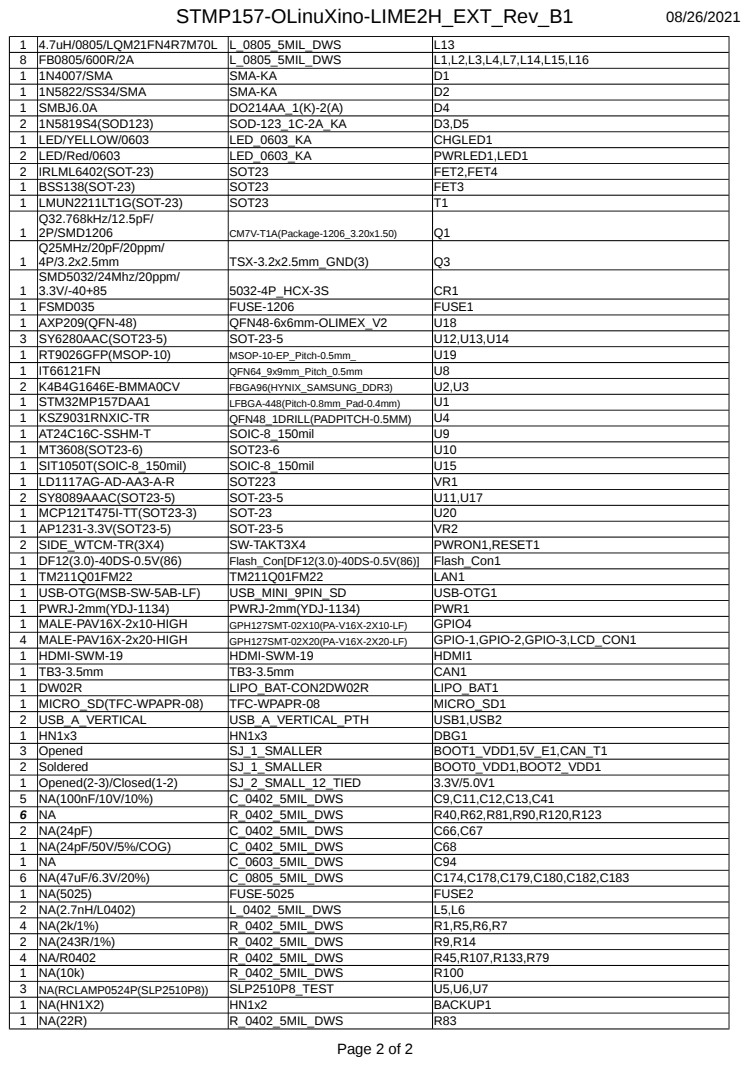
[picture p179: page 2]
