OLIMEX/OLINUXINO/HARDWARE/LCDs/LCD-OLinuXino-4.3TS/Hardware revision D/LCD-OLINUXINO-4.3''TS_Rev_D.pdf

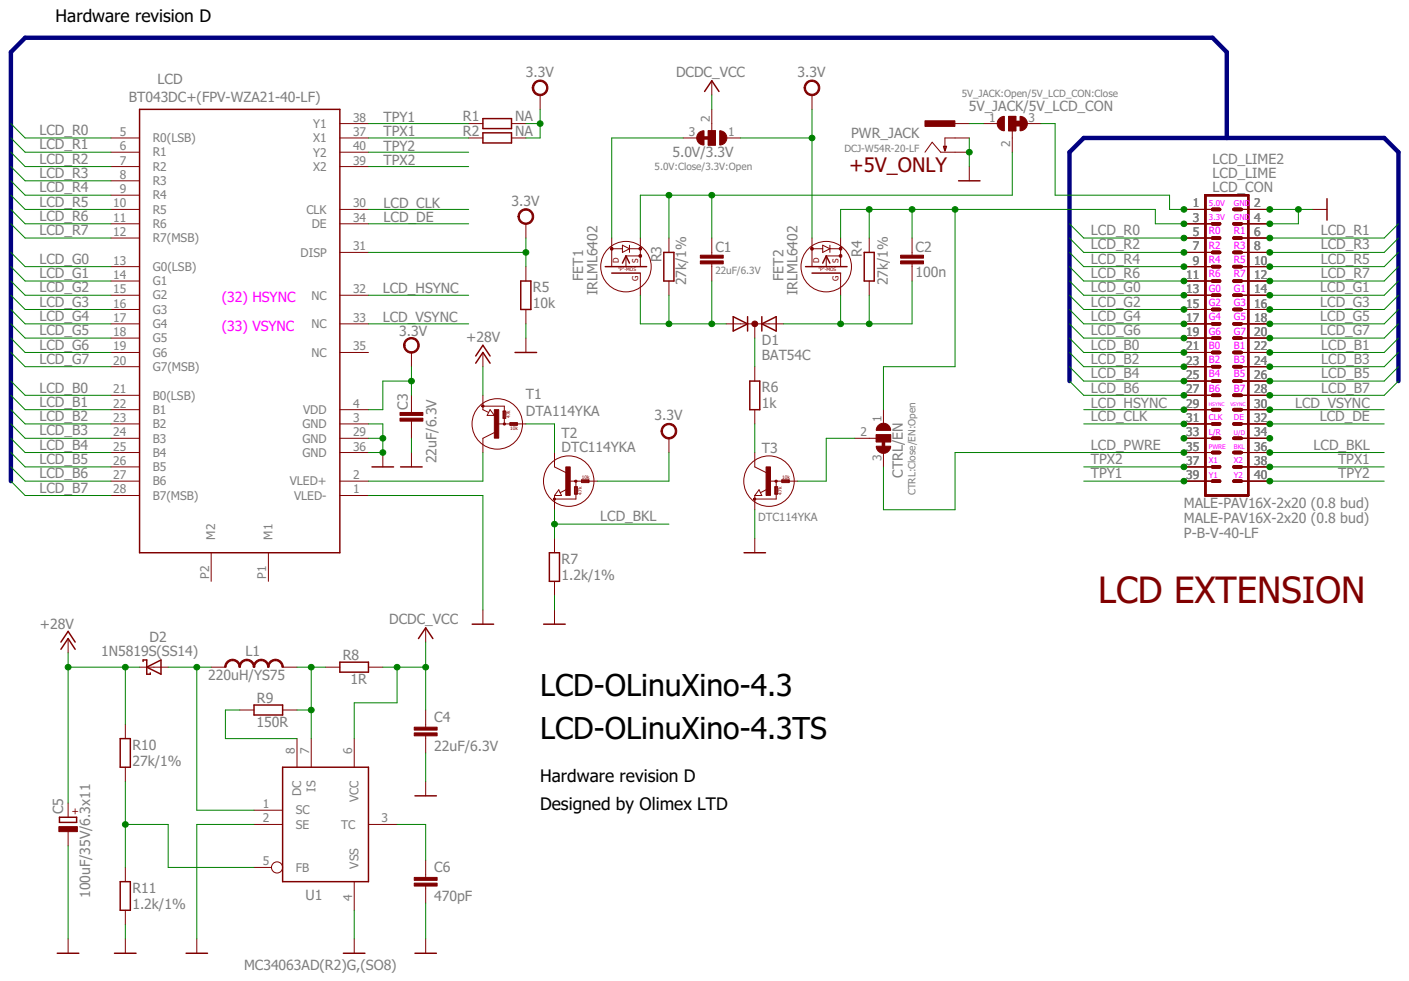
[picture p180: page 1]

CTRL:Close/EN:Open

Hardware revision D
Designed by Olimex LTD
