OLIMEX/OLINUXINO/HARDWARE/LCDs/LCD-OLinuXino-4.3TS/Hardware revision D/LCD-OLINUXINO-4.3TS_Rev_D_bom.pdf

LCD-OLINUXINO-4.3TS_Rev_D_bom | 03/18/2019

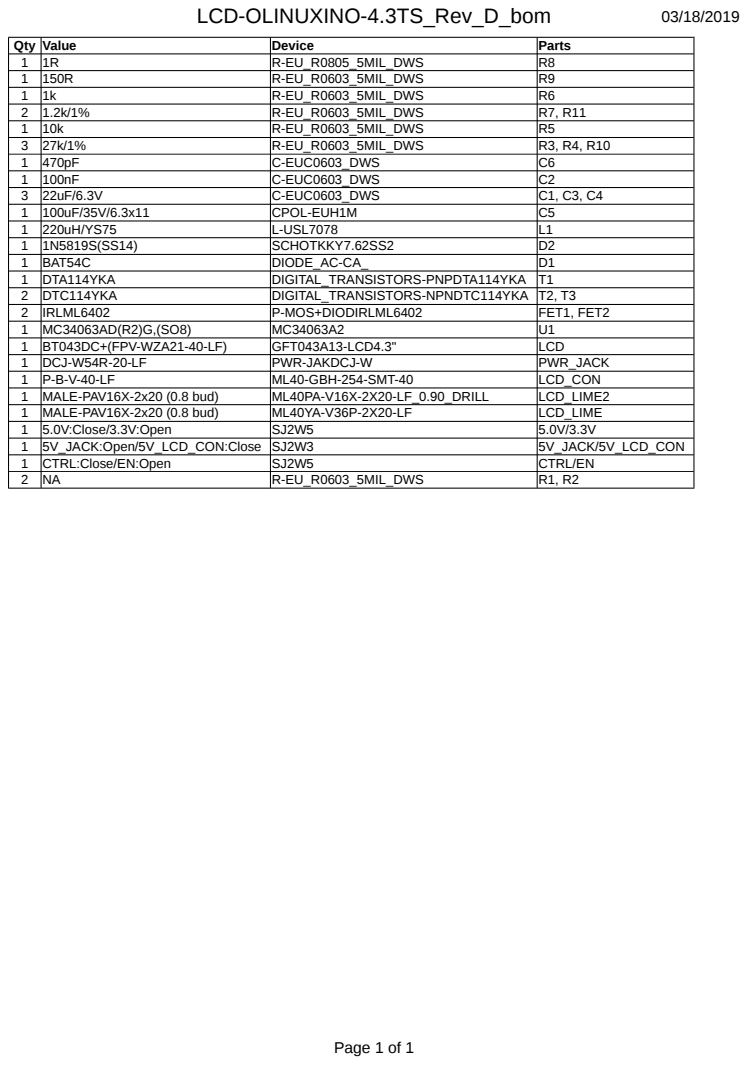
[picture p181: page 1]
