OLIMEX/OLINUXINO/HARDWARE/A20-OLinuXino-LIME2/1. Latest hardware revision/Bills-of-materials/A20-OLinuXino-Lime2_Rev_L_1Ge4Gs16MB_bom.pdf

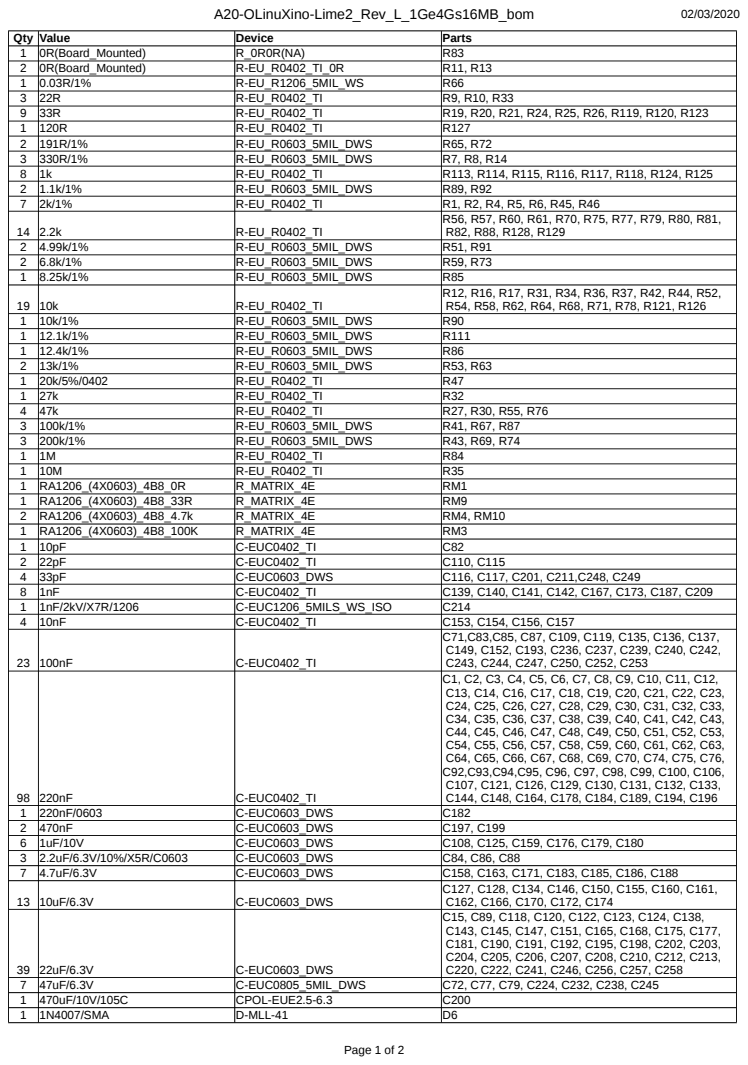
[picture p184: page 1]

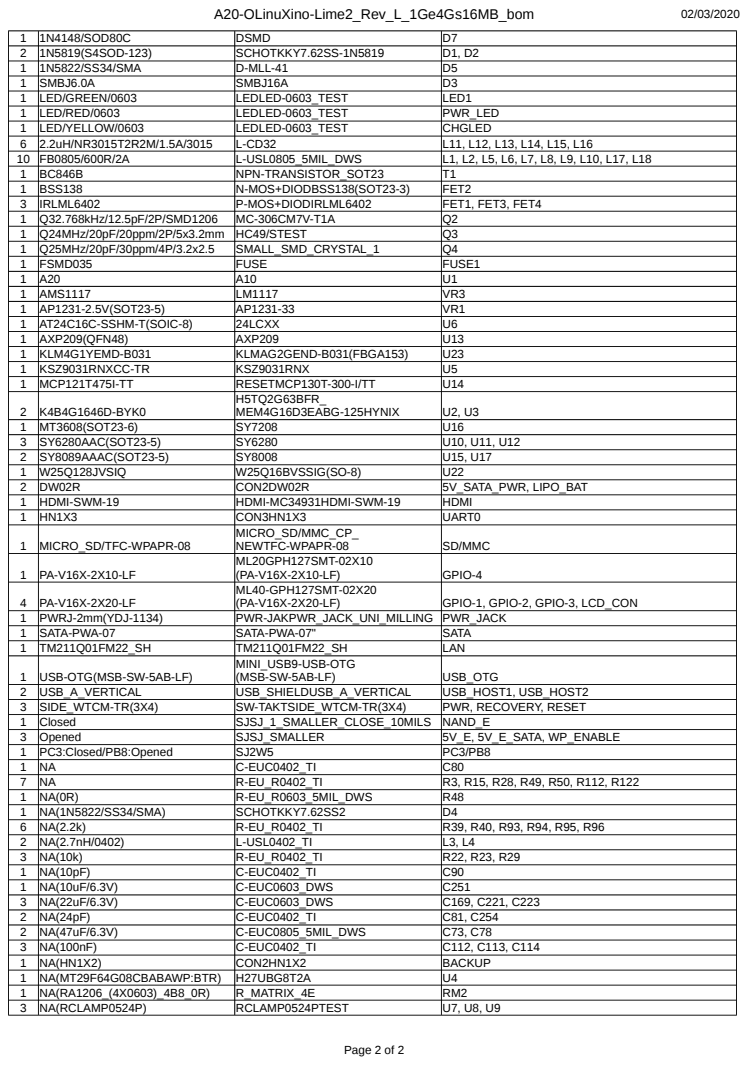
[picture p185: page 2]
