OLIMEX/OLINUXINO/HARDWARE/A20-OLinuXino-LIME2/1. Latest hardware revision/Bills-of-materials/A20-OLinuXino-Lime2_Rev_L_1Gs16M_bom.pdf

A20-OLinuXino-Lime2_Rev_L_1Gs16M_bom | 02/03/2020

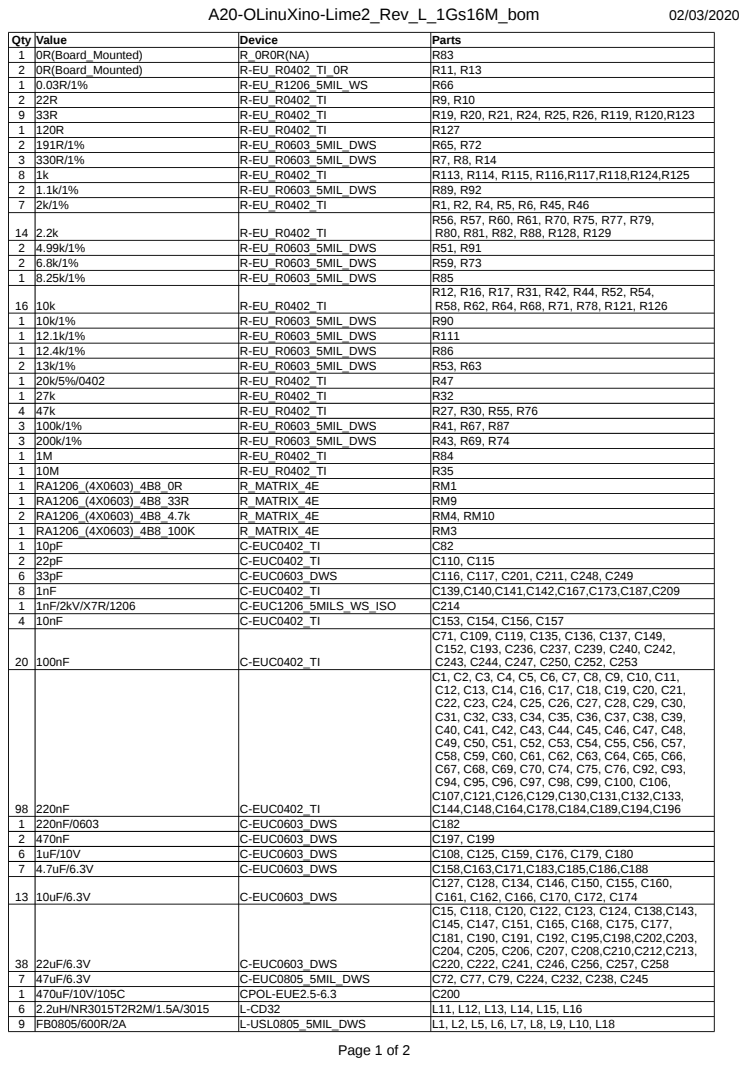
[picture p188: page 1]

A20-OLinuXino-Lime2_Rev_L_1Gs16M_bom | 02/03/2020

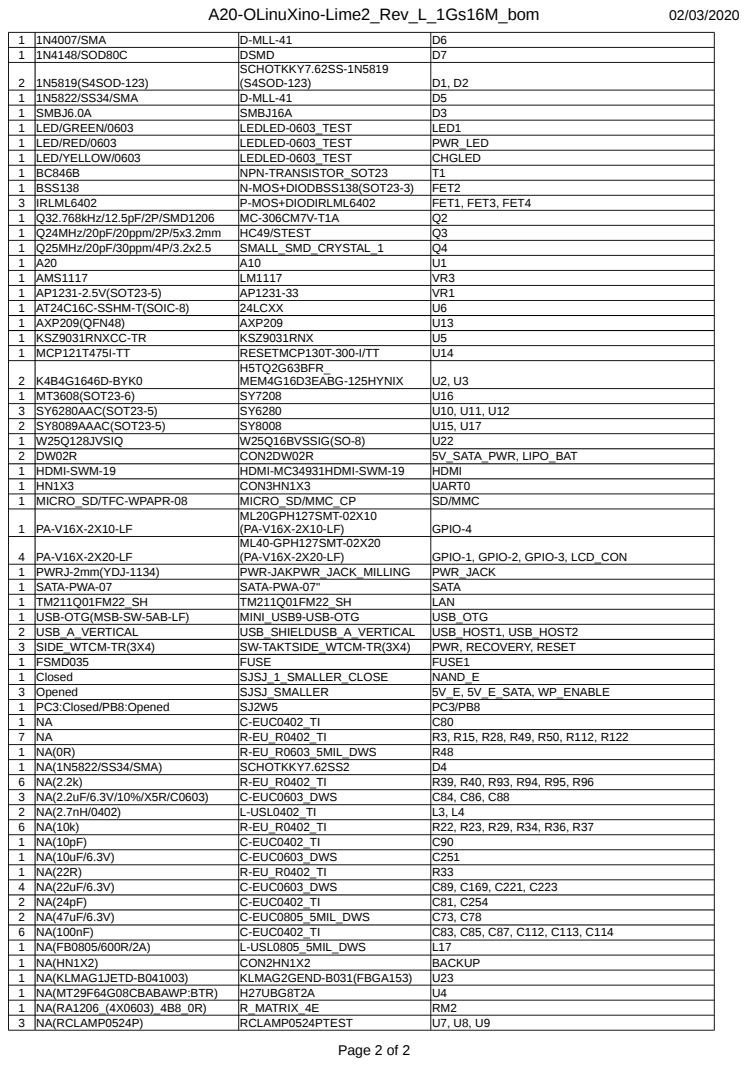
[picture p189: page 2]
