OLIMEX/OLINUXINO/HARDWARE/A20-OLinuXino-LIME2/1. Latest hardware revision/Bills-of-materials/T2-OLinuXino-Lime2_Rev_L_e8Gs16M_IND_bom.pdf

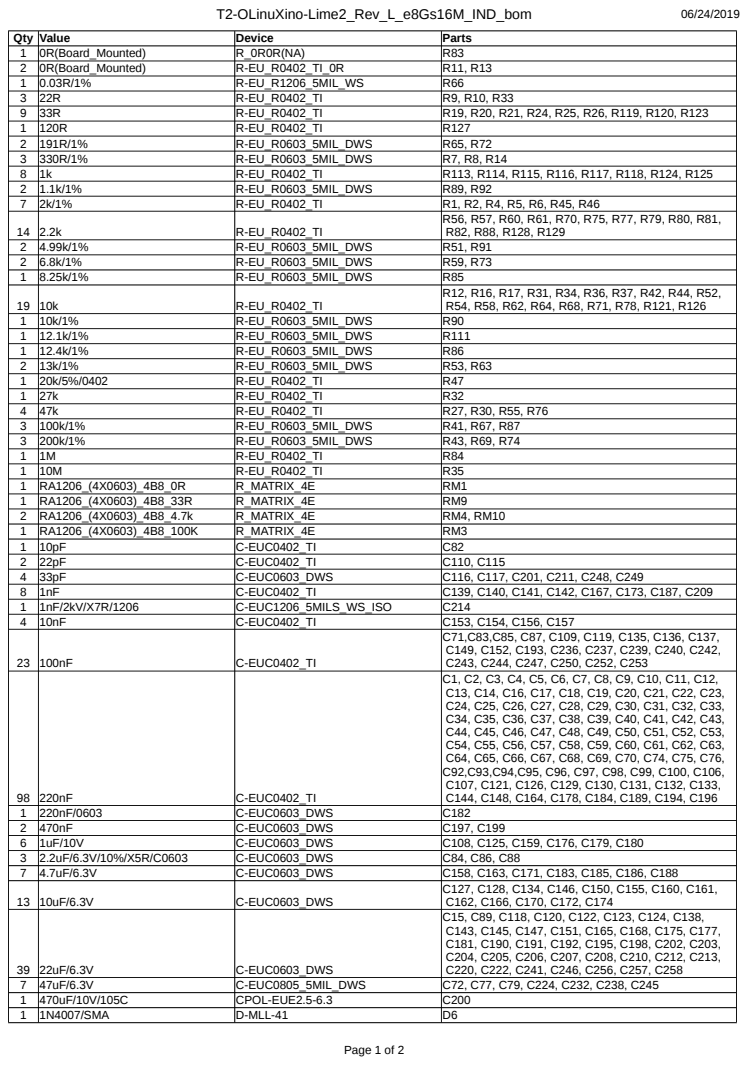
[picture p192: page 1]

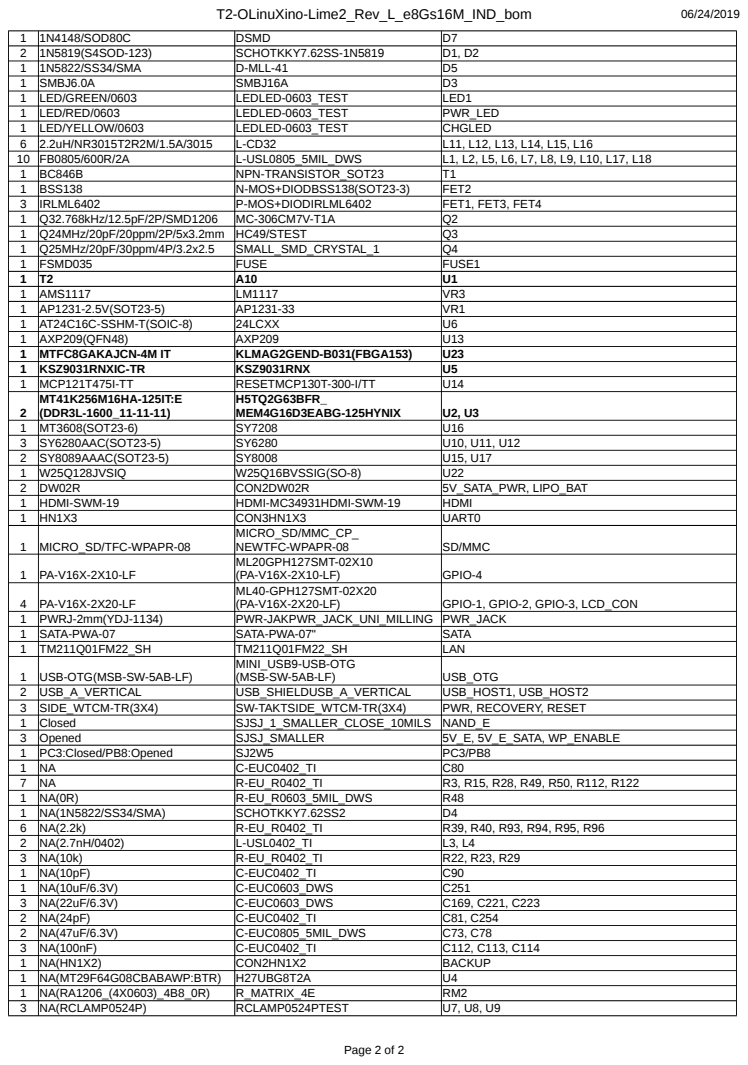
[picture p193: page 2]
