OLIMEX/OLINUXINO/HARDWARE/A20-OLinuXino-LIME2/1. Latest hardware revision/Bills-of-materials/T2-OLinuXino-Lime2_Rev_L_s16M_IND_bom.pdf

T2-OLinuXino-Lime2_Rev_L_s16M_IND_bom | 06/24/2019

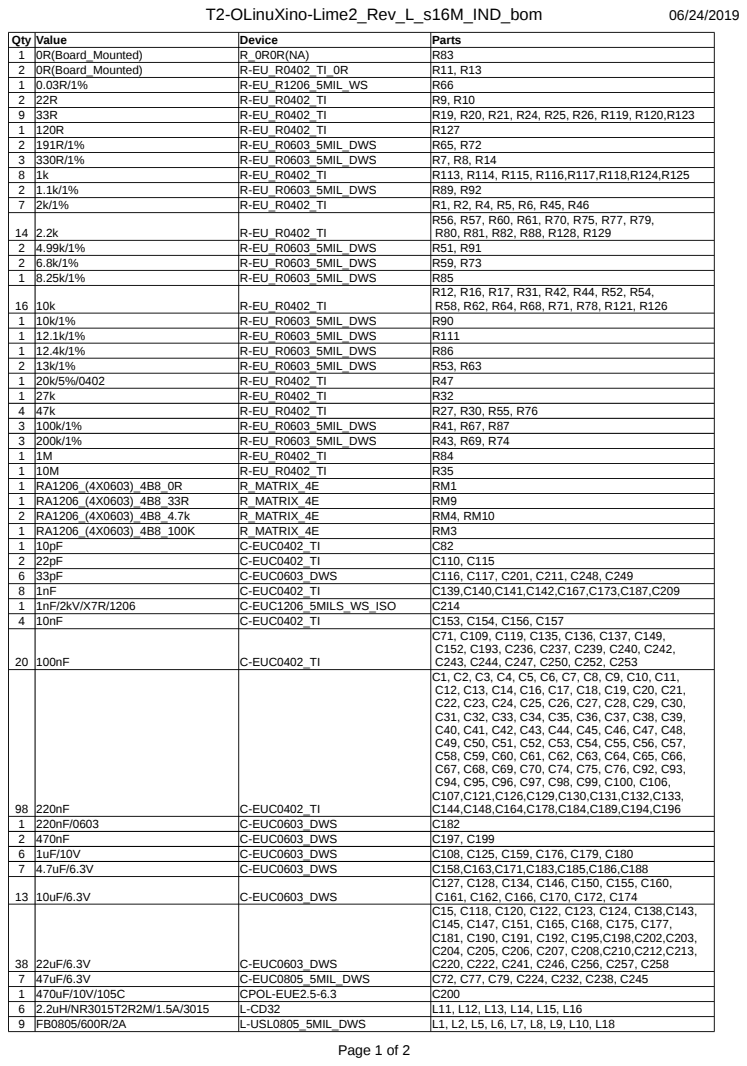
[picture p196: page 1]

T2-OLinuXino-Lime2_Rev_L_s16M_IND_bom | 06/24/2019

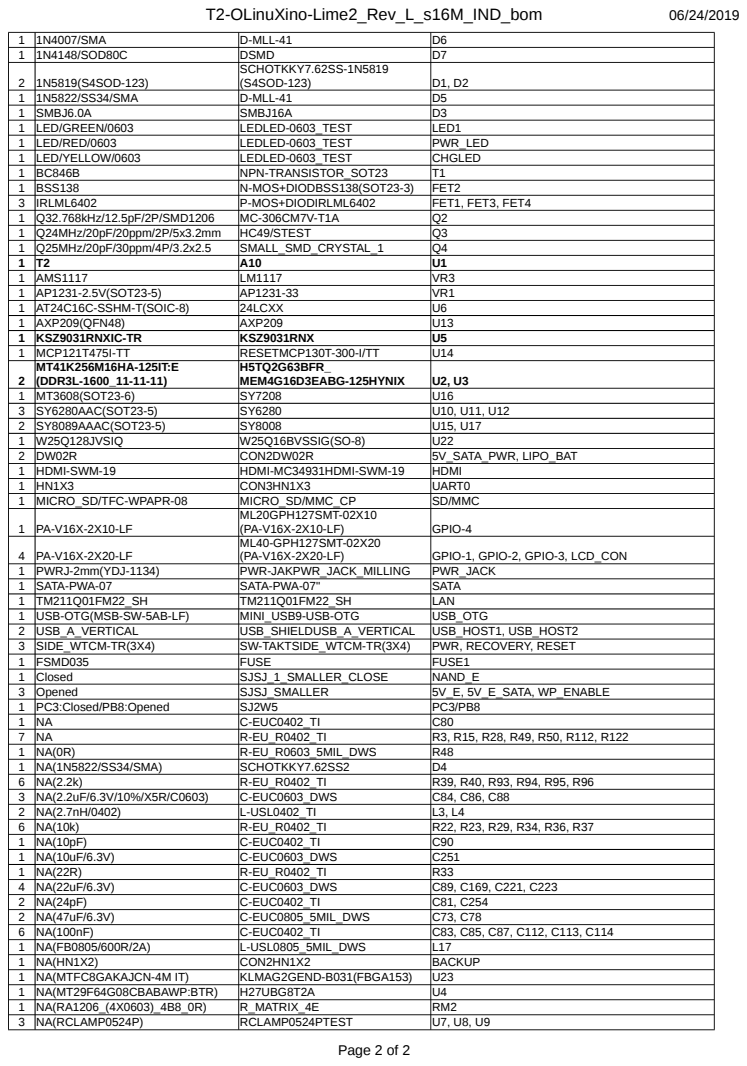
[picture p197: page 2]
