OLIMEX/OLINUXINO/HARDWARE/A13-OLinuXino/1. Latest hardware revision/A13-OLinuXino-WIFI hardware revision G2/A13-OLinuXino_WIFI_Rev_G2.pdf

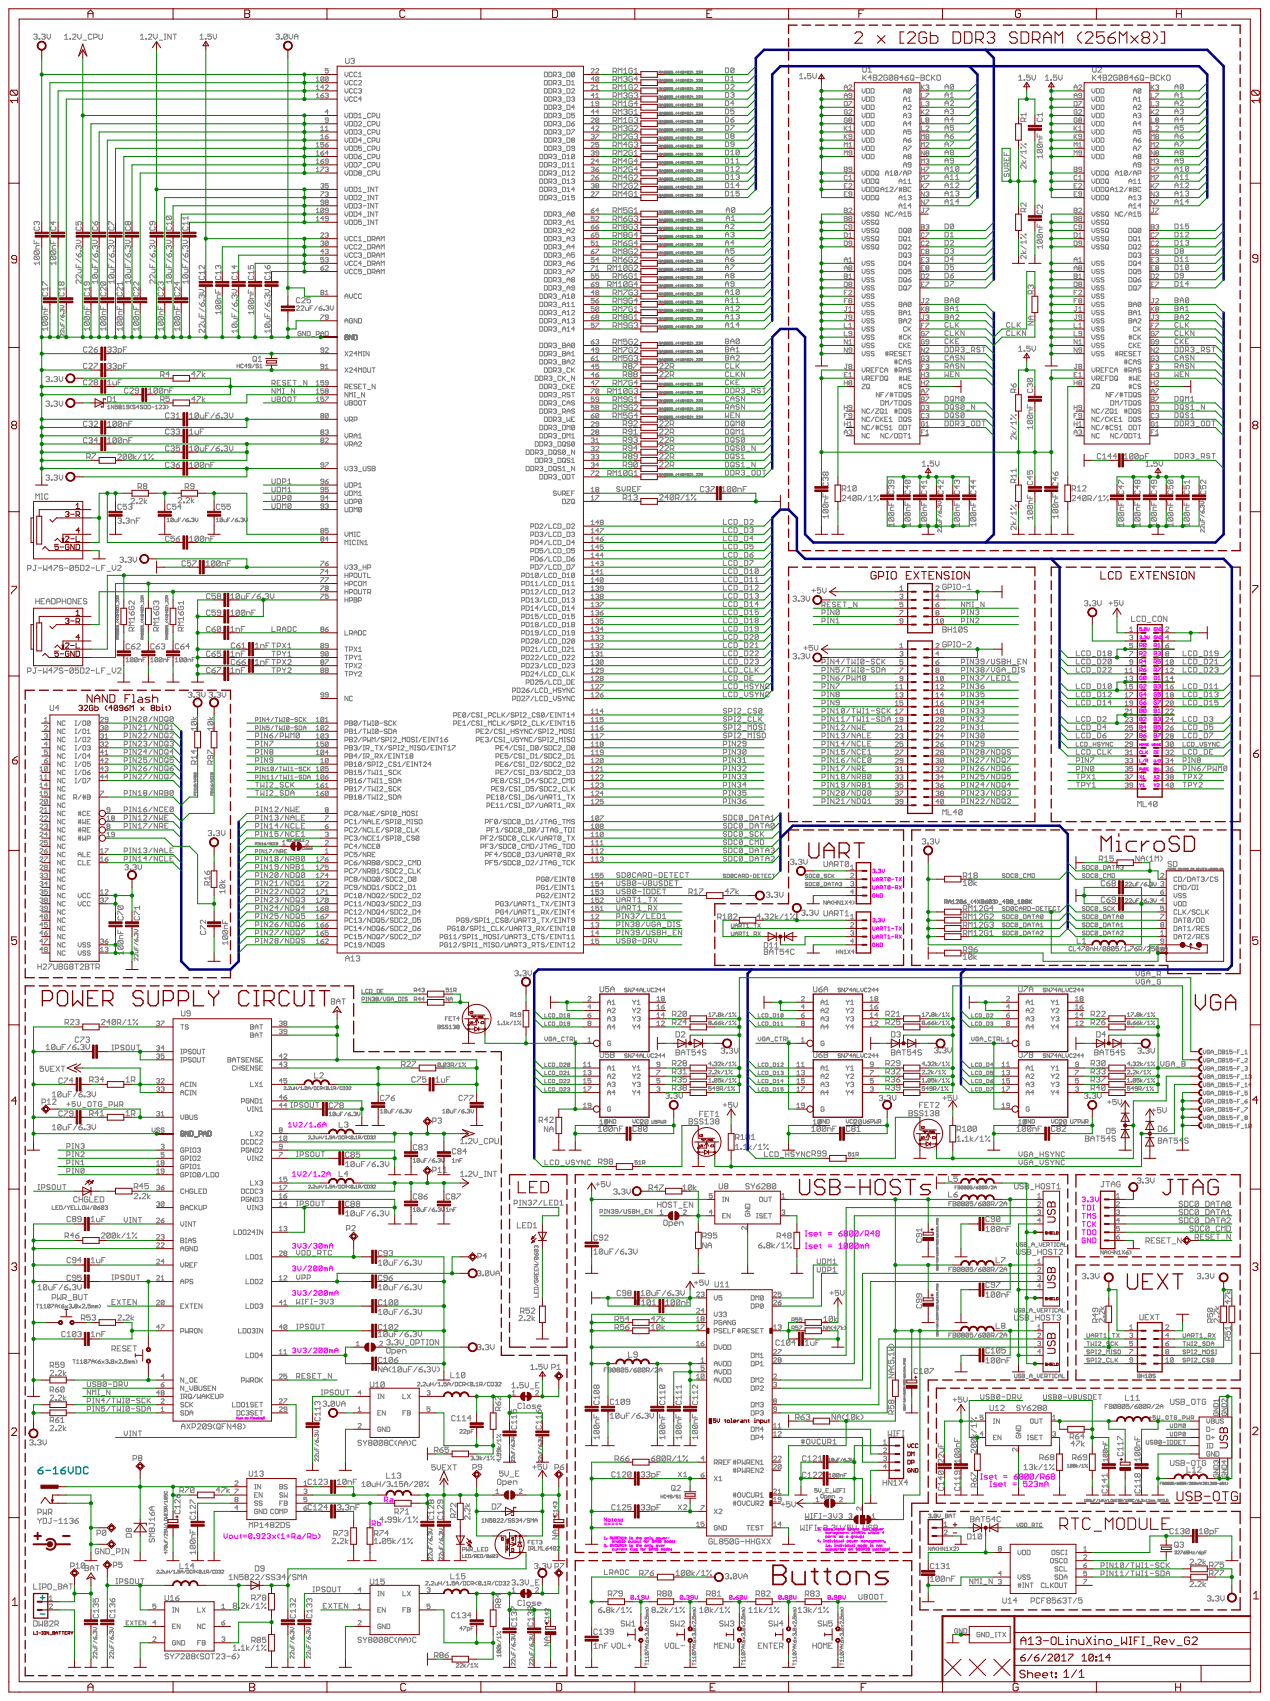
[picture p198: page 1]
