OLIMEX/OLINUXINO/HARDWARE/A13-OLinuXino/1. Latest hardware revision/A13-OLinuXino-WIFI hardware revision H/A13-OLinuXino_WIFI_Rev_H.pdf

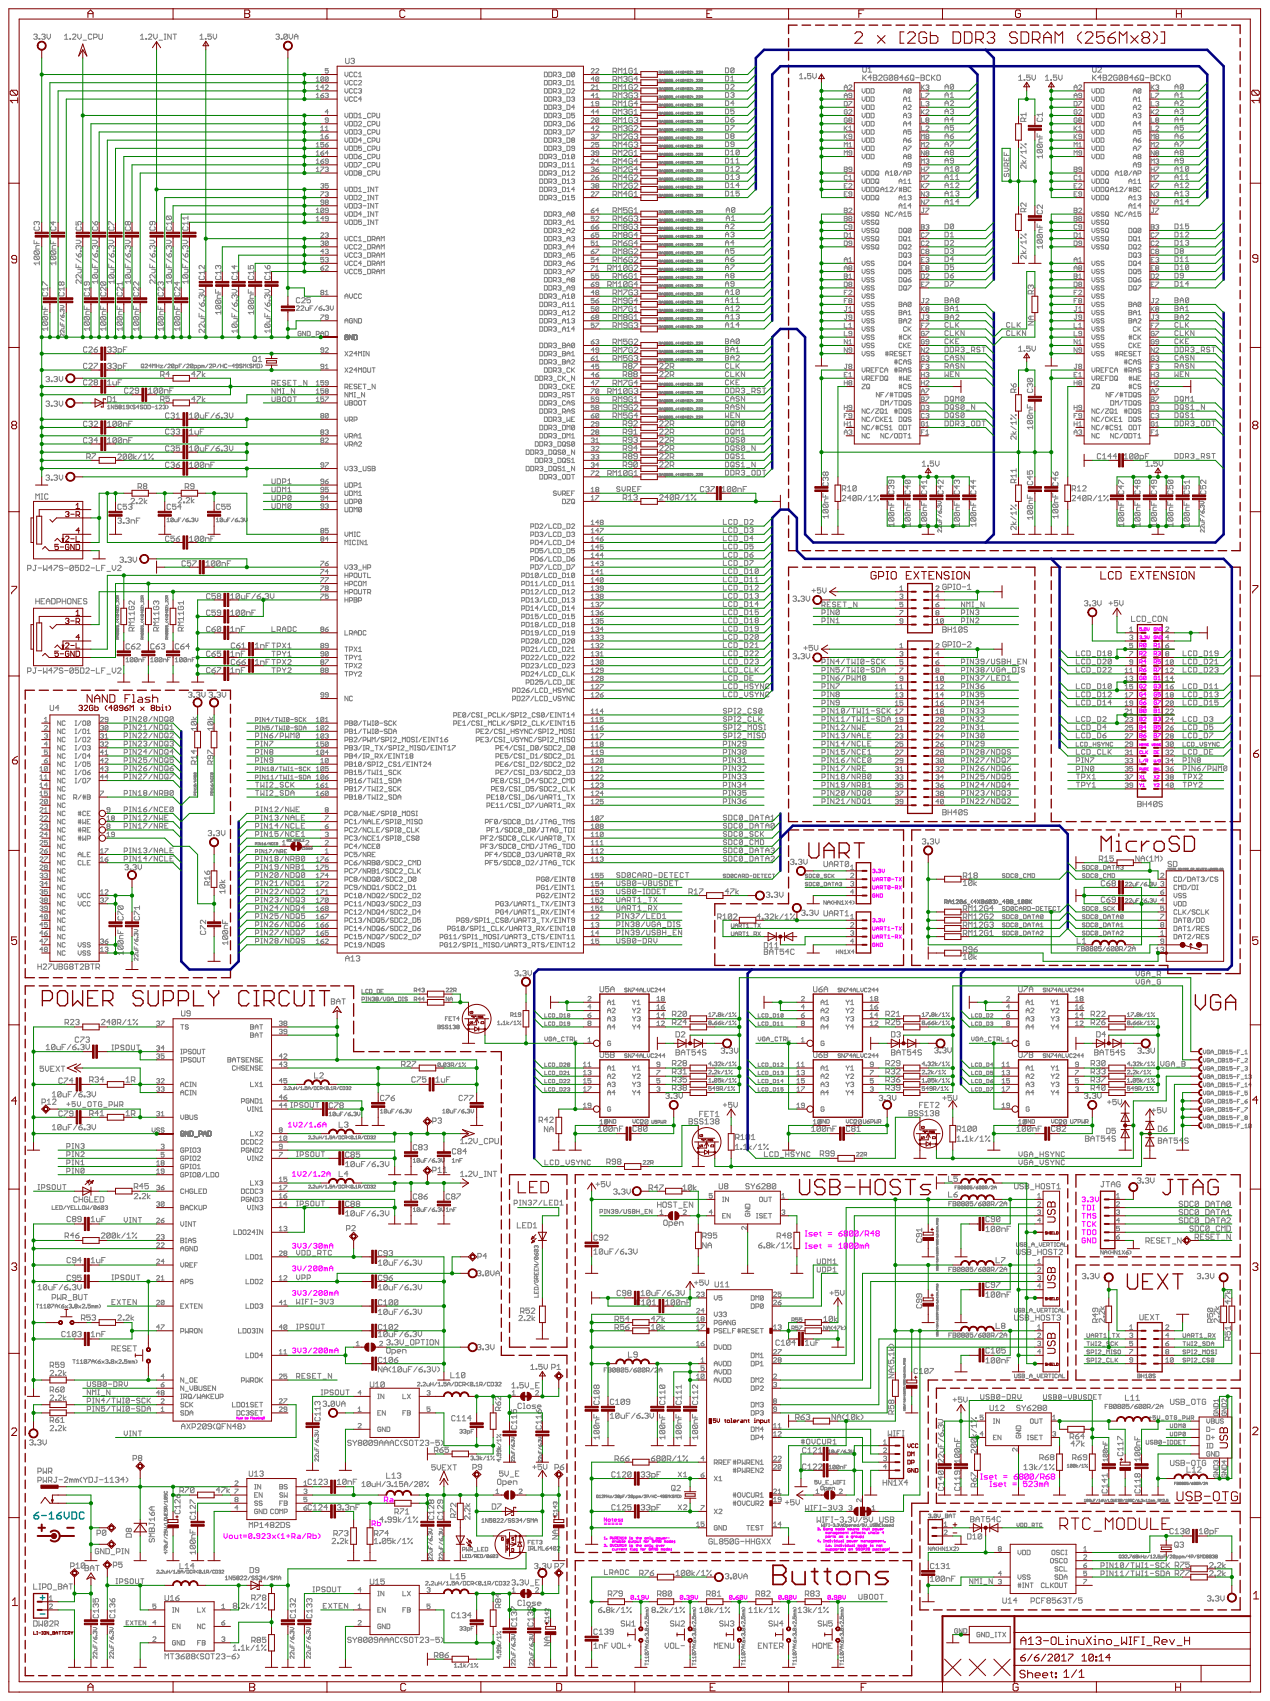
[picture p199: page 1]
