OLIMEX/OLINUXINO/HARDWARE/A10-OLinuXino-MICRO/A10-OLinuXino-MICRO hardware revision C/A10-A20-OLINUXINO-MICRO-4GB_Rev_C.sch

## EAGLE design HARDWARE/A10-OLinuXino-MICRO/A10-OLinuXino-MICRO hardware revision C/A10-A20-OLINUXINO-MICRO-4GB_Rev_C.sch (2013-08-23, an earlier design)

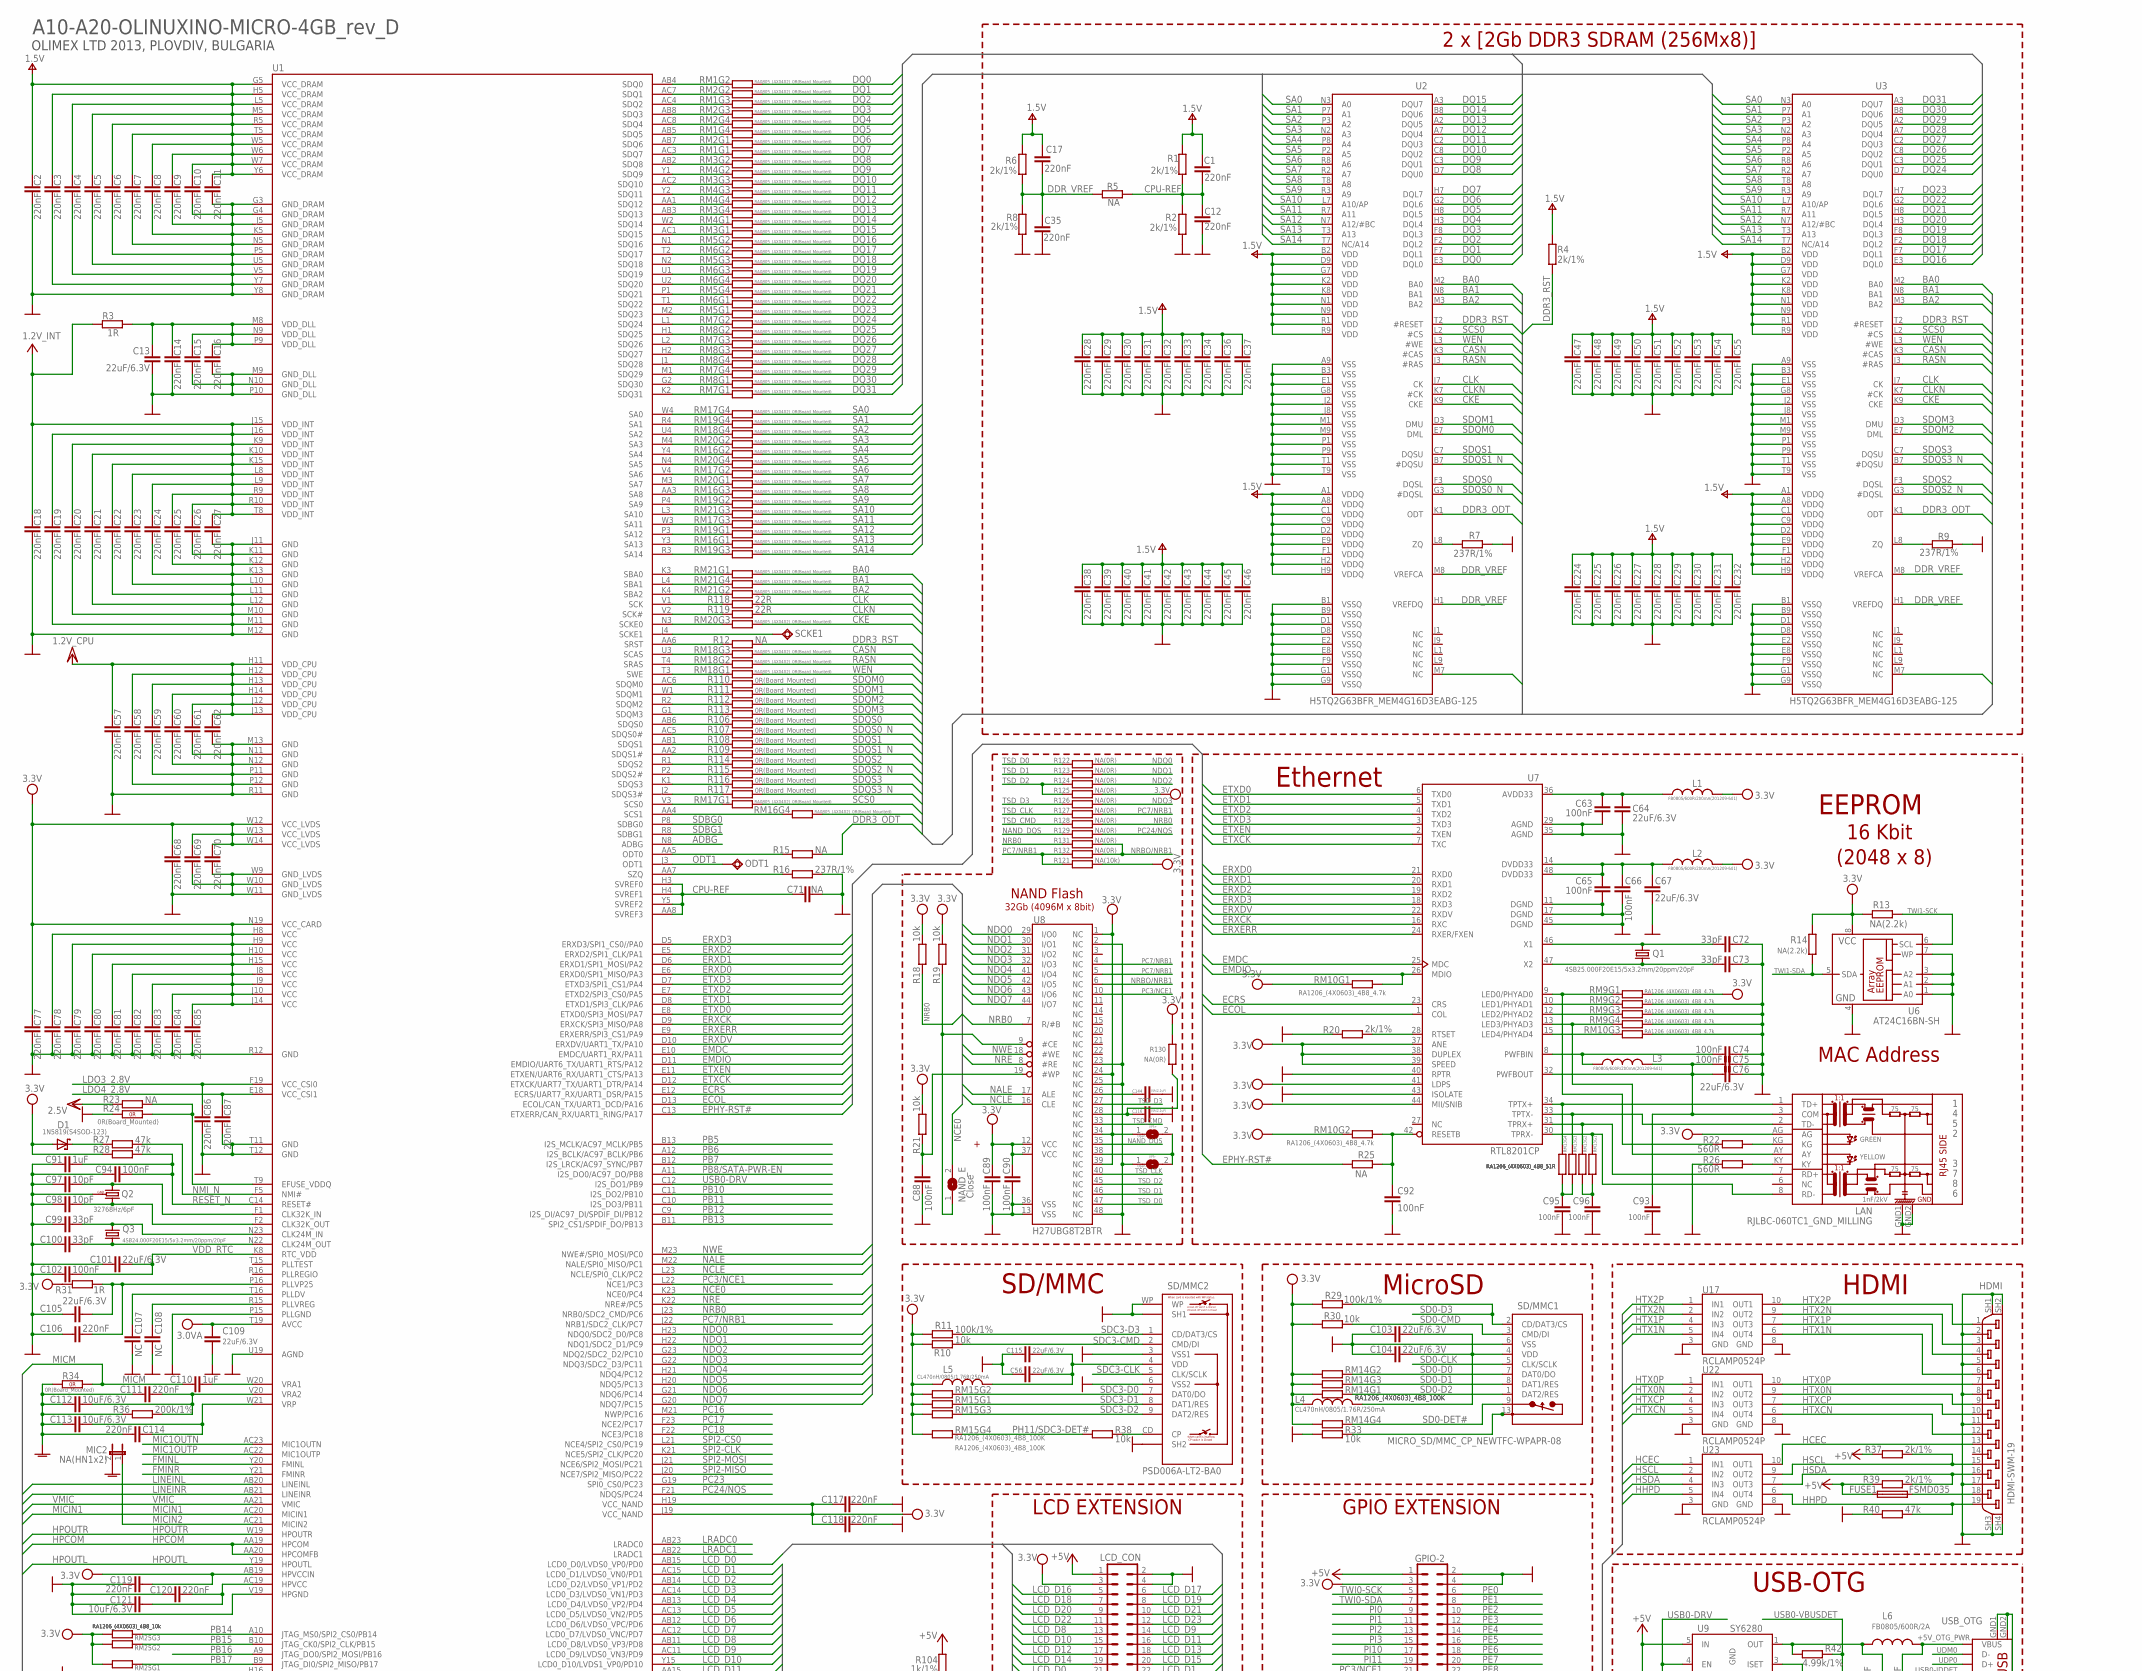
[picture p215: schematic A10-A20-OLINUXINO-MICRO-4GB_Rev_C.sch, part in row 1, column 1]

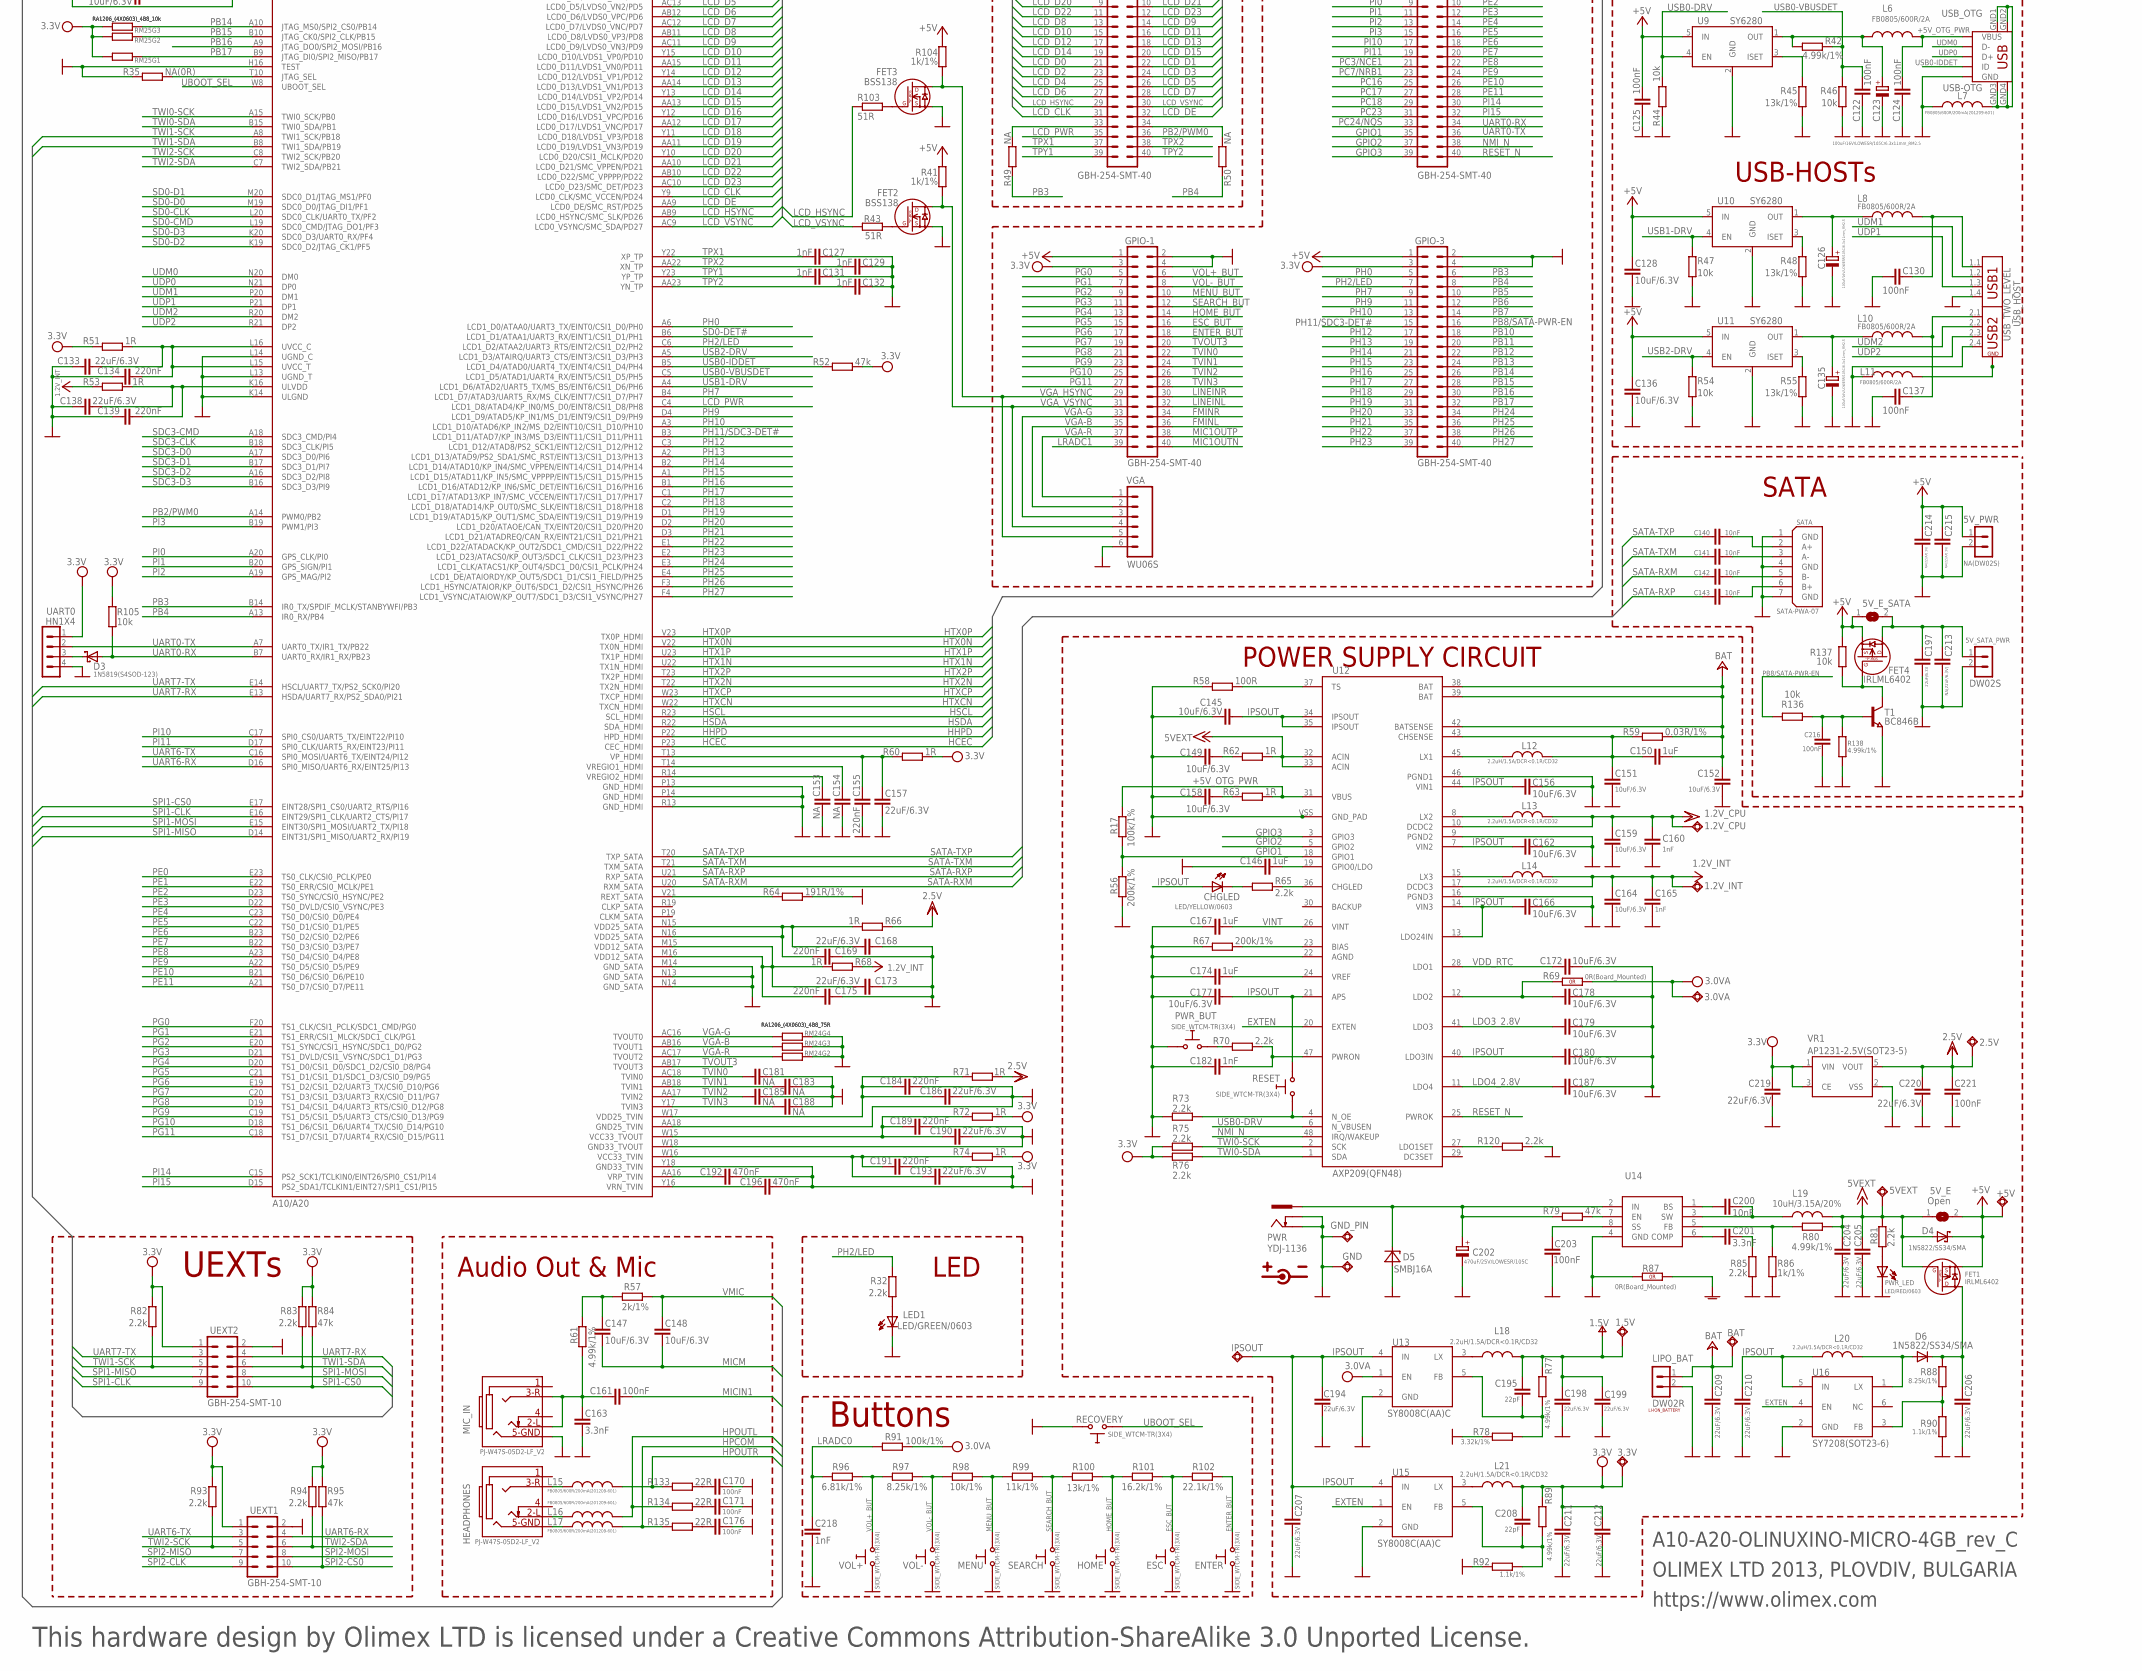
[picture p216: schematic A10-A20-OLINUXINO-MICRO-4GB_Rev_C.sch, part in row 2, column 1]

Parts:
1.2V_CPU, 1.2V_INT, 1.5V, 2.5V, 3.0VA, 3.3V, 5VEXT: TESTPADTESTPAD_40-ROUND; TESTPAD_40-ROUND
5V_E: Open; SJ_1_SMALLER
5V_E_SATA: SJSJ_SMALLER; SJ_1_SMALLER
5V_PWR: NA(DW02S); DW02S
5V_SATA_PWR: DW02S
+5V: TESTPADTESTPAD_40-ROUND; TESTPAD_40-ROUND
BAT: TESTPADTESTPAD_40-ROUND; TESTPAD_40-ROUND
C1, C4, C6, C8, C9, C12, C16, C17, C20, C28, C29, C30, C31, C32, C33, C34, C35, C36, C37, C38, C39, C40, C41, C42, C43, C44, C45, C46, C47, C48, C49, C50, C51, C52, C53, C54, C55, C58, C81, C111, C114, C117, C118, C119, C120, C224, C225, C226, C227, C228, C229, C230, C231, C232: 220nF; C0603_DWS
C2, C3, C5, C7, C10, C11, C14, C15, C18, C19, C21, C22, C23, C24, C25, C26, C27, C57, C59, C60, C61, C62, C68, C69, C70, C77, C78, C79, C80, C82, C83, C84, C85, C86, C87, C106, C134, C139, C155, C169, C175, C184, C189, C191: 220nF; C0402_TI
C13, C56, C64, C67, C76, C101, C103, C104, C105, C109, C115, C133, C138, C157, C168, C173, C186, C190, C193, C194, C197, C198, C199, C204, C205, C206, C207, C209, C210, C211, C212, C219, C220: 22uF/6.3V; C0603_DWS
C63, C65, C66, C74, C75, C88, C89, C90, C92, C93, C94, C95, C96, C122, C124, C125, C130, C137, C161, C170, C171, C176, C203, C216, C221: 100nF; C0603_DWS
C71, C181, C183, C185, C188: NA; C0603_DWS
C72, C73, C99, C100: 33pF; C0603_DWS
C91, C110, C146, C150, C167, C174: 1uF; C0603_DWS
C97, C98: 10pF; C0603_DWS
C102: 100nF; C0402_TI
C107, C108: NC; C0402_TI
C112, C113, C121, C128, C136, C145, C147, C148, C149, C151, C152, C156, C158, C159, C162, C164, C166, C172, C177, C178, C179, C180, C187: 10uF/6.3V; C0603_DWS
C116, C144: NA(2.2uF); C0603_DWS
C123, C126, C135: 100uF/16V/LOWESR/105C/6.3x11mm_RM2.5; E2,5-6,3
C127, C129, C131, C132, C160, C165, C182, C218: 1nF; C0603_DWS
C140, C141, C142, C143, C200: 10nF; C0402_TI
C153, C154: NA; C0402_TI
C163, C201: 3.3nF; C0603_DWS
C192, C196: 470nF; C0603_DWS
C195, C208: 22pF; C0603_DWS
C202: 470uF/25V/LOWESR/105C; E5-10,5
C213, C214, C215: NA(22uF/6.3V); C0603_DWS
CHGLED: LED/YELLOW/0603; LED-0603
D1, D3: 1N5819(S4SOD-123); SOD-123
D4: 1N5822/SS34/SMA; MLL-41
D5: SMBJ16A; DO214AA
D6: 1N5822/SS34/SMA; MELF-MLL41
ENTER: SIDE_WTCM-TR(3X4); SW_TAKT3X4
ESC: SIDE_WTCM-TR(3X4); SW_TAKT3X4
FET1, FET4: IRLML6402; SOT23
FET2, FET3: BSS138; SOT23
FUSE1: FSMD035; 1206
GND: TESTPADTESTPAD_40-ROUND; TESTPAD_40-ROUND
GND_PIN: TESTPAD3; TEST_PAD40/70/SQUARE
GPIO-1, GPIO-2, GPIO-3: GBH-254-SMT-40; ML40-MALE(GBH-254-SMT-40)
HDMI: HDMI-SWM-19
HEADPHONES: PJ-W47S-05D2-LF_V2; PJ-W47S-05D2-LF_5PIN_V2
HOME: SIDE_WTCM-TR(3X4); SW_TAKT3X4
IPSOUT: TESTPADTESTPAD_40-ROUND; TESTPAD_40-ROUND
L1, L2, L3, L7, L15, L16, L17: FB0805/600R/200mA(201209-601); L0805_5MIL_DWS
L4, L5: CL470nH/0805/1.76R/250mA; L0805_5MIL_DWS
L6, L8, L10, L11: FB0805/600R/2A; L0805_5MIL_DWS
L12, L13, L14, L18, L20, L21: 2.2uH/1.5A/DCR<0.1R/CD32; CD32
L19: 10uH/3.15A/20%; 8X8MM_3131
LAN: RJLBC-060TC1_GND_MILLING; RJLBC-060TC1_MILLING
LCD_CON: GBH-254-SMT-40; ML40-MALE(GBH-254-SMT-40)
LED1: LED/GREEN/0603; LED-0603
LIPO_BAT: DW02R
MENU: SIDE_WTCM-TR(3X4); SW_TAKT3X4
MIC2: NA(HN1x2); JP1
MIC_IN: PJ-W47S-05D2-LF_V2; PJ-W47S-05D2-LF_5PIN_V2
NAND_E: Close; SJ_1_SMALLER_CLOSE_10MILS
ODT1: TESTPADTESTPAD_40-ROUND; TESTPAD_40-ROUND
PWR: YDJ-1136; PWR_JACK_UNI_MILLING
PWR_BUT: SIDE_WTCM-TR(3X4); SW_TAKT3X4
PWR_LED: LED/RED/0603; LED-0603
Q1: 4SB25.000F20E15/5x3.2mm/20ppm/20pF; HCX-4S
Q2: 32768Hz/6pF; TC26H_3_REPAIR_SMD
Q3: 4SB24.000F20E15/5x3.2mm/20ppm/20pF; HCX-4S
R1, R2, R4, R6, R8, R20, R37, R39, R57: 2k/1%; R0603_5MIL_DWS
R3, R31, R51, R53, R60, R62, R63, R66, R68, R71, R72, R74: 1R; R0603_5MIL_DWS
R5, R23, R25, R49, R50: NA; R0603_5MIL_DWS
R7, R9, R16: 237R/1%; R0603_5MIL_DWS
R10, R18, R19, R21, R30, R33, R38, R44, R46, R47, R54, R105, R136, R137: 10k; R0603_5MIL_DWS
R11, R17, R29, R91: 100k/1%; R0603_5MIL_DWS
R12, R15: NA; R0402_TI_0R
R13, R14: NA(2.2k); R0603_5MIL_DWS
R22, R26: 560R; R0603_5MIL_DWS
R24, R34, R69, R87: 0R(Board_Mounted); 0603_0R
R27, R28, R40, R52, R79, R84, R95: 47k; R0603_5MIL_DWS
R32, R65, R70, R73, R75, R76, R81, R82, R83, R85, R93, R94, R120: 2.2k; R0603_5MIL_DWS
R35: NA(0R); R0603_5MIL_DWS
R36, R56, R67: 200k/1%; R0603_5MIL_DWS
R41, R86, R104: 1k/1%; R0603_5MIL_DWS
R42, R61, R77, R80, R89, R138: 4.99k/1%; R0603_5MIL_DWS
R43, R103: 51R; R0603_5MIL_DWS
R45, R48, R55, R100: 13k/1%; R0603_5MIL_DWS
R58: 100R; R0603_5MIL_DWS
R59: 0.03R/1%; R1206_5MIL_WS
R64: 191R/1%; R0603_5MIL_DWS
R78: 3.32k/1%; R0603_5MIL_DWS
R88, R97: 8.25k/1%; R0603_5MIL_DWS
R90, R92: 1.1k/1%; R0603_5MIL_DWS
R96: 6.81k/1%; R0603_5MIL_DWS
R98: 10k/1%; R0603_5MIL_DWS
R99: 11k/1%; R0603_5MIL_DWS
R101: 16.2k/1%; R0603_5MIL_DWS
R102: 22.1k/1%; R0603_5MIL_DWS
R106, R107, R108, R109, R110, R111, R112, R113, R114, R115, R116, R117: 0R(Board_Mounted); R0402_TI_0R
R118, R119, R133, R134, R135: 22R; R0402_TI
R121: NA(10k); R0603_5MIL_DWS
R122, R123, R124, R125, R126, R127, R128, R129, R130, R131, R132: NA(0R); R0402_TI
RECOVERY: SIDE_WTCM-TR(3X4); SW_TAKT3X4
RESET: SIDE_WTCM-TR(3X4); SW_TAKT3X4
RM1, RM2, RM3, RM4, RM5, RM6, RM7, RM8, RM16, RM17, RM18, RM19, RM20, RM21: RA0805_(4X0402)_0R(Board_Mounted); R_MATRIX_4_0402_25_625_0R
RM9, RM10: RA1206_(4X0603)_4B8_4.7k; R_MATRIX_4
RM13: RA1206_(4X0603)_4B8_51R; R_MATRIX_4
RM14, RM15: RA1206_(4X0603)_4B8_100K; R_MATRIX_4
RM24: RA1206_(4X0603)_4B8_75R; R_MATRIX_4
RM25: RA1206_(4X0603)_4B8_10k; R_MATRIX_4
SATA: SATA-PWA-07
SCKE1: TESTPADTESTPAD_40-ROUND; TESTPAD_40-ROUND
SD/MMC1: MICRO_SD/MMC_CP_NEWTFC-WPAPR-08; TFC-WPAPR-08
SD/MMC2: PSD006A-LT2-BA0; SD_CARD
SEARCH: SIDE_WTCM-TR(3X4); SW_TAKT3X4
T1: BC846B; SOT23
U1: A10/A20; TFBGA441
U2, U3: H5TQ2G63BFR_MEM4G16D3EABG-125; FBGA96_MEM
U6: AT24C16BN-SH; SO-08MN
U7: RTL8201CP; LQFP48
U8: H27UBG8T2BTR; TSOP48
U9, U10, U11: SY6280; SOT23-5
U12: AXP209(QFN48); QFN48
U13, U15: SY8008C(AA)C; SOT23-5
U14: MP1482DS; SOIC8
U16: SY7208(SOT23-6); SOT23-6
U17, U22, U23: RCLAMP0524P; SLP2510P8
UART0: HN1X4
UEXT1, UEXT2: GBH-254-SMT-10; ML10_S
USB_HOST: USB_TWO_LEVEL
USB_OTG: USB-OTG; USB_MINI_9PIN
VGA: WU06S; CON1.27MM-6-SMALL_ICSP
VOL+: SIDE_WTCM-TR(3X4); SW_TAKT3X4
VOL-: SIDE_WTCM-TR(3X4); SW_TAKT3X4
VPS+: Open; SJ_1_SMALLER
VPS-: Open; SJ_1_SMALLER
VR1: AP1231-2.5V(SOT23-5); SOT-23-5

Connections:
+5V: 5V_E.2, 5V_E_SATA.1, 5V_PWR.1, +5V.1, C125.1, C128.1, C136.1, C214.2, C215.2, D4.K (C), FET1.2 (S), FET4.2 (S), FUSE1.1, GPIO-1.1, GPIO-2.1, GPIO-3.1, LCD_CON.1, R37.2, R39.2, R41.1, R104.1, R137.1, U9.5 (IN), U10.5 (IN), U11.5 (IN)
+5V_OTG_PWR: C124.1, L6.1, R17.1, R63.2, U12.31 (VBUS), USB_OTG.VBUS
+15V: 5VEXT.1, 5V_E.1, C204.1, C205.1, D4.A, FET1.1 (G), L19.2, R62.2, R80.2, R81.1, U12.32 (ACIN), U12.33 (ACIN)
+24V: BAT.1, C150.2, C152.1, C209.2, LIPO_BAT.1, R59.2, U12.38 (BAT), U12.39 (BAT), U12.42 (BATSENSE)
ADBG: U1.N8 (ADBG)
BA0: RM21.1.2 (2), U2.M2 (BA0), U3.M2 (BA0)
BA1: RM21.4.2 (2), U2.N8 (BA1), U3.N8 (BA1)
BA2: RM21.2.2 (2), U2.M3 (BA2), U3.M3 (BA2)
CASN: RM18.3.2 (2), U2.K3 (#CAS), U3.K3 (#CAS)
CKE: RM20.3.2 (2), U2.K9 (CKE), U3.K9 (CKE)
CLK: R118.1, U2.J7 (CK), U3.J7 (CK)
CLKN: R119.1, U2.K7 (#CK), U3.K7 (#CK)
CPU-REF: C1.2, C12.2, C71.2, R1.1, R2.2, R5.2, U1.AA8 (SVREF3), U1.H3 (SVREF0), U1.H4 (SVREF1), U1.Y5 (SVREF2)
DDR3_ODT: R15.1, U2.K1 (ODT), U3.K1 (ODT)
DDR3_RST: R4.1, R12.1, U2.T2 (#RESET), U3.T2 (#RESET)
DDR3_SA0: RM17.4.1 (1), U1.W4 (SA0)
DDR3_SA1: RM19.4.1 (1), U1.R4 (SA1)
DDR3_SA2: RM18.4.1 (1), U1.U4 (SA2)
DDR3_SA3: RM20.2.1 (1), U1.M4 (SA3)
DDR3_SA4: RM16.2.1 (1), U1.Y4 (SA4)
DDR3_SA5: RM20.4.1 (1), U1.N4 (SA5)
DDR3_SA6: RM17.2.1 (1), U1.V4 (SA6)
DDR3_SA7: RM20.1.1 (1), U1.M3 (SA7)
DDR3_SA8: RM16.3.1 (1), U1.AA3 (SA8)
DDR3_SA9: RM19.2.1 (1), U1.P4 (SA9)
DDR3_SA10: RM21.3.1 (1), U1.L3 (SA10)
DDR3_SA11: RM17.3.1 (1), U1.W3 (SA11)
DDR3_SA12: RM19.1.1 (1), U1.P3 (SA12)
DDR3_SA13: RM16.1.1 (1), U1.Y3 (SA13)
DDR3_SA14: RM19.3.1 (1), U1.R3 (SA14)
DDR3_SA15: RM16.4.1 (1), U1.AA4 (SCS1)
DDR3_SBA0: RM21.1.1 (1), U1.K3 (SBA0)
DDR3_SBA1: RM21.4.1 (1), U1.L4 (SBA1)
DDR3_SBA2: RM21.2.1 (1), U1.K4 (SBA2)
DDR3_SCAS: RM18.3.1 (1), U1.U3 (SCAS)
DDR3_SCS0: RM17.1.1 (1), U1.V3 (SCS0)
DDR3_SDQM0: R110.2, U1.AC6 (SDQM0)
DDR3_SDQM1: R111.2, U1.W1 (SDQM1)
DDR3_SDQM2: R112.2, U1.R2 (SDQM2)
DDR3_SDQM3: R113.2, U1.G1 (SDQM3)
DDR3_SDQS0: R106.2, U1.AB6 (SDQS0)
DDR3_SDQS0#: R107.2, U1.AC5 (SDQS0#)
DDR3_SDQS1: R108.2, U1.AB1 (SDQS1)
DDR3_SDQS1#: R109.2, U1.AA2 (SDQS1#)
DDR3_SDQS2: R114.2, U1.R1 (SDQS2)
DDR3_SDQS2#: R115.2, U1.P2 (SDQS2#)
DDR3_SDQS3: R116.2, U1.K1 (SDQS3)
DDR3_SDQS3#: R117.2, U1.J2 (SDQS3#)
DDR3_SRAS: RM18.2.1 (1), U1.T4 (SRAS)
DDR3_SWE: RM18.1.1 (1), U1.T3 (SWE)
DDR_VREF: C17.2, C35.2, R5.1, R6.1, R8.2, U2.H1 (VREFDQ), U2.M8 (VREFCA), U3.H1 (VREFDQ), U3.M8 (VREFCA)
DQ0: RM1.2.1 (1), U2.E3 (DQL0)
DQ1: RM2.2.1 (1), U2.F7 (DQL1)
DQ2: RM1.3.1 (1), U2.F2 (DQL2)
DQ3: RM2.3.1 (1), U2.F8 (DQL3)
DQ4: RM2.4.1 (1), U2.H3 (DQL4)
DQ5: RM1.4.1 (1), U2.H8 (DQL5)
DQ6: RM2.1.1 (1), U2.G2 (DQL6)
DQ7: RM1.1.1 (1), U2.H7 (DQL7)
DQ8: RM3.2.1 (1), U2.D7 (DQU0)
DQ9: RM4.2.1 (1), U2.C3 (DQU1)
DQ10: RM3.3.1 (1), U2.C8 (DQU2)
DQ11: RM4.3.1 (1), U2.C2 (DQU3)
DQ12: RM4.4.1 (1), U2.A7 (DQU4)
DQ13: RM3.4.1 (1), U2.A2 (DQU5)
DQ14: RM4.1.1 (1), U2.B8 (DQU6)
DQ15: RM3.1.1 (1), U2.A3 (DQU7)
DQ16: RM5.2.1 (1), U3.E3 (DQL0)
DQ17: RM6.2.1 (1), U3.F7 (DQL1)
DQ18: RM5.3.1 (1), U3.F2 (DQL2)
DQ19: RM6.3.1 (1), U3.F8 (DQL3)
DQ20: RM6.4.1 (1), U3.H3 (DQL4)
DQ21: RM5.4.1 (1), U3.H8 (DQL5)
DQ22: RM6.1.1 (1), U3.G2 (DQL6)
DQ23: RM5.1.1 (1), U3.H7 (DQL7)
DQ24: RM7.2.1 (1), U3.D7 (DQU0)
DQ25: RM8.2.1 (1), U3.C3 (DQU1)
DQ26: RM7.3.1 (1), U3.C8 (DQU2)
DQ27: RM8.3.1 (1), U3.C2 (DQU3)
DQ28: RM8.4.1 (1), U3.A7 (DQU4)
DQ29: RM7.4.1 (1), U3.A2 (DQU5)
DQ30: RM8.1.1 (1), U3.B8 (DQU6)
DQ31: RM7.1.1 (1), U3.A3 (DQU7)
ECOL: U1.D13 (ECOL/CAN_TX/UART1_DCD/PA16), U7.1 (COL)
ECRS: U1.E12 (ECRS/UART7_RX/UART1_DSR/PA15), U7.23 (CRS)
EMDC: U1.E10 (EMDC/UART1_RX/PA11), U7.25 (MDC)
EMDIO: RM10.1.1 (1), U1.D11 (EMDIO/UART6_TX/UART1_RTS/PA12), U7.26 (MDIO)
ENTER_BUT: ENTER.1_1 (1), GPIO-1.18, R102.2
EPHY-RST#: R25.1, U1.C13 (ETXERR/CAN_RX/UART1_RING/PA17)
ERXCK: U1.D9 (ERXCK/SPI3_MISO/PA8), U7.16 (RXC)
ERXD0: U1.E6 (ERXD0/SPI1_MISO/PA3), U7.21 (RXD0)
ERXD1: U1.D6 (ERXD1/SPI1_MOSI/PA2), U7.20 (RXD1)
ERXD2: U1.E5 (ERXD2/SPI1_CLK/PA1), U7.19 (RXD2)
ERXD3: U1.D5 (ERXD3/SPI1_CS0//PA0), U7.18 (RXD3)
ERXDV: U1.D10 (ERXDV/UART1_TX/PA10), U7.22 (RXDV)
ERXERR: U1.E9 (ERXERR/SPI3_CS1/PA9), U7.24 (RXER/FXEN)
ESC_BUT: ESC.1_1 (1), GPIO-1.16, R101.2, R102.1
ETXCK: U1.D12 (ETXCK/UART7_TX/UART1_DTR/PA14), U7.7 (TXC)
ETXD0: U1.E8 (ETXD0/SPI3_MOSI/PA7), U7.6 (TXD0)
ETXD1: U1.D8 (ETXD1/SPI3_CLK/PA6), U7.5 (TXD1)
ETXD2: U1.E7 (ETXD2/SPI3_CS0/PA5), U7.4 (TXD2)
ETXD3: U1.D7 (ETXD3/SPI1_CS1/PA4), U7.3 (TXD3)
ETXEN: U1.E11 (ETXEN/UART6_RX/UART1_CTS/PA13), U7.2 (TXEN)
EXTEN: U12.20 (EXTEN), U15.1 (EN), U16.4 (EN)
FMINL: GPIO-1.36, U1.Y20 (FMINL)
FMINR: GPIO-1.34, U1.Y21 (FMINR)
GND: 5V_PWR.2, 5V_SATA_PWR.2, C2.1, C3.1, C4.1, C5.1, C6.1, C7.1, C8.1, C9.1, C10.1, C11.1, C12.1, C13.1, C14.1, C15.1, C16.1, C18.1, C19.1, C20.1, C21.1, C22.1, C23.1, C24.1, C25.1, C26.1, C27.1, C28.1, C29.1, C30.1, C31.1, C32.1, C33.1, C34.1, C35.1, C36.1, C37.1, C38.1, C39.1, C40.1, C41.1, C42.1, C43.1, C44.1, C45.1, C46.1, C47.1, C48.1, C49.1, C50.1, C51.1, C52.1, C53.1, C54.1, C55.1, C56.1, C57.1, C58.1, C59.1, C60.1, C61.1, C62.1, C63.1, C64.1, C65.1, C66.1, C67.1, C68.1, C69.1, C70.1, C71.1, C72.1, C73.1, C74.2, C75.2, C76.2, C77.1, C78.1, C79.1, C80.1, C81.1, C82.1, C83.1, C84.1, C85.1, C86.1, C87.1, C88.1, C89.1, C90.1, C91.1, C92.1, C93.1, C94.1, C95.1, C96.1, C97.1, C98.1, C99.1, C100.1, C101.1, C102.1, C103.1, C104.1, C105.1, C106.1, C107.1, C108.1, C109.1, C115.1, C116.2, C117.1, C118.1, C119.1, C120.1, C121.1, C122.2, C123.-, C124.2, C125.2, C126.-, C127.1, C128.2, C129.1, C130.2, C131.1, C132.1, C133.1, C134.1, C135.-, C136.2, C137.2, C138.1, C139.1, C144.2, C145.1, C146.1, C149.1, C151.2, C152.2, C153.2, C154.2, C155.2, C156.2, C157.1, C158.1, C159.2, C160.2, C162.2, C163.1, C164.2, C165.2, C166.2, C167.1, C168.1, C169.1, C170.1, C171.1, C172.2, C173.1, C174.1, C175.1, C176.1, C177.1, C178.2, C179.2, C180.2, C181.1, C182.1, C183.1, C184.2, C185.1, C186.1, C187.2, C188.1, C189.2, C190.1, C191.2, C192.1, C193.1, C194.2, C196.1, C197.1, C198.2, C199.2, C202.-, C203.2, C204.2, C205.2, C206.2, C207.2, C209.1, C210.1, C211.2, C212.2, C213.1, C214.1, C215.1, C216.2, C218.2, C219.2, C220.2, C221.2, C224.1, C225.1, C226.1, C227.1, C228.1, C229.1, C230.1, C231.1, C232.1, D5.A, ENTER.2_1 (0), ESC.2_1 (0), FET2.2 (S), FET3.2 (S), GND.1, GND_PIN.P$1, GPIO-1.2, GPIO-1.4, GPIO-2.2, GPIO-2.4, GPIO-3.2, GPIO-3.4, HDMI.2, HDMI.5, HDMI.8, HDMI.11, HDMI.17, HDMI.SH1 (20), HDMI.SH2 (21), HDMI.SH3 (22), HDMI.SH4 (23), HOME.2_1 (0), L7.1, L11.1, LAN.GND1, LAN.GND2, LCD_CON.2, LCD_CON.4, LED1.C, LIPO_BAT.2, MENU.2_1 (0), MIC_IN.5, PWR.-, PWR.--, PWR_BUT.2_1 (0), PWR_LED.C, Q2.GND, R2.1, R7.1, R8.1, R9.1, R16.1, R20.1, R24.1 (1.1), R26.2, R33.2, R35.2, R40.2, R44.1, R45.1, R46.1, R47.1, R48.1, R54.1, R55.1, R56.2, R58.1, R64.1, R67.1, R73.1, R78.2, R85.2, R86.2, R87.1 (1.1), R90.2, R92.2, R120.2, R138.1, RECOVERY.1_1 (1), RM9.2.1 (1), RM9.3.1 (1), RM9.4.1 (1), RM10.3.2 (2), RM24.2.1 (1), RM24.3.1 (1), RM24.4.1 (1), SATA.1 (GND), SATA.4 (GND), SATA.7 (GND), SD/MMC1.6 (VSS), SD/MMC2.3 (VSS1), SD/MMC2.6 (VSS2), SD/MMC2.SH1, SD/MMC2.SH2, SD/MMC2.WP, SEARCH.2_1 (0), T1.2 (E), U1.AA18 (GND25_TVIN), U1.G3 (GND_DRAM), U1.G4 (GND_DRAM), U1.H16 (TEST), U1.J5 (GND_DRAM), U1.J11 (GND), U1.K5 (GND_DRAM), U1.K11 (GND), U1.K12 (GND), U1.K13 (GND), U1.K14 (ULGND), U1.L10 (GND), U1.L11 (GND), U1.L12 (GND), U1.L13 (UGND_T), U1.L14 (UGND_C), U1.M9 (GND_DLL), U1.M10 (GND), U1.M11 (GND), U1.M12 (GND), U1.M13 (GND), U1.M14 (GND_SATA), U1.N5 (GND_DRAM), U1.N10 (GND_DLL), U1.N11 (GND), U1.N12 (GND), U1.N13 (GND_SATA), U1.N14 (GND_SATA), U1.P5 (GND_DRAM), U1.P10 (GND_DLL), U1.P11 (GND), U1.P12 (GND), U1.P13 (GND_HDMI), U1.P14 (GND_HDMI), U1.P15 (PLLGND), U1.R11 (GND), U1.R12 (GND), U1.R13 (GND_HDMI), U1.T11 (GND), U1.T12 (GND), U1.U5 (GND_DRAM), U1.U19 (AGND), U1.V5 (GND_DRAM), U1.V19 (HPGND), U1.W9 (GND_LVDS), U1.W10 (GND_LVDS), U1.W11 (GND_LVDS), U1.W18 (GND33_TVOUT), U1.Y7 (GND_DRAM), U1.Y8 (GND_DRAM), U1.Y18 (GND33_TVIN), U2.A9 (VSS), U2.B1 (VSSQ), U2.B3 (VSS), U2.B9 (VSSQ), U2.D1 (VSSQ), U2.D8 (VSSQ), U2.E1 (VSS), U2.E2 (VSSQ), U2.E8 (VSSQ), U2.F9 (VSSQ), U2.G1 (VSSQ), U2.G8 (VSS), U2.G9 (VSSQ), U2.J2 (VSS), U2.J8 (VSS), U2.M1 (VSS), U2.M9 (VSS), U2.P1 (VSS), U2.P9 (VSS), U2.T1 (VSS), U2.T9 (VSS), U3.A9 (VSS), U3.B1 (VSSQ), U3.B3 (VSS), U3.B9 (VSSQ), U3.D1 (VSSQ), U3.D8 (VSSQ), U3.E1 (VSS), U3.E2 (VSSQ), U3.E8 (VSSQ), U3.F9 (VSSQ), U3.G1 (VSSQ), U3.G8 (VSS), U3.G9 (VSSQ), U3.J2 (VSS), U3.J8 (VSS), U3.M1 (VSS), U3.M9 (VSS), U3.P1 (VSS), U3.P9 (VSS), U3.T1 (VSS), U3.T9 (VSS), U6.1 (A0), U6.2 (A1), U6.3 (A2), U6.4 (GND), U6.7 (WP), U7.11 (DGND), U7.17 (DGND), U7.29 (AGND), U7.35 (AGND), U7.40 (RPTR), U7.43 (ISOLATE), U7.45 (DGND), U8.2 (NC), U8.13 (VSS), U8.23 (NC), U8.25 (NC), U8.36 (VSS), U8.48 (NC), U9.2 (GND), U10.2 (GND), U11.2 (GND), U12.9 (PGND2), U12.16 (PGND3), U12.22 (AGND), U12.46 (PGND1), U12.N1 (GND_PAD), U12.N2 (GND_PAD), U12.N3 (GND_PAD), U12.N4 (GND_PAD), U12.N5 (GND_PAD), U12.N6 (GND_PAD), U12.N7 (GND_PAD), U12.N8 (GND_PAD), U12.N9 (GND_PAD), U12.N10 (GND_PAD), U12.N11 (GND_PAD), U12.N12 (GND_PAD), U12.N13 (GND_PAD), U12.N14 (GND_PAD), U12.N15 (GND_PAD), U12.N16 (GND_PAD), U12.N17 (GND_PAD), U12.VSS (GND_PAD), U13.2 (GND), U14.4 (GND), U15.2 (GND), U16.2 (GND), U17.3 (GND), U17.8 (GND), U22.3 (GND), U22.8 (GND), U23.3 (GND), U23.8 (GND), UART0.4, UEXT1.2, UEXT2.2, USB_HOST.1.4, USB_HOST.2.4, USB_OTG.GND, VGA.6, VOL+.2_1 (0), VOL-.2_1 (0), VPS-.1, VR1.2 (VSS)
GNDA: C111.1, C112.1, C113.1, C114.1, MIC2.2, R34.1 (1.1), R36.2, R87.2 (1.2)
GPIO1: GPIO-2.35, R17.2, R56.1, U12.18 (GPIO1)
GPIO2: GPIO-2.37, U12.5 (GPIO2)
GPIO3: GPIO-2.39, U12.3 (GPIO3)
HCEC: HDMI.13, U1.P23 (CEC_HDMI), U23.1 (IN1), U23.10 (OUT1)
HDMI_5V_SOURCE: FUSE1.2, HDMI.18
HHPD: HDMI.19, R40.1, U1.P22 (HPD_HDMI), U23.5 (IN4), U23.6 (OUT4)
HOME_BUT: GPIO-1.14, HOME.1_1 (1), R100.2, R101.1
HPCOM: L17.1, R135.2, U1.AA19 (HPCOM), U1.AA20 (HPCOMFB)
HPOUTL: L16.1, R134.2, U1.Y19 (HPOUTL)
HPOUTR: L15.1, R133.2, U1.W19 (HPOUTR)
HSCL: HDMI.15, R37.1, U1.R23 (SCL_HDMI), U23.2 (IN2), U23.9 (OUT2)
HSDA: HDMI.16, R39.1, U1.R22 (SDA_HDMI), U23.4 (IN3), U23.7 (OUT3)
HTX0N: HDMI.9, U1.V22 (TX0N_HDMI), U22.2 (IN2), U22.9 (OUT2)
HTX0P: HDMI.7, U1.V23 (TX0P_HDMI), U22.1 (IN1), U22.10 (OUT1)
HTX1N: HDMI.6, U1.U22 (TX1N_HDMI), U17.5 (IN4), U17.6 (OUT4)
HTX1P: HDMI.4, U1.U23 (TX1P_HDMI), U17.4 (IN3), U17.7 (OUT3)
HTX2N: HDMI.3, U1.T22 (TX2N_HDMI), U17.2 (IN2), U17.9 (OUT2)
HTX2P: HDMI.1, U1.T23 (TX2P_HDMI), U17.1 (IN1), U17.10 (OUT1)
HTXCN: HDMI.12, U1.W22 (TXCN_HDMI), U22.5 (IN4), U22.6 (OUT4)
HTXCP: HDMI.10, U1.W23 (TXCP_HDMI), U22.4 (IN3), U22.7 (OUT3)
IPSOUT: C145.2, C156.1, C162.1, C166.1, C177.2, C180.1, C194.1, C207.1, C210.2, CHGLED.A, IPSOUT.1, L20.1, RESET.1_1 (1), U12.7 (VIN2), U12.13 (LDO24IN), U12.14 (VIN3), U12.21 (APS), U12.34 (IPSOUT), U12.35 (IPSOUT), U12.40 (LDO3IN), U12.44 (VIN1), U13.4 (IN), U15.4 (IN), U16.5 (IN)
LCD_CLK: LCD_CON.31, U1.Y9 (LCD0_CLK/SMC_VCCEN/PD24)
LCD_D0: LCD_CON.21, U1.AB15 (LCD0_D0/LVDS0_VP0/PD0)
LCD_D1: LCD_CON.22, U1.AC15 (LCD0_D1/LVDS0_VN0/PD1)
LCD_D2: LCD_CON.23, U1.AB14 (LCD0_D2/LVDS0_VP1/PD2)
LCD_D3: LCD_CON.24, U1.AC14 (LCD0_D3/LVDS0_VN1/PD3)
LCD_D4: LCD_CON.25, U1.AB13 (LCD0_D4/LVDS0_VP2/PD4)
LCD_D5: LCD_CON.26, U1.AC13 (LCD0_D5/LVDS0_VN2/PD5)
LCD_D6: LCD_CON.27, U1.AB12 (LCD0_D6/LVDS0_VPC/PD6)
LCD_D7: LCD_CON.28, U1.AC12 (LCD0_D7/LVDS0_VNC/PD7)
LCD_D8: LCD_CON.13, U1.AB11 (LCD0_D8/LVDS0_VP3/PD8)
LCD_D9: LCD_CON.14, U1.AC11 (LCD0_D9/LVDS0_VN3/PD9)
LCD_D10: LCD_CON.15, U1.Y15 (LCD0_D10/LVDS1_VP0/PD10)
LCD_D11: LCD_CON.16, U1.AA15 (LCD0_D11/LVDS1_VN0/PD11)
LCD_D12: LCD_CON.17, U1.Y14 (LCD0_D12/LVDS1_VP1/PD12)
LCD_D13: LCD_CON.18, U1.AA14 (LCD0_D13/LVDS1_VN1/PD13)
LCD_D14: LCD_CON.19, U1.Y13 (LCD0_D14/LVDS1_VP2/PD14)
LCD_D15: LCD_CON.20, U1.AA13 (LCD0_D15/LVDS1_VN2/PD15)
LCD_D16: LCD_CON.5, U1.Y12 (LCD0_D16/LVDS1_VPC/PD16)
LCD_D17: LCD_CON.6, U1.AA12 (LCD0_D17/LVDS1_VNC/PD17)
LCD_D18: LCD_CON.7, U1.Y11 (LCD0_D18/LVDS1_VP3/PD18)
LCD_D19: LCD_CON.8, U1.AA11 (LCD0_D19/LVDS1_VN3/PD19)
LCD_D20: LCD_CON.9, U1.Y10 (LCD0_D20/CSI1_MCLK/PD20)
LCD_D21: LCD_CON.10, U1.AA10 (LCD0_D21/SMC_VPPEN/PD21)
LCD_D22: LCD_CON.11, U1.AB10 (LCD0_D22/SMC_VPPPP/PD22)
LCD_D23: LCD_CON.12, U1.AC10 (LCD0_D23/SMC_DET/PD23)
LCD_DE: LCD_CON.32, U1.AA9 (LCD0_DE/SMC_RST/PD25)
LCD_HSYNC: LCD_CON.29, R103.1, U1.AB9 (LCD0_HSYNC/SMC_SLK/PD26)
LCD_PWR: LCD_CON.35, U1.C4 (LCD1_D8/ATAD4/KP_IN0/MS_D0/EINT8/CSI1_D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)
LCD_VSYNC: LCD_CON.30, R43.1, U1.AC9 (LCD0_VSYNC/SMC_SDA/PD27)
LDO3_2.8V: C86.2, C179.1, U1.F19 (VCC_CSI0), U12.41 (LDO3)
LDO4_2.8V: C87.2, C187.1, U1.E18 (VCC_CSI1), U12.11 (LDO4)
LINEINL: GPIO-1.32, U1.AB20 (LINEINL)
LINEINR: GPIO-1.30, U1.AB21 (LINEINR)
LRADC0: C218.1, R91.2, R96.1, U1.AB23 (LRADC0)
LRADC1: GPIO-1.39, U1.AB22 (LRADC1)
MENU_BUT: GPIO-1.10, MENU.1_1 (1), R98.2, R99.1
MIC1OUTN: GPIO-1.40, U1.AC23 (MIC1OUTN)
MIC1OUTP: GPIO-1.38, U1.AC22 (MIC1OUTP)
MICIN1: C161.2, U1.AC20 (MICIN1)
MICIN2: MIC2.1, U1.AC21 (MICIN2)
MICM: C110.1, C147.1, C148.1, R34.2 (1.2)
unnamed: C120.2, C121.2, U1.AC19 (HPVCC)
unnamed: R16.2, U1.AA7 (SZQ)
unnamed: R7.2, U2.L8 (ZQ)
unnamed: R65.2, U12.36 (CHGLED)
unnamed: R9.2, U3.L8 (ZQ)
unnamed: R20.2, U7.28 (RTSET)
unnamed: D3.C, UART0.3
unnamed: L18.1, U13.3 (LX)
unnamed: C146.2, U12.19 (GPIO0/LDO)
unnamed: D1.C, R27.2
unnamed: FET2.1 (G), R43.2
unnamed: R120.1, U12.27 (LDO1SET)
unnamed: RM10.3.1 (1), U7.15 (LED4/PHYAD4)
unnamed: C144.1, U8.26 (NC)
unnamed: C161.1, C163.2, MIC_IN.2, MIC_IN.3, R61.2
unnamed: C216.1, R136.1, R138.2, T1.1 (B)
unnamed: FET4.1 (G), R137.2, T1.3 (C)
unnamed: C195.2, R77.2, R78.1, U13.5 (FB)
unnamed: C116.1, R130.2, U8.28 (NC)
unnamed: C63.2, C64.2, L1.1, U7.36 (AVDD33)
unnamed: HEADPHONES.5, L17.2
unnamed: C206.1, D6.1 (C), FET1.3 (D), R88.2
unnamed: 5V_E_SATA.2, 5V_SATA_PWR.1, C197.2, C213.2, FET4.3 (D)
unnamed: HEADPHONES.2, L16.2
unnamed: HEADPHONES.3, L15.2
unnamed: FET3.1 (G), R103.2
unnamed: C178.1, R69.2 (1.2), U12.12 (LDO2)
unnamed: C202.+, D5.C, PWR.+, R79.1, U14.2 (IN)
unnamed: C92.2, R25.2, RM10.2.1 (1), U7.42 (RESETB)
unnamed: C96.2, RM13.1.1 (1), RM13.2.1 (1)
unnamed: C171.2, R134.1
unnamed: C176.2, R135.1
unnamed: C203.1, U14.8 (SS)
unnamed: R79.2, U14.7 (EN)
unnamed: PWR_BUT.1_1 (1), R70.1
unnamed: LAN.1 (TD+), RM13.4.2 (2), U7.34 (TPTX+)
unnamed: LAN.2 (TD-), RM13.3.2 (2), U7.33 (TPTX-)
unnamed: LAN.7 (RD+), RM13.2.2 (2), U7.31 (TPRX+)
unnamed: C192.2, U1.AA16 (VRP_TVIN)
unnamed: CHGLED.C, R65.1
unnamed: C170.2, R133.1
unnamed: LAN.8 (RD-), RM13.1.2 (2), U7.30 (TPRX-)
unnamed: C200.1, U14.1 (BS)
unnamed: C95.2, RM13.3.1 (1), RM13.4.1 (1)
unnamed: RM9.2.2 (2), U7.10 (LED1/PHYAD1)
unnamed: C200.2, L19.1, U14.3 (SW)
unnamed: RM9.3.2 (2), U7.12 (LED2/PHYAD2)
unnamed: LAN.KG, R22.1
unnamed: LAN.AY, RM9.4.2 (2), U7.13 (LED3/PHYAD3)
unnamed: C74.1, L3.1, U7.8 (PWFBIN)
unnamed: C75.1, C76.1, C93.2, L3.2, LAN.3 (COM), U7.32 (PWFBOUT)
unnamed: LAN.KY, R26.1
unnamed: R33.1, SD/MMC1.10 (PACK1), SD/MMC1.11 (PACK2), SD/MMC1.12 (PACK3), SD/MMC1.13 (PACK4)
unnamed: C201.1, U14.6 (COMP)
unnamed: C201.2, R85.1
unnamed: R80.1, R86.1, U14.5 (FB)
unnamed: L21.1, U15.3 (LX)
unnamed: C208.2, R89.2, R92.1, U15.5 (FB)
unnamed: C65.2, C66.2, C67.2, L2.1, U7.14 (DVDD33), U7.48 (DVDD33)
unnamed: R22.2, RM9.1.2 (2), U7.9 (LED0/PHYAD0)
unnamed: U8.38 (NC), VPS+.2, VPS-.2
unnamed: C155.1, C157.2, R60.2, U1.T13 (VP_HDMI)
unnamed: C153.1, U1.R14 (VREGIO2_HDMI)
unnamed: C154.1, U1.T14 (VREGIO1_HDMI)
unnamed: R23.1, R24.2 (1.2), U1.T9 (EFUSE_VDDQ)
unnamed: C105.2, C106.2, R31.1, U1.P16 (PLLVP25)
unnamed: C97.2, Q2.1, U1.F1 (CLK32K_IN)
unnamed: R45.2, U9.3 (ISET)
unnamed: C123.+, L6.2, R42.2, U9.1 (OUT)
unnamed: R48.2, U10.3 (ISET)
unnamed: C133.2, C134.2, R51.1, U1.L15 (UVCC_T), U1.L16 (UVCC_C)
unnamed: C138.2, C139.2, R53.1, U1.K16 (ULVDD)
unnamed: C140.2, SATA.2 (A+)
unnamed: C130.1, L8.2, USB_HOST.1.1
unnamed: C141.2, SATA.3 (A-)
unnamed: C142.2, SATA.5 (B-)
unnamed: C143.2, SATA.6 (B+)
unnamed: C107.2, U1.T16 (PLLDV)
unnamed: C98.2, Q2.2, U1.F2 (CLK32K_OUT)
unnamed: R64.2, U1.V21 (REXT_SATA)
unnamed: R67.2, U12.23 (BIAS)
unnamed: C108.2, U1.R15 (PLLVREG)
unnamed: C113.2, C114.2, U1.W21 (VRP)
unnamed: D6.2 (A), L20.2, U16.1 (LX)
unnamed: C88.2, R21.2, U8.19 (#WP)
unnamed: R58.2, U12.37 (TS)
unnamed: R88.1, R90.1, U16.3 (FB)
unnamed: L12.1, U12.45 (LX1)
unnamed: C150.1, C151.1, L12.2, R59.1, U12.43 (CHSENSE)
unnamed: PWR_LED.A, R81.2
unnamed: L13.1, U12.8 (LX2)
unnamed: L14.1, U12.15 (LX3)
unnamed: C174.2, U12.24 (VREF)
unnamed: C110.2, U1.W20 (VRA1)
unnamed: C149.2, R62.1
unnamed: C158.2, R63.1
unnamed: R55.2, U11.3 (ISET)
unnamed: C182.2, R70.2, U12.47 (PWRON)
unnamed: R73.2, RESET.2_1 (0), U12.4 (N_OE)
unnamed: R38.1, SD/MMC2.CD (CP)
unnamed: C111.2, C112.2, R36.1, U1.V20 (VRA2)
unnamed: C147.2, R57.1, R61.1
unnamed: R35.1, U1.T10 (JTAG_SEL)
unnamed: C168.2, C169.2, R66.1, U1.N15 (VDD25_SATA), U1.N16 (VDD25_SATA)
unnamed: C126.+, L8.1, U10.1 (OUT)
unnamed: L11.2, USB_HOST.GND1, USB_HOST.GND2, USB_HOST.GND3, USB_HOST.GND4
unnamed: C137.1, L10.2, USB_HOST.2.1
unnamed: C135.+, L10.1, U11.1 (OUT)
unnamed: C173.2, C175.2, R68.1, U1.M15 (VDD12_SATA), U1.M16 (VDD12_SATA)
unnamed: C13.2, C14.2, C15.2, C16.2, R3.1, U1.M8 (VDD_DLL), U1.N9 (VDD_DLL), U1.P9 (VDD_DLL)
unnamed: C191.1, C193.2, R74.2, U1.W16 (VCC33_TVIN)
unnamed: C189.1, C190.2, R72.2, U1.W15 (VCC33_TVOUT)
unnamed: C184.1, C186.2, R71.2, U1.W17 (VDD25_TVIN)
unnamed: C196.2, U1.Y16 (VRN_TVIN)
unnamed: LCD_CON.33, R49.1
unnamed: LCD_CON.34, R50.1
unnamed: LED1.A, R32.2
unnamed: NAND_E.1, R19.2, U8.9 (#CE)
unnamed: L7.2, USB_OTG.GND1, USB_OTG.GND2, USB_OTG.GND3, USB_OTG.GND4
NALE: U1.M22 (NALE/SPI0_MISO/PC1), U8.17 (ALE)
NAND_DQS: R129.2, U8.35 (NC)
NCE0: NAND_E.2, U1.K23 (NCE0/PC4)
NCLE: U1.L23 (NCLE/SPI0_CLK/PC2), U8.16 (CLE)
NDQ0: R122.1, U1.H23 (NDQ0/SDC2_D0/PC8), U8.29 (I/O0)
NDQ1: R123.1, U1.H22 (NDQ1/SDC2_D1/PC9), U8.30 (I/O1)
NDQ2: R124.1, U1.G23 (NDQ2/SDC2_D2/PC10), U8.31 (I/O2)
NDQ3: R126.1, U1.G22 (NDQ3/SDC2_D3/PC11), U8.32 (I/O3)
NDQ4: U1.H21 (NDQ4/PC12), U8.41 (I/O4)
NDQ5: U1.H20 (NDQ5/PC13), U8.42 (I/O5)
NDQ6: U1.G21 (NDQ6/PC14), U8.43 (I/O6)
NDQ7: U1.G20 (NDQ7/PC15), U8.44 (I/O7)
NMI_N: GPIO-2.38, R27.1, U1.F5 (NMI#), U12.48 (IRQ/WAKEUP)
NRB0: R18.2, R128.1, R131.2, U1.J23 (NRB0/SDC2_CMD/PC6), U8.7 (R/#B)
NRBO/NRB1: R131.1, R132.1, U8.6 (NC)
NRE: U1.K22 (NRE#/PC5), U8.8 (#RE)
NWE: U1.M23 (NWE#/SPI0_MOSI/PC0), U8.18 (#WE)
ODT0: R15.2, U1.AA5 (ODT0)
ODT1: ODT1.1, U1.J3 (ODT1)
PB2/PWM0: LCD_CON.36, U1.A14 (PWM0/PB2)
PB3: GPIO-3.6, R49.2, U1.B14 (IR0_TX/SPDIF_MCLK/STANBYWFI/PB3)
PB4: GPIO-3.8, R50.2, U1.A13 (IR0_RX/PB4)
PB5: GPIO-3.10, U1.B13 (I2S_MCLK/AC97_MCLK/PB5)
PB6: GPIO-3.12, U1.A12 (I2S_BCLK/AC97_BCLK/PB6)
PB7: GPIO-3.14, U1.B12 (I2S_LRCK/AC97_SYNC/PB7)
PB8/SATA-PWR-EN: GPIO-3.16, R136.2, U1.A11 (I2S_DO0/AC97_DO/PB8)
PB10: GPIO-3.18, U1.C11 (I2S_DO2/PB10)
PB11: GPIO-3.20, U1.C10 (I2S_DO3/PB11)
PB12: GPIO-3.22, U1.C9 (I2S_DI/AC97_DI/SPDIF_DI/PB12)
PB13: GPIO-3.24, U1.B11 (SPI2_CS1/SPDIF_DO/PB13)
PB14: GPIO-3.26, RM25.3.1 (1), U1.A10 (JTAG_MS0/SPI2_CS0/PB14)
PB15: GPIO-3.28, RM25.2.1 (1), U1.B10 (JTAG_CK0/SPI2_CLK/PB15)
PB16: GPIO-3.30, U1.A9 (JTAG_DO0/SPI2_MOSI/PB16)
PB17: GPIO-3.32, RM25.1.1 (1), U1.B9 (JTAG_DI0/SPI2_MISO/PB17)
PC3/NCE1: GPIO-2.21, U1.L22 (NCE1/PC3), U8.10 (NC)
PC7/NRB1: GPIO-2.23, R121.2, R127.1, R132.2, U1.J22 (NRB1/SDC2_CLK/PC7), U8.4 (NC), U8.5 (NC)
PC16: GPIO-2.25, U1.M21 (NWP/PC16)
PC17: GPIO-2.27, U1.F23 (NCE2/PC17)
PC18: GPIO-2.29, U1.F22 (NCE3/PC18)
PC23: GPIO-2.31, U1.G19 (SPI0_CS0/PC23)
PC24/NQS: GPIO-2.33, R129.1, U1.F21 (NDQS/PC24)
PE0: GPIO-2.6, U1.E23 (TS0_CLK/CSI0_PCLK/PE0)
PE1: GPIO-2.8, U1.E22 (TS0_ERR/CSI0_MCLK/PE1)
PE2: GPIO-2.10, U1.D23 (TS0_SYNC/CSI0_HSYNC/PE2)
PE3: GPIO-2.12, U1.D22 (TS0_DVLD/CSI0_VSYNC/PE3)
PE4: GPIO-2.14, U1.C23 (TS0_D0/CSI0_D0/PE4)
PE5: GPIO-2.16, U1.C22 (TS0_D1/CSI0_D1/PE5)
PE6: GPIO-2.18, U1.B23 (TS0_D2/CSI0_D2/PE6)
PE7: GPIO-2.20, U1.B22 (TS0_D3/CSI0_D3/PE7)
PE8: GPIO-2.22, U1.A23 (TS0_D4/CSI0_D4/PE8)
PE9: GPIO-2.24, U1.A22 (TS0_D5/CSI0_D5/PE9)
PE10: GPIO-2.26, U1.B21 (TS0_D6/CSI0_D6/PE10)
PE11: GPIO-2.28, U1.A21 (TS0_D7/CSI0_D7/PE11)
PG0: GPIO-1.5, U1.F20 (TS1_CLK/CSI1_PCLK/SDC1_CMD/PG0)
PG1: GPIO-1.7, U1.E21 (TS1_ERR/CSI1_MLCK/SDC1_CLK/PG1)
PG2: GPIO-1.9, U1.E20 (TS1_SYNC/CSI1_HSYNC/SDC1_D0/PG2)
PG3: GPIO-1.11, U1.D21 (TS1_DVLD/CSI1_VSYNC/SDC1_D1/PG3)
PG4: GPIO-1.13, U1.D20 (TS1_D0/CSI1_D0/SDC1_D2/CSI0_D8/PG4)
PG5: GPIO-1.15, U1.C21 (TS1_D1/CSI1_D1/SDC1_D3/CSI0_D9/PG5)
PG6: GPIO-1.17, U1.E19 (TS1_D2/CSI1_D2/UART3_TX/CSI0_D10/PG6)
PG7: GPIO-1.19, U1.C20 (TS1_D3/CSI1_D3/UART3_RX/CSI0_D11/PG7)
PG8: GPIO-1.21, U1.D19 (TS1_D4/CSI1_D4/UART3_RTS/CSI0_D12/PG8)
PG9: GPIO-1.23, U1.C19 (TS1_D5/CSI1_D5/UART3_CTS/CSI0_D13/PG9)
PG10: GPIO-1.25, U1.D18 (TS1_D6/CSI1_D6/UART4_TX/CSI0_D14/PG10)
PG11: GPIO-1.27, U1.C18 (TS1_D7/CSI1_D7/UART4_RX/CSI0_D15/PG11)
PH0: GPIO-3.5, U1.A6 (LCD1_D0/ATAA0/UART3_TX/EINT0/CSI1_D0/PH0)
PH2/LED: GPIO-3.7, R32.1, U1.C6 (LCD1_D2/ATAA2/UART3_RTS/EINT2/CSI1_D2/P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)
PH7: GPIO-3.9, U1.B4 (LCD1_D7/ATAD3/UART5_RX/MS_CLK/EINT7/CSI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)
PH9: GPIO-3.11, U1.D4 (LCD1_D9/ATAD5/KP_IN1/MS_D1/EINT9/CSI1_D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)
PH10: GPIO-3.13, U1.A3 (LCD1_D10/ATAD6/KP_IN2/MS_D2/EINT10/CSI1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)
PH11/SDC3-DET#: GPIO-3.15, R38.2, RM15.4.1 (1), U1.B3 (LCD1_D11/ATAD7/KP_IN3/MS_D3/EINT11/CSI1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)
PH12: GPIO-3.17, U1.C3 (LCD1_D12/ATAD8/PS2_SCK1/EINT12/CSI1_D12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)
PH13: GPIO-3.19, U1.A2 (LCD1_D13/ATAD9/PS2_SDA1/SMC_RST/EINT13/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)
PH14: GPIO-3.21, U1.B2 (LCD1_D14/ATAD10/KP_IN4/SMC_VPPEN/EINT14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)
PH15: GPIO-3.23, U1.A1 (LCD1_D15/ATAD11/KP_IN5/SMC_VPPPP/EINT15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)
PH16: GPIO-3.25, U1.B1 (LCD1_D16/ATAD12/KP_IN6/SMC_DET/EINT16/C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)
PH17: GPIO-3.27, U1.C1 (LCD1_D17/ATAD13/KP_IN7/SMC_VCCEN/EINT17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)
PH18: GPIO-3.29, U1.C2 (LCD1_D18/ATAD14/KP_OUT0/SMC_SLK/EINT18/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)
PH19: GPIO-3.31, U1.D1 (LCD1_D19/ATAD15/KP_OUT1/SMC_SDA/EINT19/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)
PH20: GPIO-3.33, U1.D2 (LCD1_D20/ATAOE/CAN_TX/EINT20/CSI1_D20/P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)
PH21: GPIO-3.35, U1.D3 (LCD1_D21/ATADREQ/CAN_RX/EINT21/CSI1_D21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)
PH22: GPIO-3.37, U1.E1 (LCD1_D22/ATADACK/KP_OUT2/SDC1_CMD/CSI1_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)
PH23: GPIO-3.39, U1.E2 (LCD1_D23/ATACS0/KP_OUT3/SDC1_CLK/CSI1_D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)
PH24: GPIO-3.34, U1.E3 (LCD1_CLK/ATACS1/KP_OUT4/SDC1_D0/CSI1_PC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)
PH25: GPIO-3.36, U1.E4 (LCD1_DE/ATAIORDY/KP_OUT5/SDC1_D1/CSI1_F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)
PH26: GPIO-3.38, U1.F3 (LCD1_HSYNC/ATAIOR/KP_OUT6/SDC1_D2/CSI1_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)
PH27: GPIO-3.40, U1.F4 (LCD1_VSYNC/ATAIOW/KP_OUT7/SDC1_D3/CSI1_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)
PI0: GPIO-2.9, U1.A20 (GPS_CLK/PI0)
PI1: GPIO-2.11, U1.B20 (GPS_SIGN/PI1)
PI2: GPIO-2.13, U1.A19 (GPS_MAG/PI2)
PI3: GPIO-2.15, U1.B19 (PWM1/PI3)
PI10: GPIO-2.17, U1.C17 (SPI0_CS0/UART5_TX/EINT22/PI10)
PI11: GPIO-2.19, U1.D17 (SPI0_CLK/UART5_RX/EINT23/PI11)
PI14: GPIO-2.30, U1.C15 (PS2_SCK1/TCLKIN0/EINT26/SPI0_CS1/PI14)
PI15: GPIO-2.32, U1.D15 (PS2_SDA1/TCLKIN1/EINT27/SPI1_CS1/PI15)
RASN: RM18.2.2 (2), U2.J3 (#RAS), U3.J3 (#RAS)
RESET_N: C91.2, C94.2, GPIO-2.40, R28.1, U1.C14 (RESET#), U12.25 (PWROK)
SA0: RM17.4.2 (2), U2.N3 (A0), U3.N3 (A0)
SA1: RM19.4.2 (2), U2.P7 (A1), U3.P7 (A1)
SA2: RM18.4.2 (2), U2.P3 (A2), U3.P3 (A2)
SA3: RM20.2.2 (2), U2.N2 (A3), U3.N2 (A3)
SA4: RM16.2.2 (2), U2.P8 (A4), U3.P8 (A4)
SA5: RM20.4.2 (2), U2.P2 (A5), U3.P2 (A5)
SA6: RM17.2.2 (2), U2.R8 (A6), U3.R8 (A6)
SA7: RM20.1.2 (2), U2.R2 (A7), U3.R2 (A7)
SA8: RM16.3.2 (2), U2.T8 (A8), U3.T8 (A8)
SA9: RM19.2.2 (2), U2.R3 (A9), U3.R3 (A9)
SA10: RM21.3.2 (2), U2.L7 (A10/AP), U3.L7 (A10/AP)
SA11: RM17.3.2 (2), U2.R7 (A11), U3.R7 (A11)
SA12: RM19.1.2 (2), U2.N7 (A12/#BC), U3.N7 (A12/#BC)
SA13: RM16.1.2 (2), U2.T3 (A13), U3.T3 (A13)
SA14: RM19.3.2 (2), U2.T7 (NC/A14), U3.T7 (NC/A14)
SA15: RM16.4.2 (2), U2.M7 (NC), U3.M7 (NC)
SATA-RXM: C142.1, U1.U20 (RXM_SATA)
SATA-RXP: C143.1, U1.U21 (RXP_SATA)
SATA-TXM: C141.1, U1.T21 (TXM_SATA)
SATA-TXP: C140.1, U1.T20 (TXP_SATA)
SCK: R118.2, U1.V1 (SCK)
SCK#: R119.2, U1.V2 (SCK#)
SCKE0: RM20.3.1 (1), U1.N3 (SCKE0)
SCKE1: SCKE1.1, U1.J4 (SCKE1)
SCS0: RM17.1.2 (2), U2.L2 (#CS), U3.L2 (#CS)
SD0-CLK: SD/MMC1.5 (CLK/SCLK), U1.L20 (SDC0_CLK/UART0_TX/PF2)
SD0-CMD: R30.1, SD/MMC1.3 (CMD/DI), U1.L19 (SDC0_CMD/JTAG_DO1/PF3)
SD0-D0: RM14.2.2 (2), SD/MMC1.7 (DAT0/DO), U1.M19 (SDC0_D0/JTAG_DI1/PF1)
SD0-D1: RM14.3.2 (2), SD/MMC1.8 (DAT1/RES), U1.M20 (SDC0_D1/JTAG_MS1/PF0)
SD0-D2: RM14.1.2 (2), SD/MMC1.1 (DAT2/RES), U1.K19 (SDC0_D2/JTAG_CK1/PF5)
SD0-D3: R29.1, SD/MMC1.2 (CD/DAT3/CS), U1.K20 (SDC0_D3/UART0_RX/PF4)
SD0-DET#: RM14.4.2 (2), SD/MMC1.9 (CP_E), U1.B6 (LCD1_D1/ATAA1/UART3_RX/EINT1/CSI1_D1/PH1)
SDBG0: U1.P8 (SDBG0)
SDBG1: U1.R8 (SDBG1)
SDC3-CLK: SD/MMC2.5 (CLK/SCLK), U1.B18 (SDC3_CLK/PI5)
SDC3-CMD: R10.1, SD/MMC2.2 (CMD/DI), U1.A18 (SDC3_CMD/PI4)
SDC3-D0: RM15.2.1 (1), SD/MMC2.7 (DAT0/DO), U1.A17 (SDC3_D0/PI6)
SDC3-D1: RM15.1.1 (1), SD/MMC2.8 (DAT1/RES), U1.B17 (SDC3_D1/PI7)
SDC3-D2: RM15.3.1 (1), SD/MMC2.9 (DAT2/RES), U1.A16 (SDC3_D2/PI8)
SDC3-D3: R11.1, SD/MMC2.1 (CD/DAT3/CS), U1.B16 (SDC3_D3/PI9)
SDQ0: RM1.2.2 (2), U1.AB4 (SDQ0)
SDQ1: RM2.2.2 (2), U1.AC7 (SDQ1)
SDQ2: RM1.3.2 (2), U1.AC4 (SDQ2)
SDQ3: RM2.3.2 (2), U1.AB8 (SDQ3)
SDQ4: RM2.4.2 (2), U1.AC8 (SDQ4)
SDQ5: RM1.4.2 (2), U1.AB5 (SDQ5)
SDQ6: RM2.1.2 (2), U1.AB7 (SDQ6)
SDQ7: RM1.1.2 (2), U1.AC3 (SDQ7)
SDQ8: RM3.2.2 (2), U1.AB2 (SDQ8)
SDQ9: RM4.2.2 (2), U1.Y1 (SDQ9)
SDQ10: RM3.3.2 (2), U1.AC2 (SDQ10)
SDQ11: RM4.3.2 (2), U1.Y2 (SDQ11)
SDQ12: RM4.4.2 (2), U1.AA1 (SDQ12)
SDQ13: RM3.4.2 (2), U1.AB3 (SDQ13)
SDQ14: RM4.1.2 (2), U1.W2 (SDQ14)
SDQ15: RM3.1.2 (2), U1.AC1 (SDQ15)
SDQ16: RM5.2.2 (2), U1.N1 (SDQ16)
SDQ17: RM6.2.2 (2), U1.T2 (SDQ17)
SDQ18: RM5.3.2 (2), U1.N2 (SDQ18)
SDQ19: RM6.3.2 (2), U1.U1 (SDQ19)
SDQ20: RM6.4.2 (2), U1.U2 (SDQ20)
SDQ21: RM5.4.2 (2), U1.P1 (SDQ21)
SDQ22: RM6.1.2 (2), U1.T1 (SDQ22)
SDQ23: RM5.1.2 (2), U1.M2 (SDQ23)
SDQ24: RM7.2.2 (2), U1.L1 (SDQ24)
SDQ25: RM8.2.2 (2), U1.H1 (SDQ25)
SDQ26: RM7.3.2 (2), U1.L2 (SDQ26)
SDQ27: RM8.3.2 (2), U1.H2 (SDQ27)
SDQ28: RM8.4.2 (2), U1.J1 (SDQ28)
SDQ29: RM7.4.2 (2), U1.M1 (SDQ29)
SDQ30: RM8.1.2 (2), U1.G2 (SDQ30)
SDQ31: RM7.1.2 (2), U1.K2 (SDQ31)
SDQM0: R110.1, U2.E7 (DML)
SDQM1: R111.1, U2.D3 (DMU)
SDQM2: R112.1, U3.E7 (DML)
SDQM3: R113.1, U3.D3 (DMU)
SDQS0: R106.1, U2.F3 (DQSL)
SDQS0_N: R107.1, U2.G3 (#DQSL)
SDQS1: R108.1, U2.C7 (DQSU)
SDQS1_N: R109.1, U2.B7 (#DQSU)
SDQS2: R114.1, U3.F3 (DQSL)
SDQS2_N: R115.1, U3.G3 (#DQSL)
SDQS3: R116.1, U3.C7 (DQSU)
SDQS3_N: R117.1, U3.B7 (#DQSU)
SD_VCC: C103.2, C104.2, L4.2, SD/MMC1.4 (VDD)
SD_VCC1: C56.2, C115.2, L5.2, SD/MMC2.4 (VDD)
SEARCH_BUT: GPIO-1.12, R99.2, R100.1, SEARCH.1_1 (1)
SPI1-CLK: U1.E16 (EINT29/SPI1_CLK/UART2_CTS/PI17), UEXT2.9
SPI1-CS0: R84.1, U1.E17 (EINT28/SPI1_CS0/UART2_RTS/PI16), UEXT2.10
SPI1-MISO: U1.D14 (EINT31/SPI1_MISO/UART2_RX/PI19), UEXT2.7
SPI1-MOSI: U1.E15 (EINT30/SPI1_MOSI/UART2_TX/PI18), UEXT2.8
SPI2-CLK: U1.K21 (NCE5/SPI2_CLK/PC20), UEXT1.9
SPI2-CS0: R95.1, U1.L21 (NCE4/SPI2_CS0/PC19), UEXT1.10
SPI2-MISO: U1.J20 (NCE7/SPI2_MISO/PC22), UEXT1.7
SPI2-MOSI: U1.J21 (NCE6/SPI2_MOSI/PC21), UEXT1.8
SRST: R12.2, U1.AA6 (SRST)
TPX1: C127.2, LCD_CON.37, U1.Y22 (XP_TP)
TPX2: C129.2, LCD_CON.38, U1.AA22 (XN_TP)
TPY1: C131.2, LCD_CON.39, U1.Y23 (YP_TP)
TPY2: C132.2, LCD_CON.40, U1.AA23 (YN_TP)
TSD_CLK: R127.2, U8.40 (NC)
TSD_CMD: R128.2, U8.33 (NC)
TSD_D0: R122.2, U8.47 (NC)
TSD_D1: R123.2, U8.46 (NC)
TSD_D2: R124.2, R125.2, U8.45 (NC)
TSD_D3: R126.2, U8.27 (NC)
TVIN0: C181.2, GPIO-1.22, U1.AC18 (TVIN0)
TVIN1: C183.2, GPIO-1.24, U1.AB18 (TVIN1)
TVIN2: C185.2, GPIO-1.26, U1.AA17 (TVIN2)
TVIN3: C188.2, GPIO-1.28, U1.Y17 (TVIN3)
TVOUT3: GPIO-1.20, U1.AB17 (TVOUT3)
TWI0-SCK: GPIO-2.5, R75.1, U1.A15 (TWI0_SCK/PB0), U12.2 (SCK)
TWI0-SDA: GPIO-2.7, R76.1, U1.B15 (TWI0_SDA/PB1), U12.1 (SDA)
TWI1-SCK: R13.2, R82.1, U1.A8 (TWI1_SCK/PB18), U6.6 (SCL), UEXT2.5
TWI1-SDA: R14.1, R83.1, U1.B8 (TWI1_SDA/PB19), U6.5 (SDA), UEXT2.6
TWI2-SCK: R93.1, U1.C8 (TWI2_SCK/PB20), UEXT1.5
TWI2-SDA: R94.1, U1.C7 (TWI2_SDA/PB21), UEXT1.6
UART0-RX: D3.A, GPIO-2.34, R105.1, U1.B7 (UART0_RX/IR1_RX/PB23)
UART0-TX: GPIO-2.36, U1.A7 (UART0_TX/IR1_TX/PB22), UART0.2
UART6-RX: U1.D16 (SPI0_MISO/UART6_RX/EINT25/PI13), UEXT1.4
UART6-TX: U1.C16 (SPI0_MOSI/UART6_TX/EINT24/PI12), UEXT1.3
UART7-RX: U1.E13 (HSDA/UART7_RX/PS2_SDA0/PI21), UEXT2.4
UART7-TX: U1.E14 (HSCL/UART7_TX/PS2_SCK0/PI20), UEXT2.3
UBOOT_SEL: RECOVERY.2_1 (0), U1.W8 (UBOOT_SEL)
UDM0: U1.N20 (DM0), USB_OTG.D-
UDM1: U1.P20 (DM1), USB_HOST.1.2
UDM2: U1.R20 (DM2), USB_HOST.2.2
UDP0: U1.N21 (DP0), USB_OTG.D+
UDP1: U1.P21 (DP1), USB_HOST.1.3
UDP2: U1.R21 (DP2), USB_HOST.2.3
USB0-DRV: R44.2, U1.C12 (I2S_DO1/PB9), U9.4 (EN), U12.6 (N_VBUSEN)
USB0-IDDET: R52.2, U1.B5 (LCD1_D4/ATAD0/UART4_TX/EINT4/CSI1_D4/PH4), USB_OTG.ID
USB0-VBUSDET: C122.1, R42.1, R46.2, U1.C5 (LCD1_D5/ATAD1/UART4_RX/EINT5/CSI1_D5/PH5)
USB1-DRV: R47.2, U1.A4 (LCD1_D6/ATAD2/UART5_TX/MS_BS/EINT6/CSI1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), U10.4 (EN)
USB2-DRV: R54.2, U1.A5 (LCD1_D3/ATAIRQ/UART3_CTS/EINT3/CSI1_D3/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), U11.4 (EN)
V+: 1.5V.1, C1.1, C2.2, C3.2, C4.2, C5.2, C6.2, C7.2, C8.2, C9.2, C10.2, C11.2, C17.1, C28.2, C29.2, C30.2, C31.2, C32.2, C33.2, C34.2, C36.2, C37.2, C38.2, C39.2, C40.2, C41.2, C42.2, C43.2, C44.2, C45.2, C46.2, C47.2, C48.2, C49.2, C50.2, C51.2, C52.2, C53.2, C54.2, C55.2, C195.1, C198.1, C199.1, C224.2, C225.2, C226.2, C227.2, C228.2, C229.2, C230.2, C231.2, C232.2, L18.2, R1.2, R4.2, R6.2, R77.1, U1.G5 (VCC_DRAM), U1.H5 (VCC_DRAM), U1.L5 (VCC_DRAM), U1.M5 (VCC_DRAM), U1.R5 (VCC_DRAM), U1.T5 (VCC_DRAM), U1.W5 (VCC_DRAM), U1.W6 (VCC_DRAM), U1.W7 (VCC_DRAM), U1.Y6 (VCC_DRAM), U2.A1 (VDDQ), U2.A8 (VDDQ), U2.B2 (VDD), U2.C1 (VDDQ), U2.C9 (VDDQ), U2.D2 (VDDQ), U2.D9 (VDD), U2.E9 (VDDQ), U2.F1 (VDDQ), U2.G7 (VDD), U2.H2 (VDDQ), U2.H9 (VDDQ), U2.K2 (VDD), U2.K8 (VDD), U2.N1 (VDD), U2.N9 (VDD), U2.R1 (VDD), U2.R9 (VDD), U3.A1 (VDDQ), U3.A8 (VDDQ), U3.B2 (VDD), U3.C1 (VDDQ), U3.C9 (VDDQ), U3.D2 (VDDQ), U3.D9 (VDD), U3.E9 (VDDQ), U3.F1 (VDDQ), U3.G7 (VDD), U3.H2 (VDDQ), U3.H9 (VDDQ), U3.K2 (VDD), U3.K8 (VDD), U3.N1 (VDD), U3.N9 (VDD), U3.R1 (VDD), U3.R9 (VDD)
VCC: 3.3V.1, C68.2, C69.2, C70.2, C77.2, C78.2, C79.2, C80.2, C81.2, C82.2, C83.2, C84.2, C85.2, C89.2, C90.2, C117.2, C118.2, C119.2, C208.1, C211.1, C212.1, C219.1, D1.A, GPIO-1.3, GPIO-2.3, GPIO-3.3, L1.2, L2.2, L4.1, L5.1, L21.2, LAN.AG, LCD_CON.3, R10.2, R11.2, R13.1, R14.2, R18.1, R19.1, R21.1, R28.2, R29.2, R30.2, R31.2, R51.2, R52.1, R60.1, R72.1, R74.1, R75.2, R76.2, R82.2, R83.2, R84.2, R89.1, R93.2, R94.2, R95.2, R105.2, R121.1, R125.1, R130.1, RM9.1.1 (1), RM10.1.2 (2), RM10.2.2 (2), RM14.1.1 (1), RM14.2.1 (1), RM14.3.1 (1), RM14.4.1 (1), RM15.1.2 (2), RM15.2.2 (2), RM15.3.2 (2), RM15.4.2 (2), RM25.1.2 (2), RM25.2.2 (2), RM25.3.2 (2), U1.AB19 (HPVCCIN), U1.H8 (VCC), U1.H9 (VCC), U1.H10 (VCC), U1.H15 (VCC), U1.H19 (VCC_NAND), U1.J8 (VCC), U1.J9 (VCC), U1.J10 (VCC), U1.J14 (VCC), U1.J19 (VCC_NAND), U1.N19 (VCC_CARD), U1.W12 (VCC_LVDS), U1.W13 (VCC_LVDS), U1.W14 (VCC_LVDS), U6.8 (VCC), U7.37 (ANE), U7.38 (DUPLEX), U7.39 (SPEED), U7.41 (LDPS), U7.44 (MII/SNIB), U8.1 (NC), U8.12 (VCC), U8.24 (NC), U8.34 (NC), U8.37 (VCC), U8.39 (NC), UART0.1, UEXT1.1, UEXT2.1, VPS+.1, VR1.1 (VIN), VR1.3 (CE)
VCC/2: 1.2V_CPU.1, C57.2, C58.2, C59.2, C60.2, C61.2, C62.2, C159.1, C160.1, L13.2, U1.H11 (VDD_CPU), U1.H12 (VDD_CPU), U1.H13 (VDD_CPU), U1.H14 (VDD_CPU), U1.J12 (VDD_CPU), U1.J13 (VDD_CPU), U12.10 (DCDC2)
VCCINT: 1.2V_INT.1, C18.2, C19.2, C20.2, C21.2, C22.2, C23.2, C24.2, C25.2, C26.2, C27.2, C164.1, C165.1, L14.2, R3.2, R53.2, R68.2, U1.J15 (VDD_INT), U1.J16 (VDD_INT), U1.K9 (VDD_INT), U1.K10 (VDD_INT), U1.K15 (VDD_INT), U1.L8 (VDD_INT), U1.L9 (VDD_INT), U1.R9 (VDD_INT), U1.R10 (VDD_INT), U1.T8 (VDD_INT), U12.17 (DCDC3)
VDD: 2.5V.1, C220.1, C221.1, R23.2, R66.2, R71.1, VR1.5 (VOUT)
VDD_RTC: C101.2, C102.2, C172.1, U1.K8 (RTC_VDD), U12.28 (LDO1)
VGA-B: GPIO-1.35, RM24.3.2 (2), U1.AB16 (TVOUT1), VGA.2
VGA-G: GPIO-1.33, RM24.4.2 (2), U1.AC16 (TVOUT0), VGA.3
VGA-R: GPIO-1.37, RM24.2.2 (2), U1.AC17 (TVOUT2), VGA.1
VGA_HSYNC: FET3.3 (D), GPIO-1.29, R104.2, VGA.5
VGA_VSYNC: FET2.3 (D), GPIO-1.31, R41.2, VGA.4
VINT: C167.2, U12.26 (VINT)
VMIC: C148.2, R57.2, U1.AA21 (VMIC)
VOL+_BUT: GPIO-1.6, R96.2, R97.1, VOL+.1_1 (1)
VOL-_BUT: GPIO-1.8, R97.2, R98.1, VOL-.1_1 (1)
VPP: 3.0VA.1, C109.2, R69.1 (1.1), R91.1, U1.T19 (AVCC), U13.1 (EN)
WEN: RM18.1.2 (2), U2.L3 (#WE), U3.L3 (#WE)
XTALI: C99.2, Q3.2, U1.N23 (CLK24M_IN)
XTALI1: C72.2, Q1.2, U7.46 (X1)
XTALO: C100.2, Q3.1, U1.N22 (CLK24M_OUT)
XTALO1: C73.2, Q1.1, U7.47 (X2)

Notes on the sheet:
POWER SUPPLY CIRCUIT
LI-ION_BATTERY
2 x [2Gb DDR3 SDRAM (256Mx8)]
MicroSD
UEXTs
Buttons
USB-OTG
USB-HOSTs
NAND Flash
32Gb (4096M x 8bit)
GPIO EXTENSION
LCD EXTENSION
Ethernet
EEPROM
MAC Address
16 Kbit
(2048 x 8)
HDMI
SATA
Audio Out & Mic
LED
SD/MMC
This hardware design by Olimex LTD is licensed under a Creative Commons Attribution-ShareAlike 3.0 Unported License.
A10-A20-OLINUXINO-MICRO-4GB_rev_C
OLIMEX LTD 2013, PLOVDIV, BULGARIA
https://www.olimex.com
A10-A20-OLINUXINO-MICRO-4GB_rev_D
