OLIMEX/OLINUXINO/HARDWARE/A10-OLinuXino-LIME/3. Templates and more/A10-OLinuXino-LIME revision B SHIELD TEMPLATE KiCAD/A10_OLinuXino_Lime_Rev-B_SHIELD_TEMPLATE.sch

## KiCad design HARDWARE/A10-OLinuXino-LIME/3. Templates and more/A10-OLinuXino-LIME revision B SHIELD TEMPLATE KiCAD/A10_OLinuXino_Lime_Rev-B_SHIELD_TEMPLATE.sch (2022-06-17, an earlier design)

Schematic: A10_OLinuXino_Lime_Rev-B_SHIELD_TEMPLATE.sch

Parts:
GPIO-1, GPIO-2, GPIO-3: FL40YA-V36P-2X20-LF; A10_OLIMEXINO_LIME_SHIELD_1-YA-V36P-2X20-LF
GPIO-4: FL20YA-V36P-2X10-LF; A10_OLIMEXINO_LIME_SHIELD_1-YA-V36P-2X10-LF
LCD_CON1: FL40YA-V36P-2X20-LF; A10_OLIMEXINO_LIME_SHIELD_1-YA-V36P-2X20-LF
