OLIMEX/OLINUXINO/HARDWARE/iMX233-OLinuXino-Micro/2. Older hardware revisions/iMX233-OLinuXino-MICRO hardware revision C/iMX233-OLinuXino-Micro_Rev_C.sch

## EAGLE design HARDWARE/iMX233-OLinuXino-Micro/2. Older hardware revisions/iMX233-OLinuXino-MICRO hardware revision C/iMX233-OLinuXino-Micro_Rev_C.sch (2013-09-18, an earlier design)

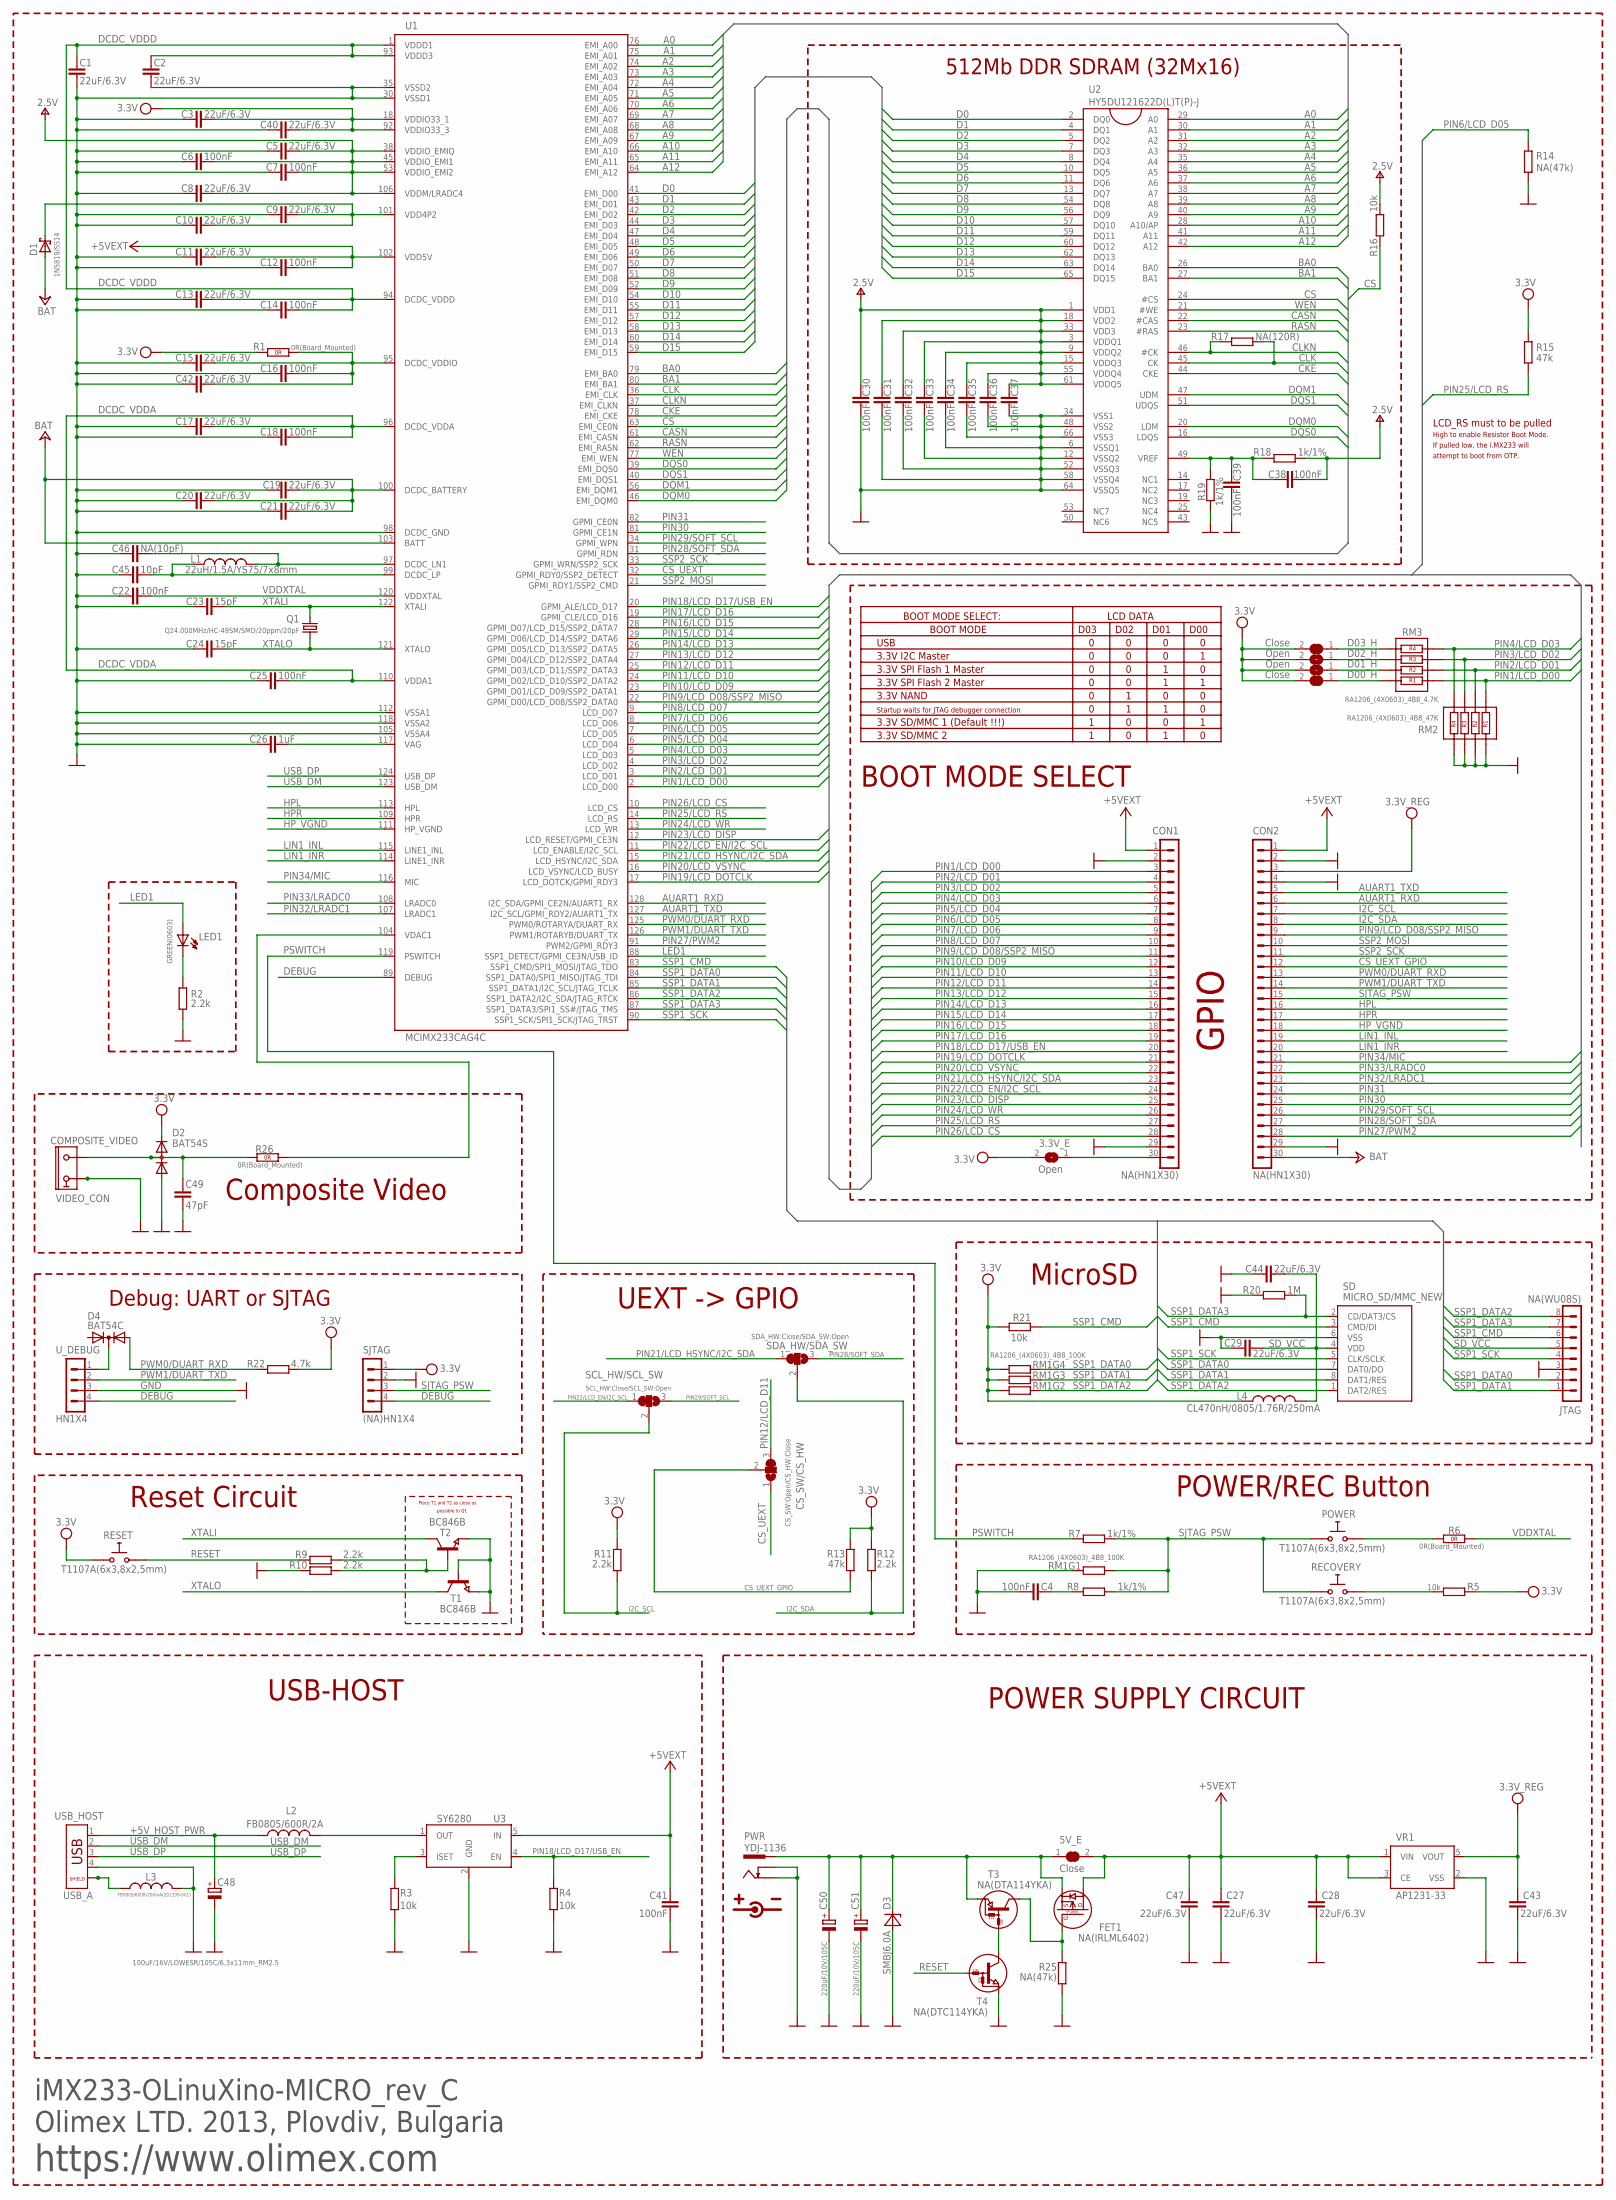
[picture p217: schematic iMX233-OLinuXino-Micro_Rev_C.sch]

Parts:
3.3V_E: Open; SJ_1_SMALLER
5V_E: Close; SJ-CLOSE
C1, C2, C5, C8, C9, C10, C11, C13, C15, C17, C19, C20, C21, C27, C28, C29, C40, C42, C43, C44, C47: 22uF/6.3V; C0603_DWS
C3: 22uF/6.3V; C1206
C4, C6, C7, C12, C14, C16, C18, C22, C25, C30, C31, C32, C33, C34, C35, C36, C37, C38, C39, C41: 100nF; C0603_DWS
C23, C24: 15pF; C0603_DWS
C26: 1uF; C0603_DWS
C45: 10pF; C0603_DWS
C46: NA(10pF); C0603_DWS
C48: 100uF/16V/LOWESR/105C/6.3x11mm_RM2.5; E2,5-6,3
C49: 47pF; C0603_DWS
C50, C51: 220uF/10V/105C; E2,5-6,3
COMPOSITE_VIDEO: VIDEO_CON; VIDEO_CINCH
CON1, CON2: NA(HN1X30); HN1X30
CS_SW/CS_HW: CS_SW:Open/CS_HW:Close; SJ_2_SMALL
D00_H, D03_H: Close; SJ_1_SMALLER
D1: 1N5819/SS14; MLL-41
D01_H, D02_H: Open; SJ_1_SMALLER
D2: BAT54S; SOT23C(BAT54S)
D3: SMBJ6.0A; DO214AA
D4: BAT54C; SOT23C
FET1: NA(IRLML6402); SOT23
JTAG: NA(WU08S); WU08S
L1: 22uH/1.5A/YS75/7x8mm; L7078
L2: FB0805/600R/2A; L0805_5MIL_DWS
L3: FB0805/600R/200mA(201209-601); L0805_5MIL_DWS
L4: CL470nH/0805/1.76R/250mA; L0805_5MIL_DWS
LED1: GREEN(0603); LED-0603
POWER: T1107A(6x3,8x2,5mm); SW-TAKT_6X3.5_SMD
PWR: YDJ-1136; PWR_JACK_UNI_MILLING
Q1: Q24.000MHz/HC-49SM/SMD/20ppm/20pF; HC49/SMD2_THIN
R1, R6, R26: 0R(Board_Mounted); 0603_0R
R2, R9, R10, R11, R12: 2.2k; R0603_5MIL_DWS
R3, R4, R5, R16, R21: 10k; R0603_5MIL_DWS
R7, R8, R18, R19: 1k/1%; R0603_5MIL_DWS
R13, R15: 47k; R0603_5MIL_DWS
R14, R25: NA(47k); R0603_5MIL_DWS
R17: NA(120R); R0603_5MIL_DWS
R20: 1M; R0603_5MIL_DWS
R22: 4.7k; R0603_5MIL_DWS
RECOVERY: T1107A(6x3,8x2,5mm); SW-TAKT_6X3.5_SMD
RESET: T1107A(6x3,8x2,5mm); SW-TAKT_6X3.5_SMD
RM1: RA1206_(4X0603)_4B8_100K; R_MATRIX_4
RM2: RA1206_(4X0603)_4B8_47K; R_MATRIX_4
RM3: RA1206_(4X0603)_4B8_4.7K; R_MATRIX_4
SCL_HW/SCL_SW: SCL_HW:Close/SCL_SW:Open; SJ_2_SMALL
SD: MICRO_SD/MMC_NEW; TFR/C-MEM-CON
SDA_HW/SDA_SW: SDA_HW:Close/SDA_SW:Open; SJ_2_SMALL
SJTAG: (NA)HN1X4; HN1X4
T1, T2: BC846B; SOT23
T3: NA(DTA114YKA); SOT-23
T4: NA(DTC114YKA); SOT-23
U1: MCIMX233CAG4C; TQFP128LD
U2: HY5DU121622D(L)T(P)-J; 66TSOP-II
U3: SY6280; SOT23-5
USB_HOST: USB_A; USB_PN87520_HOST_PTH
U_DEBUG: HN1X4
VR1: AP1231-33; SOT-23-5

Connections:
+5V: 5V_E.2, C11.2, C12.2, C27.1, C28.1, C41.1, C47.1, CON1.1, CON2.1, FET1.3 (D), U1.102 (VDD5V), U3.5 (IN), VR1.1 (VIN), VR1.3 (CE)
+5V_HOST_PWR: C48.+, L2.1, USB_HOST.1
+24V: C19.2, C20.2, C21.2, CON2.30, D1.A, U1.100 (DCDC_BATTERY), U1.103 (BATT)
A0: U1.76 (EMI_A00), U2.29 (A0)
A1: U1.75 (EMI_A01), U2.30 (A1)
A2: U1.74 (EMI_A02), U2.31 (A2)
A3: U1.73 (EMI_A03), U2.32 (A3)
A4: U1.72 (EMI_A04), U2.35 (A4)
A5: U1.71 (EMI_A05), U2.36 (A5)
A6: U1.70 (EMI_A06), U2.37 (A6)
A7: U1.69 (EMI_A07), U2.38 (A7)
A8: U1.68 (EMI_A08), U2.39 (A8)
A9: U1.67 (EMI_A09), U2.40 (A9)
A10: U1.66 (EMI_A10), U2.28 (A10/AP)
A11: U1.65 (EMI_A11), U2.41 (A11)
A12: U1.64 (EMI_A12), U2.42 (A12)
AUART1_RXD: CON2.6, U1.128 (I2C_SDA/GPMI_CE2N/AUART1_RX)
AUART1_TXD: CON2.5, U1.127 (I2C_SCL/GPMI_RDY2/AUART1_TX)
BA0: U1.79 (EMI_BA0), U2.26 (BA0)
BA1: U1.80 (EMI_BA1), U2.27 (BA1)
CASN: U1.61 (EMI_CASN), U2.22 (#CAS)
CKE: U1.78 (EMI_CKE), U2.44 (CKE)
CLK: R17.2, U1.36 (EMI_CLK), U2.45 (CK)
CLKN: R17.1, U1.37 (EMI_CLKN), U2.46 (#CK)
CS: R16.1, U1.63 (EMI_CE0N), U2.24 (#CS)
CS_UEXT: CS_SW/CS_HW.1, U1.32 (GPMI_RDY0/SSP2_DETECT)
CS_UEXT_GPIO: CON2.12, CS_SW/CS_HW.2, R13.1
D0: U1.41 (EMI_D00), U2.2 (DQ0)
D1: U1.43 (EMI_D01), U2.4 (DQ1)
D2: U1.42 (EMI_D02), U2.5 (DQ2)
D3: U1.44 (EMI_D03), U2.7 (DQ3)
D4: U1.47 (EMI_D04), U2.8 (DQ4)
D5: U1.48 (EMI_D05), U2.10 (DQ5)
D6: U1.49 (EMI_D06), U2.11 (DQ6)
D7: U1.50 (EMI_D07), U2.13 (DQ7)
D8: U1.51 (EMI_D08), U2.54 (DQ8)
D9: U1.52 (EMI_D09), U2.56 (DQ9)
D10: U1.54 (EMI_D10), U2.57 (DQ10)
D11: U1.55 (EMI_D11), U2.59 (DQ11)
D12: U1.57 (EMI_D12), U2.60 (DQ12)
D13: U1.58 (EMI_D13), U2.62 (DQ13)
D14: U1.60 (EMI_D14), U2.63 (DQ14)
D15: U1.59 (EMI_D15), U2.65 (DQ15)
DCDC_VDDA: C17.2, C18.2, C25.2, U1.96 (DCDC_VDDA), U1.110 (VDDA1)
DCDC_VDDD: C1.2, C2.2, C13.2, C14.2, U1.1 (VDDD1), U1.93 (VDDD3), U1.94 (DCDC_VDDD)
DCDC_VDDIO: C15.2, C16.2, C42.2, R1.2 (1.2), U1.95 (DCDC_VDDIO)
DEBUG: SJTAG.4, U1.89 (DEBUG), U_DEBUG.4
DQM0: U1.46 (EMI_DQM0), U2.20 (LDM)
DQM1: U1.56 (EMI_DQM1), U2.47 (UDM)
DQS0: U1.39 (EMI_DQS0), U2.16 (LDQS)
DQS1: U1.40 (EMI_DQS1), U2.51 (UDQS)
GND: C1.1, C2.1, C3.1, C4.2, C5.1, C6.1, C7.1, C8.1, C9.1, C10.1, C11.1, C12.1, C13.1, C14.1, C15.1, C16.1, C17.1, C18.1, C19.1, C20.1, C21.1, C22.1, C23.1, C24.1, C25.1, C26.1, C27.2, C28.2, C29.1, C30.1, C31.1, C32.1, C33.1, C34.1, C35.1, C36.1, C37.1, C39.1, C40.1, C41.2, C42.1, C43.2, C44.1, C45.1, C46.1, C47.2, C48.-, C49.2, C50.-, C51.-, COMPOSITE_VIDEO.GND1 (GND), COMPOSITE_VIDEO.GND1A (GND), COMPOSITE_VIDEO.GND1B (GND), COMPOSITE_VIDEO.GND1C (GND), COMPOSITE_VIDEO.GND1D (GND), COMPOSITE_VIDEO.GND1E (GND), COMPOSITE_VIDEO.GND2 (GND), COMPOSITE_VIDEO.GND3 (GND), COMPOSITE_VIDEO.GND3C (GND), COMPOSITE_VIDEO.GND3D (GND), COMPOSITE_VIDEO.GND3E (GND), COMPOSITE_VIDEO.GNG3A (GND), COMPOSITE_VIDEO.GNG3B (GND), CON1.2, CON1.29, CON2.2, CON2.4, CON2.29, D2.1 (A), D3.A, JTAG.3, L3.1, PWR.-, PWR.--, R2.1, R3.1, R4.1, R10.2, R14.1, R19.1, R20.2, R25.1, RM1.1.1 (1), RM2.1.2, RM2.2.2, RM2.3.2, RM2.4.2, SD.6 (VSS), SJTAG.2, T1.1 (B), T1.2 (E), T2.2 (E), T4.2 (E), U1.30 (VSSD1), U1.35 (VSSD2), U1.98 (DCDC_GND), U1.105 (VSSA4), U1.112 (VSSA1), U1.118 (VSSA2), U2.6 (VSSQ1), U2.12 (VSSQ2), U2.34 (VSS1), U2.48 (VSS2), U2.52 (VSSQ3), U2.58 (VSSQ4), U2.64 (VSSQ5), U2.66 (VSS3), U3.2 (GND), USB_HOST.4, U_DEBUG.3, VR1.2 (VSS)
HPL: CON2.16, U1.113 (HPL)
HPR: CON2.17, U1.109 (HPR)
HP_VGND: CON2.18, U1.111 (HP_VGND)
I2C_SCL: CON2.7, R11.1, SCL_HW/SCL_SW.2
I2C_SDA: CON2.8, R12.1, SDA_HW/SDA_SW.2
LED1: LED1.A, U1.88 (SSP1_DETECT/GPMI_CE3N/USB_ID)
LIN1_INL: CON2.19, U1.115 (LINE1_INL)
LIN1_INR: CON2.20, U1.114 (LINE1_INR)
unnamed: POWER.P$1 (0), R6.1 (1.1)
unnamed: 3.3V_E.1, CON1.30
unnamed: 5V_E.1, C50.+, C51.+, D3.C, FET1.2 (S), PWR.+, T3.2 (E)
unnamed: C49.1, COMPOSITE_VIDEO.IO, D2.3 (AK), R26.2 (1.2)
unnamed: L2.2, U3.1 (OUT)
unnamed: R3.2, U3.3 (ISET)
unnamed: C38.2, C39.2, R18.1, R19.2, U2.49 (VREF)
unnamed: R5.1, RECOVERY.P$1 (0)
unnamed: D4.3 (K), U_DEBUG.1
unnamed: FET1.1 (G), R25.2, T3.3 (C)
unnamed: T3.1 (B), T4.3 (C)
unnamed: C46.2, L1.2, U1.97 (DCDC_LN1)
unnamed: C45.2, L1.1, U1.99 (DCDC_LP)
unnamed: C26.2, U1.117 (VAG)
unnamed: C4.1, R8.1
unnamed: LED1.C, R2.2
unnamed: R9.1, R10.1, T2.1 (B)
unnamed: D03_H.1, RM3.4.1
unnamed: D02_H.1, RM3.3.1
unnamed: D01_H.1, RM3.2.1
unnamed: D00_H.1, RM3.1.1
unnamed: L3.2, USB_HOST.P$1 (5), USB_HOST.P$2 (6)
PIN1/LCD_D00: CON1.3, RM2.1.1, RM3.1.2, U1.2 (LCD_D00)
PIN2/LCD_D01: CON1.4, RM2.2.1, RM3.2.2, U1.3 (LCD_D01)
PIN3/LCD_D02: CON1.5, RM2.3.1, RM3.3.2, U1.4 (LCD_D02)
PIN4/LCD_D03: CON1.6, RM2.4.1, RM3.4.2, U1.5 (LCD_D03)
PIN5/LCD_D04: CON1.7, U1.6 (LCD_D04)
PIN6/LCD_D05: CON1.8, R14.2, U1.7 (LCD_D05)
PIN7/LCD_D06: CON1.9, U1.8 (LCD_D06)
PIN8/LCD_D07: CON1.10, U1.9 (LCD_D07)
PIN9/LCD_D08/SSP2_MISO: CON1.11, CON2.9, U1.22 (GPMI_D00/LCD_D08/SSP2_DATA0)
PIN10/LCD_D09: CON1.12, U1.23 (GPMI_D01/LCD_D09/SSP2_DATA1)
PIN11/LCD_D10: CON1.13, U1.24 (GPMI_D02/LCD_D10/SSP2_DATA2)
PIN12/LCD_D11: CON1.14, CS_SW/CS_HW.3, U1.25 (GPMI_D03/LCD_D11/SSP2_DATA3)
PIN13/LCD_D12: CON1.15, U1.27 (GPMI_D04/LCD_D12/SSP2_DATA4)
PIN14/LCD_D13: CON1.16, U1.26 (GPMI_D05/LCD_D13/SSP2_DATA5)
PIN15/LCD_D14: CON1.17, U1.29 (GPMI_D06/LCD_D14/SSP2_DATA6)
PIN16/LCD_D15: CON1.18, U1.28 (GPMI_D07/LCD_D15/SSP2_DATA7)
PIN17/LCD_D16: CON1.19, U1.19 (GPMI_CLE/LCD_D16)
PIN18/LCD_D17/USB_EN: CON1.20, R4.2, U1.20 (GPMI_ALE/LCD_D17), U3.4 (EN)
PIN19/LCD_DOTCLK: CON1.21, U1.17 (LCD_DOTCK/GPMI_RDY3)
PIN20/LCD_VSYNC: CON1.22, U1.16 (LCD_VSYNC/LCD_BUSY)
PIN21/LCD_HSYNC/I2C_SDA: CON1.23, SDA_HW/SDA_SW.1, U1.15 (LCD_HSYNC/I2C_SDA)
PIN22/LCD_EN/I2C_SCL: CON1.24, SCL_HW/SCL_SW.1, U1.11 (LCD_ENABLE/I2C_SCL)
PIN23/LCD_DISP: CON1.25, U1.12 (LCD_RESET/GPMI_CE3N)
PIN24/LCD_WR: CON1.26, U1.13 (LCD_WR)
PIN25/LCD_RS: CON1.27, R15.2, U1.14 (LCD_RS)
PIN26/LCD_CS: CON1.28, U1.10 (LCD_CS)
PIN27/PWM2: CON2.28, U1.91 (PWM2/GPMI_RDY3)
PIN28/SOFT_SDA: CON2.27, SDA_HW/SDA_SW.3, U1.31 (GPMI_RDN)
PIN29/SOFT_SCL: CON2.26, SCL_HW/SCL_SW.3, U1.34 (GPMI_WPN)
PIN30: CON2.25, U1.81 (GPMI_CE1N)
PIN31: CON2.24, U1.82 (GPMI_CE0N)
PIN32/LRADC1: CON2.23, U1.107 (LRADC1)
PIN33/LRADC0: CON2.22, U1.108 (LRADC0)
PIN34/MIC: CON2.21, U1.116 (MIC)
PSWITCH: R7.1, U1.119 (PSWITCH)
PWM0/DUART_RXD: CON2.13, D4.2 (A2), R22.2, U1.125 (PWM0/ROTARYA/DUART_RX)
PWM1/DUART_TXD: CON2.14, U1.126 (PWM1/ROTARYB/DUART_TX), U_DEBUG.2
RASN: U1.62 (EMI_RASN), U2.23 (#RAS)
RESET: R9.2, RESET.P$1 (0), T4.1 (B)
SD_VCC: C29.2, C44.2, JTAG.5, L4.2, SD.4 (VDD)
SJTAG_PSW: CON2.15, POWER.P$2 (1), R7.2, R8.2, RECOVERY.P$2 (1), RM1.1.2 (2), SJTAG.3
SSP1_CMD: JTAG.6, R21.1, SD.3 (CMD/DI), U1.83 (SSP1_CMD/SPI1_MOSI/JTAG_TDO)
SSP1_DATA0: JTAG.2, RM1.4.1 (1), SD.7 (DAT0/DO), U1.84 (SSP1_DATA0/SPI1_MISO/JTAG_TDI)
SSP1_DATA1: JTAG.1, RM1.3.1 (1), SD.8 (DAT1/RES), U1.85 (SSP1_DATA1/I2C_SCL/JTAG_TCLK)
SSP1_DATA2: JTAG.8, RM1.2.1 (1), SD.1 (DAT2/RES), U1.86 (SSP1_DATA2/I2C_SDA/JTAG_RTCK)
SSP1_DATA3: JTAG.7, R20.1, SD.2 (CD/DAT3/CS), U1.87 (SSP1_DATA3/SPI1_SS#/JTAG_TMS)
SSP1_SCK: JTAG.4, SD.5 (CLK/SCLK), U1.90 (SSP1_SCK/SPI1_SCK/JTAG_TRST)
SSP2_MOSI: CON2.10, U1.21 (GPMI_RDY1/SSP2_CMD)
SSP2_SCK: CON2.11, U1.33 (GPMI_WRN/SSP2_SCK)
USB_DM: U1.123 (USB_DM), USB_HOST.2
USB_DP: U1.124 (USB_DP), USB_HOST.3
V+: C5.2, C6.2, C7.2, C8.2, C30.2, C31.2, C32.2, C33.2, C34.2, C35.2, C36.2, C37.2, C38.1, R16.2, R18.2, U1.38 (VDDIO_EMIQ), U1.45 (VDDIO_EMI1), U1.53 (VDDIO_EMI2), U1.106 (VDDM/LRADC4), U2.1 (VDD1), U2.3 (VDDQ1), U2.9 (VDDQ2), U2.15 (VDDQ3), U2.18 (VDD2), U2.33 (VDD3), U2.55 (VDDQ4), U2.61 (VDDQ5)
VCC: 3.3V_E.2, C3.2, C40.2, D00_H.2, D01_H.2, D2.2 (K), D02_H.2, D03_H.2, L4.1, R1.1 (1.1), R5.2, R11.2, R12.2, R13.2, R15.1, R21.2, R22.1, RESET.P$2 (1), RM1.2.2 (2), RM1.3.2 (2), RM1.4.2 (2), SJTAG.1, U1.18 (VDDIO33_1), U1.92 (VDDIO33_3)
VDAC1: R26.1 (1.1), U1.104 (VDAC1)
VDD4P2: C9.2, C10.2, D1.K (C), U1.101 (VDD4P2)
VDDXTAL: C22.2, R6.2 (1.2), U1.120 (VDDXTAL)
VPP: C43.1, CON2.3, VR1.5 (VOUT)
WEN: U1.77 (EMI_WEN), U2.21 (#WE)
XTALI: C23.2, Q1.2, T2.3 (C), U1.122 (XTALI)
XTALO: C24.2, Q1.1, T1.3 (C), U1.121 (XTALO)

Notes on the sheet:
POWER SUPPLY CIRCUIT
Place T1 and T2 as close as
possible to Q1
Reset Circuit
512Mb DDR SDRAM (32Mx16)
MicroSD
Composite Video
POWER/REC Button
BOOT MODE SELECT
UEXT -> GPIO
BOOT MODE SELECT:
LCD DATA
BOOT MODE
D03
D02
D01
D00
USB
3.3V I2C Master
3.3V SPI Flash 1 Master
3.3V SPI Flash 2 Master
3.3V NAND
Startup waits for JTAG debugger connection
3.3V SD/MMC 1 (Default !!!)
3.3V SD/MMC 2
LCD_RS must to be pulled
High to enable Resistor Boot Mode.
If pulled low, the i.MX233 will
attempt to boot from OTP.
GPIO
Debug: UART or SJTAG
USB-HOST
iMX233-OLinuXino-MICRO_rev_C
Olimex LTD. 2013, Plovdiv, Bulgaria
https://www.olimex.com
