OLIMEX/OLINUXINO/HARDWARE/LCDs/A13-LCD10TS/A13-LCD10TS_Rev_A.sch

## EAGLE design HARDWARE/LCDs/A13-LCD10TS/A13-LCD10TS_Rev_A.sch (2014-10-23)

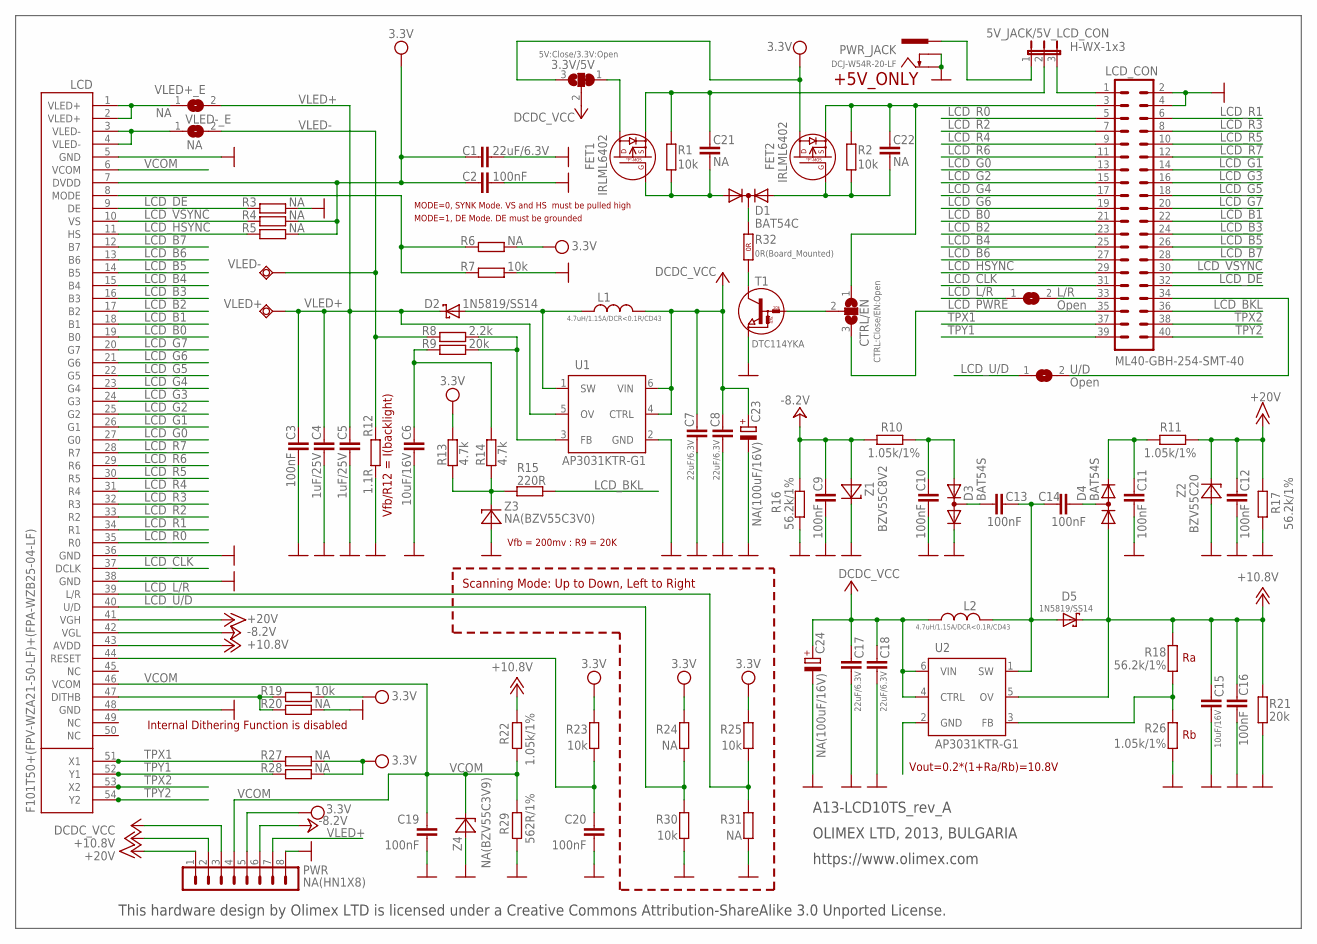
[picture p220: schematic A13-LCD10TS_Rev_A.sch]

Parts:
3.3V/5V: 5V:Close/3.3V:Open; SJ_2_SMALL_12_TIED
5V_JACK/5V_LCD_CON: H-WX-1x3; HN1X3-SMD
C1, C7, C8, C17, C18: 22uF/6.3V; C0805_5MIL_DWS
C2, C3, C9, C10, C11, C12, C13, C14, C16, C19, C20: 100nF; C0603_DWS
C4, C5: 1uF/25V; C0805_5MIL_DWS
C6, C15: 10uF/16V; C0805_5MIL_DWS
C21, C22: NA; C0603_DWS
C23, C24: NA(100uF/16V); C-SMD5X11-M
CTRL/EN: CTRL:Close/EN:Open; SJ_2_SMALL
D1: BAT54C; SOT23C
D2, D5: 1N5819/SS14; MLL-41
D3, D4: BAT54S; SOT23C(BAT54S)
FET1, FET2: IRLML6402; SOT23
L1, L2: 4.7uH/1.15A/DCR<0.1R/CD43; CD42(43)
L/R: Open; SJ
LCD: F101T50+(FPV-WZA21-50-LF)+(FPA-WZB25-04-LF); LCD10"_TOUCH(F101T50)
LCD_CON: ML40-GBH-254-SMT-40; ML40-MALE(GBH-254-SMT-40)
PWR: NA(HN1X8); HN1X8
PWR_JACK: DCJ-W54R-20-LF; PWR-JACK-SMD
R1, R2, R7, R19, R23, R25, R30: 10k; R0603_5MIL_DWS
R3, R4, R5, R6, R20, R24, R27, R28, R31: NA; R0603_5MIL_DWS
R8: 2.2k; R0603_5MIL_DWS
R9, R21: 20k; R0603_5MIL_DWS
R10, R11, R22, R26: 1.05k/1%; R0603_5MIL_DWS
R12: 1.1R; R0603_5MIL_DWS
R13, R14: 4.7k; R0603_5MIL_DWS
R15: 220R; R0603_5MIL_DWS
R16, R17, R18: 56.2k/1%; R0603_5MIL_DWS
R29: 562R/1%; R0603_5MIL_DWS
R32: 0R(Board_Mounted); 0603_0R
T1: DTC114YKA; SOT-23
U1, U2: AP3031KTR-G1; SOT23-6
U/D: Open; SJ
VLED+: TESTPAD120X40; SMD120X40
VLED+_E: NA; SJ
VLED-: TESTPAD120X40; SMD120X40
VLED-_E: NA; SJ
Z1: BZV55C8V2; MINI-MELF
Z2: BZV55C20; MINI-MELF
Z3: NA(BZV55C3V0); MINI-MELF
Z4: NA(BZV55C3V9); MINI-MELF

Connections:
+5V: 3.3V/5V.2, C7.2, C8.2, C17.2, C18.2, C23.+, C24.+, L1.1, L2.1, PWR.3, U1.4 (CTRL), U1.6 (VIN), U2.4 (CTRL), U2.6 (VIN)
+12V: C15.1, C16.1, D4.1 (A), D5.K (C), LCD.43 (AVDD), PWR.2, R18.2, R21.2, R22.1, U2.5 (OV)
+15V: C12.1, LCD.41 (VGH), PWR.1, R11.1, R17.2, Z2.1 (C)
-24V: C9.1, LCD.42 (VGL), PWR.6, R10.1, R16.2, Z1.2 (A)
GND: C1.2, C2.2, C3.2, C4.2, C5.2, C6.2, C7.1, C8.1, C9.2, C10.2, C11.2, C12.2, C15.2, C16.2, C17.1, C18.1, C19.2, C20.2, C23.-, C24.-, D3.2 (K), LCD.5 (GND), LCD.36 (GND), LCD.38 (GND), LCD.48 (GND), LCD_CON.2, LCD_CON.4, PWR.8, PWR_JACK.2 (-), PWR_JACK.3 (--), R3.1, R7.1, R12.2, R16.1, R17.1, R20.1, R21.1, R26.2, R29.2, R30.2, R31.2, T1.2 (E), U1.2 (GND), Z1.1 (C), Z2.2 (A), Z3.2 (A), Z4.2 (A)
LCD_B0: LCD.19 (B0), LCD_CON.21
LCD_B1: LCD.18 (B1), LCD_CON.22
LCD_B2: LCD.17 (B2), LCD_CON.23
LCD_B3: LCD.16 (B3), LCD_CON.24
LCD_B4: LCD.15 (B4), LCD_CON.25
LCD_B5: LCD.14 (B5), LCD_CON.26
LCD_B6: LCD.13 (B6), LCD_CON.27
LCD_B7: LCD.12 (B7), LCD_CON.28
LCD_BKL: LCD_CON.36, R15.1
LCD_CLK: LCD.37 (DCLK), LCD_CON.31
LCD_DE: LCD.9 (DE), LCD_CON.32, R3.2
LCD_G0: LCD.27 (G0), LCD_CON.13
LCD_G1: LCD.26 (G1), LCD_CON.14
LCD_G2: LCD.25 (G2), LCD_CON.15
LCD_G3: LCD.24 (G3), LCD_CON.16
LCD_G4: LCD.23 (G4), LCD_CON.17
LCD_G5: LCD.22 (G5), LCD_CON.18
LCD_G6: LCD.21 (G6), LCD_CON.19
LCD_G7: LCD.20 (G7), LCD_CON.20
LCD_HSYNC: LCD.11 (HS), LCD_CON.29, R5.2
LCD_L/R: L/R.1, LCD.39 (L/R), R25.2, R31.1
LCD_PWRE: CTRL/EN.3, LCD_CON.35
LCD_R0: LCD.35 (R0), LCD_CON.5
LCD_R1: LCD.34 (R1), LCD_CON.6
LCD_R2: LCD.33 (R2), LCD_CON.7
LCD_R3: LCD.32 (R3), LCD_CON.8
LCD_R4: LCD.31 (R4), LCD_CON.9
LCD_R5: LCD.30 (R5), LCD_CON.10
LCD_R6: LCD.29 (R6), LCD_CON.11
LCD_R7: LCD.28 (R7), LCD_CON.12
LCD_U/D: LCD.40 (U/D), R24.2, R30.1, U/D.1
LCD_VSYNC: LCD.10 (VS), LCD_CON.30, R4.2
unnamed: LCD.8 (MODE), R6.2, R7.2
unnamed: C14.2, D4.3 (AK)
unnamed: C22.1, CTRL/EN.1, FET2.2 (S), LCD_CON.3, R2.2
unnamed: C11.1, D4.2 (K), R11.2
unnamed: R8.1, R9.1, U1.3 (FB)
unnamed: C10.1, D3.1 (A), R10.2
unnamed: 5V_JACK/5V_LCD_CON.2, C21.1, FET1.2 (S), R1.2
unnamed: C22.2, D1.1 (A1), FET2.1 (G), R2.1
unnamed: C21.2, D1.2 (A2), FET1.1 (G), R1.1
unnamed: C13.1, D3.3 (AK)
unnamed: R32.2 (1.2), T1.3 (C)
unnamed: C6.1, R9.2, R14.2
unnamed: D2.A, L1.2, U1.1 (SW)
unnamed: R13.1, R14.1, R15.2, Z3.1 (C)
unnamed: L/R.2, LCD_CON.33
unnamed: CTRL/EN.2, T1.1 (B)
unnamed: LCD_CON.34, U/D.2
unnamed: 3.3V/5V.1, FET1.3 (D)
unnamed: D1.3 (K), R32.1 (1.1)
unnamed: 5V_JACK/5V_LCD_CON.3, LCD_CON.1
unnamed: LCD.1 (VLED+), LCD.2 (VLED+), VLED+_E.1
unnamed: 5V_JACK/5V_LCD_CON.1, PWR_JACK.1 (+)
unnamed: LCD.3 (VLED-), LCD.4 (VLED-), VLED-_E.1
unnamed: LCD.47 (DITHB), R19.2, R20.2
unnamed: C13.2, C14.1, D5.A, L2.2, U2.1 (SW)
unnamed: R18.1, R26.1, U2.3 (FB)
RESET: C20.1, LCD.44 (RESET), R23.2
TPX1: LCD.51 (X1), LCD.55 (X1_1), LCD_CON.37, R27.2
TPX2: LCD.53 (X2), LCD.57 (X2_2), LCD_CON.38
TPY1: LCD.52 (Y1), LCD.56 (Y1_1), LCD_CON.39, R28.2
TPY2: LCD.54 (Y2), LCD.58 (Y2_2), LCD_CON.40
VCC: 3.3V/5V.3, C1.1, C2.1, FET2.3 (D), LCD.7 (DVDD), PWR.5, R4.1, R5.1, R6.1, R13.2, R19.1, R23.1, R24.1, R25.1, R27.1, R28.1
VCOM: C19.1, LCD.6 (VCOM), LCD.46 (VCOM), PWR.4, R22.2, R29.1, Z4.1 (C)
VLED+: C3.1, C4.1, C5.1, D2.K (C), PWR.7, U1.5 (OV), VLED+.1, VLED+_E.2
VLED-: R8.2, R12.1, VLED-.1, VLED-_E.2

Notes on the sheet:
Vfb/R12 = I(backlight)
Vfb = 200mv : R9 = 20K
MODE=0, SYNK Mode. VS and HS must be pulled high
MODE=1, DE Mode. DE must be grounded
Scanning Mode: Up to Down, Left to Right
Vout=0.2*(1+Ra/Rb)=10.8V
Internal Dithering Function is disabled
+5V_ONLY
This hardware design by Olimex LTD is licensed under a Creative Commons Attribution-ShareAlike 3.0 Unported License.
A13-LCD10TS_rev_A
OLIMEX LTD, 2013, BULGARIA
https://www.olimex.com
