OLIMEX/OLINUXINO/HARDWARE/A64-OLinuXino/1. Latest hardware revision/A64-OLinuXino hardware revision G/A64-OlinuXino_Rev_G.sch

## KiCad design HARDWARE/A64-OLinuXino/1. Latest hardware revision/A64-OLinuXino hardware revision G/A64-OlinuXino_Rev_G.sch (2021-03-23)

Schematic: A64-OlinuXino_Rev_G.sch

Parts:
C1, C2, C3, C4, C6, C7, C8, C9, C11, C12, C13, C14, C15, C17, C18, C19, C20, C22, C23, C24, C25, C32, C33: 100nF\\10V/10%; C_0402_5MIL_DWS
C5, C10, C16, C21: 10uF\\6.3V/20%; C_0603_5MIL_DWS
C26: 10uF/6.3V/20%; C_0603_5MIL_DWS
C27: 1uF/10V/10%; C_0603_5MIL_DWS
C28, C29, C30, C31: 100nF/10V/10%; C_0402_5MIL_DWS
R1, R5, R8, R11, R12: 2k\\1%; R_0402_5MIL_DWS
R2: 100R\\1%; R_0402_5MIL_DWS
R3, R4: 22R; R_0402_5MIL_DWS
R6: NA; R_0402_5MIL_DWS
R7, R9, R10: 243R\\1%; R_0402_5MIL_DWS
R13, R14: NA(243R\\1%); R_0402_5MIL_DWS
U1: AllWinner-A64(FBGA396); FBGA396
U2, U3: K4B4G1646Q-HYK0(FBGA-96_256Mx16_DDR3-1600_11-11-1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; FBGA96(HYNIX_SAMSUNG_512MX16_DDR3)

Notes on the sheet:
DDR3:1GByte
Options: ======= 1. Use 2(DDR3 256Mx16 Memory chips)x4Gb = 1GByte, i.e. 2xH5TQ4G63MFR-PBC(or K4B4G1646Q-HYK0) -> Default 2. Use 2(DDR3 512Mx16 Memory chips)x8Gb = 2GBytes, i.e. 2xH5TC8G63AMR-PBA(or K4B8G1646Q-MYK0)
Note: ===== We have used a number of fully compatible, but different DDR3 memories due to supply unavailability. In such cases the memory part name in the schematic might remain outdated. It is recommended to always refer to the exact memory name printed on the component itself.
