OLIMEX/OLINUXINO/HARDWARE/A64-OLinuXino/1. Latest hardware revision/A64-OLinuXino hardware revision G/NAND Flash , eMMC, T-Card and Audio.sch

## KiCad design HARDWARE/A64-OLinuXino/1. Latest hardware revision/A64-OLinuXino hardware revision G/NAND Flash , eMMC, T-Card and Audio.sch (2021-03-23)

Schematic: NAND Flash , eMMC, T-Card and Audio.sch

Parts:
C34, C45, C46, C50, C51, C52, C58, C60, C65, C66, C82, C83, C86, C87: 100nF\\10V/10%; C_0402_5MIL_DWS
C35, C37, C44, C81: NA(100nF\\10V/10%); C_0402_5MIL_DWS
C36, C38, C43: NA(2.2uF\\6.3V/10%); C_0603_5MIL_DWS
C42: NA(22uF\\6.3V/20%); C_0603_5MIL_DWS
C47, C49, C53, C54, C57, C59, C63: 10uF\\6.3V/20%; C_0603_5MIL_DWS
C48, C62, C84, C85: 33pF\\50V/5%; C_0402_5MIL_DWS
C55: 1uF\\10V/10%; C_0603_5MIL_DWS
C56, C61: 2.2uF\\6.3V/10%; C_0603_5MIL_DWS
C64: 47uF\\6.3V/20%; C_0805_5MIL_DWS
C94: NA; C_0402_5MIL_DWS
GNDA1: TESTPAD; TESTPAD_40-ROUND
HEADPHONES/LINEOUT1: SCJ325P00XG0B02G
HPHONEOUTL/LINEOUTL1: Soldered(1-2);Opened(2-3); SJ_2_SMALL
HPHONEOUTR/LINEOUTR1: Soldered(1-2);Opened(2-3); SJ_2_SMALL
L1: NA(FB0805\\600R/2A); L_0805_5MIL_DWS
L2, L3, L4, L5: FB0805\\600R/2A; L_0805_5MIL_DWS
LINEINL/MICIN2: Opened(2-3);Soldered(1-2); SJ_2_SMALL
LINEINR/MICIN1: Opened(2-3);Soldered(1-2); SJ_2_SMALL
MIC/LINEIN1: SCJ325P00XG0B02G
MICRO_SD1: MICRO_SD(TFC-WPAPR-08); TFC-WPAPR-08
Mounting_hole1, Mounting_hole2, Mounting_hole3: Mounting_hole; Mounting_hole_3.3mm_with_5.5mm_pad
R15, R66, R68: NA(22R); R_0402_5MIL_DWS
R21, R23, R53, R56, R57, R62, R67: NA(10k); R_0402_5MIL_DWS
R25: 470R; R_0402_5MIL_DWS
R26, R29: 2k\\1%; R_0402_5MIL_DWS
R27: 200k\\1%; R_0402_5MIL_DWS
R30, R35: 100k; R_0402_5MIL_DWS
R31: 10k; R_0402_5MIL_DWS
R32: NA(1M); R_0402_5MIL_DWS
R33, R63, R64: 22R; R_0402_5MIL_DWS
R34: 0R(Board_Mounted); R_0402_5MIL_0R(Board_Mounted)
R36: 0R(Board_Mounted); R_0603_5MIL_0R(Board_Mounted)
R55: NA; R_0402_5MIL_DWS
R59: 47k; R_0402_5MIL_DWS
RM7: RA1206_(4x0603)_4B8_100k; RA1206_(4X0603)_4B8_xx
U1: AllWinner-A64(FBGA396); FBGA396
U5: NA(KLMAG2GEND-B031(FBGA153)); FBGA153_Pitch-0.5mm_Ball-0.25mm_Dimensions-11.50x13.00x0.80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
U12: NA(W25Q128FVSIG); SO-8_208mil
WP_Enable1: Opened; SJ

Notes on the sheet:
NAND Flash
CPVEE and VEE to be made as Kelvin connection.
Audio
T-Card
SPI Flash
Mounting Holes
eMMC
Present in -eXG
Present in -sXM
16G Bytes eMMC
16M Bytes SPI Flash
Was removed from the design
