OLIMEX/OLINUXINO/HARDWARE/A64-OLinuXino/1. Latest hardware revision/A64-OLinuXino hardware revision G/Power Supply, Extensions and MiPi-DSI .sch

## KiCad design HARDWARE/A64-OLinuXino/1. Latest hardware revision/A64-OLinuXino hardware revision G/Power Supply, Extensions and MiPi-DSI .sch (2021-03-23)

Schematic: Power Supply, Extensions and MiPi-DSI .sch

Parts:
1.1V_CPUS1, 1.1V_CPUX1, 1.1V_SYS1, 3.0V_RTC1, 3.3V1, 3.3V_MIPI1: TESTPAD; TP_SMD
3.3V/VCC-PE:2.8V1: Opened(2-3);Closed(1-2); SJ_2_SMALL_12_TIED
5V_E1: Opened; SJ
+1.8V1, +3.0VA1, +3.3VD1, +3.3VWiFiIO1, +5V_USBOTG1: TESTPAD; TP_SMD
C115, C117, C123, C127, C130, C132, C134, C155, C156, C158, C177, C186, C189, C191, C195, C197: 100nF\\10V/10%; C_0402_5MIL_DWS
C116, C121, C122, C124, C125, C126, C128, C129, C131, C133, C136, C138, C139, C140, C141, C143, C144, C145, C146, C147, C148, C149, C150, C151, C152, C153, C154, C157, C159, C161, C162, C164, C165, C166, C167, C168, C169, C170, C171, C172, C173, C175, C176, C178, C179, C188, C192, C194: 10uF\\6.3V/20%; C_0603_5MIL_DWS
C118, C119, C180: 47uF\\6.3V/20%; C_0805_5MIL_DWS
C120, C135, C137, C142, C160, C163, C181, C182, C190: 1uF\\10V/10%; C_0603_5MIL_DWS
C174: NA(10uF\\6.3V/20%); C_0603_5MIL_DWS
C183, C184: 22pF\\50V/5%; C_0402_5MIL_DWS
C185, C187: 33pF\\50V/5%; C_0402_5MIL_DWS
C193: NA(1nF\\50V/10%); C_0402_5MIL_DWS
CHGLED1: LED\\YELLOW/0603; LED_0603_KA
D1: SMBJ6.0A; DO214AA_1(K)-2(A)
D2, D3: 1N5822\\SS34/SMA; SMA-KA
D4: 1N5819(S4SOD-123); SOD-123_1C-2A_KA
DBG_UART1: HN1x3
DDR-VCC1: TESTPAD; TP_SMD
FET2: IRLML6402(SOT-23); SOT23
FUSE2: NA(5025); FUSE-5025
GND1: TESTPAD; TP_SMD
GPIO1: NA(HN2x20); HN2x20
GPIO_LED1: LED\\Red/0603; LED_0603_KA
HSIC1: NA(B4B-PH-K-S); B4B-PH-K-S
HSIC_E1: Opened; SJ
IPS1: TESTPAD; TP_SMD
L14, L19, L20: SWPA3015S1R5NT(1.5uH\\2.30A/DCR<0.1R/CD32); CD32
L15, L17, L18: SWPA4018S1R5NT(1.5uH\\3.35A/DCR<0.1R/CD43); CD42(43)
L16: 2.2uH\\3A/YS75/7x8; YS75_7X8MM
LIPO_BAT1: DW02R; LIPO_BAT-CON2DW02R
MIPI-DSI1: FPV-WZA21-20-LF
PWR1: PWRJ-2mm(YDJ-1134)
PWRLED1: LED\\Red/0603; LED_0603_KA
PWRON1: IT-1185AU2-160G-G-TR; IT1185AU2_V2
PWR_PC1: Opened(2-3);Soldered(1-2); SJ_2_SMALL
Q2: Q32.768kHz/12.5pF/2P/SMD1206; CM7V-T1A(Crystal_Package-1206_3.20x1.50x0.65mm)
Q3: Q24MHZ\\20pF/20ppm/2P/5x3.2mm; HCX-4S_2Pins_5.0x3.2mm_TEST
R28: NA(1k); R_0402_5MIL_DWS
R58, R89, R91, R92: 1k; R_0402_5MIL_DWS
R65, R121, R122, R123, R124, R125, R126, R129, R130: 22R; R_0402_5MIL_DWS
R73: NA(22R); R_0402_5MIL_DWS
R74, R75, R77, R82, R88, R90: 2.2k; R_0402_5MIL_DWS
R76, R79, R83, R85, R95: 10k; R_0402_5MIL_DWS
R78: 0.01R\\1%/1206; R_1206_5MIL_DWS
R80: 8.25k\\1%; R_0402_5MIL_DWS
R81: 1.1k\\1%; R_0402_5MIL_DWS
R84, R96, R97, R98, R127, R128, R131, R132: NA; R_0402_5MIL_DWS
R86, R87, R94: 0R(Board_Mounted); R_0402_5MIL_0R(Board_Mounted)
R93: 10M; R_0402_5MIL_DWS
R101, R102: NA(2.2k); R_0402_5MIL_DWS
R103: 100k; R_0402_5MIL_DWS
R104: NA(10k); R_0402_5MIL_DWS
RESET1: IT-1185AU2-160G-G-TR; IT1185AU2_V2
T1: WPM1481-6\\TR(DFN2X2-6L); DFN2x2-6L
U1: AllWinner-A64(FBGA396); FBGA396
U13: MT3608(SOT23-6); SOT23-6
U14: AXP803(QFN68_8x8mm); QFN68
UBOOT1: IT-1185AU2-160G-G-TR; IT1185AU2_V2
UEXT1: HN2x5
VCC-PC1: TESTPAD; TP_SMD
VCC-PL1: TESTPAD; TP_SMD

Notes on the sheet:
Power Supply
Crystal, RTC & Control
VCC-PL=3.3V
Vout=0.6*(1+Ra\Rb)
LI-ION_BATTERY 4.2V
VCC-PE=2.8V
UEXT
Extension
MiPi-DSI
+5VDC ONLY!!!
DDR3-VCC
DC5SET DDR3-VCC Floating 1.24V GND 1.50V VINT 1.36V
Notes: ===== 1. When SPI_Flash is populated, use PH10 for SPI_CS on the UEXT! In this case, R73 must be populated and R124 desoldered;
Raspberry Pi 3 Model B+ DISPLAY Connector Compatible!!!
