OLIMEX/OLINUXINO/HARDWARE/A64-OLinuXino/1. Latest hardware revision/A64-OLinuXino hardware revision G/USB&HDMI,WiFi&BT,Ethernet,LCD.sch

## KiCad design HARDWARE/A64-OLinuXino/1. Latest hardware revision/A64-OLinuXino hardware revision G/USB&HDMI,WiFi&BT,Ethernet,LCD.sch (2021-03-23)

Schematic: USB&HDMI,WiFi&BT,Ethernet,LCD.sch

Parts:
1.25_EXT1: TESTPAD; TP_SMD
ANT1: PCB_WIFI_ANT; BT_Antenna_Inverted_1ANT_2GND
ANT2: NA(U.FL-R-SMT-1); U.FL-R-SMT-1
C39: 100nF/10V/10%; C_0402_5MIL_DWS
C67, C72, C73, C74, C79, C80, C109, C110, C199, C200, C203, C206, C207, C208, C209, C210, C215, C216, C217: 100nF\\10V/10%; C_0402_5MIL_DWS
C68, C71, C75, C78, C201, C202: 47uF\\6.3V/20%; C_0805_5MIL_DWS
C69, C70, C76, C77: NA(47uF\\6.3V/20%); C_0805_5MIL_DWS
C88, C198: NA(24pF\\50V/5%); C_0402_5MIL_DWS
C89, C91: NA(10uF\\6.3V/20%); C_0603_5MIL_DWS
C90, C92: NA(100nF\\10V/10%); C_0402_5MIL_DWS
C93: 24pF\\50V/5%; C_0402_5MIL_DWS
C105: NA(10pF\\50V/5%); C_0402_5MIL_DWS
C106: NA(0.8pF\\C0402); C_0402_5MIL_DWS
C107: NA(1.5pF\\C0402); C_0402_5MIL_DWS
C196: 1nF\\2kV/10%/X7R; C_1206_5MIL_DWS_ISO
C204, C205, C214, C218, C219: 22uF\\6.3V/20%; C_0603_5MIL_DWS
C211: 1uF\\10V/10%; C_0603_5MIL_DWS
C212, C213: 33pF\\50V/5%; C_0402_5MIL_DWS
D5: 1N4007\\SMA; SMA-KA
FET1: BSS138(SOT23-3); SOT23
FUSE1: FSMD035; FUSE-1206
HDMI1: HDMI-SWM-19; HDMI-SWM-19-TEST
L6, L8, L21, L23, L24: FB0805\\600R/2A; L_0805_5MIL_DWS
L7, L9: NA(2.7nH\\L0402); L_0402_5MIL_DWS
L10: NA(3.3nH +-0.1nH LQP15MN3N3B02D); L_0402_5MIL_DWS
LAN1: TM211Q01FM22
LCD_CON1: FPV-WZA21-40-LF
PHYRST1: HN1x2(Opened); HN1x2_Jumper
Q4: Q25MHz\\20pF/20ppm/2P/5x3.2mm; HCX-4S_2Pins_5.0x3.2mm_TEST
R16: 0R; R_0402_5MIL_DWS
R17, R60: NA(0R); R_0402_5MIL_DWS
R18, R19, R72, R105, R109: 22R; R_0402_5MIL_DWS
R37, R40, R42, R52, R99, R106, R119: 10k; R_0402_5MIL_DWS
R38, R51: 4.7k; R_0402_5MIL_DWS
R39, R43, R44, R45: NA(510R); R_0402_5MIL_DWS
R41: 13k\\1%; R_0402_5MIL_DWS
R46: 27k; R_0402_5MIL_DWS
R47, R50, R70, R71: 2.2k; R_0402_5MIL_DWS
R48, R61: NA(10k); R_0402_5MIL_DWS
R49: 3.92k\\1%; R_0402_5MIL_DWS
R54: NA(22R); R_0402_5MIL_DWS
R107, R108, R110, R111, R112, R113, R114, R117: 1k; R_0402_5MIL_DWS
R115: 12.1k\\1%; R_0603_5MIL_DWS
R116: 100k; R_0402_5MIL_DWS
R118: NA; R_0402_5MIL_DWS
R120: 120R; R_0603_5MIL_DWS
RM1, RM15: RA0805_(4X0402)_22R; RA0805_(4X0402)_xx_BIGGEROUTPADS
RM8: RA0805_(4X0402)_4.7k; RA0805_(4X0402)_xx_BIGGEROUTPADS
RM9, RM12: NA(RA1206_(4x0603)_4B8_100k); RA1206_(4X0603)_4B8_xx
U1: AllWinner-A64(FBGA396); FBGA396
U4: AT24C16C-SSHM-T(SOIC-8_150mil); SOIC-8_150mil
U6, U9: SY6280AAC(SOT23-5); SOT-23-5
U7, U8, U10: NA(RCLAMP0524P(SLP2510P8)); SLP2510P8_TEST
U11: NA(RTL8723BS(ComboModule)); RL-SM02BD(RTL8723BS)
U15: KSZ9031RNXCC(QFN48_1DRILL(PADPITCH-0.5MM)); QFN48_1DRILL(PADPITCH-0.5MM)
USB1: USB_A_VERTICAL; USB_A_VERTICAL_PTH
USB-OTG1: MICRO_USB\\MISB-SWMM-5B_LF; USB-MICRO_MISB-SWMM-5B_LF
VR1: AMS1117(ADJ); SOT223

Notes on the sheet:
HDMI
USB
To DLDO1
To DLDO4
To ALDO2
WiFi&BT
Gigabit Ethernet or LCD
Ilim(A)=6800\Rset(Ohm)
Rset
Ilim=1.7A
Ilim=0.5A
RLC filter close to the MCU!
RLC filter close to the PHY!
RC filter close to the PHY!
Present in -xxxW
I2C Address: 0xA0
EEPROM
MAC Address
