OLIMEX/OLINUXINO/HARDWARE/A10-OLinuXino/A10-OLinuXino_Rev_A.sch

## KiCad design HARDWARE/STMP157-OLinuXino-LIME2/1. Latest hardware revision/STMP157-OLinuXino-LIME2_Rev_B1/HDMI, LCD and Ethernet.sch

Schematic: HDMI, LCD  and Ethernet.sch

Parts:
1.25_EXT1: TESTPAD; TP_SMD
C47, C48, C52, C63, C64, C72, C76, C79: 22uF/6.3V/20%; C_0603_5MIL_DWS
C49, C50: 33pF/50V/5%; C_0402_5MIL_DWS
C51, C61: 47uF/6.3V/20%/X5R/C0805; C_0805_5MIL_DWS
C53, C54, C55, C56, C57, C59, C60, C62, C65, C69, C70, C73, C74, C75, C77, C78, C80, C81, C82, C83, C84, C85, C123: 100nF/10V/10%; C_0402_5MIL_DWS
C58: 1uF/10V/10%/X5R/C0603; C_0603_5MIL_DWS
C66, C67: NA(24pF); C_0402_5MIL_DWS
C68: NA(24pF/50V/5%/COG); C_0402_5MIL_DWS
C71: 1nF/2kV/10%/X7R; C_1206_5MIL_DWS_ISO
D1: 1N4007/SMA; SMA-KA
FUSE1: FSMD035; FUSE-1206
HDMI1: HDMI-SWM-19
L2, L3, L4, L7: FB0805/600R/2A; L_0805_5MIL_DWS
L5, L6: NA(2.7nH/L0402); L_0402_5MIL_DWS
LAN1: TM211Q01FM22
LCD_CON1: PA-V16X-2X20-LF; GPH127SMT-02X20(PA-V16X-2X20-LF)
Q3: Q25MHz/20pF/20ppm/4P/3.2x2.5mm; TSX-3.2x2.5mm_GND(3)
R42, R63, R71, R72, R74, R75, R91, R92: 22R; R_0402_5MIL_DWS
R57: 120R; R_0603_5MIL_DWS
R58, R73, R80, R88, R89, R93: 10k; R_0402_5MIL_DWS
R59: 12.1k/1%; R_0603_5MIL_DWS
R60: 100k; R_0402_5MIL_DWS
R61, R64, R65, R66, R67, R68, R69, R76: 1k; R_0402_5MIL_DWS
R62, R81, R90: NA; R_0402_5MIL_DWS
R70, R77, R78, R82: 2.2k; R_0402_5MIL_DWS
R87: 5.6k; R_0402_5MIL_DWS
RM2: RA0805_(4X0402)_4.7k; RA0805_(4X0402)_xx_BIGGEROUTPADS
RM3, RM4: RA0805_(4X0402)_22R; RA0805_(4X0402)_xx_BIGGEROUTPADS
U1: STM32MP157CAA3x; LFBGA-448(Pitch-0.8mm_Pad-0.4mm_18x18x1.27mm)
U4: KSZ9031RNXCC(QFN48_1DRILL(PADPITCH-0.5MM)); QFN48_1DRILL(PADPITCH-0.5MM)
U5, U6, U7: NA(RCLAMP0524P(SLP2510P8)); SLP2510P8_TEST
U8: IT66121FN; QFN64_9x9mm_Pitch_0.5mm_65PAD_4.5mm
U9: AT24C16C-SSHM-T; SOIC-8_150mil
VR1: LD1117AG-AD-AA3-A-R; SOT223

Notes on the sheet:
HDMI
Gigabit Ethernet
RLC filter close to the MCU!
RLC filter close to the PHY!
RC filter close to the PHY!
LCD
I2C Address: 0x50-0x57
I2C Address: 0x4D
(SAI4_SD_A)
Notes: 1. Да се тества дали може CEC линията на HDMI да няма pull-up, понеже пише в datasheet-a на IT
