OLIMEX/OLINUXINO/HARDWARE/STMP157-OLinuXino-LIME2/1. Latest hardware revision/STMP157-OLinuXino-LIME2_Rev_B1/Power Supply.sch

## KiCad design HARDWARE/STMP157-OLinuXino-LIME2/1. Latest hardware revision/STMP157-OLinuXino-LIME2_Rev_B1/Power Supply.sch (2021-10-07)

Schematic: Power Supply.sch

Parts:
1.2V_VDDCORE1, 1.35V_DDR1, 3.3V1: TESTPAD; TP_SMD
5V_E1: Opened; SJ_1_SMALLER
+1.2V_HDMI1, +2.8V1, +5V_EXT1: TESTPAD; TP_SMD
BACKUP1: NA(HN1X2); HN1x2
C44, C86, C90, C91, C92, C93, C98, C101, C102, C103, C104, C105, C106, C107, C113, C115, C116, C117, C118, C119, C121, C134, C135, C147, C148: 10uF/6.3V/20%/X5R/C0603; C_0603_5MIL_DWS
C87, C88, C89: 47uF/6.3V/20%/X5R/C0805; C_0805_5MIL_DWS
C94: NA; C_0603_5MIL_DWS
C95, C108, C112, C114, C136, C137, C138, C139, C149, C150, C157, C163, C164, C166: 1uF/10V/10%/X5R/C0603; C_0603_5MIL_DWS
C96, C120, C125, C126, C140, C141, C142, C143, C144, C145, C146, C151, C152, C153, C154, C155, C156, C158, C159, C160, C161, C162, C165, C167: 100nF/10V/10%; C_0402_5MIL_DWS
C97: 1nF/50V/10%/X7R/C0402; C_0402_5MIL_DWS
C99, C100, C109, C111, C124: 4.7uF/6.3V/20%/X5R/C0603; C_0603_5MIL_DWS
CHGLED1: LED/YELLOW/0603; LED_0603_KA
D2: 1N5822/SS34/SMA; SMA-KA
D4: SMBJ6.0A; DO214AA_1(K)-2(A)
FET2, FET4: IRLML6402(SOT-23); SOT23
FET3: BSS138(SOT-23); SOT23
FUSE2: NA(5025); FUSE-5025
GND1: TESTPAD; TP_SMD
IPS1: TESTPAD; TP_SMD
L8: 2.2uH/3A/YS75/7x8; YS75_7X8MM
L9, L10, L11, L12, L17: 2.2uH/1.5A/DCR=72mR/20%/3.00x3.00x1.50mm/CD32(NR3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; CD32
L13: 4.7uH/0805/LQM21FN4R7M70L; L_0805_5MIL_DWS
LIPO_BAT1: DW02R; LIPO_BAT-CON2DW02R
PWR1: PWRJ-2mm(YDJ-1134)
PWRLED1: LED/Red/0603; LED_0603_KA
PWRON1: SIDE_WTCM-TR(3X4); SW-TAKT3X4
R44, R134: 0R/R0402; R_0402_5MIL_DWS
R45, R79, R107, R133: NA/R0402; R_0402_5MIL_DWS
R52, R101, R103, R109: 2.2k; R_0402_5MIL_DWS
R83: NA(22R); R_0402_5MIL_DWS
R97: 8.25k/1%; R_0402_5MIL_DWS
R98, R116: 1.1k/1%/R0402; R_0402_5MIL_DWS
R99: 200k/1%/R0402; R_0402_5MIL_DWS
R100: NA(10k); R_0402_5MIL_DWS
R102, R104, R136, R138: 10k; R_0402_5MIL_DWS
R105: 1k; R_0402_5MIL_DWS
R106, R108, R135: 22R; R_0402_5MIL_DWS
R110, R111: 1.5k; R_0402_5MIL_DWS
R112: 12.4k/1%/R0402; R_0402_5MIL_DWS
R113: 10k/1%/R0402; R_0402_5MIL_DWS
R115: 4.99k/1%/R0402; R_0402_5MIL_DWS
R128: 0.03R/1%/R1206; R_1206_5MIL_DWS
R137: 1M; R_0402_5MIL_DWS
RESET1: SIDE_WTCM-TR(3X4); SW-TAKT3X4
T1: LMUN2211LT1G(SOT-23); SOT23
U1: STM32MP157CAA3x; LFBGA-448(Pitch-0.8mm_Pad-0.4mm_18x18x1.27mm)
U10: MT3608(SOT23-6); SOT23-6
U11, U17: SY8089AAAC(SOT23-5); SOT-23-5
U18: AXP209(QFN-48); QFN48-6x6mm-OLIMEX_V2
U19: RT9026GFP(MSOP-10); MSOP-10-EP_Pitch-0.5mm_3.00x3.00x1.00mm
U20: MCP121T475I-TT(SOT23-3); SOT-23
VBAT-RTC1: TESTPAD; TP_SMD
VBUS1: TESTPAD; TP_SMD
VDD-FLASH1: TESTPAD; TP_SMD
VDD_USB1: TESTPAD; TP_SMD
VR2: AP1231-3.3V(SOT23-5); SOT-23-5

Notes on the sheet:
Vout=0.6*(1+Ra/Rb)
+5VDC ONLY!!!
Vtt_DDR 0.675V
Power Supply
LDO1 Voltage
1.2V
I2C Address: 0x34
GND
1.3V
3.3V
VINT
LDO1SET
1.35V
Vout=0.6*(1+Rc/Rd)
LI-ION_BATTERY 4.2V
1.8/3.3V
Default: 3.3V
