OLIMEX/OLINUXINO/HARDWARE/STMP157-OLinuXino-LIME2/1. Latest hardware revision/STMP157-OLinuXino-LIME2_Rev_B1/STMP157-OLinuXino-LIME2_Rev_B1.sch

## KiCad design HARDWARE/STMP157-OLinuXino-LIME2/1. Latest hardware revision/STMP157-OLinuXino-LIME2_Rev_B1/STMP157-OLinuXino-LIME2_Rev_B1.sch (2021-10-07)

Schematic: STMP157-OLinuXino-LIME2_Rev_B1.sch

Parts:
C1, C23, C24, C34, C35: 10uF/6.3V/20%/X5R/C0603; C_0603_5MIL_DWS
C2, C4, C6: 1uF/10V/10%/X5R/C0603; C_0603_5MIL_DWS
C3, C5, C7, C8, C10, C14, C15, C16, C17, C18, C19, C20, C21, C22, C25, C26, C27, C28, C29, C30, C31, C32, C33, C36, C37, C38, C39, C186, C187, C188, C189, C190: 100nF/10V/10%; C_0402_5MIL_DWS
C9, C11, C12, C13: NA(100nF/10V/10%); C_0402_5MIL_DWS
C122: 22uF/6.3V/20%; C_0603_5MIL_DWS
R1, R5, R6, R7: NA(2k/1%); R_0402_5MIL_DWS
R2, R3: 0R_Board_Mounted; R_0402_5MIL_0R(Board_Mounted)
R4, R8, R13: 243R/1%; R_0402_5MIL_DWS
R9, R14: NA(243R/1%); R_0402_5MIL_DWS
R10, R132: 10k; R_0402_5MIL_DWS
R11: 100R/1%; R_0402_5MIL_DWS
R12, R47: 0R/R0402; R_0402_5MIL_DWS
R15, R16, R17, R18, R19, R20, R21, R22, R23, R24, R25, R26, R27, R28, R29, R30, R31, R32, R33, R34, R35, R36, R37, R38, R39: 56R/1%; R_0402_5MIL_DWS
U1: STM32MP157CAA3x; LFBGA-448(Pitch-0.8mm_Pad-0.4mm_18x18x1.27mm)
U2, U3: K4B4G1646D-BYK0; FBGA96(HYNIX_SAMSUNG_512MX16_DDR3)

Notes on the sheet:
DDR3L:1GByte
Note: ===== We have used a number of fully compatible, but different DDR3 memories due to supply unavailability. In such cases the memory part name in the schematic might remain outdated. It is recommended to always refer to the exact memory name printed on the component itself.
