OLIMEX/OLINUXINO/HARDWARE/STMP157-OLinuXino-LIME2/1. Latest hardware revision/STMP157-OLinuXino-LIME2_Rev_B1/USB, CAN and Extensions.sch

## KiCad design HARDWARE/STMP157-OLinuXino-LIME2/1. Latest hardware revision/STMP157-OLinuXino-LIME2_Rev_B1/USB, CAN and Extensions.sch (2021-10-07)

Schematic: USB, CAN and Extensions.sch

Parts:
3.3V/5.0V1: Opened(2-3)/Closed(1-2); SJ_2_SMALL_12_TIED
C168, C169, C170, C172, C175, C176: 47uF/6.3V/20%/X5R/C0805; C_0805_5MIL_DWS
C173, C181, C184, C185: 100nF/10V/10%; C_0402_5MIL_DWS
C174, C178, C179, C180, C182, C183: NA(47uF/6.3V/20%); C_0805_5MIL_DWS
CAN1: TB3-3.5mm
CAN_T1: Opened; SJ_1_SMALLER
D3: 1N5819S4(SOD123); SOD-123_1C-2A_KA
DBG1: HN1x3
GPIO4: PA-V16X-2X10-LF; GPH127SMT-02X10(PA-V16X-2X10-LF)
GPIO-1, GPIO-2, GPIO-3: PA-V16X-2X20-LF; GPH127SMT-02X20(PA-V16X-2X20-LF)
L14, L15, L16: FB0805/600R/2A; L_0805_5MIL_DWS
LED1: LED/Red/0603; LED_0603_KA
LIME2_PLATFORM1: LIME2_PLATFORM
R41: 2.2k; R_0402_5MIL_DWS
R114: 3.01k/1%; R_0402_5MIL_DWS
R117, R118, R119, R121, R130, R140: 10k; R_0402_5MIL_DWS
R120, R123: NA; R_0402_5MIL_DWS
R122: 120R/1206; R_1206_5MIL_DWS
R124: 13k/1%; R_0402_5MIL_DWS
R125, R126: 6.81k/1%; R_0402_5MIL_DWS
R129: 330R; R_0402_5MIL_DWS
R131: 1k; R_0402_5MIL_DWS
U1: STM32MP157CAA3x; LFBGA-448(Pitch-0.8mm_Pad-0.4mm_18x18x1.27mm)
U12, U13, U14: SY6280AAC(SOT23-5); SOT-23-5
U15: SIT1050T(SOIC-8_150mil); SOIC-8_150mil
USB1, USB2: USB_A_VERTICAL; USB_A_VERTICAL_PTH
USB-OTG1: USB-OTG(MSB-SW-5AB-LF); USB_MINI_9PIN_SD

Notes on the sheet:
USB
Ilim(A)=6800/Rset(Ohm)
Rset
Ilim=1A
Ilim=0.5A
User Led
CAN
