OLIMEX/OLINUXINO/HARDWARE/STMP157-OLinuXino-LIME2/1. Latest hardware revision/STMP157-OLinuXino-LIME2_Rev_B1/eMMC, SPI-Flash, T-Card and Boot.sch

## KiCad design HARDWARE/STMP157-OLinuXino-LIME2/1. Latest hardware revision/STMP157-OLinuXino-LIME2_Rev_B1/eMMC, SPI-Flash, T-Card and Boot.sch (2021-10-07)

Schematic: eMMC, SPI-Flash, T-Card and Boot.sch

Parts:
BOOT0_VDD1, BOOT2_VDD1: Soldered; SJ_1_SMALLER
BOOT1_VDD1: Opened; SJ_1_SMALLER
C40: 10nF/50V/10%/X7R/C0402; C_0402_5MIL_DWS
C41: NA(100nF/10V/10%); C_0402_5MIL_DWS
C42, C43: 24pF/50V/5%/COG; C_0402_5MIL_DWS
C46: 47uF/6.3V/20%/X5R/C0805; C_0805_5MIL_DWS
C127: 100nF/10V/10%/X5R/C0402; C_0402_5MIL_DWS
CR1: F535L-24(24MHz/50ppm/5x3.2mm); 5032-4P_HCX-3S
D5: 1N5819S4(SOD123); SOD-123_1C-2A_KA
FID1, FID2, FID3, FID4, FID5, FID6: Fiducial; Fiducial1x3
Flash_Con1: DF12(3.0)-40DS-0.5V(86); Flash_Con[DF12(3.0)-40DS-0.5V(86)]
L1: FB0805/600R/2A; L_0805_5MIL_DWS
MICRO_SD1: MICRO_SD(TFC-WPAPR-08); TFC-WPAPR-08
Q1: Q32.768kHz/12.5pF/2P/SMD1206; CM7V-T1A(Crystal_Package-1206_3.20x1.50x0.65mm)
R40: NA; R_0402_5MIL_DWS
R43, R46: 0R/R0402; R_0402_5MIL_DWS
R48, R49, R50: 1k; R_0402_5MIL_DWS
R51, R53, R55: 10k; R_0402_5MIL_DWS
R54: 100k; R_0402_5MIL_DWS
R139: 22R; R_0402_5MIL_DWS
RM1: RA1206_(4x0603)_4B8_100k; RA1206_(4X0603)_4B8_xx
U1: STM32MP157CAA3x; LFBGA-448(Pitch-0.8mm_Pad-0.4mm_18x18x1.27mm)

Notes on the sheet:
T-Card
PWR_ONRST = PWR_ON && NRST
eMMC/NAND/SPI-Flash
NAND -> SLC NAND Flash on FMC
Forced UART/USB Boot. USB high-speed device, or USART2/3/6 and UART4/5/7/8 on default pins.
SD-Card on SDMMC1 (default)
eMMC on SDMMC2 (default)
NAND -> Serial NAND Flash on QUADSPI
NOR -> Serial NOR Flash on QUADSPI
Reserved (NoBoot)
Boot0
Boot1
Boot2
Boot Mode
Boot Selection
Fiducials
