OLIMEX/OLINUXINO/SOFTWARE/iMX233/MOD-LCD6610/bmp.h

/*************************************************************************
 *
 *	Author: Slavcho Tomov
 *
 *    (c) Copyright Olimex 2006
 *
 **************************************************************************/
const unsigned char bmp [] = {
				0x44, 0x65, 0x68, 0x46, 0x84, 0x57, 0x34, 0x64, 0x68, 0x56, 0x83, 0x56, 0x45, 0x64, 0x57, 0x45, 0x74, 0x57, 0x45, 0x74, 0x57, 0x56, 0x75, 0x78, 
				0x56, 0x84, 0x68, 0x57, 0x85, 0x68, 0x45, 0x74, 0x68, 0x45, 0x74, 0x57, 0x46, 0x84, 0x57, 0x35, 0x74, 0x57, 0x46, 0x84, 0x68, 0x45, 0x74, 0x57, 
				0x45, 0x73, 0x57, 0x34, 0x63, 0x46, 0x45, 0x74, 0x68, 0x56, 0x84, 0x57, 0x45, 0x74, 0x67, 0x46, 0x84, 0x68, 0x46, 0x84, 0x68, 0x46, 0x85, 0x69, 
				0x56, 0x95, 0x69, 0x57, 0x95, 0x79, 0x57, 0x95, 0x69, 0x67, 0x95, 0x79, 0x57, 0x96, 0x79, 0x57, 0x95, 0x68, 0x56, 0x85, 0x68, 0x67, 0x96, 0x79, 
				0x56, 0x84, 0x57, 0x56, 0x75, 0x68, 0x45, 0x76, 0x67, 0x84, 0x38, 0x42, 0x84, 0x38, 0x42, 0x83, 0x27, 0x32, 0x73, 0x27, 0x32, 0x73, 0x27, 0x32, 
				0x83, 0x28, 0x32, 0x73, 0x28, 0x32, 0x83, 0x28, 0x32, 0x83, 0x28, 0x32, 0x83, 0x28, 0x42, 0x84, 0x28, 0x42, 0x84, 0x28, 0x42, 0x84, 0x28, 0x42, 
				0x84, 0x28, 0x42, 0x84, 0x28, 0x42, 0x84, 0x28, 0x42, 0x84, 0x28, 0x42, 0x84, 0x28, 0x42, 0x84, 0x28, 0x42, 0x84, 0x28, 0x42, 0x84, 0x28, 0x42, 
				0x84, 0x28, 0x42, 0x84, 0x28, 0x42, 0x84, 0x28, 0x42, 0x84, 0x28, 0x42, 0x84, 0x28, 0x42, 0x84, 0x29, 0x42, 0x94, 0x29, 0x42, 0x94, 0x29, 0x42, 
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
				0x57, 0x95, 0x68, 0x46, 0x95, 0x69, 0x46, 0x85, 0x79, 0x57, 0x95, 0x79, 0x57, 0x94, 0x68, 0x68, 0x97, 0x8a, 0x67, 0x95, 0x67, 0x67, 0x85, 0x68, 
				0x67, 0x95, 0x68, 0x45, 0x75, 0x68, 0x57, 0x96, 0x56, 0x83, 0x28, 0x32, 0x83, 0x28, 0x32, 0x83, 0x28, 0x32, 0x83, 0x28, 0x32, 0x83, 0x28, 0x42, 
				0x84, 0x28, 0x42, 0x84, 0x28, 0x42, 0x84, 0x28, 0x42, 0x84, 0x28, 0x42, 0x84, 0x28, 0x42, 0x84, 0x28, 0x42, 0x84, 0x28, 0x42, 0x84, 0x28, 0x42, 
				0x84, 0x29, 0x42, 0x94, 0x29, 0x42, 0x94, 0x29, 0x42, 0x94, 0x29, 0x42, 0x94, 0x29, 0x42, 0x94, 0x29, 0x42, 0x94, 0x29, 0x42, 0x94, 0x29, 0x42, 
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
				
};
