OLIMEX/OLINUXINO/SOFTWARE/A20/ANDROID A20-OLINUXINO-TOOLS/A20-OLINUXINO-TOOLS/src/olimex/a20/tools/MainActivity.java

package olimex.a20.tools;

import java.util.Locale;

import olimex.a20.tools.fragments.GPIOFragment;
import olimex.a20.tools.fragments.I2CFragment;
import olimex.a20.tools.fragments.UARTFragment;
import olimex.a20.tools.jni.I2C;
import olimex.a20.tools.jni.UART;
import olimex.a20.uart.R;

import android.app.ActionBar;
import android.app.FragmentTransaction;
import android.app.ProgressDialog;
import android.os.Bundle;
import android.support.v4.app.Fragment;
import android.support.v4.app.FragmentActivity;
import android.support.v4.app.FragmentManager;
import android.support.v4.app.FragmentPagerAdapter;
import android.support.v4.view.ViewPager;
import android.view.Menu;
import android.view.MenuItem;

public class MainActivity extends FragmentActivity implements
		ActionBar.TabListener {

	SectionsPagerAdapter mSectionsPagerAdapter;
	ViewPager mViewPager;

	@Override
	protected void onCreate(Bundle savedInstanceState) {
		super.onCreate(savedInstanceState);
		setContentView(R.layout.activity_main);
		
		final ProgressDialog gain_permission = ProgressDialog.show(
				this, "Please wait", "Gaining permissions...",
				true);
		
		new Thread(new Runnable() {
			@Override
			public void run() {

				try {
					UART.getPermission();
					I2C.getPermission();
					UART.fd = UART.serialOpen("/dev/ttyS7", 115200);
					Thread.sleep(2000);

				} catch (Exception e) {
					e.printStackTrace();
				}
				gain_permission.dismiss();

			}
		}).start();

		// Set up the action bar.
		final ActionBar actionBar = getActionBar();
		actionBar.setNavigationMode(ActionBar.NAVIGATION_MODE_TABS);

		// Create the adapter that will return a fragment for each of the three
		// primary sections of the app.
		mSectionsPagerAdapter = new SectionsPagerAdapter(
				getSupportFragmentManager());

		// Set up the ViewPager with the sections adapter.
		mViewPager = (ViewPager) findViewById(R.id.pager);
		mViewPager.setAdapter(mSectionsPagerAdapter);

		// When swiping between different sections, select the corresponding
		// tab. We can also use ActionBar.Tab#select() to do this if we have
		// a reference to the Tab.
		mViewPager
				.setOnPageChangeListener(new ViewPager.SimpleOnPageChangeListener() {
					@Override
					public void onPageSelected(int position) {
						actionBar.setSelectedNavigationItem(position);
					}
				});

		// For each of the sections in the app, add a tab to the action bar.
		for (int i = 0; i < mSectionsPagerAdapter.getCount(); i++) {
			// Create a tab with text corresponding to the page title defined by
			// the adapter. Also specify this Activity object, which implements
			// the TabListener interface, as the callback (listener) for when
			// this tab is selected.
			actionBar.addTab(actionBar.newTab()
					.setText(mSectionsPagerAdapter.getPageTitle(i))
					.setTabListener(this));
		}
	}

	@Override
	public boolean onCreateOptionsMenu(Menu menu) {
		// Inflate the menu; this adds items to the action bar if it is present.
		getMenuInflater().inflate(R.menu.main, menu);
		return true;
	}

	@Override
	public void onTabSelected(ActionBar.Tab tab,
			FragmentTransaction fragmentTransaction) {
		// When the given tab is selected, switch to the corresponding page in
		// the ViewPager.
		mViewPager.setCurrentItem(tab.getPosition());
	}

	@Override
	public void onTabUnselected(ActionBar.Tab tab,
			FragmentTransaction fragmentTransaction) {
	}

	@Override
	public void onTabReselected(ActionBar.Tab tab,
			FragmentTransaction fragmentTransaction) {
	}

	@Override
	public boolean onOptionsItemSelected(MenuItem item) {
		return true;

	}

	public class SectionsPagerAdapter extends FragmentPagerAdapter {

		public SectionsPagerAdapter(FragmentManager fm) {
			super(fm);
		}

		@Override
		public Fragment getItem(int position) {

			Fragment fragment = null;

			switch (position) {
			case 0:
				fragment = new UARTFragment();
				break;
			case 1:
				fragment = new I2CFragment();
				break;
			case 2:
				fragment = new GPIOFragment();
				break;
			}
			Bundle args = new Bundle();
			fragment.setArguments(args);
			return fragment;
		}

		@Override
		public int getCount() {
			return 3;
		}

		@Override
		public CharSequence getPageTitle(int position) {
			Locale l = Locale.getDefault();
			switch (position) {
			case 0:
				return getString(R.string.title_section1).toUpperCase(l);
			case 1:
				return getString(R.string.title_section2).toUpperCase(l);
			case 2:
				return getString(R.string.title_section3).toUpperCase(l);
			}
			return null;
		}
	}
}
